01binary/elysium-max-exoskeleton/instructions/images/chest/chest-electronics.png

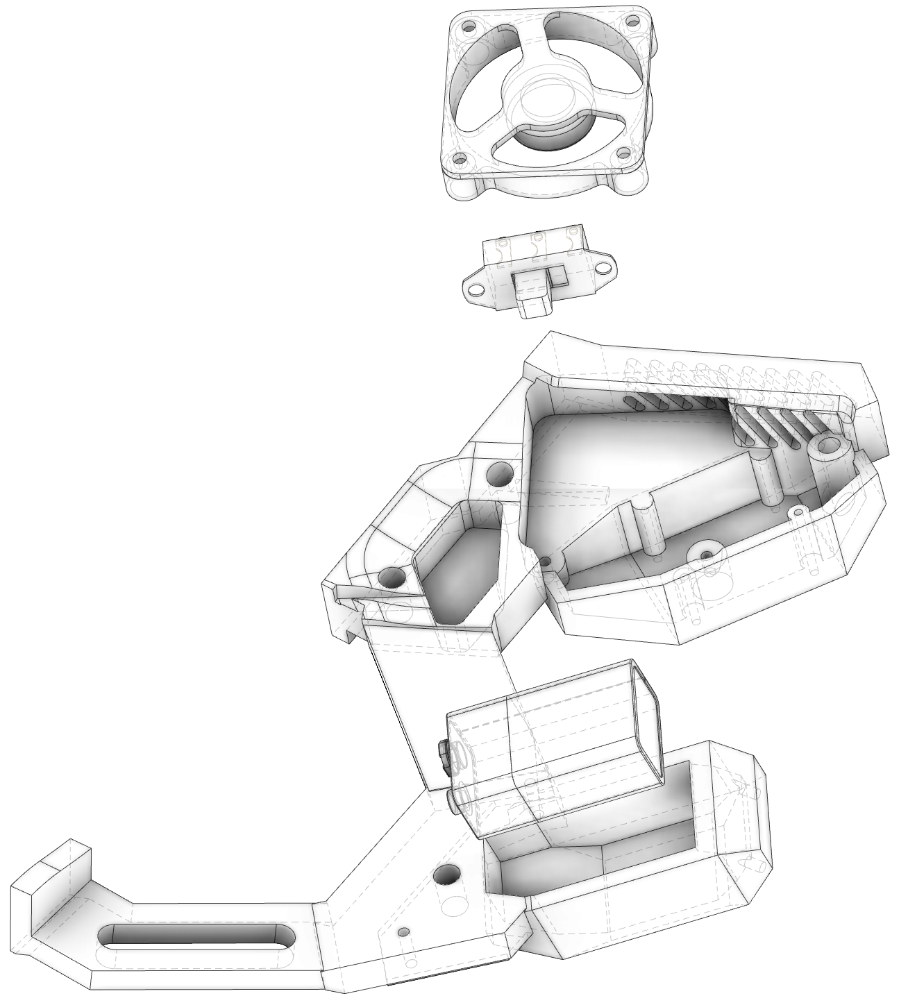
instructions/images/chest/chest-electronics.png
