01binary/elysium-max-exoskeleton/references/6mm-bolts.jpg

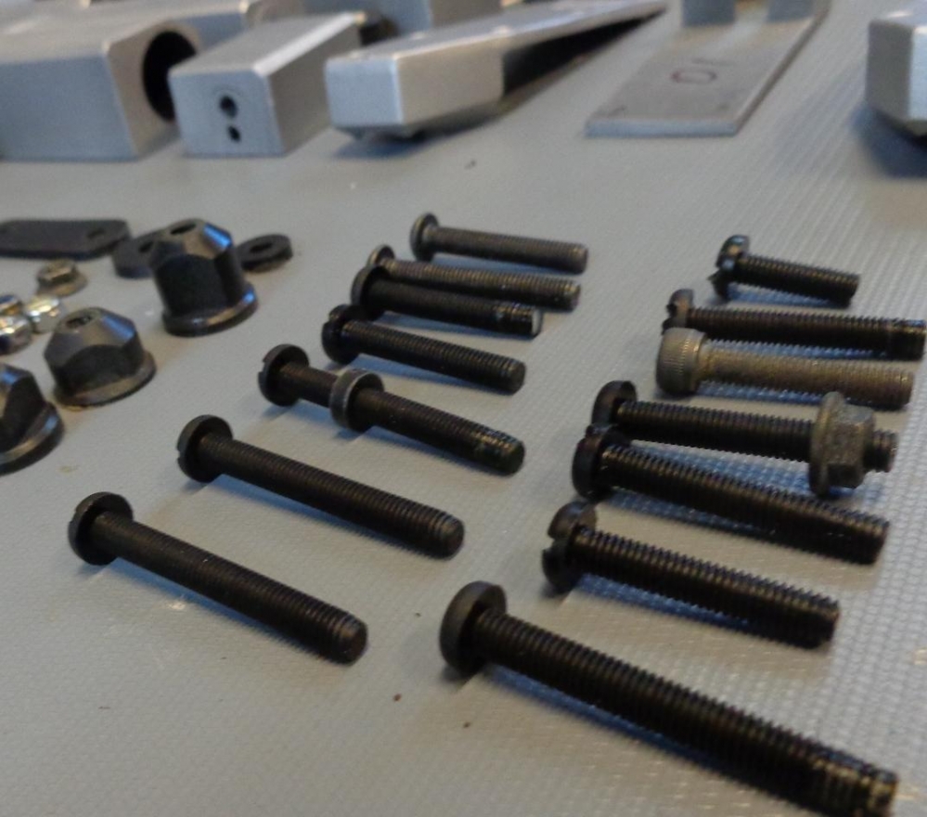
references/6mm-bolts.jpg
