01binary/elysium-max-exoskeleton/references/11591d1393811206-hulc-suit-worn-max-maxmannequin.jpg

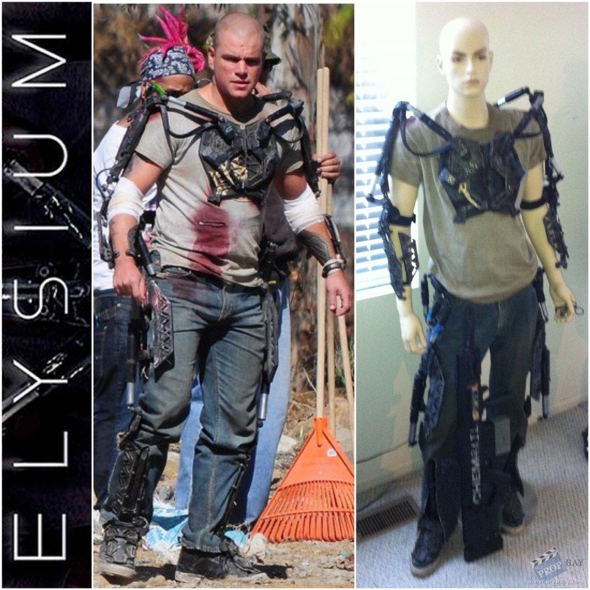
references/11591d1393811206-hulc-suit-worn-max-maxmannequin.jpg
