01binary/elysium-max-exoskeleton/references/11595d1393811206-hulc-suit-worn-max-wetaworkshopelysiumwork111.jpg

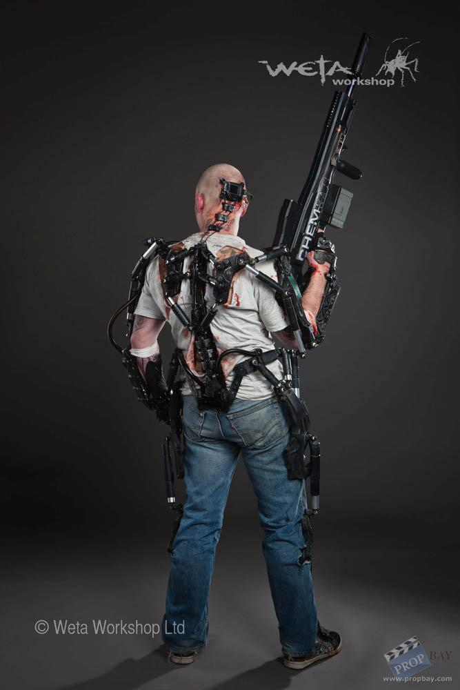
references/11595d1393811206-hulc-suit-worn-max-wetaworkshopelysiumwork111.jpg
