01binary/elysium-max-exoskeleton/references/15305_7.jpg

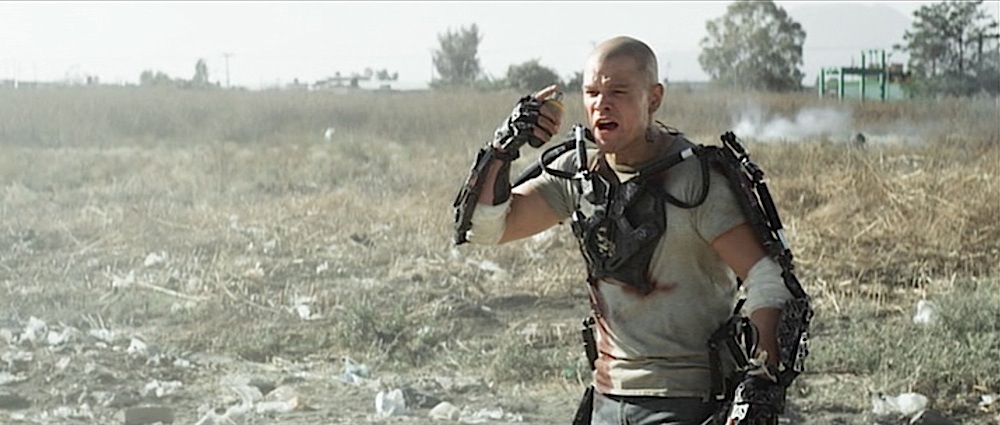
references/15305_7.jpg
