01binary/elysium-max-exoskeleton/references/15305_8.jpg

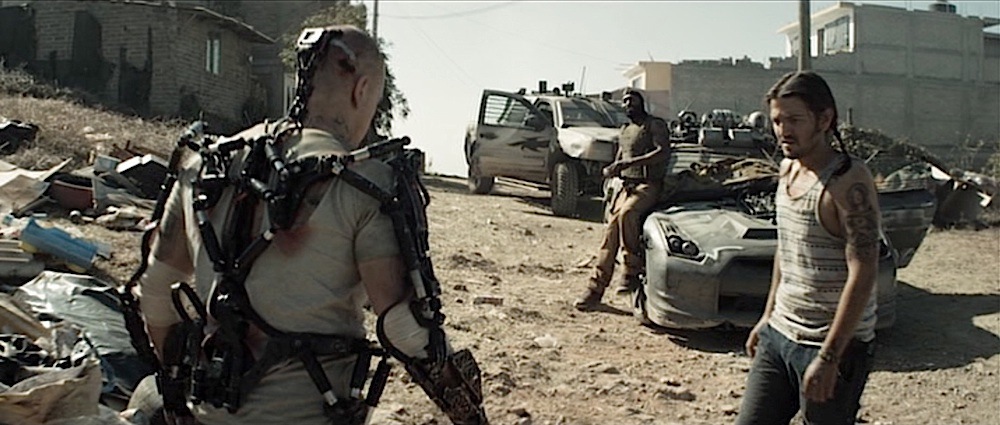
references/15305_8.jpg
