01binary/elysium-max-exoskeleton/references/15305_12.jpg

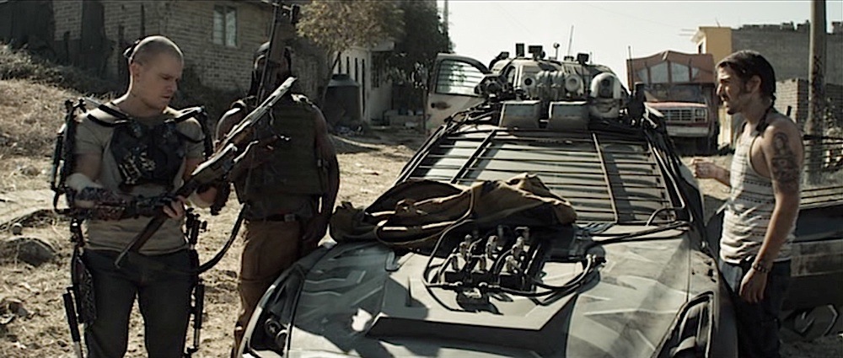
references/15305_12.jpg
