01binary/elysium-max-exoskeleton/references/15445_1.jpg

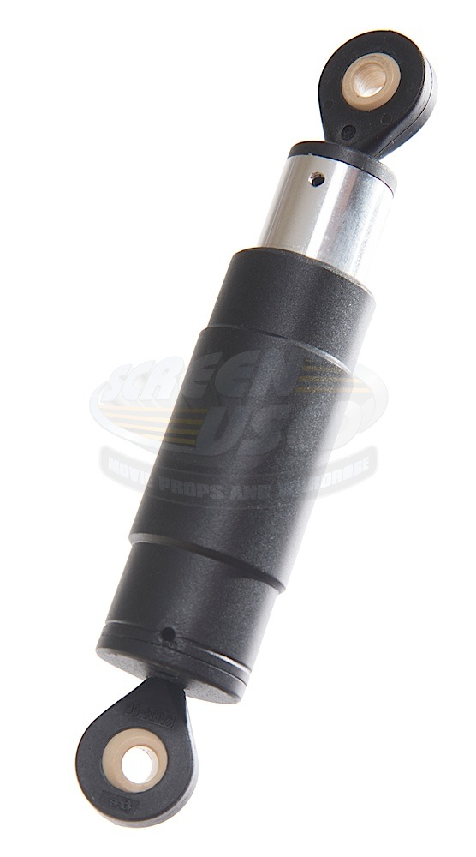
references/15445_1.jpg
