01binary/elysium-max-exoskeleton/references/15445_2.jpg

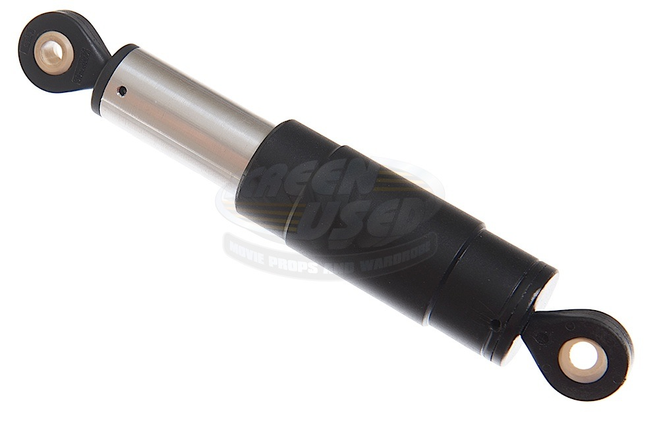
references/15445_2.jpg
