01binary/elysium-max-exoskeleton/references/28012.jpg

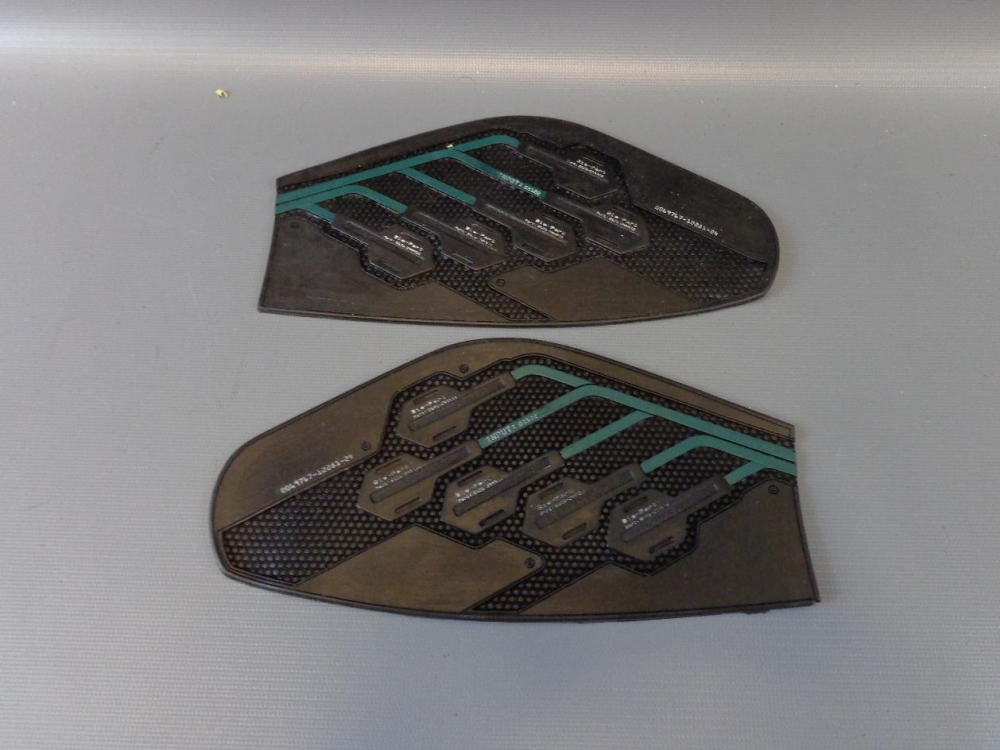
references/28012.jpg
