01binary/elysium-max-exoskeleton/references/197699.jpg

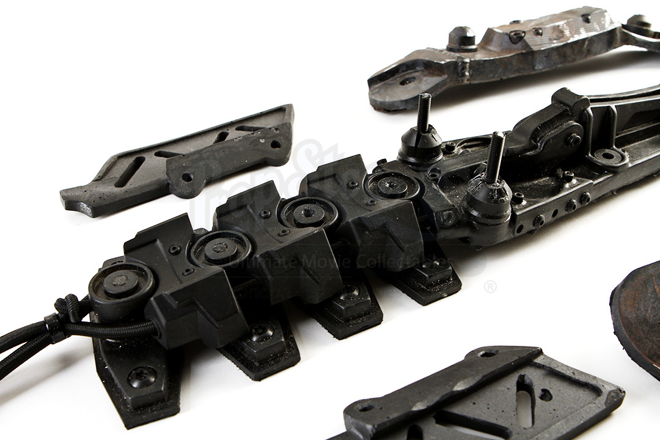
references/197699.jpg
