01binary/elysium-max-exoskeleton/references/197700.jpg

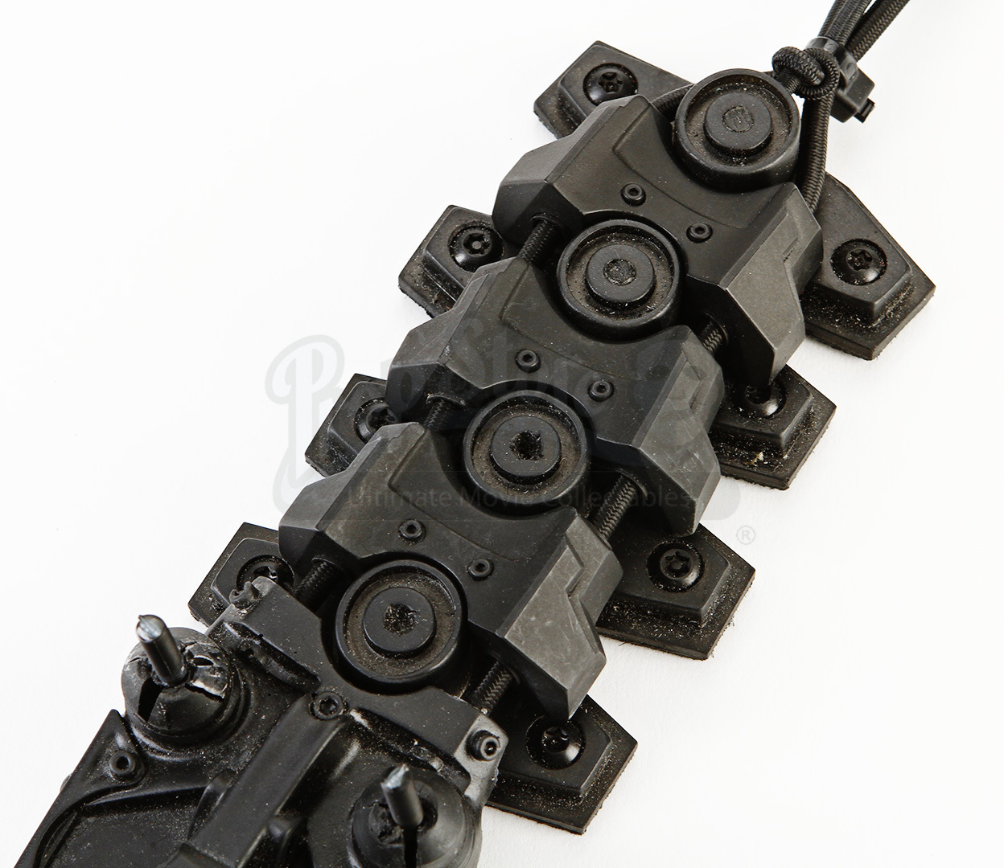
references/197700.jpg
