01binary/elysium-max-exoskeleton/references/197705.jpg

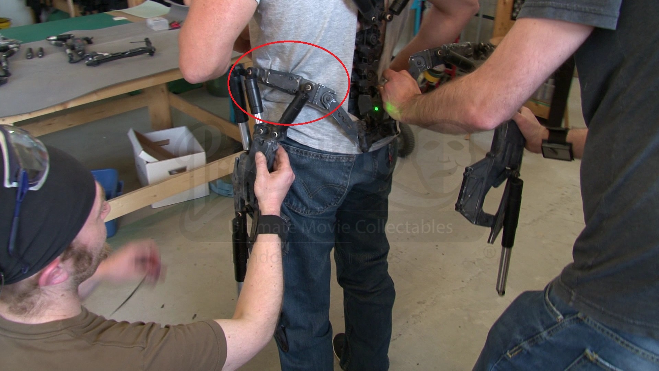
references/197705.jpg
