01binary/elysium-max-exoskeleton/references/198704.jpg

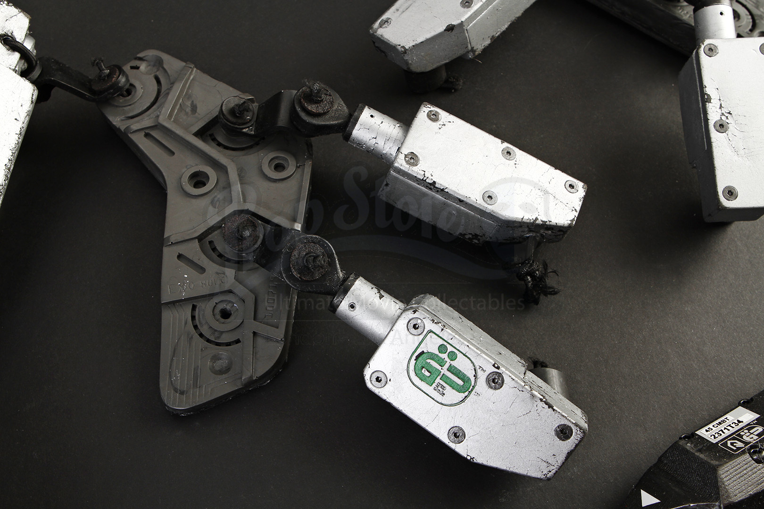
references/198704.jpg
