01binary/elysium-max-exoskeleton/references/198857.jpg

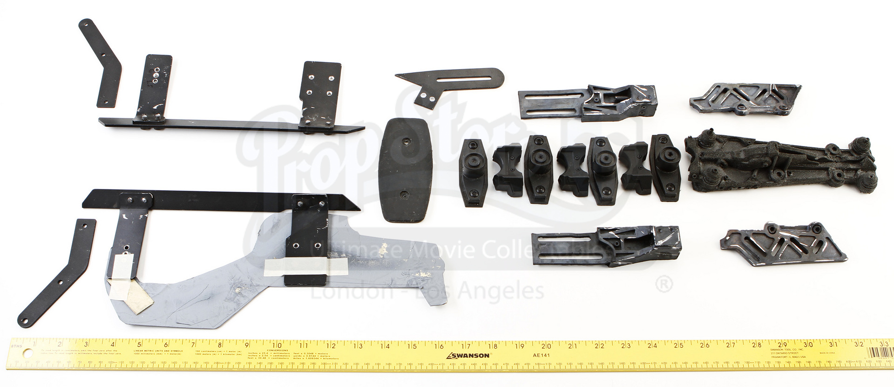
references/198857.jpg
