01binary/elysium-max-exoskeleton/references/213902.jpg

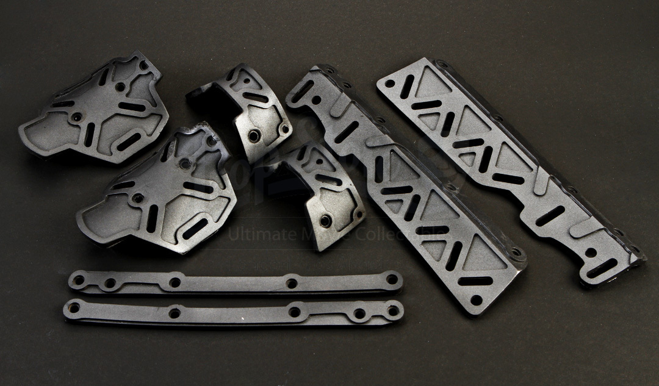
references/213902.jpg
