01binary/elysium-max-exoskeleton/references/213905.jpg

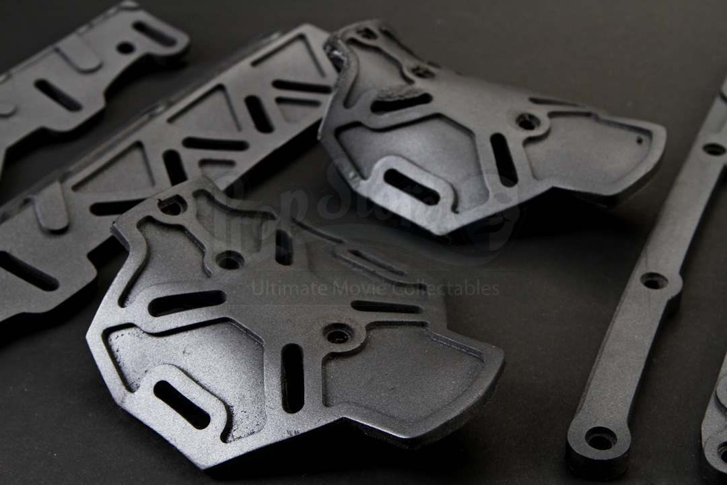
references/213905.jpg
