01binary/elysium-max-exoskeleton/references/574495_199496503551043_1846107824_n.jpg

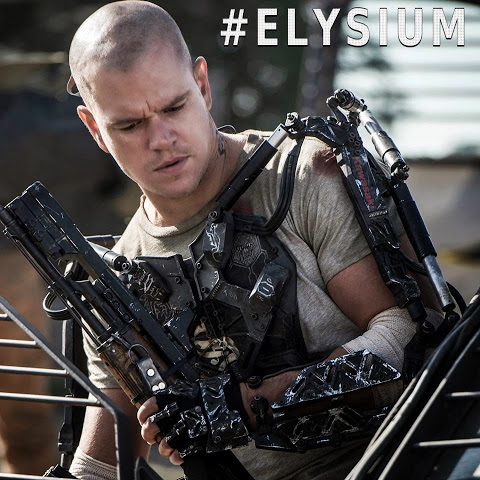
references/574495_199496503551043_1846107824_n.jpg
