01binary/elysium-max-exoskeleton/references/5401417-Elysium-Exoskeleton-Video.jpg

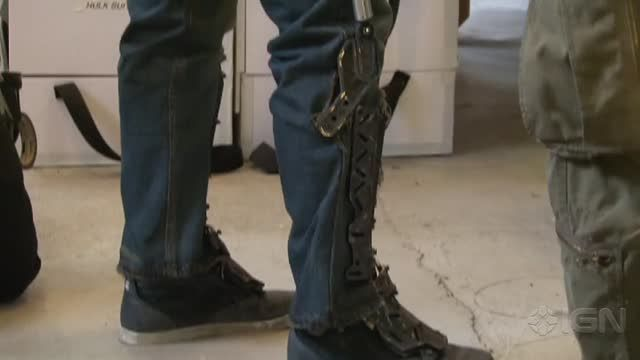
references/5401417-Elysium-Exoskeleton-Video.jpg
