01binary/elysium-max-exoskeleton/references/06674515.jpg

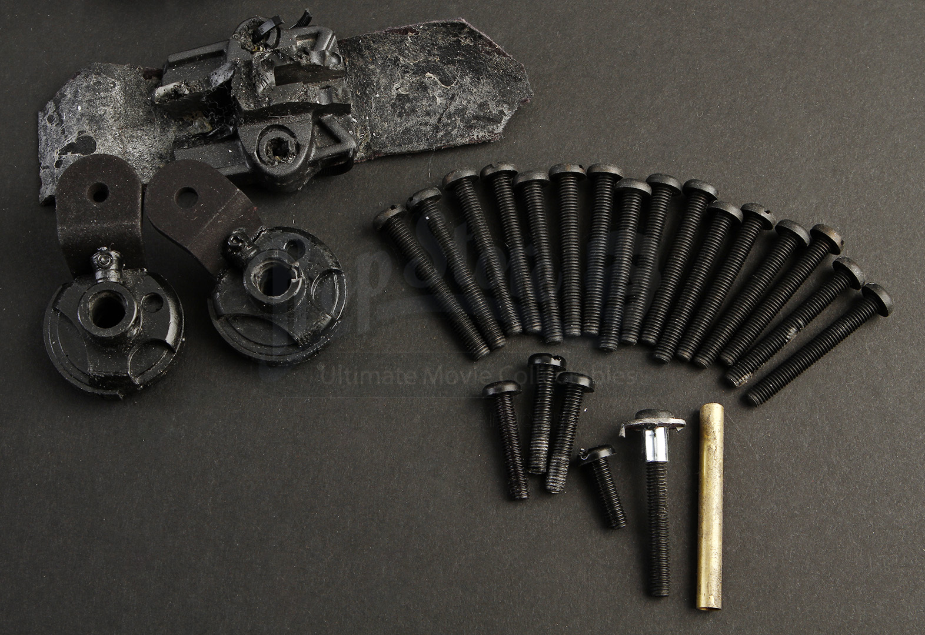
references/06674515.jpg
