01binary/elysium-max-exoskeleton/references/7878678.jpg

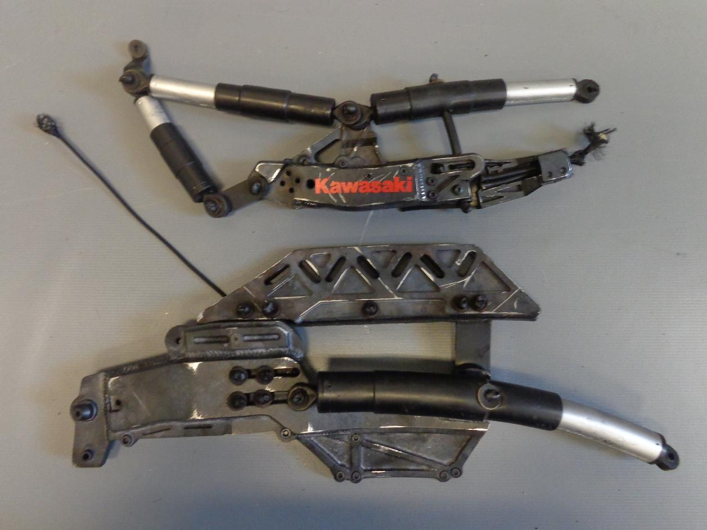
references/7878678.jpg
