01binary/elysium-max-exoskeleton/references/10857353_10152587256252303_362344312174633431_o.jpg

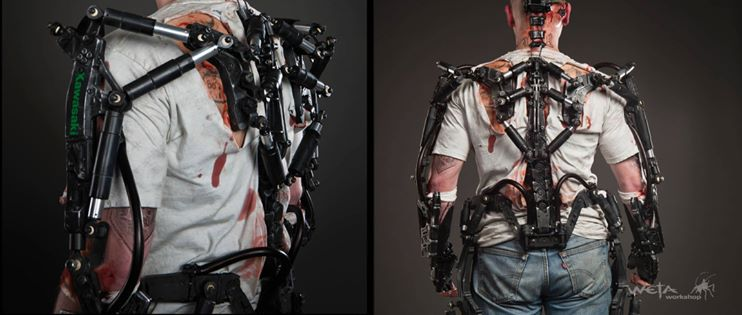
references/10857353_10152587256252303_362344312174633431_o.jpg
