01binary/elysium-max-exoskeleton/references/14776765.jpg

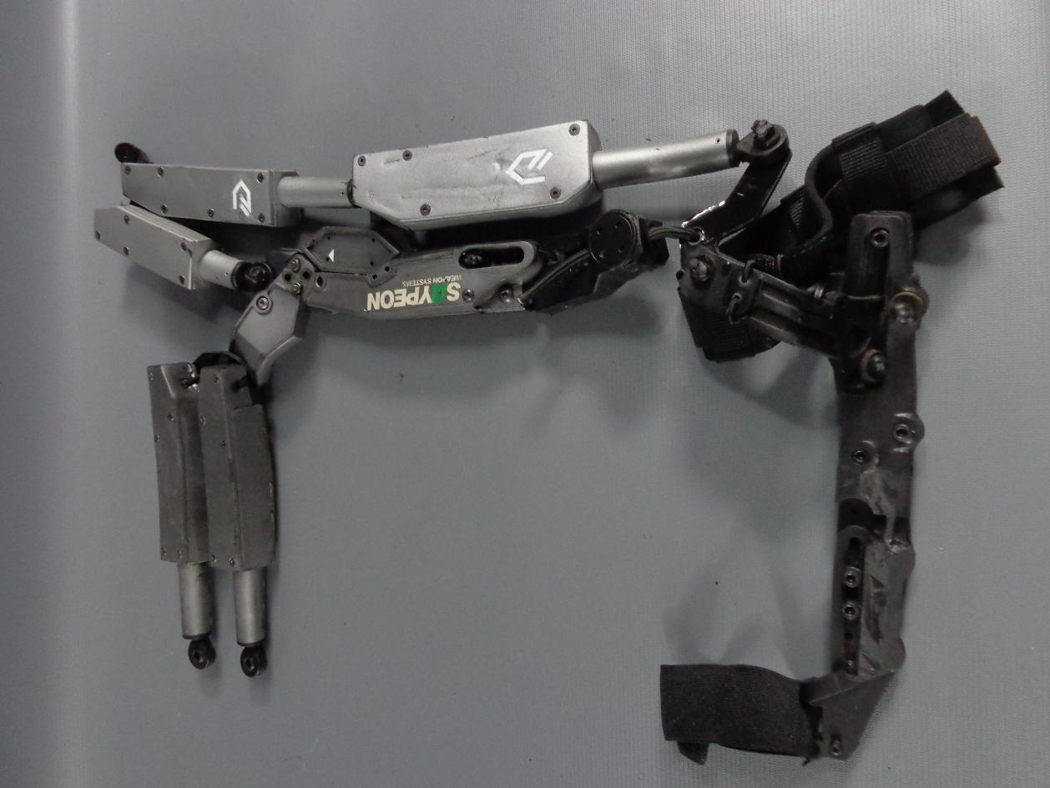
references/14776765.jpg
