01binary/elysium-max-exoskeleton/references/14776832.jpg

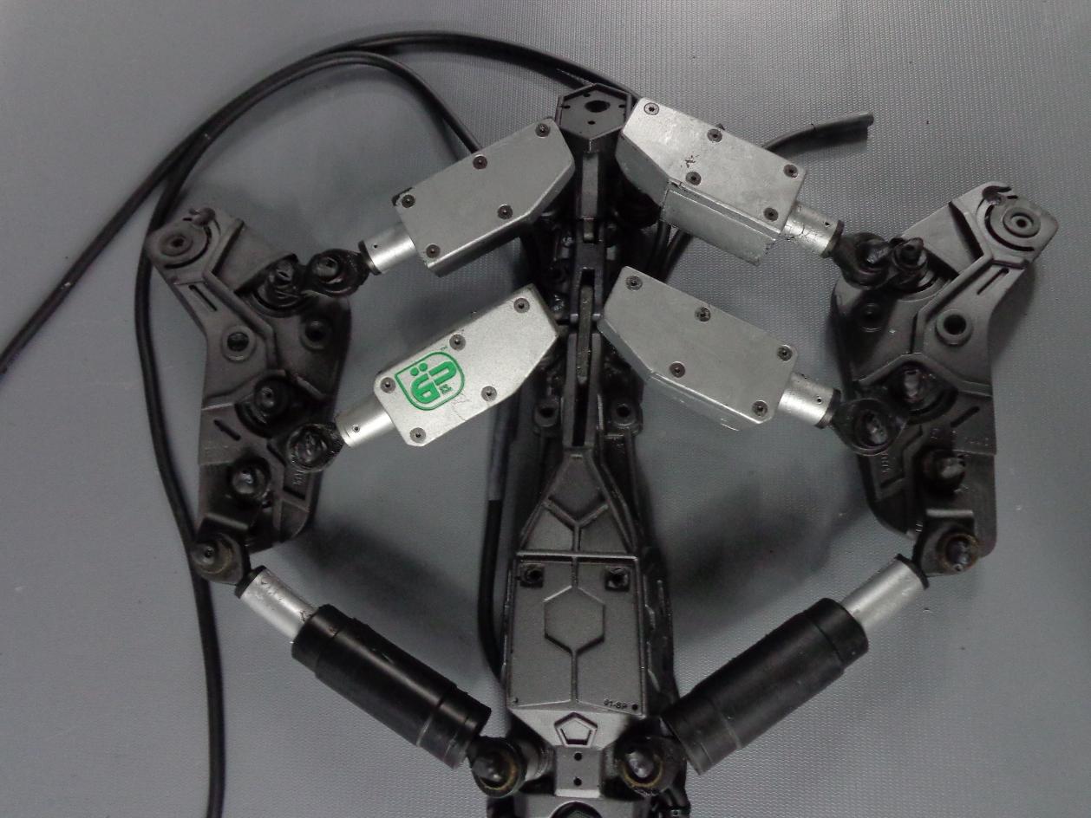
references/14776832.jpg
