01binary/elysium-max-exoskeleton/references/14795775.jpg

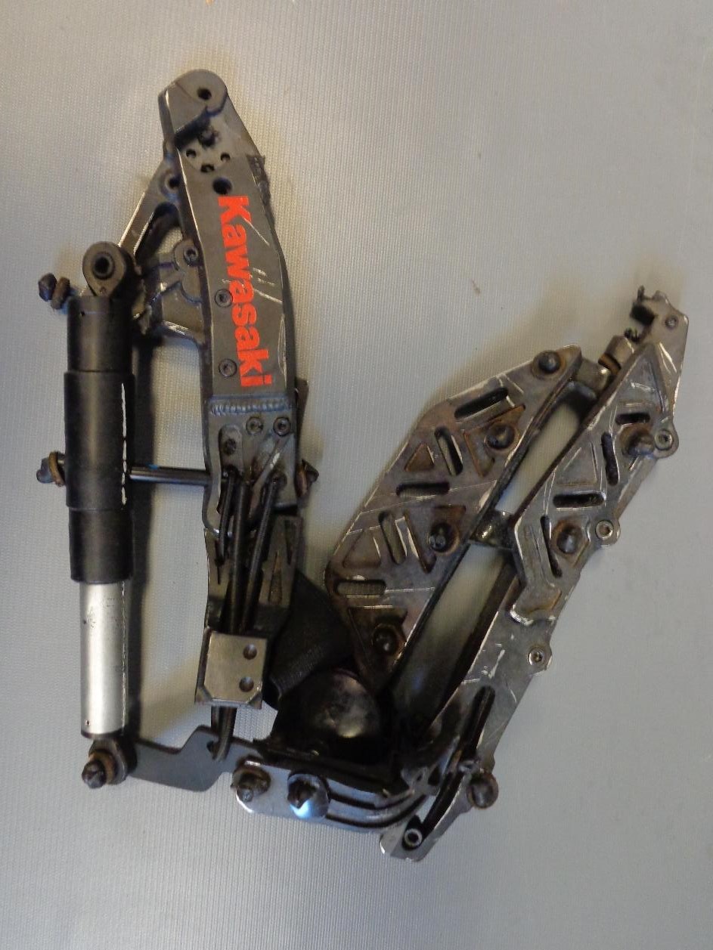
references/14795775.jpg
