01binary/elysium-max-exoskeleton/references/14795777.jpg

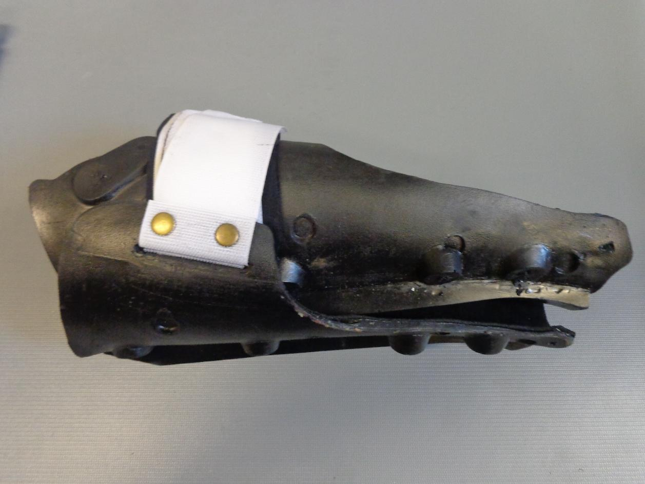
references/14795777.jpg
