01binary/elysium-max-exoskeleton/references/14795779.jpg

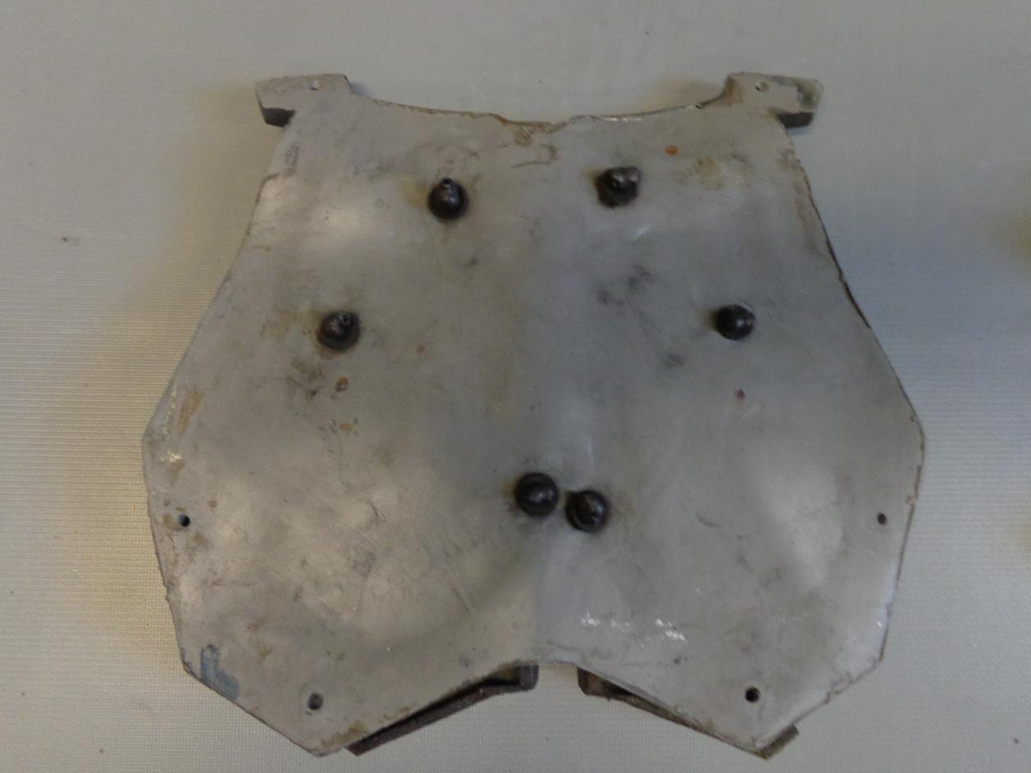
references/14795779.jpg
