01binary/elysium-max-exoskeleton/references/14795780.jpg

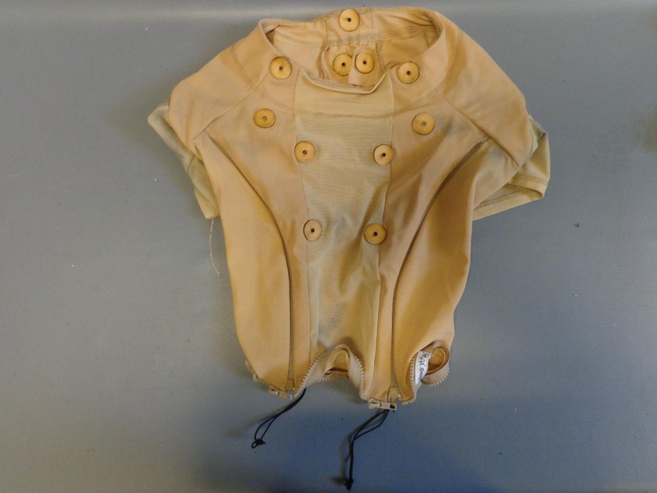
references/14795780.jpg
