01binary/elysium-max-exoskeleton/references/14795787.jpg

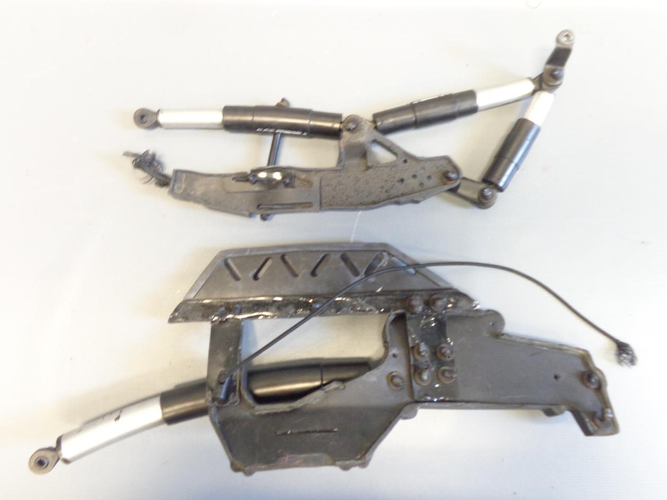
references/14795787.jpg
