01binary/elysium-max-exoskeleton/references/14795788.jpg

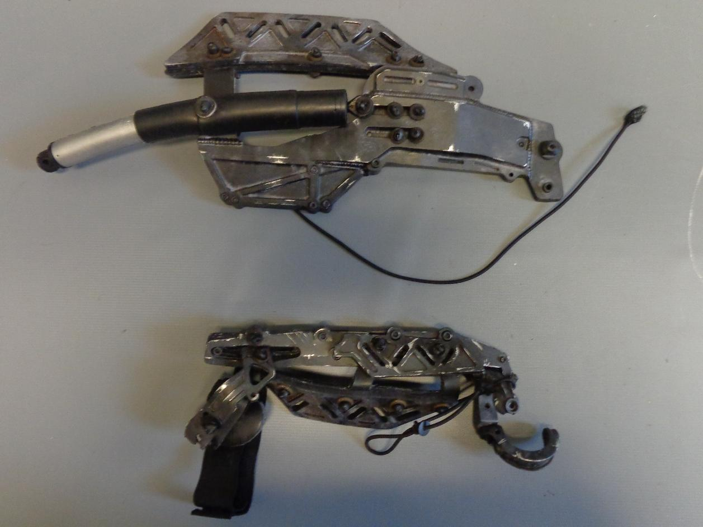
references/14795788.jpg
