01binary/elysium-max-exoskeleton/references/14795789.jpg

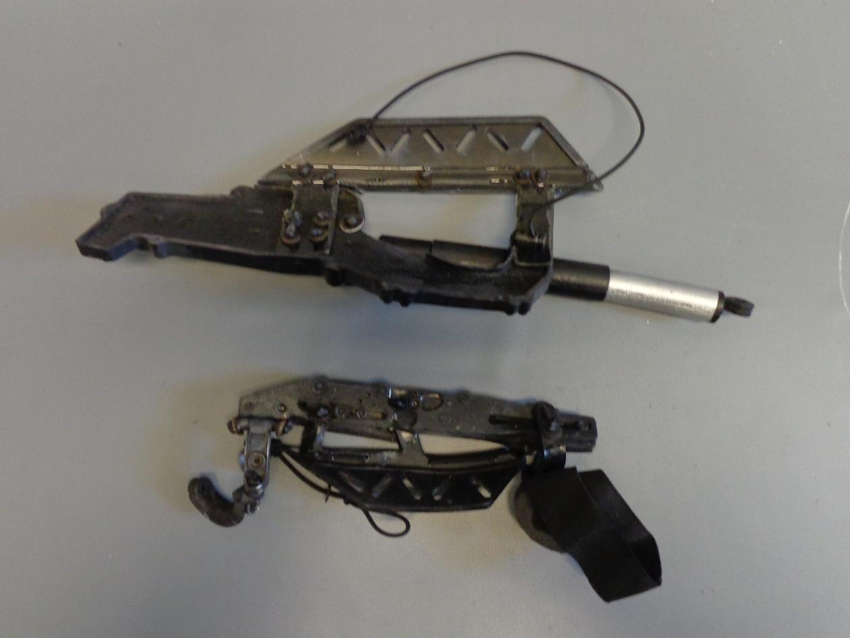
references/14795789.jpg
