01binary/elysium-max-exoskeleton/references/14852573.jpg

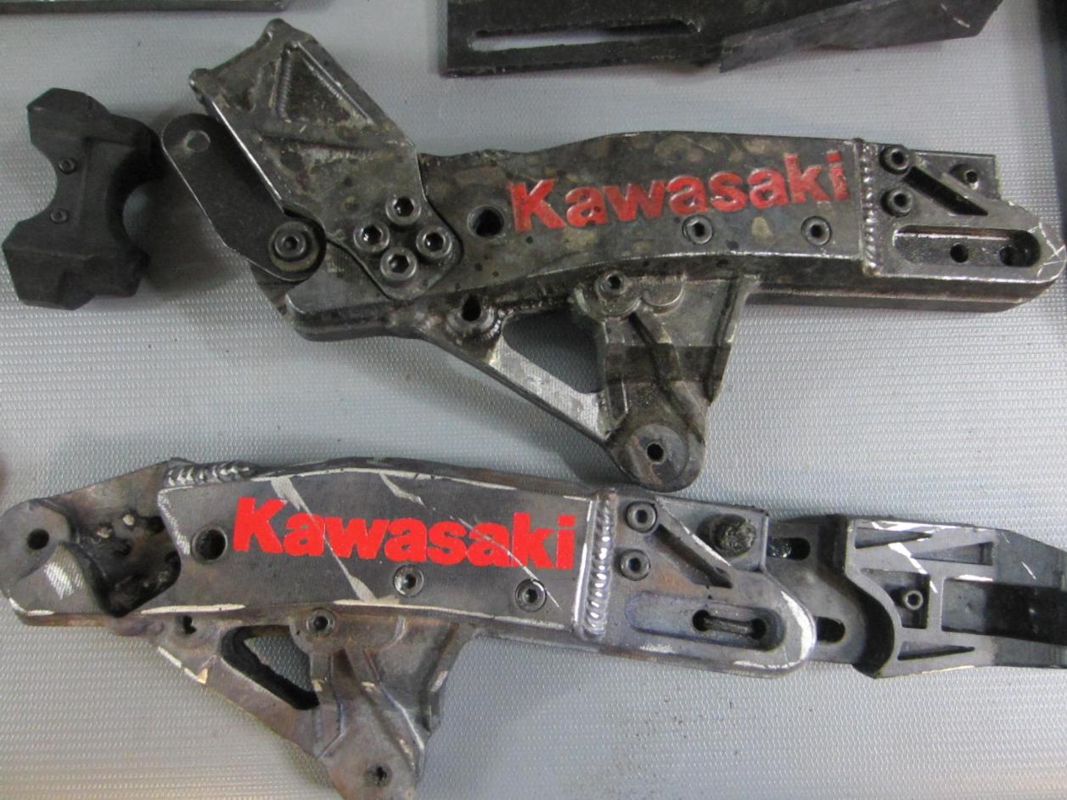
references/14852573.jpg
