01binary/elysium-max-exoskeleton/references/14852575.jpg

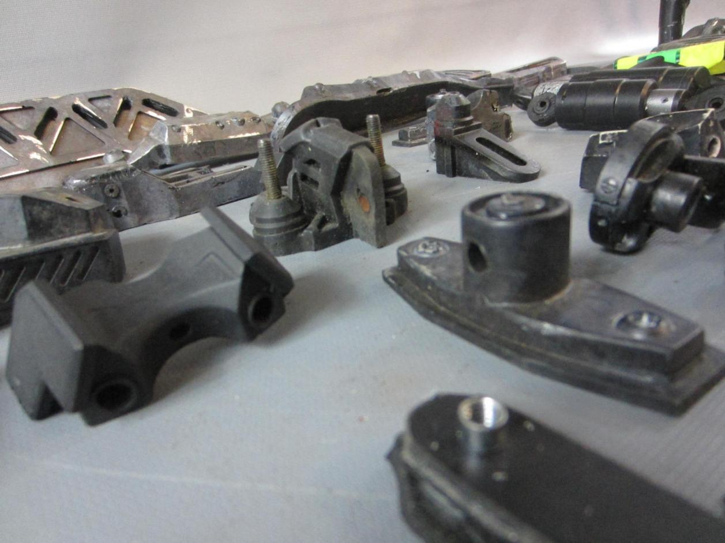
references/14852575.jpg
