01binary/elysium-max-exoskeleton/references/aliensarchive.png

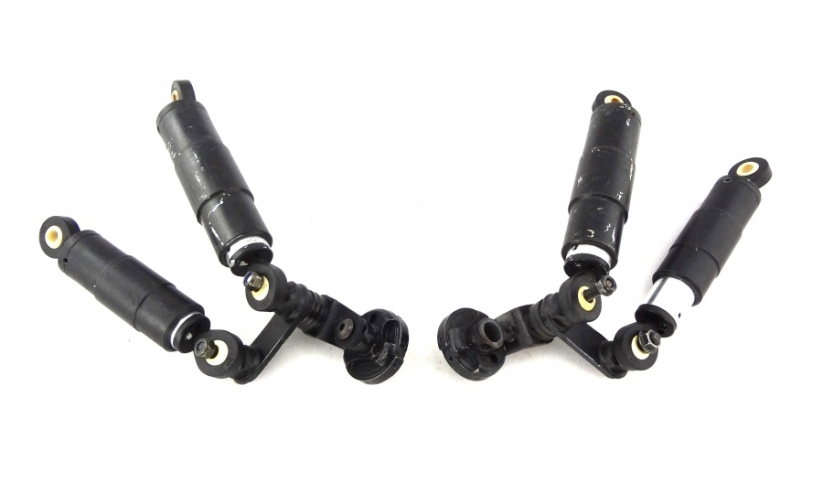
references/aliensarchive.png
