01binary/elysium-max-exoskeleton/references/another-pelvis.jpg

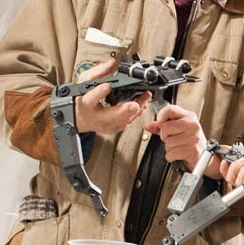
references/another-pelvis.jpg
