01binary/elysium-max-exoskeleton/references/arm left.bmp

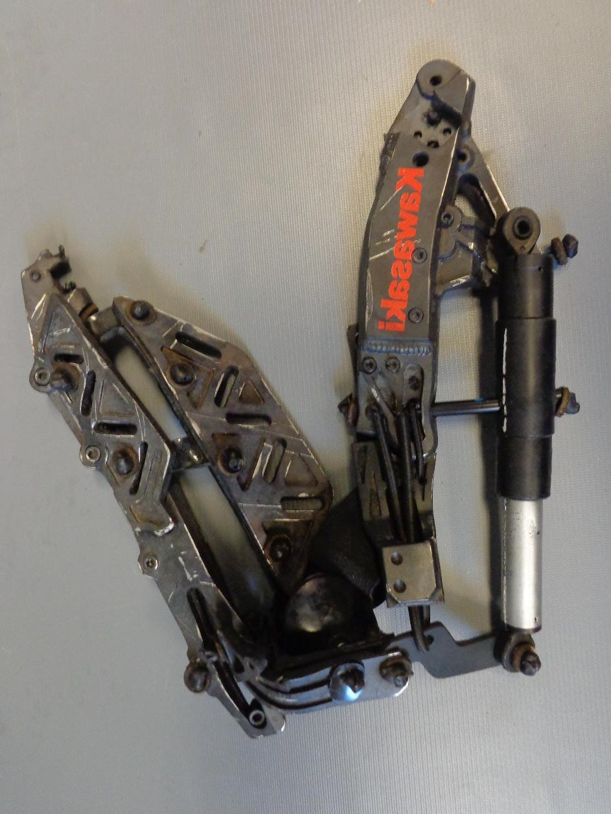
references/arm left.bmp
