01binary/elysium-max-exoskeleton/references/Chest/chest mount 2.jpg

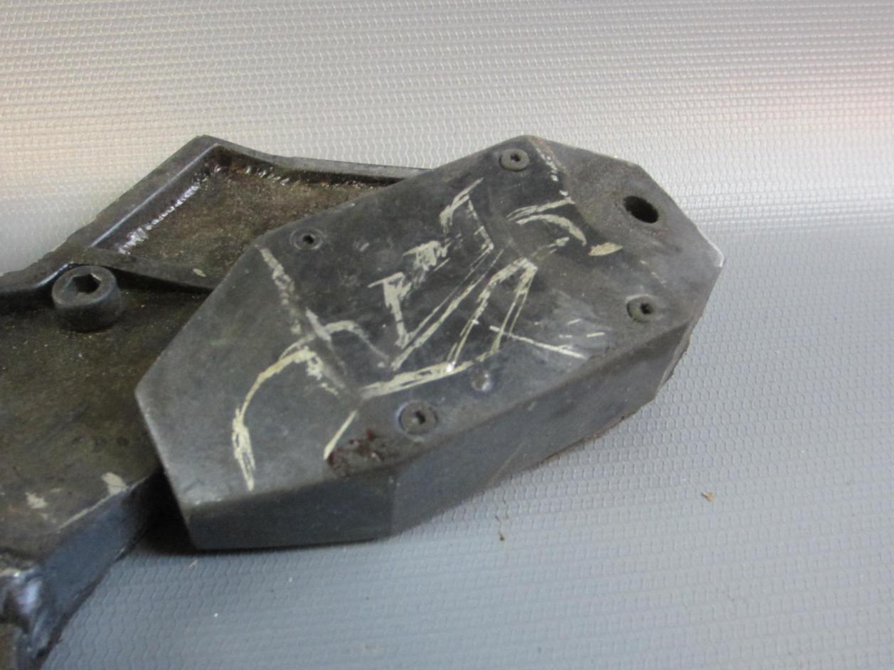
references/chest mount 2.jpg
