01binary/elysium-max-exoskeleton/references/Chest/chest-top.png

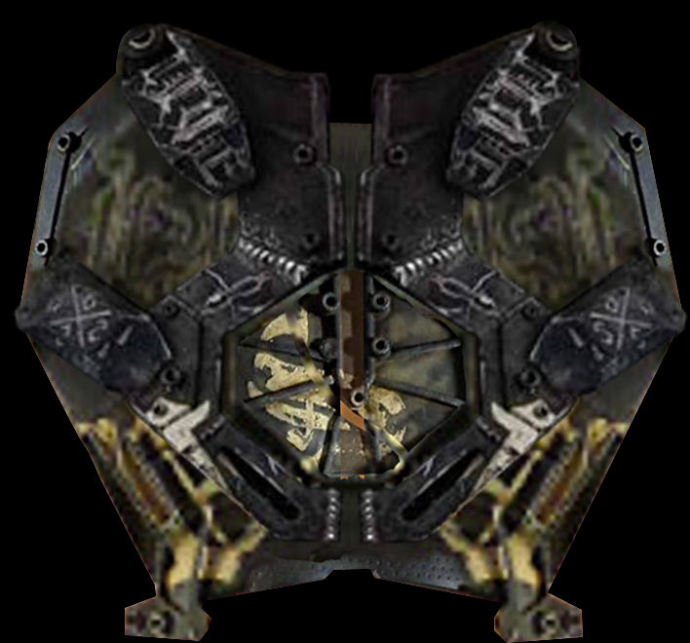
references/Chest/chest-top.png
