01binary/elysium-max-exoskeleton/references/Chest/movie12.jpg

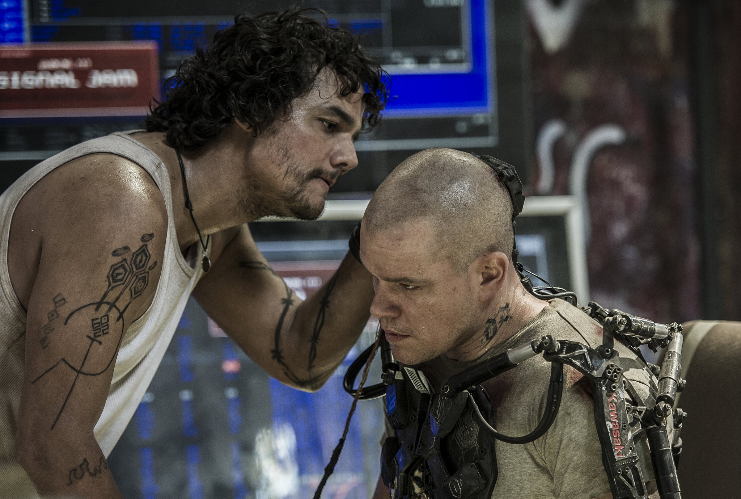
references/Chest/movie12.jpg
