01binary/elysium-max-exoskeleton/references/Chest/production05.jpg

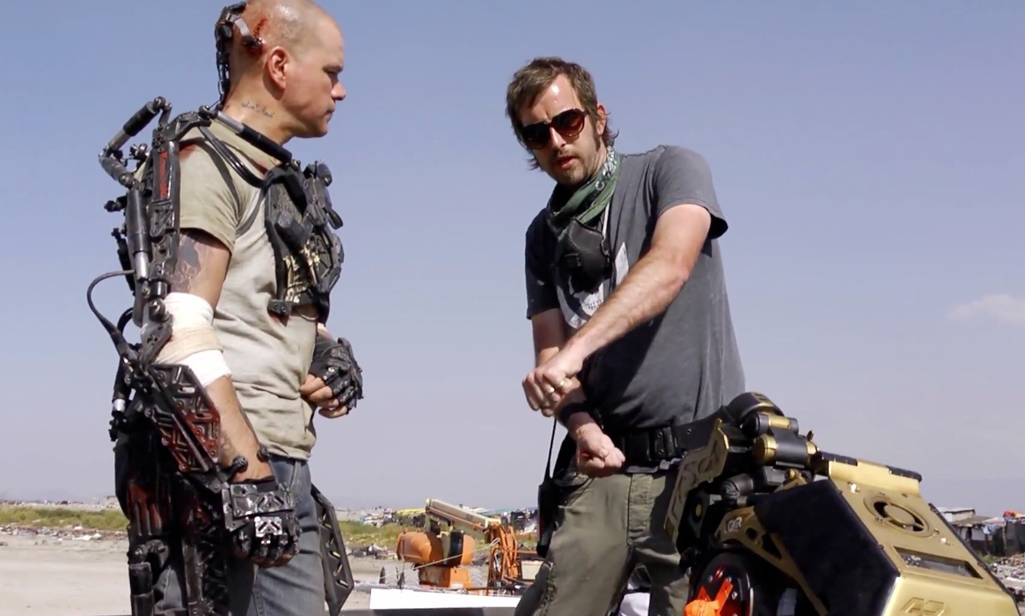
references/Chest/production05.jpg
