01binary/elysium-max-exoskeleton/references/chestak.png

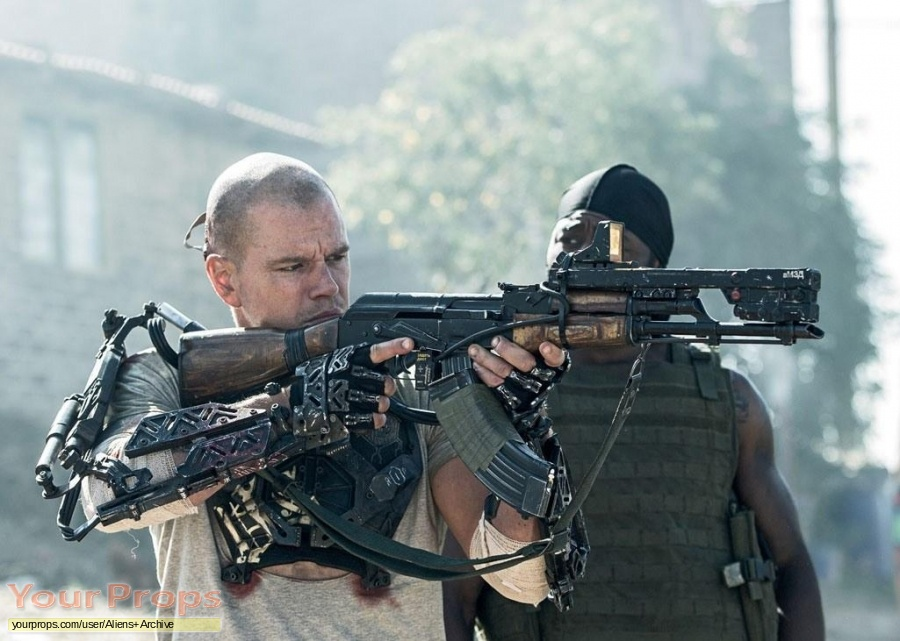
references/chestak.png
