01binary/elysium-max-exoskeleton/references/corners.png

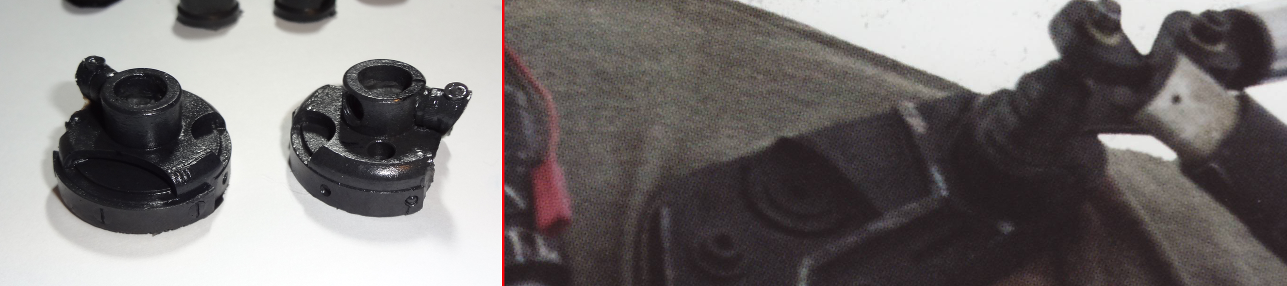
references/corners.png
