01binary/elysium-max-exoskeleton/references/elysium048-upperarmconn.jpg

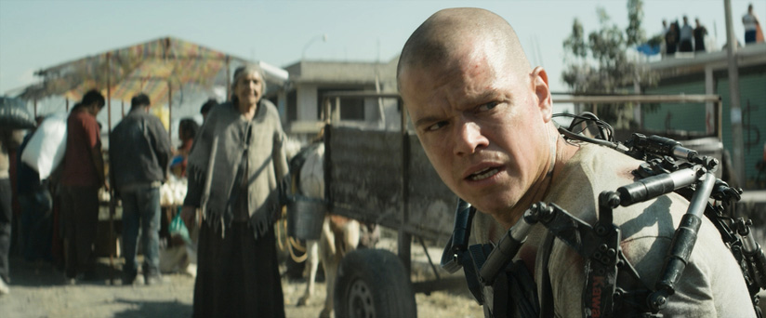
references/elysium048-upperarmconn.jpg
