01binary/elysium-max-exoskeleton/references/elysium065.jpg

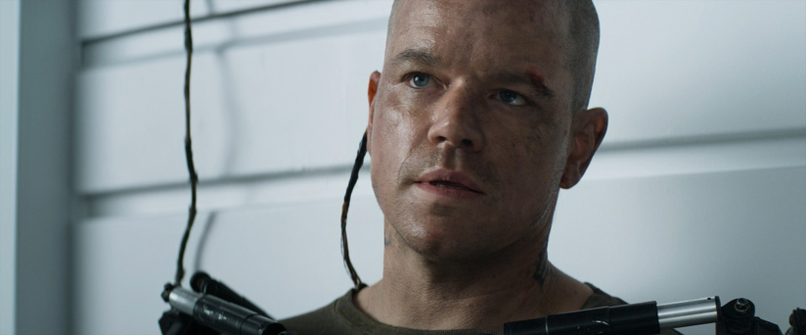
references/elysium065.jpg
