01binary/elysium-max-exoskeleton/references/ELYSIUM-graphic-design2.jpg

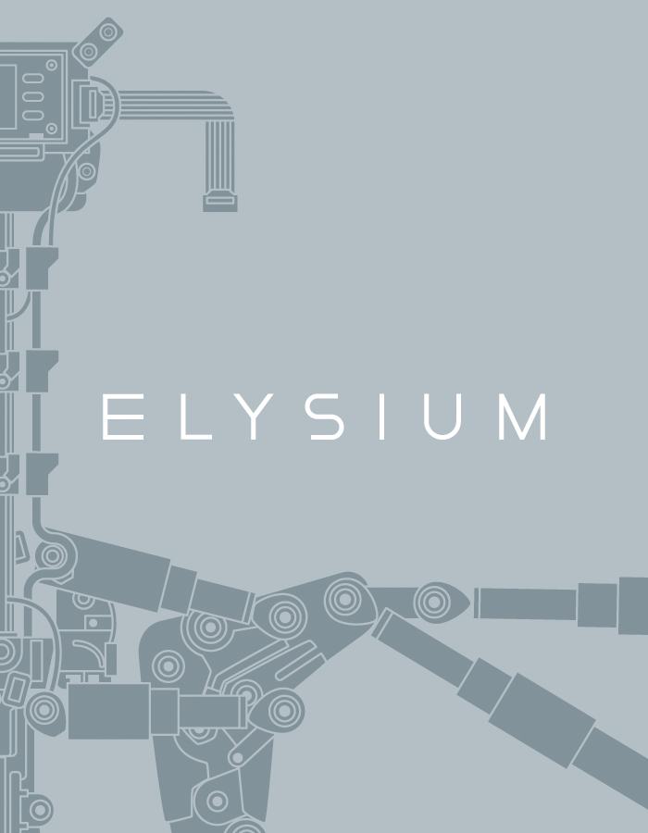
references/ELYSIUM-graphic-design2.jpg
