01binary/elysium-max-exoskeleton/references/elysium-matt-damon-elektro-suit.jpg

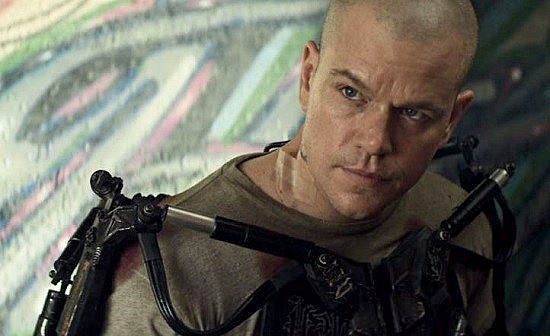
references/elysium-matt-damon-elektro-suit.jpg
