01binary/elysium-max-exoskeleton/references/elysium-sword-strike.jpg

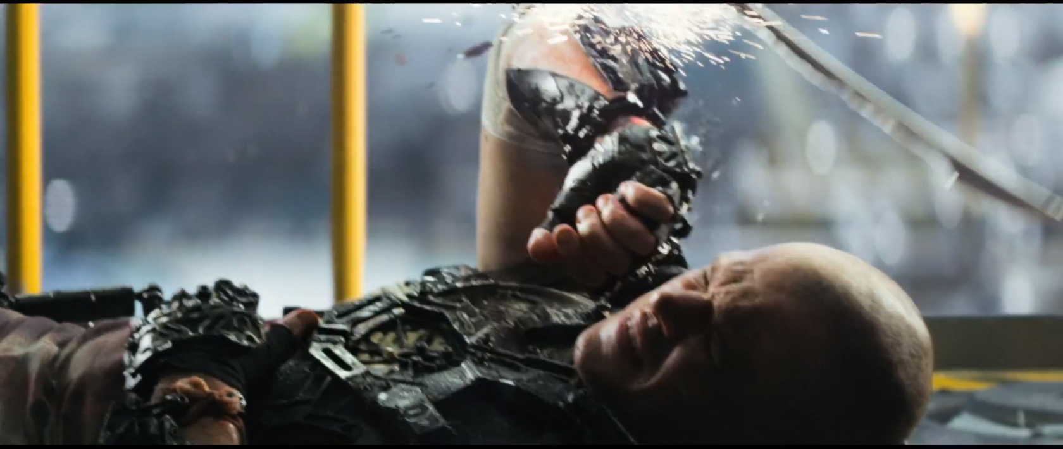
references/elysium-sword-strike.jpg
