01binary/elysium-max-exoskeleton/references/Elysium_BTS_comp_01.jpg

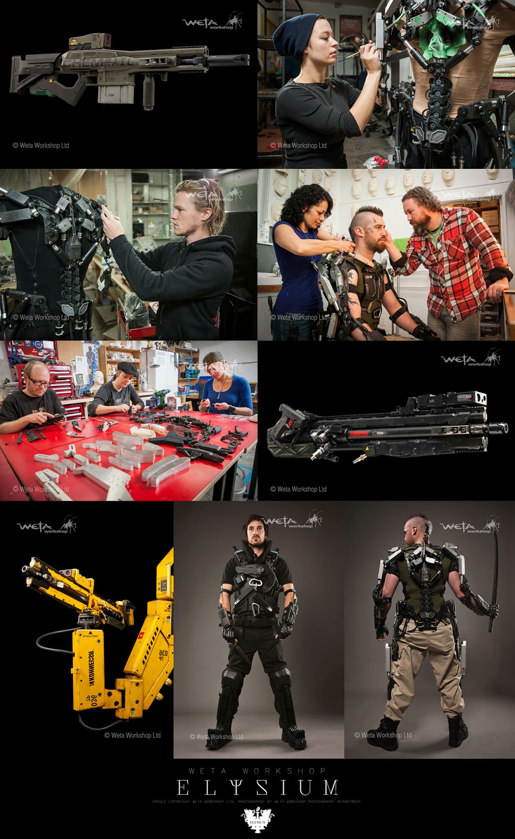
references/Elysium_BTS_comp_01.jpg
