01binary/elysium-max-exoskeleton/references/front.jpg

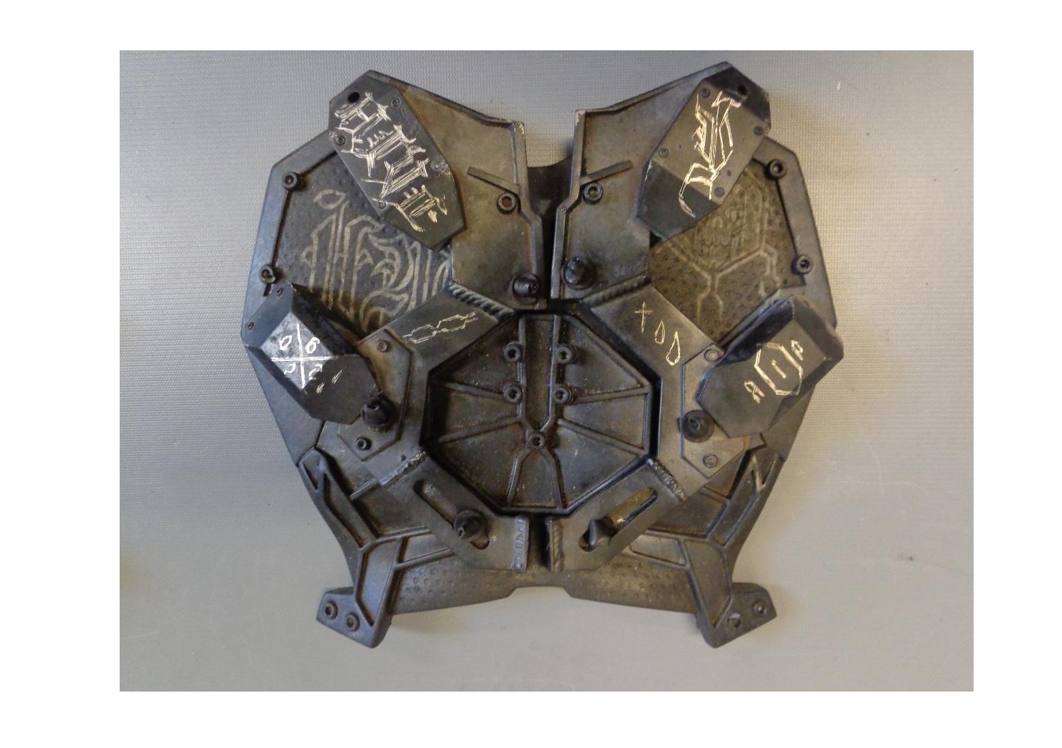
references/front.jpg
