01binary/elysium-max-exoskeleton/references/hand-palm-and-forearm.jpg

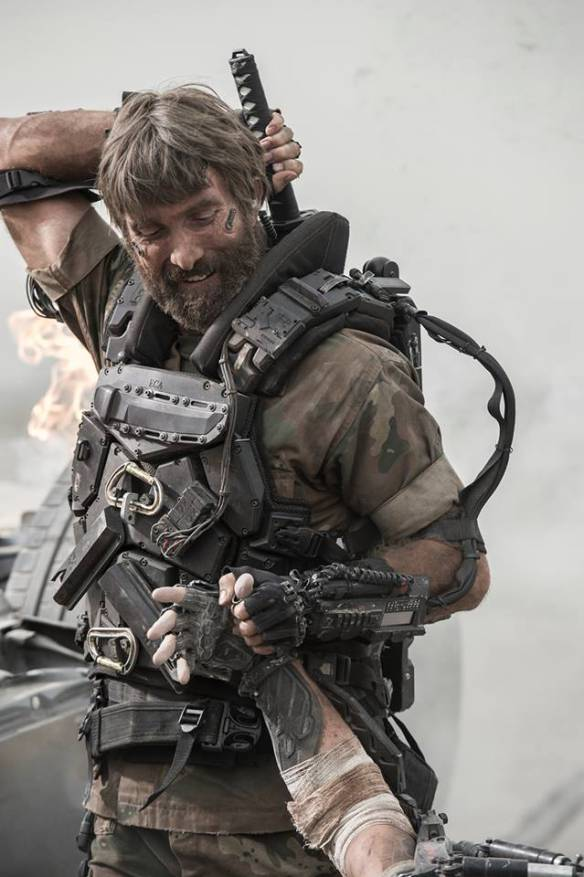
references/hand-palm-and-forearm.jpg
