01binary/elysium-max-exoskeleton/references/handref-unwrapped.JPG

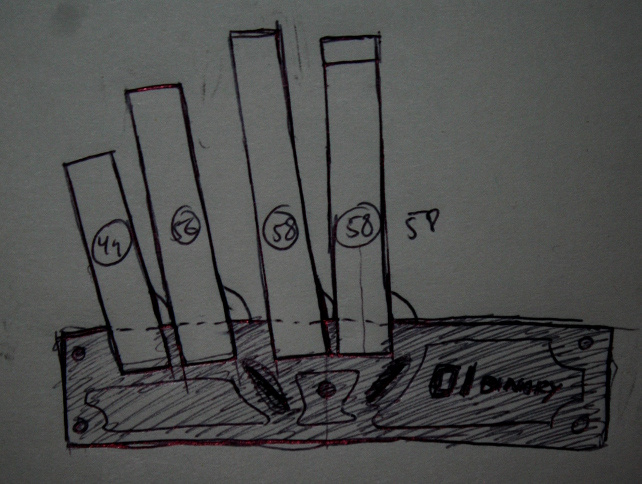
references/handref-unwrapped.JPG
