01binary/elysium-max-exoskeleton/references/hawk-hands.png

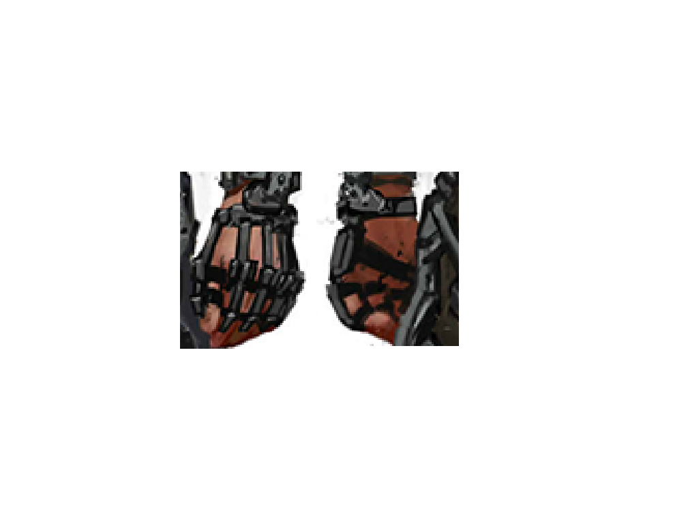
references/hawk-hands.png
