01binary/elysium-max-exoskeleton/references/head-plate.bmp

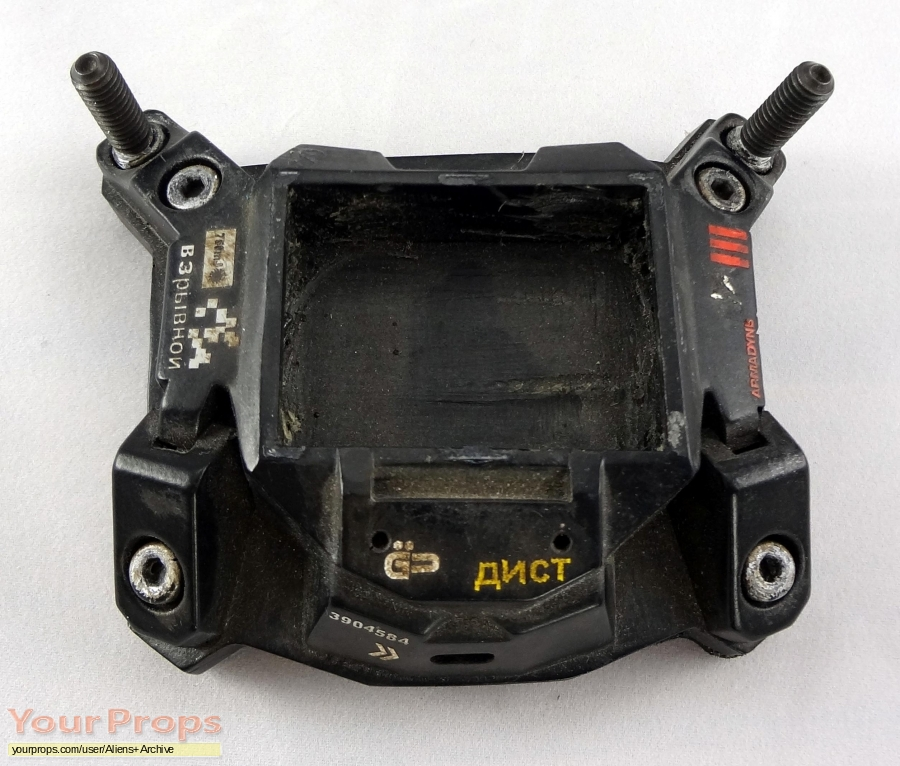
references/head-plate.bmp
