01binary/elysium-max-exoskeleton/references/karm sheet.png

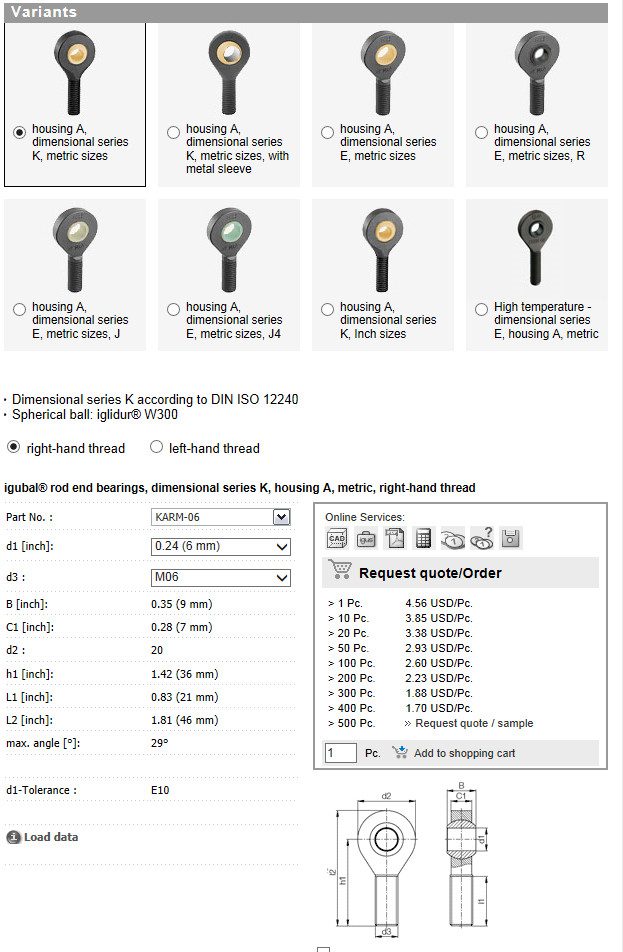
references/karm sheet.png
