01binary/elysium-max-exoskeleton/references/karm.png

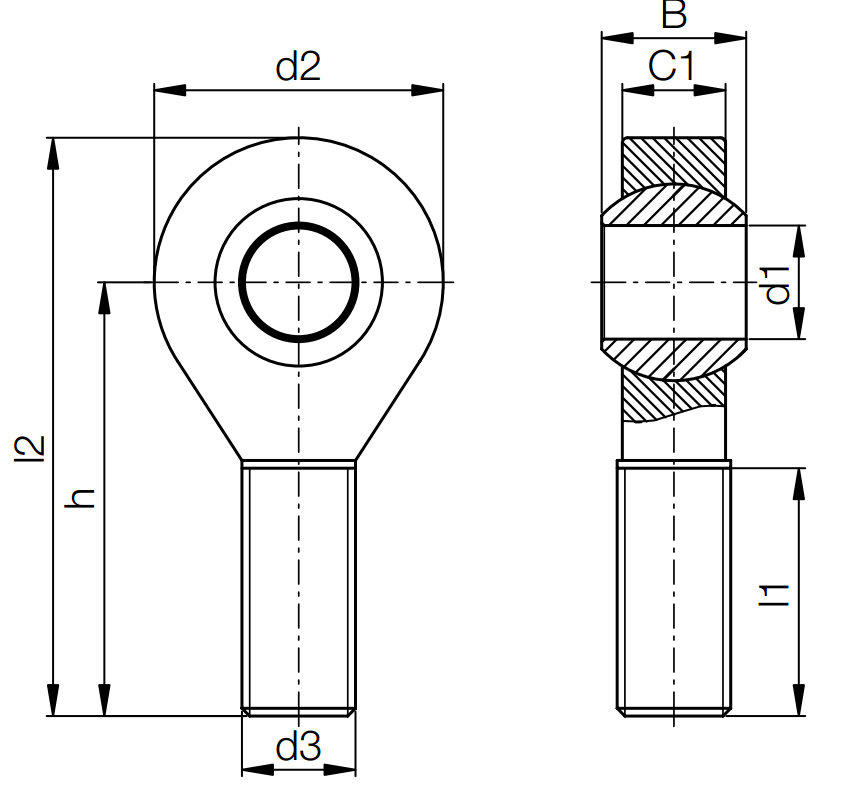
references/karm.png
