01binary/elysium-max-exoskeleton/references/kruger-pistons.jpg

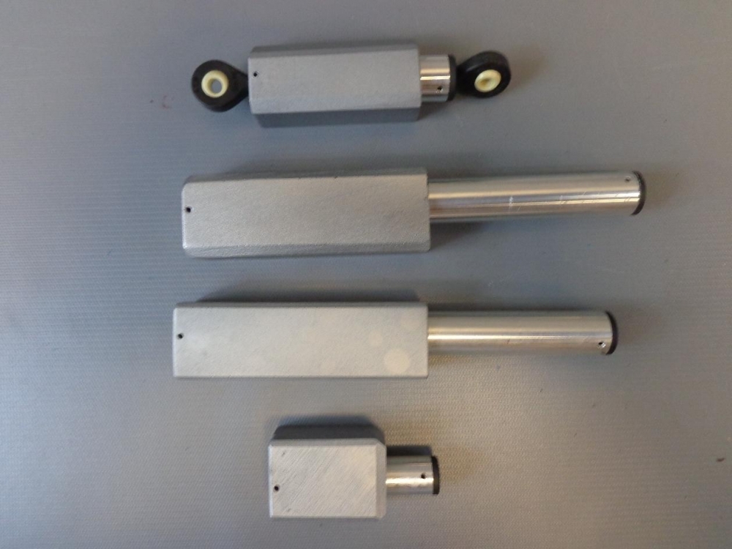
references/kruger-pistons.jpg
