01binary/elysium-max-exoskeleton/references/lf.jpg

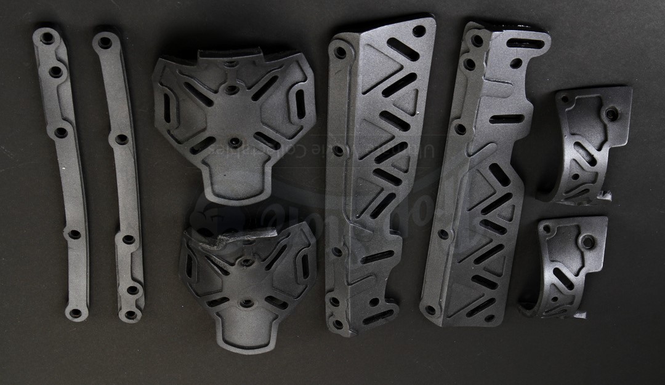
references/lf.jpg
