01binary/elysium-max-exoskeleton/references/Chest/Matt-Damon-in-Exo-Suit.jpg

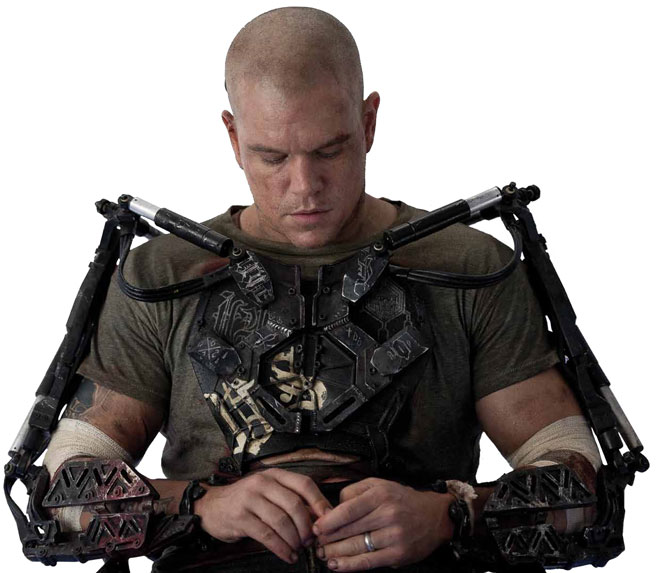
references/Matt-Damon-in-Exo-Suit.jpg
