01binary/elysium-max-exoskeleton/references/Chest/model01.jpg

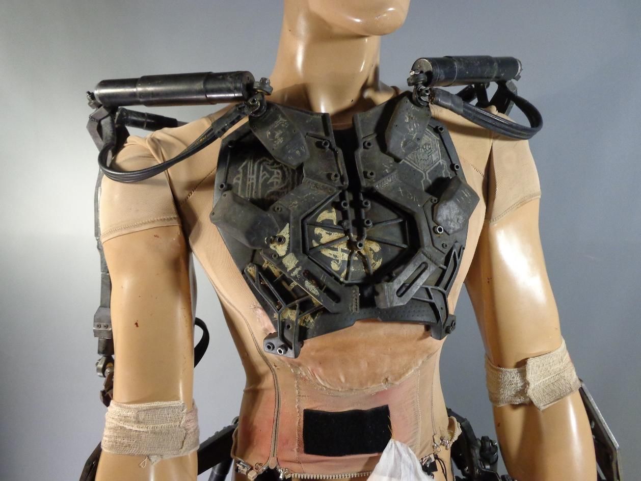
references/model01.jpg
