01binary/elysium-max-exoskeleton/references/model02.jpg

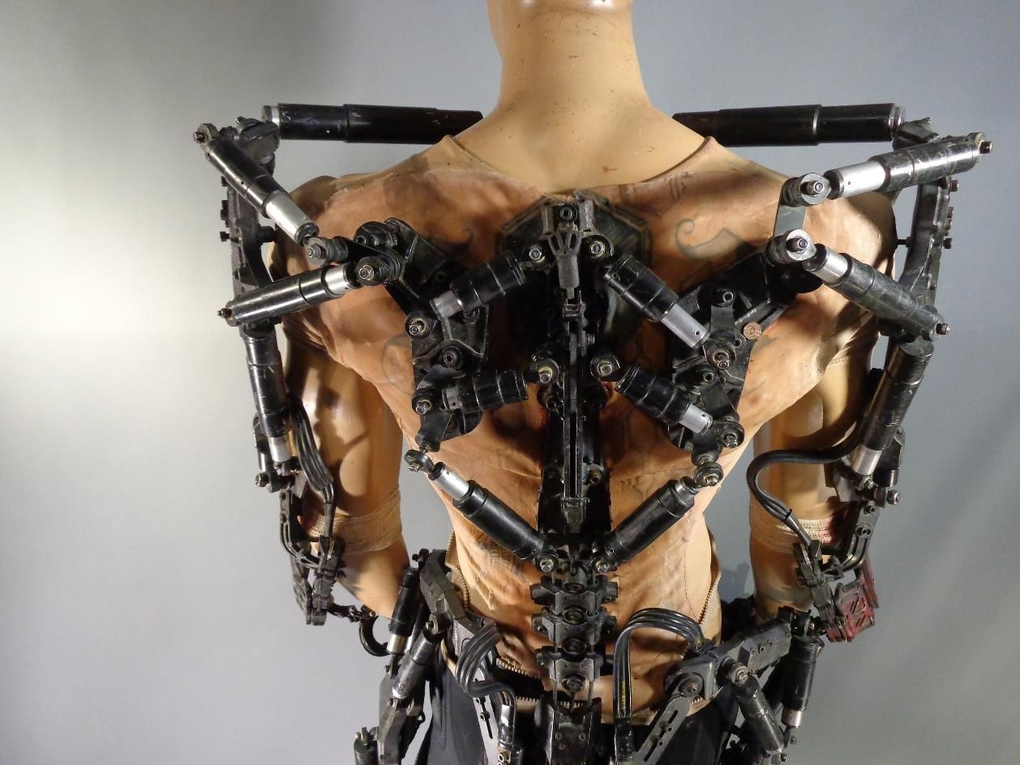
references/model02.jpg
