01binary/elysium-max-exoskeleton/references/model05.JPG

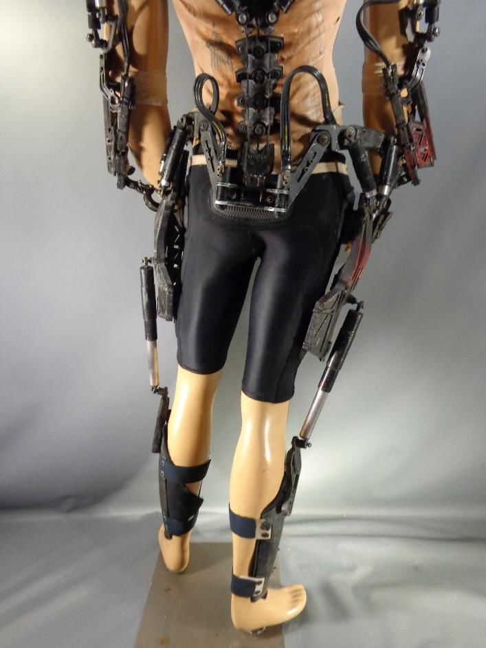
references/model05.JPG
