01binary/elysium-max-exoskeleton/references/model07.jpg

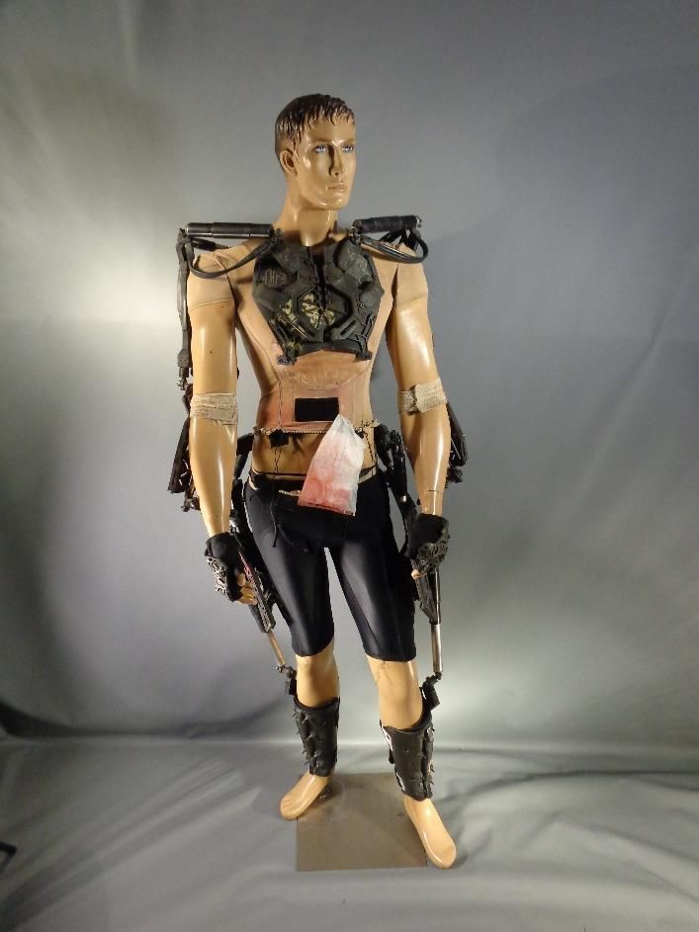
references/model07.jpg
