01binary/elysium-max-exoskeleton/references/model09.jpg

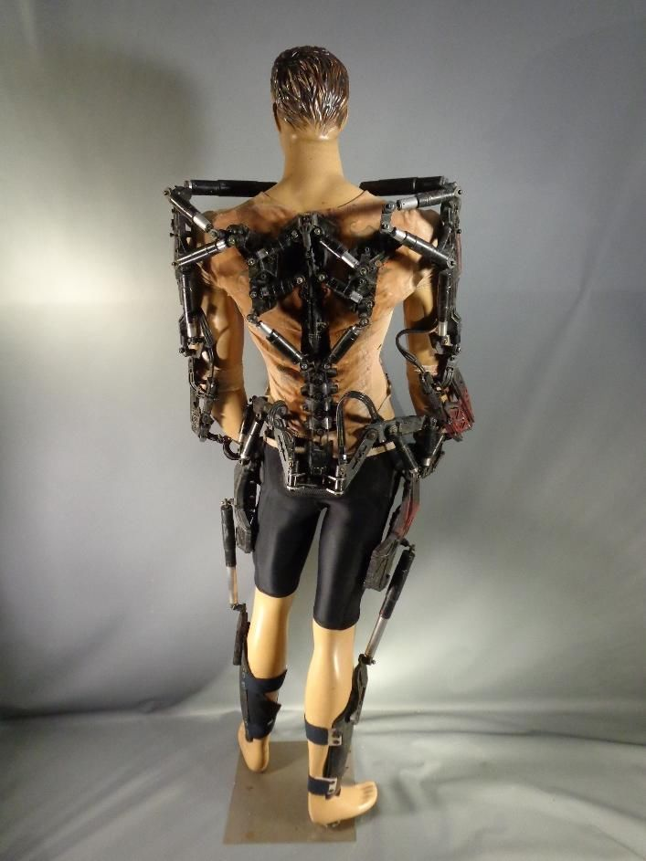
references/model09.jpg
