01binary/elysium-max-exoskeleton/references/model052.jpg

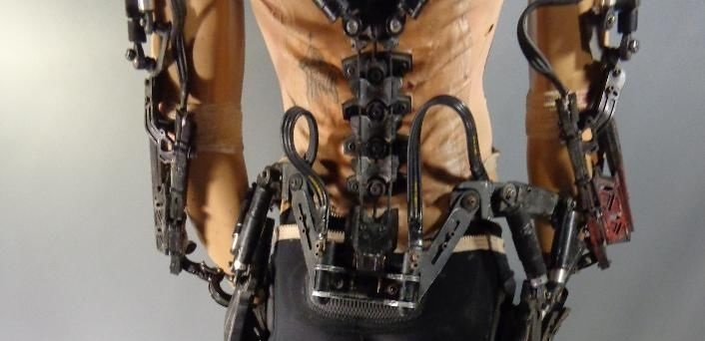
references/model052.jpg
