01binary/elysium-max-exoskeleton/references/movie03.jpg

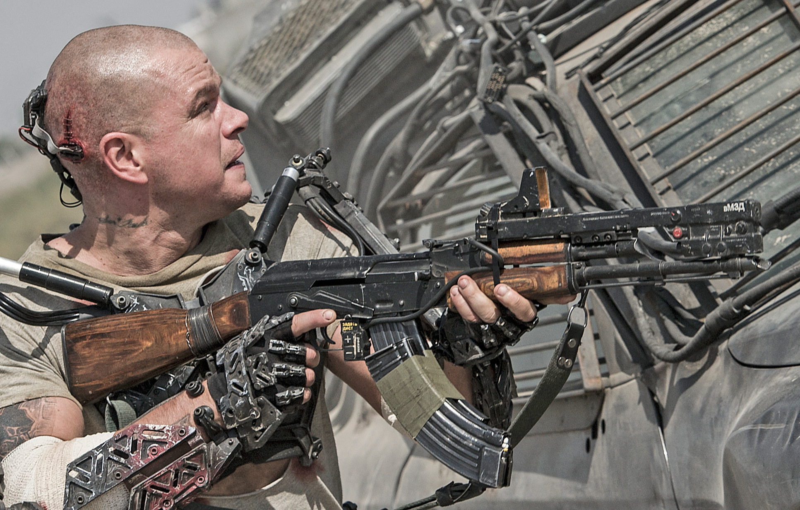
references/movie03.jpg
