01binary/elysium-max-exoskeleton/references/movie04.jpg

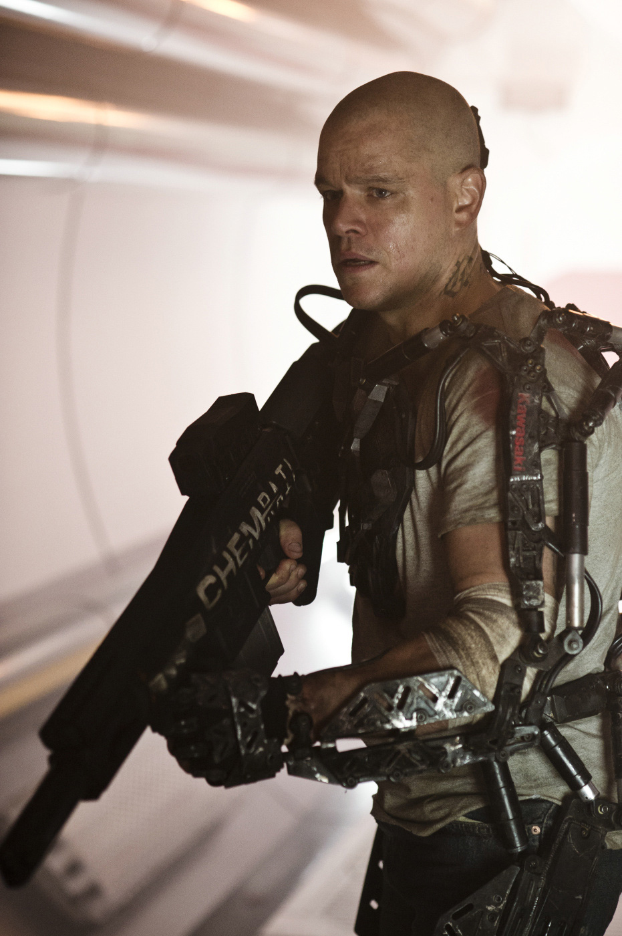
references/movie04.jpg
