01binary/elysium-max-exoskeleton/references/movie05.jpg

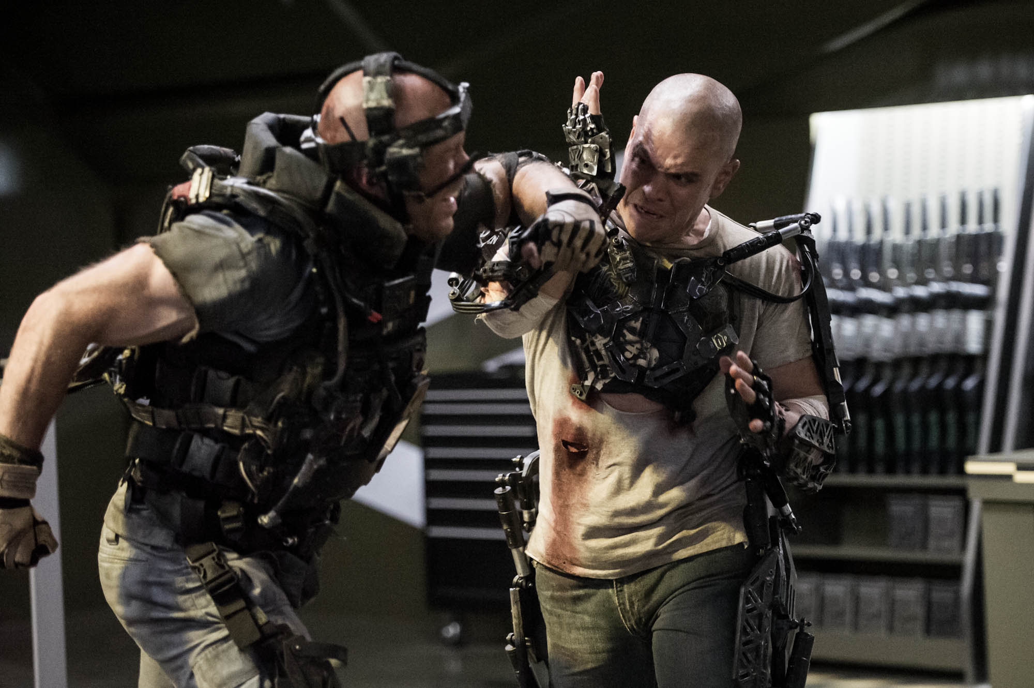
references/movie05.jpg
