01binary/elysium-max-exoskeleton/references/movie06.jpg

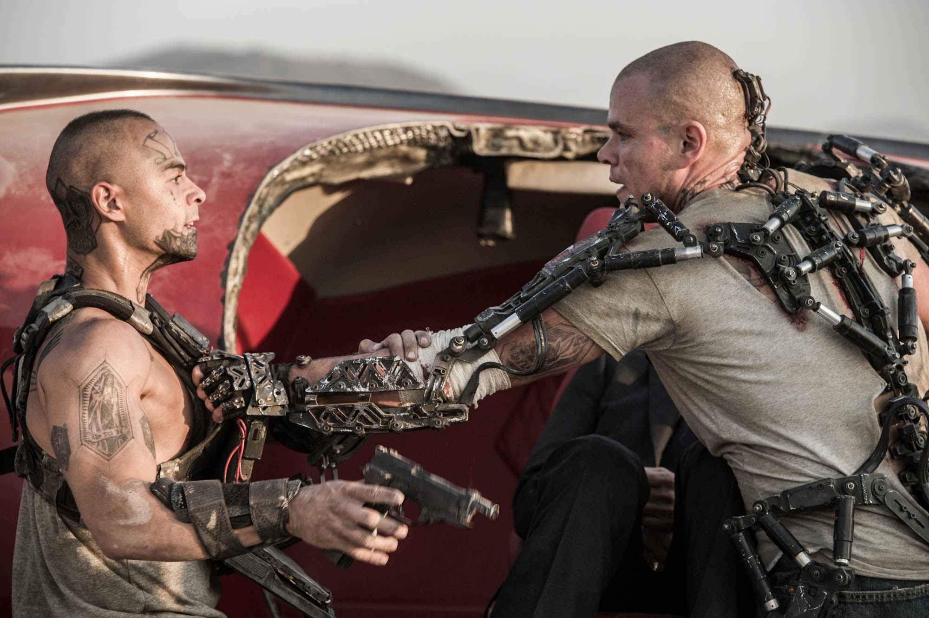
references/movie06.jpg
