01binary/elysium-max-exoskeleton/references/movie07.jpg

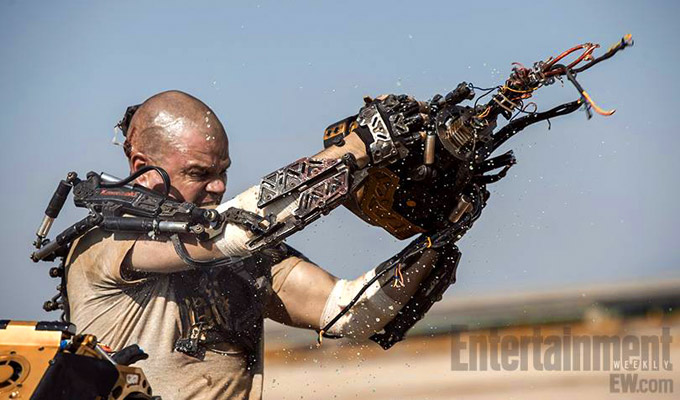
references/movie07.jpg
