01binary/elysium-max-exoskeleton/references/movie08.jpg

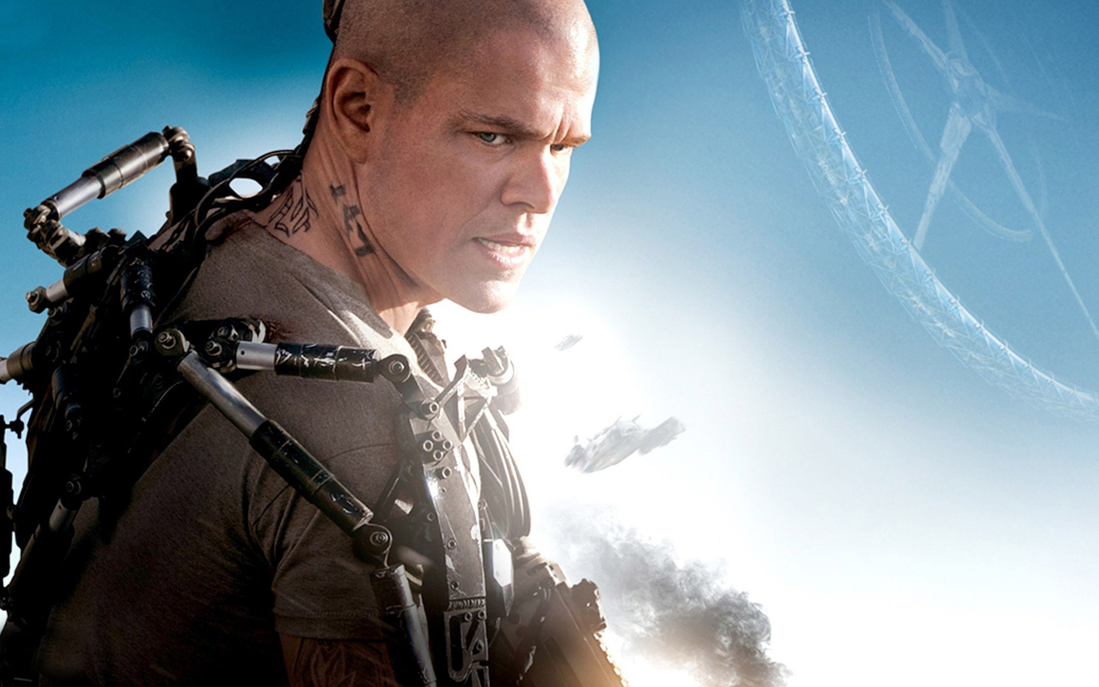
references/movie08.jpg
