01binary/elysium-max-exoskeleton/references/movie11.jpg

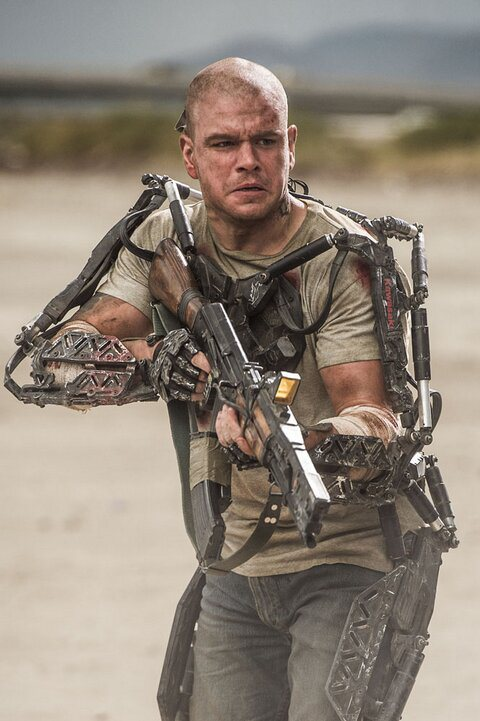
references/movie11.jpg
