01binary/elysium-max-exoskeleton/references/palm-scheme-ref.jpg

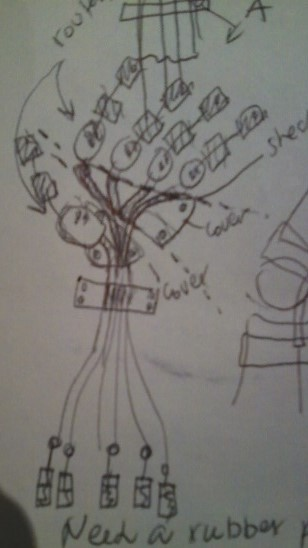
references/palm-scheme-ref.jpg
