01binary/elysium-max-exoskeleton/references/pants.bmp

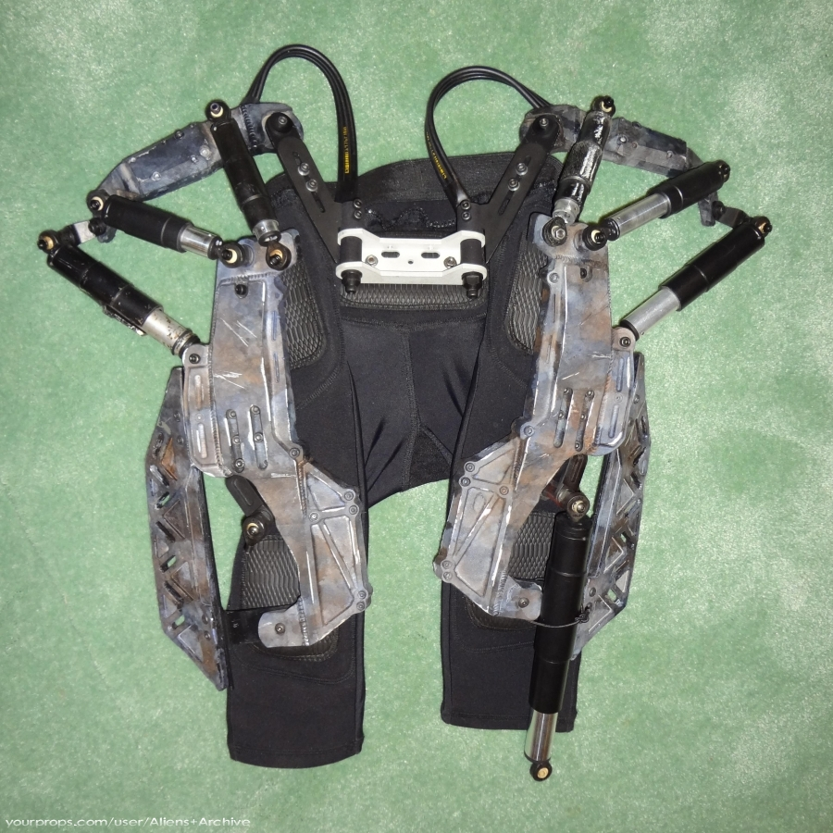
references/pants.bmp
