01binary/elysium-max-exoskeleton/references/piston-swivels-partnumber.jpg

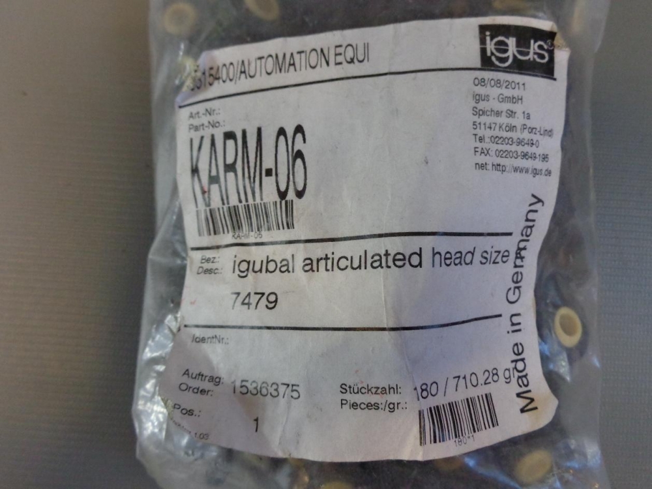
references/piston-swivels-partnumber.jpg
