01binary/elysium-max-exoskeleton/references/pistone-pipes.jpg

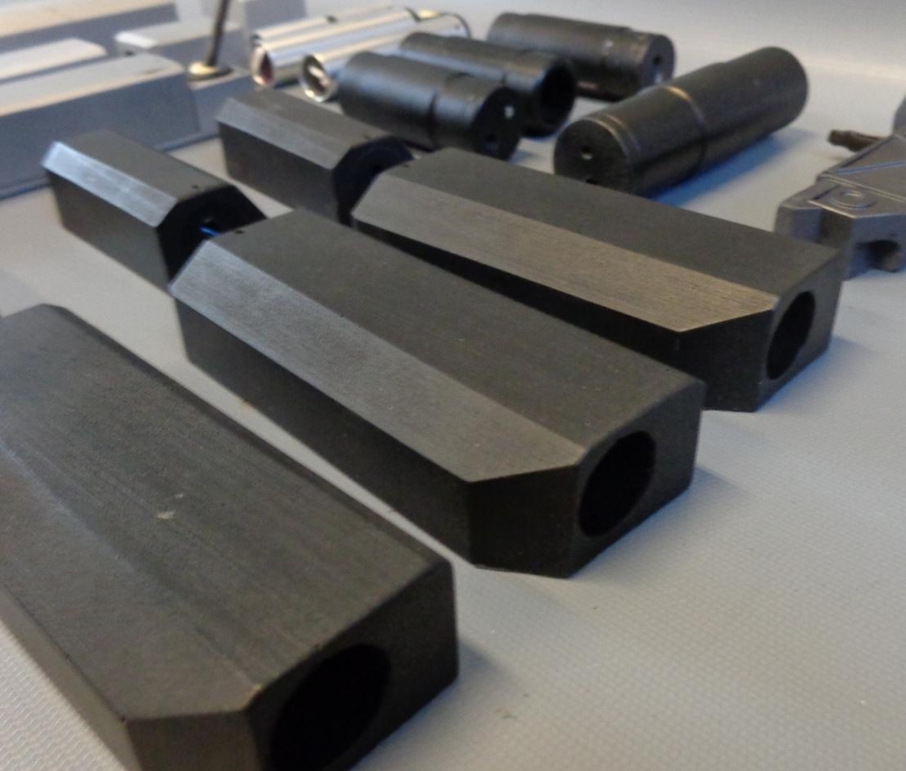
references/pistone-pipes.jpg
