01binary/elysium-max-exoskeleton/references/pistons.jpg

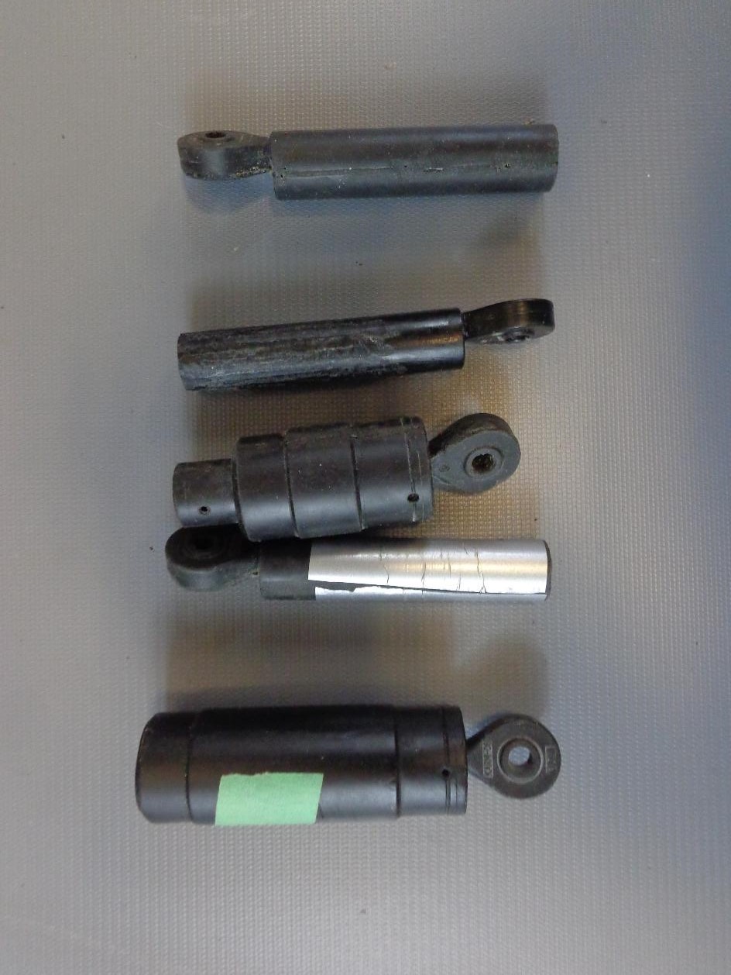
references/pistons.jpg
