01binary/elysium-max-exoskeleton/references/plate-connector-1.JPG

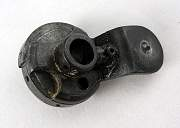
references/plate-connector-1.JPG
