01binary/elysium-max-exoskeleton/references/production01.png

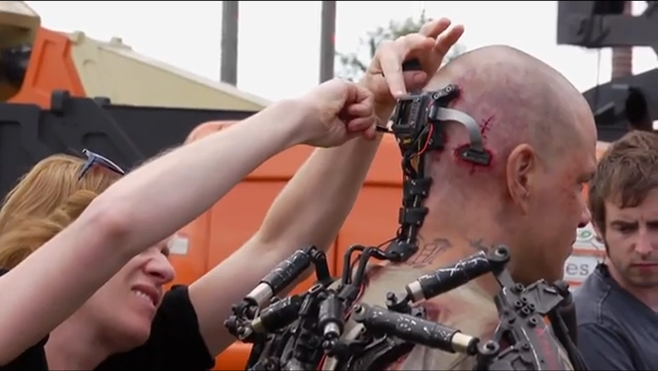
references/production01.png
