01binary/elysium-max-exoskeleton/references/production02.png

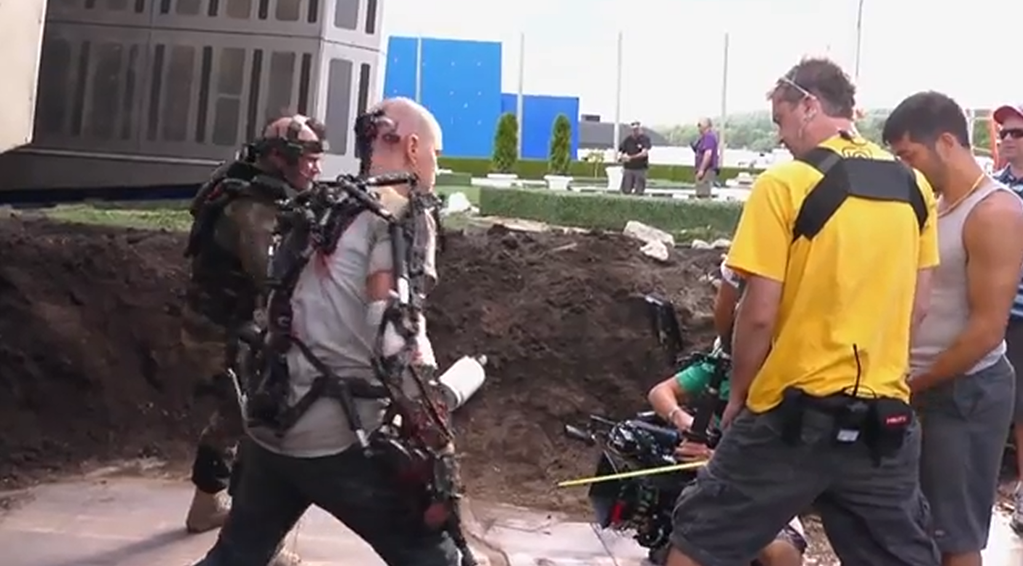
references/production02.png
