01binary/elysium-max-exoskeleton/references/production03.jpg

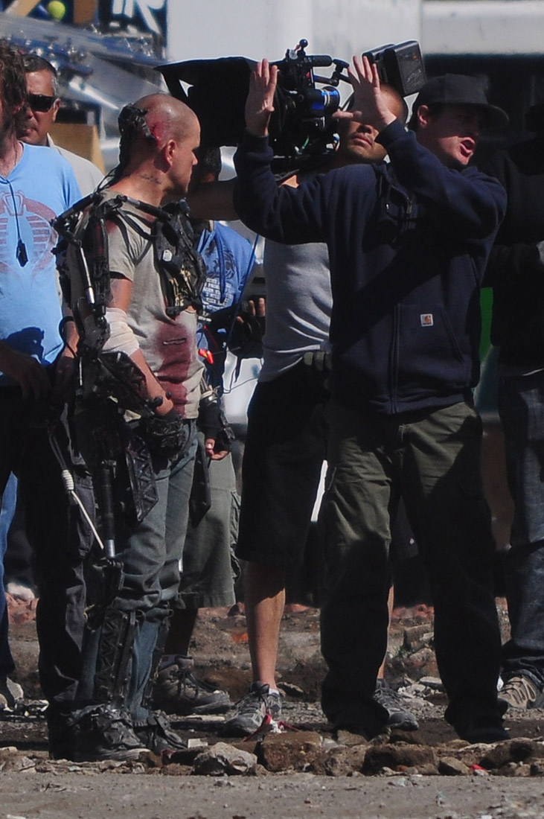
references/production03.jpg
