01binary/elysium-max-exoskeleton/references/refmodel02.jpg

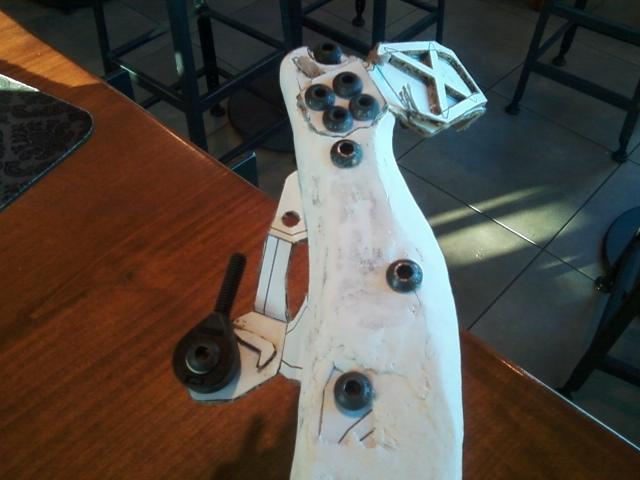
references/refmodel02.jpg
