01binary/elysium-max-exoskeleton/references/refmodel03.jpg

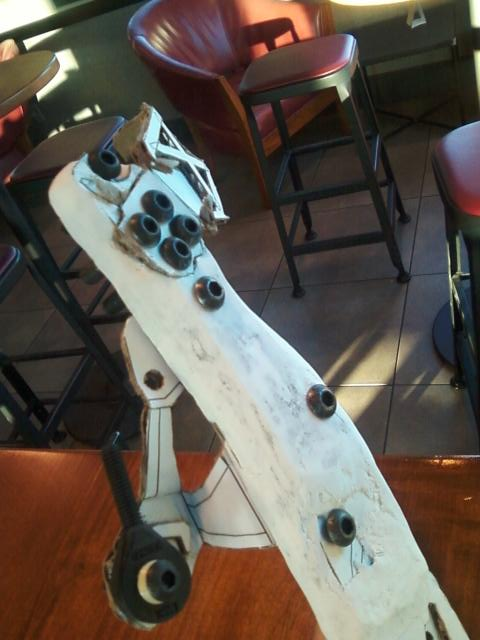
references/refmodel03.jpg
