01binary/elysium-max-exoskeleton/references/screencap02.jpg

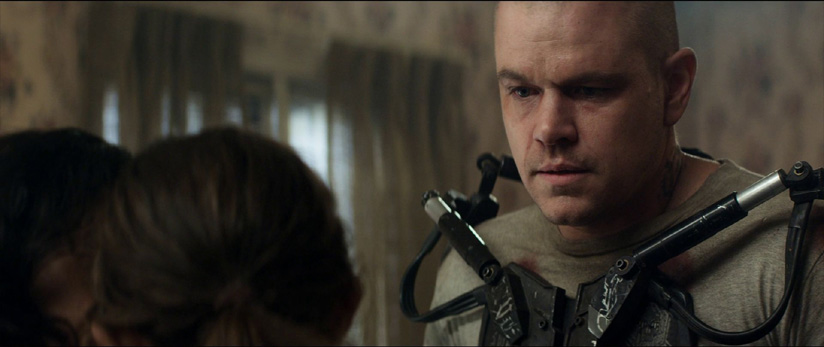
references/screencap02.jpg
