01binary/elysium-max-exoskeleton/references/screencap04.jpg

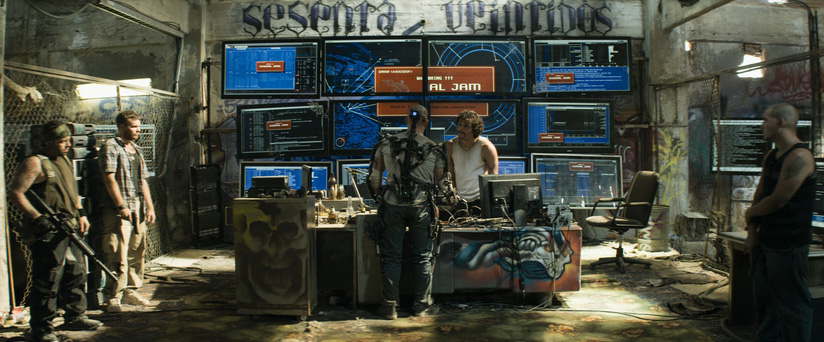
references/screencap04.jpg
