01binary/elysium-max-exoskeleton/references/screencap05.jpg

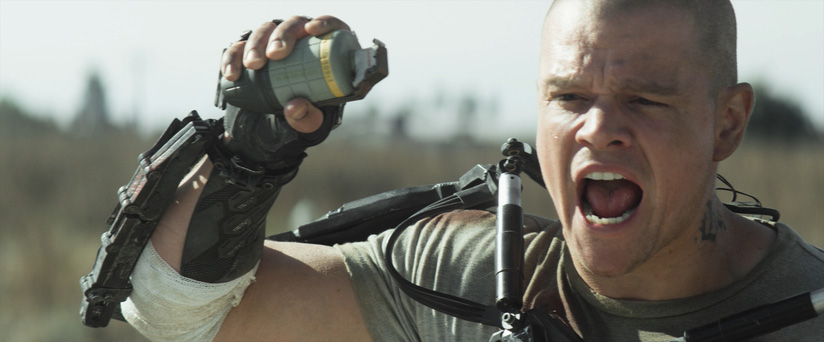
references/screencap05.jpg
