01binary/elysium-max-exoskeleton/references/screencap07.jpg

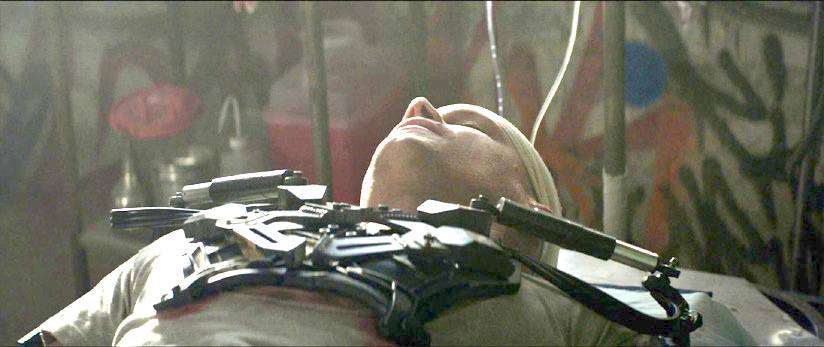
references/screencap07.jpg
