01binary/elysium-max-exoskeleton/references/screencap09.jpg

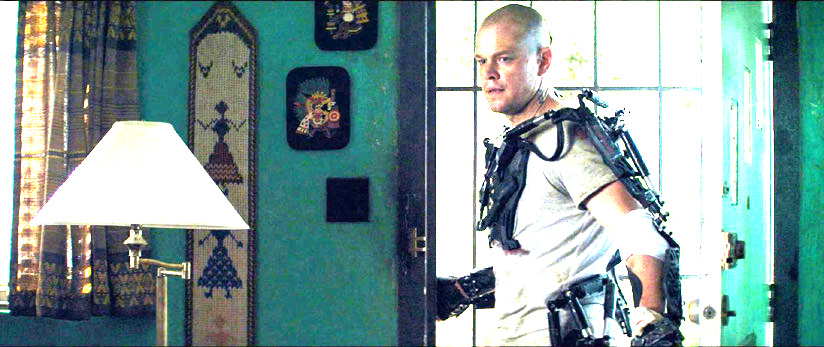
references/screencap09.jpg
