01binary/elysium-max-exoskeleton/references/screencap10.jpg

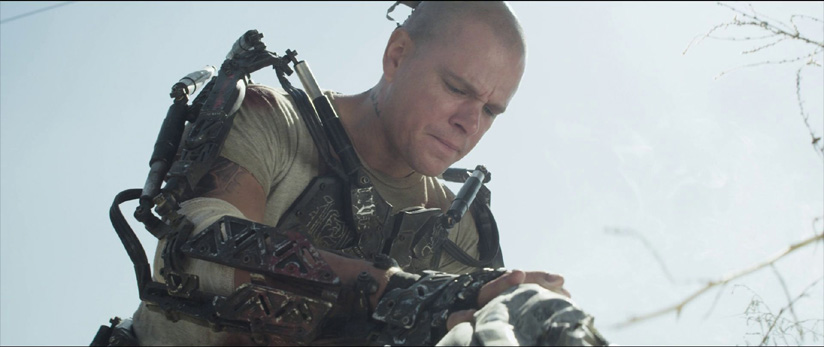
references/screencap10.jpg
