01binary/elysium-max-exoskeleton/references/screencap14.jpg

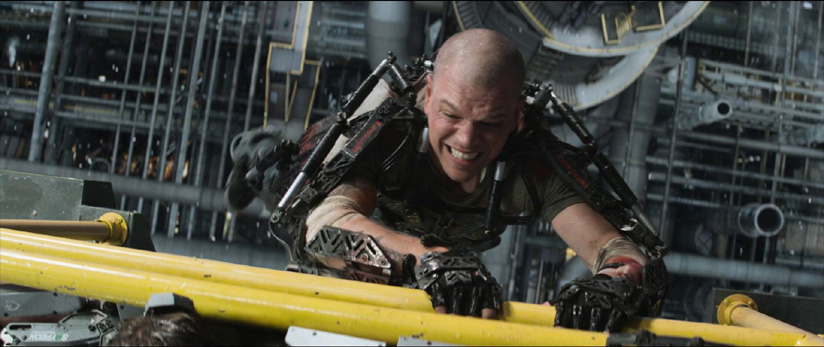
references/screencap14.jpg
