01binary/elysium-max-exoskeleton/references/screencap16.jpg

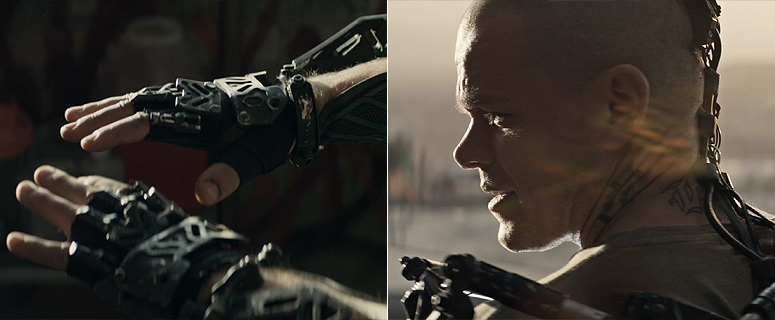
references/screencap16.jpg
