01binary/elysium-max-exoskeleton/references/screencap-spine.jpg

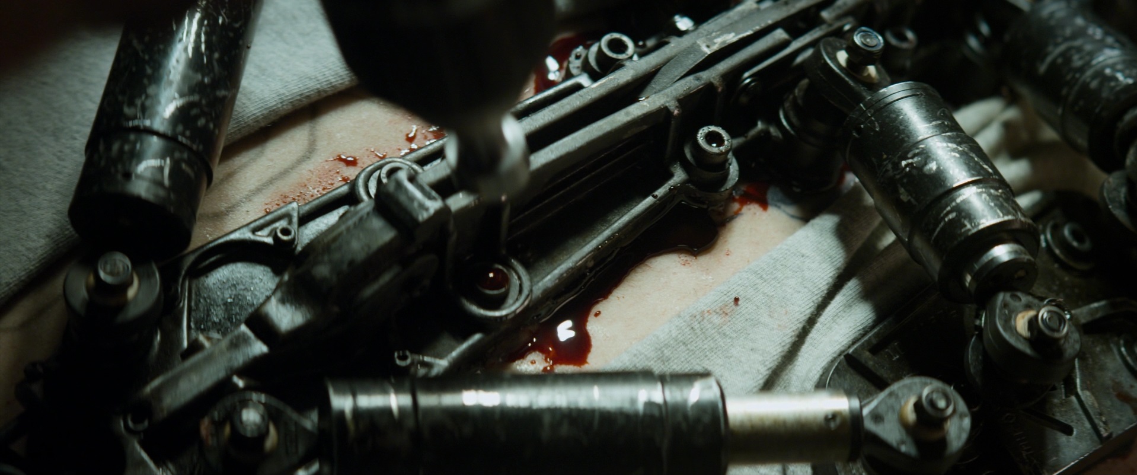
references/screencap-spine.jpg
