01binary/elysium-max-exoskeleton/references/shoeplates.jpg

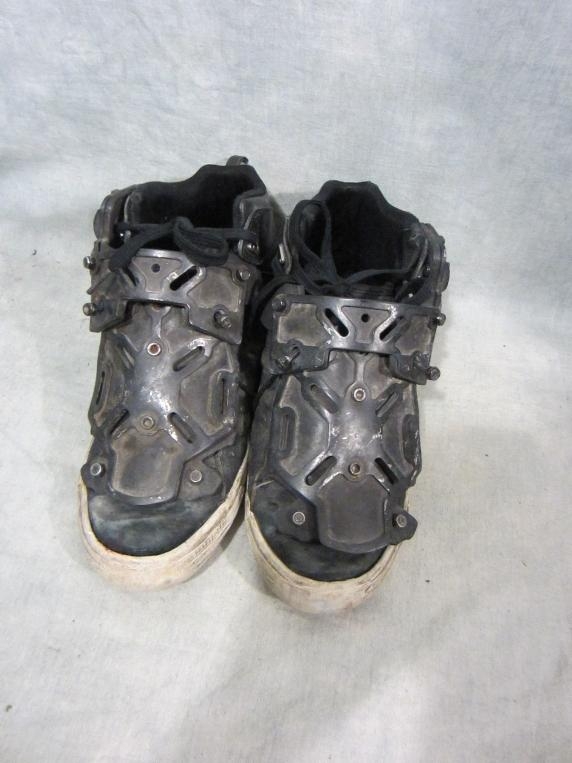
references/shoeplates.jpg
