01binary/elysium-max-exoskeleton/references/shoulder spine plates.jpg

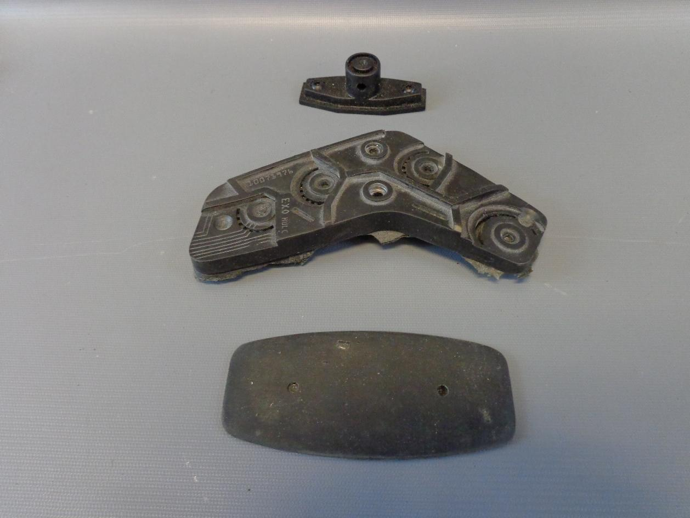
references/shoulder spine plates.jpg
