01binary/elysium-max-exoskeleton/references/slinkref.jpg

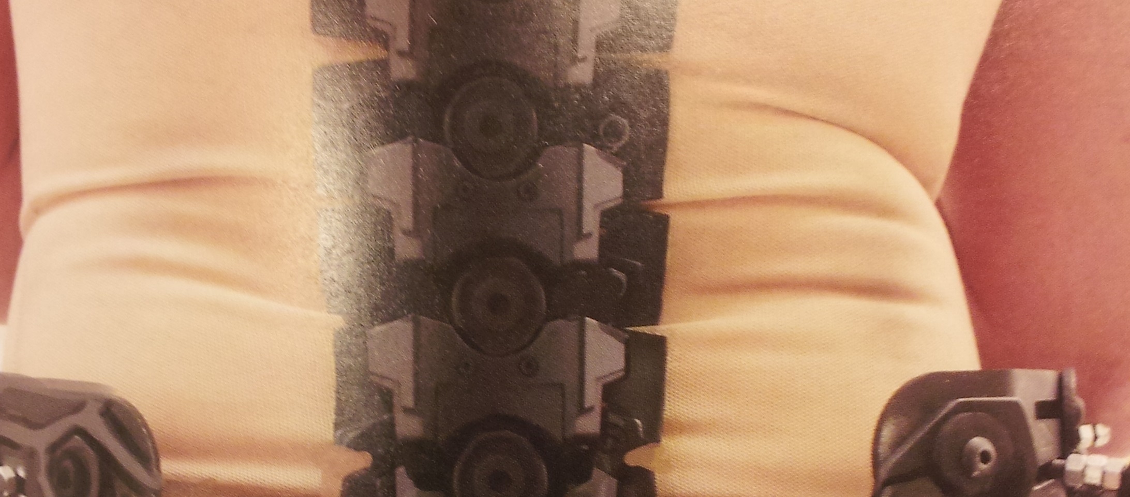
references/slinkref.jpg
