01binary/elysium-max-exoskeleton/references/spine detail top2.png

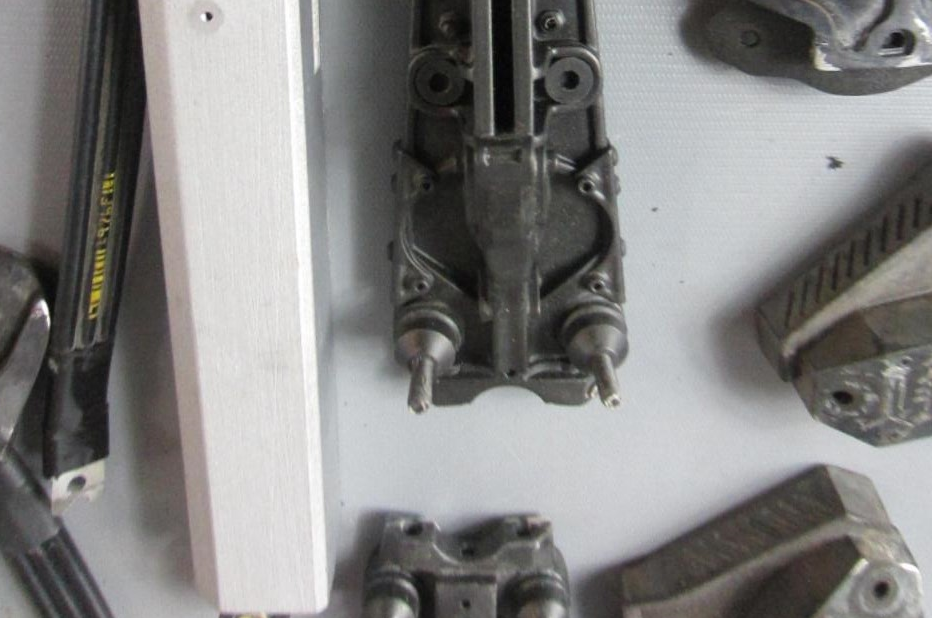
references/spine detail top2.png
