01binary/elysium-max-exoskeleton/references/spine-all.png

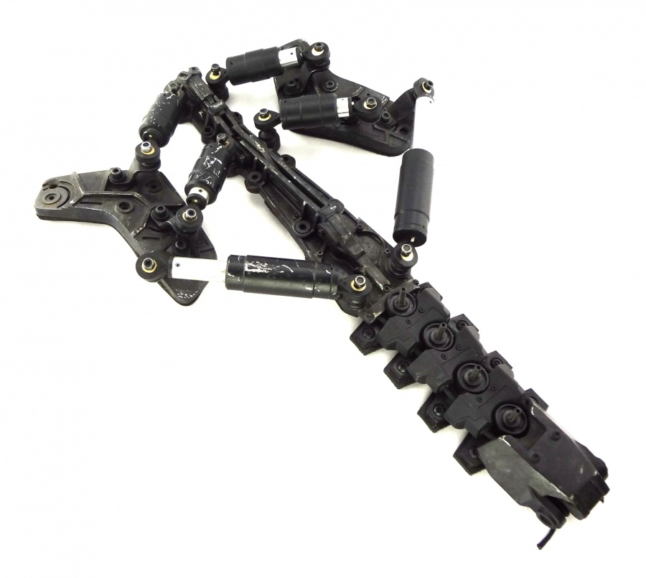
references/spine-all.png
