01binary/elysium-max-exoskeleton/references/spine-and-shoulder-blades.jpg

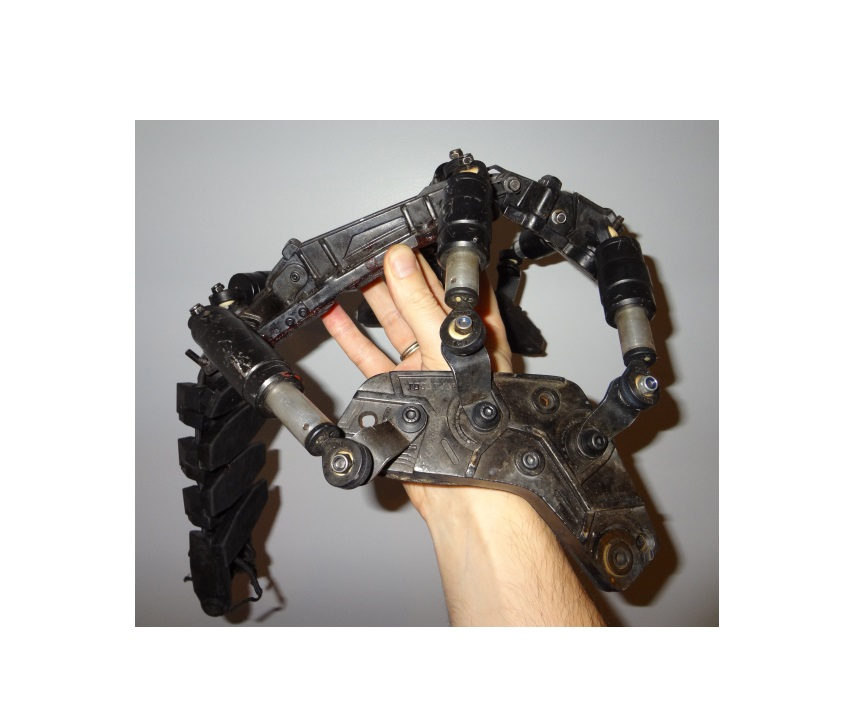
references/spine-and-shoulder-blades.jpg
