01binary/elysium-max-exoskeleton/references/spine-detail.png

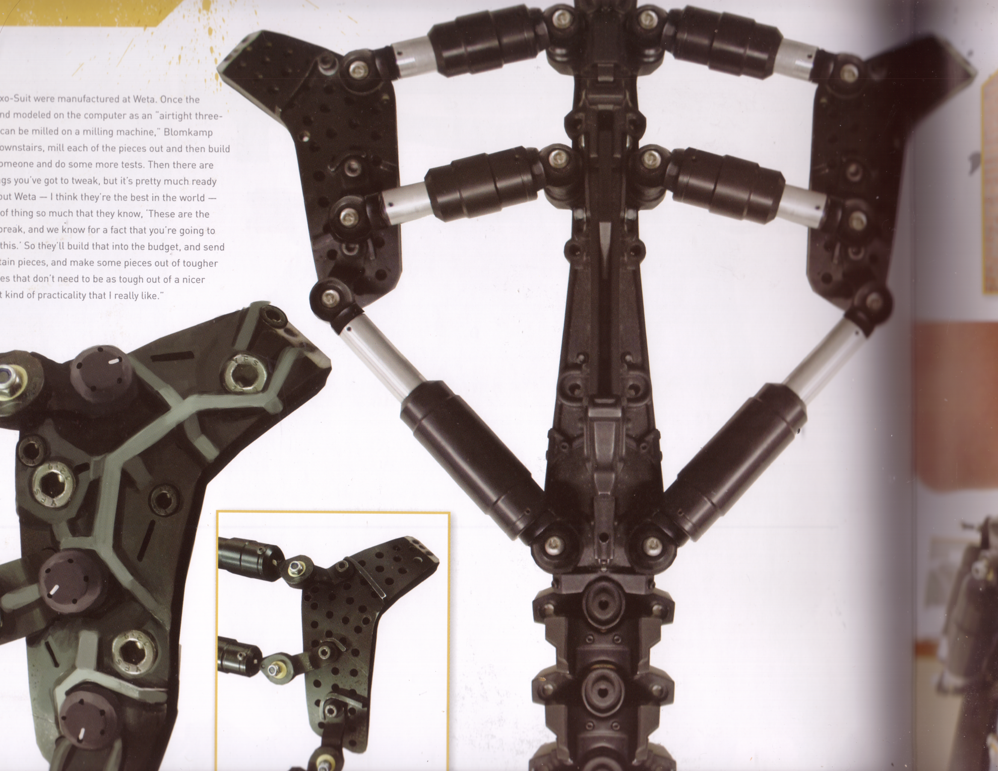
references/spine-detail.png
