01binary/elysium-max-exoskeleton/references/sprint-detail-top2.jpg

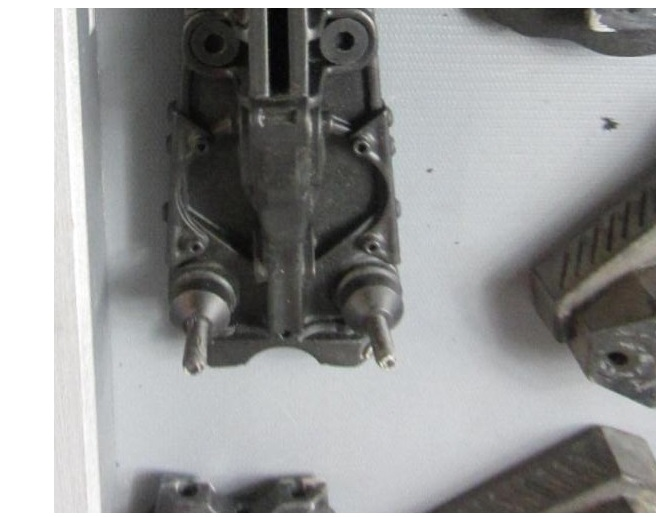
references/sprint-detail-top2.jpg
