01binary/elysium-max-exoskeleton/references/the-magic-behind-matt-damons-suit-in-elysium-preview.jpg

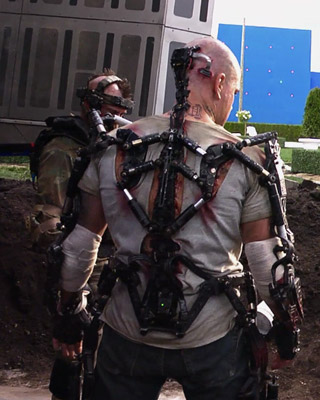
references/the-magic-behind-matt-damons-suit-in-elysium-preview.jpg
