01binary/elysium-max-exoskeleton/references/upperarmconnector.jpg

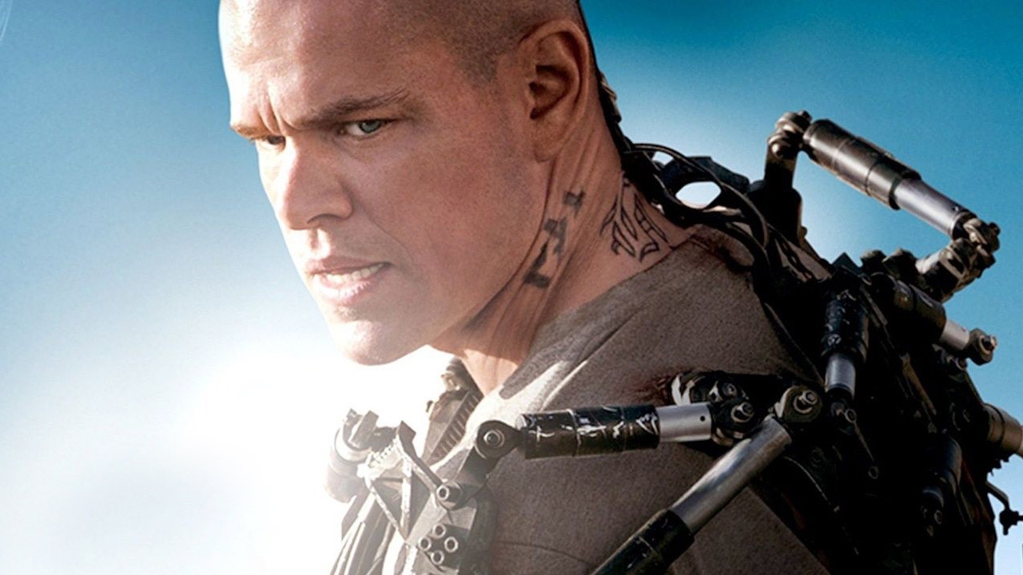
references/upperarmconnector.jpg
