01binary/elysium-max-exoskeleton/references/WetaProps9.jpg

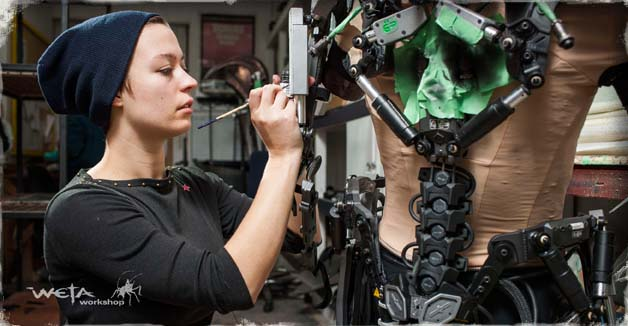
references/WetaProps9.jpg
