01binary/elysium-max-exoskeleton/references/WetaProps13.jpg

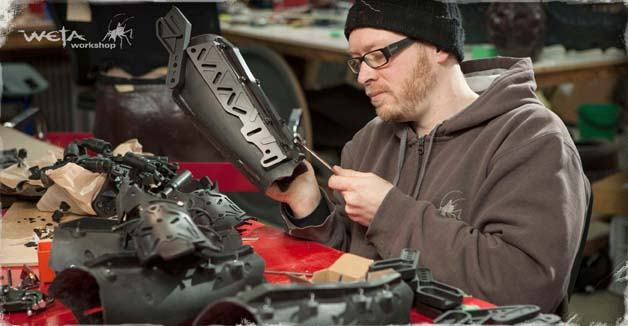
references/WetaProps13.jpg
