01binary/elysium-max-exoskeleton/references/WetaSpecialityCostume4.jpg

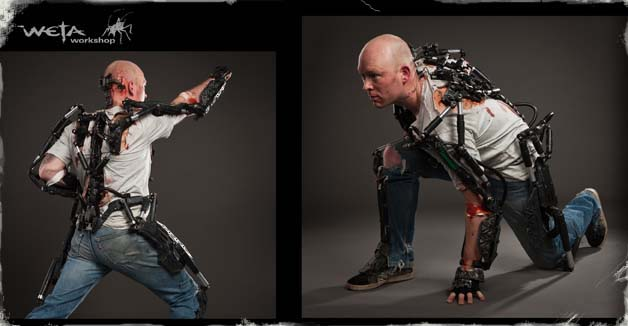
references/WetaSpecialityCostume4.jpg
