01binary/elysium-max-exoskeleton/references/WetaWorkshopElysiumWork043b.jpg

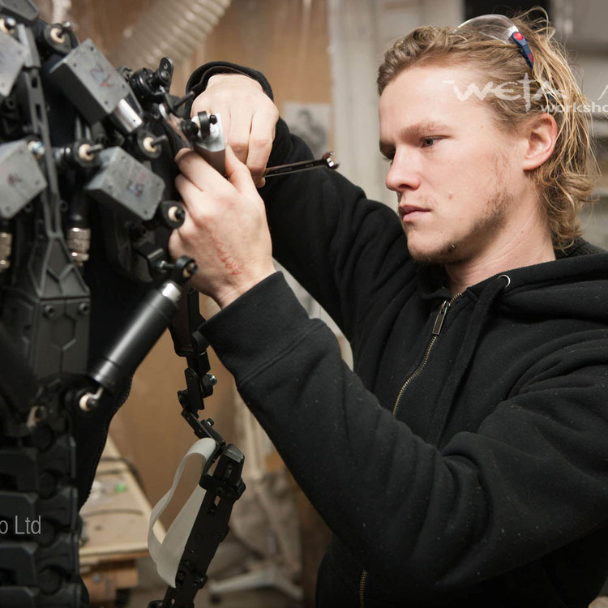
references/WetaWorkshopElysiumWork043b.jpg
