01binary/elysium-max-exoskeleton/references/WetaWorkshopElysiumWork089.jpg

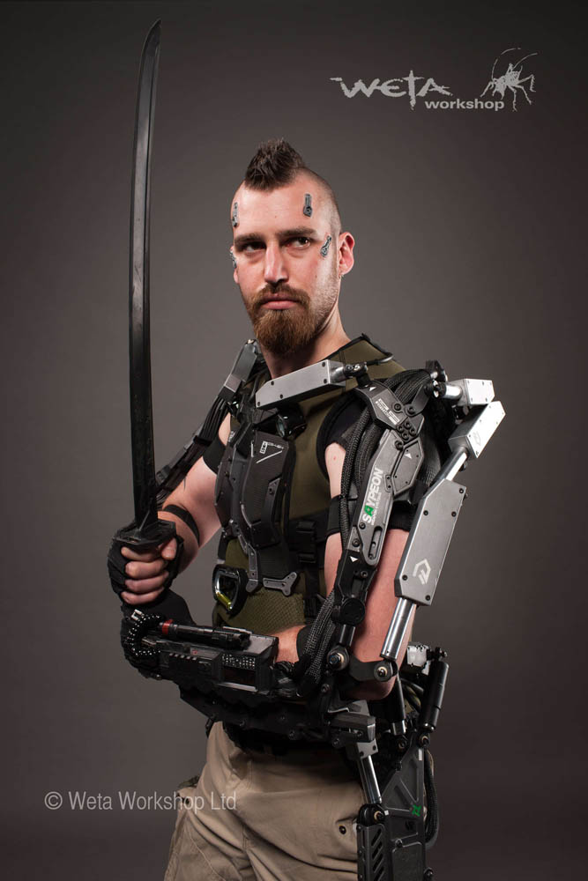
references/WetaWorkshopElysiumWork089.jpg
