01binary/elysium-max-exoskeleton/references/WetaWorkshopElysiumWork090.jpg

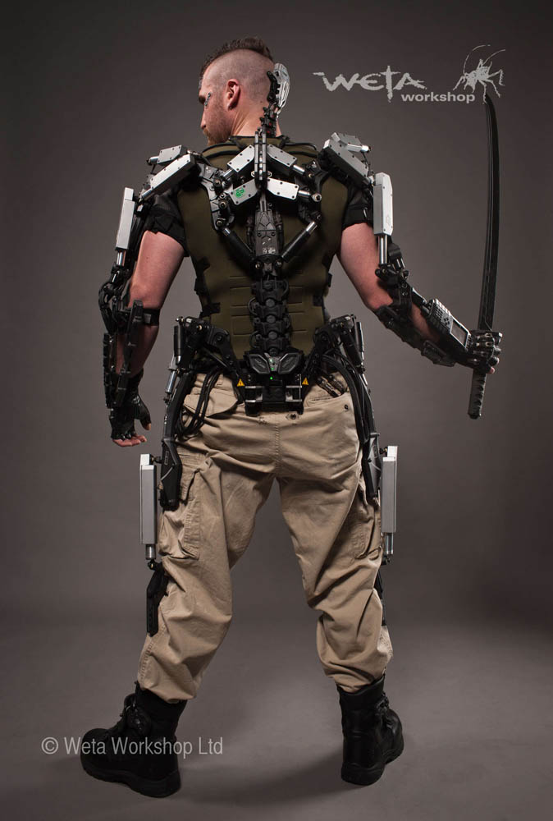
references/WetaWorkshopElysiumWork090.jpg
