01binary/elysium-max-exoskeleton/render/iso.png

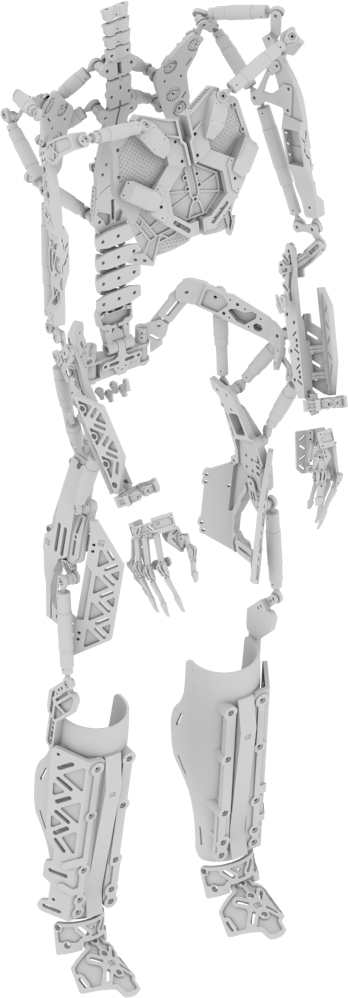
render/iso.png
