01binary/elysium-max-exoskeleton/render/top.png

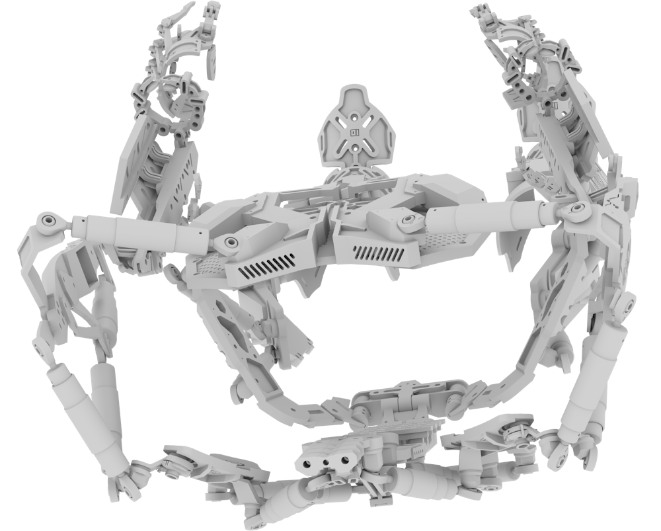
render/top.png
