01binary/elysium-max-exoskeleton/view/Exoskeleton.png

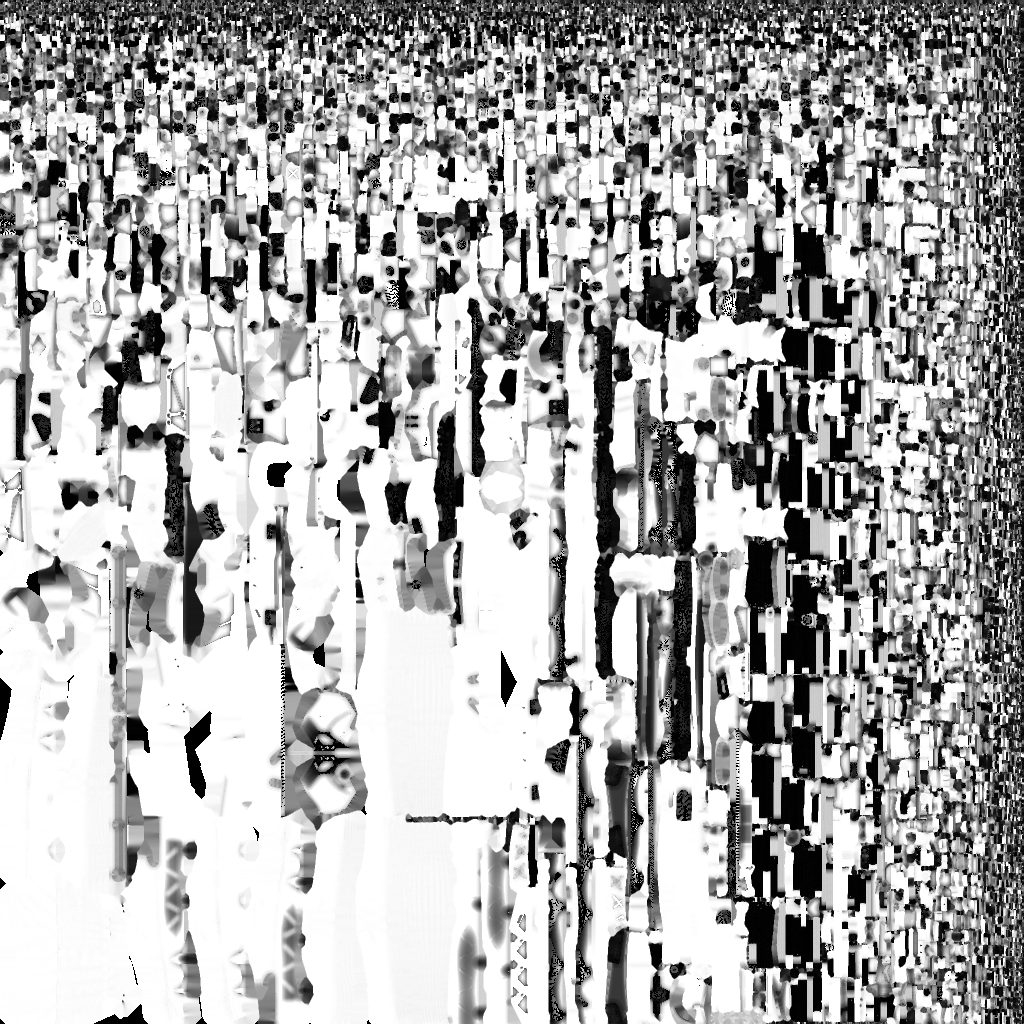
view/Exoskeleton.png
