01binary/elysium-max-exoskeleton/build/arm-parts.JPG

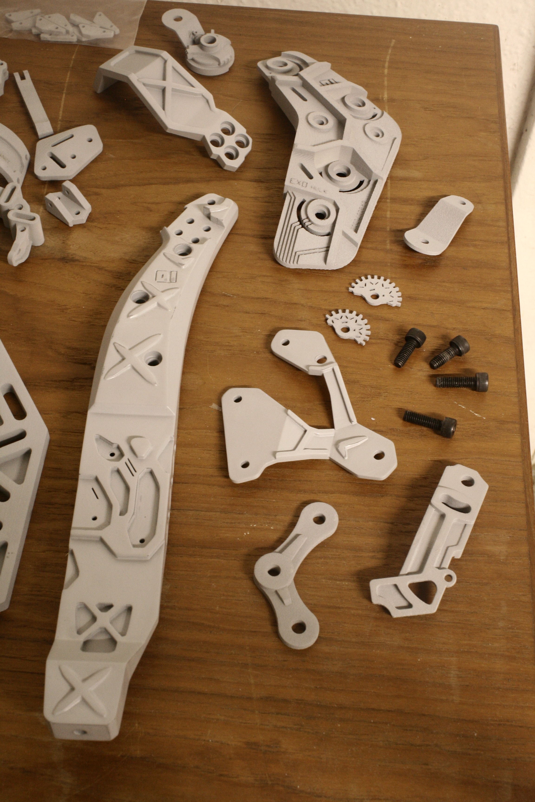
build/arm-parts.JPG
