01binary/elysium-max-exoskeleton/build/inventor-hand-parts01.png

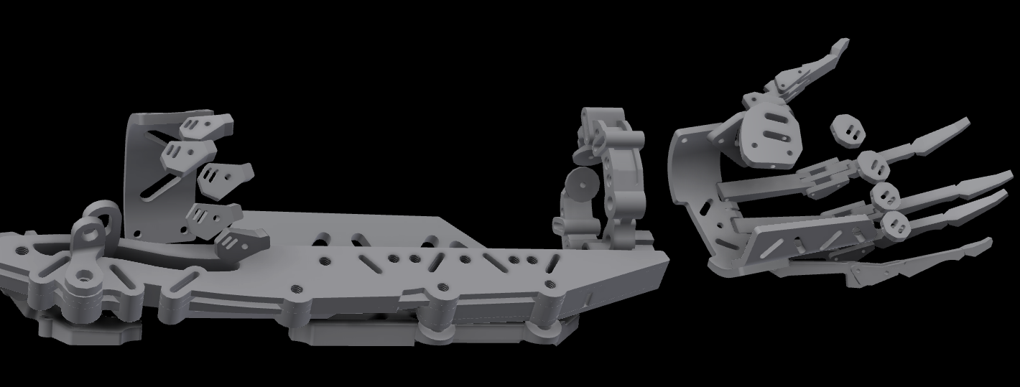
build/inventor-hand-parts01.png
