01binary/elysium-max-exoskeleton/build/inventor-hand-parts02.png

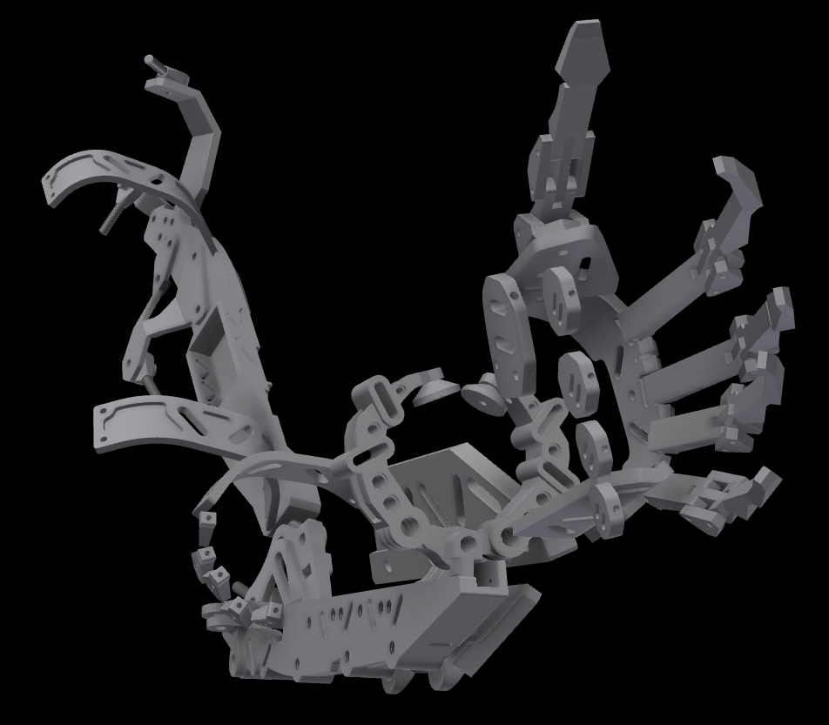
build/inventor-hand-parts02.png
