01binary/elysium-max-exoskeleton/build/inventor-spine-parts.png

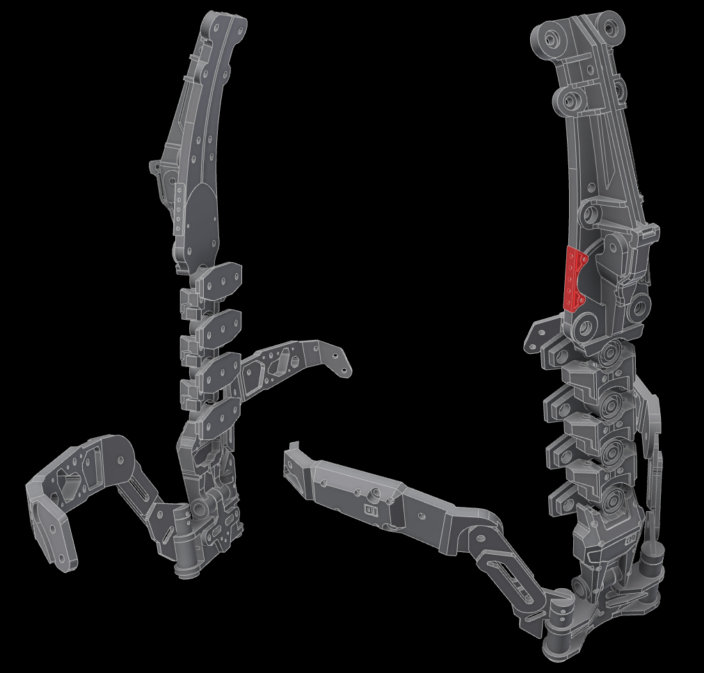
build/inventor-spine-parts.png
