01binary/elysium-max-exoskeleton/build/parts-polished01.JPG

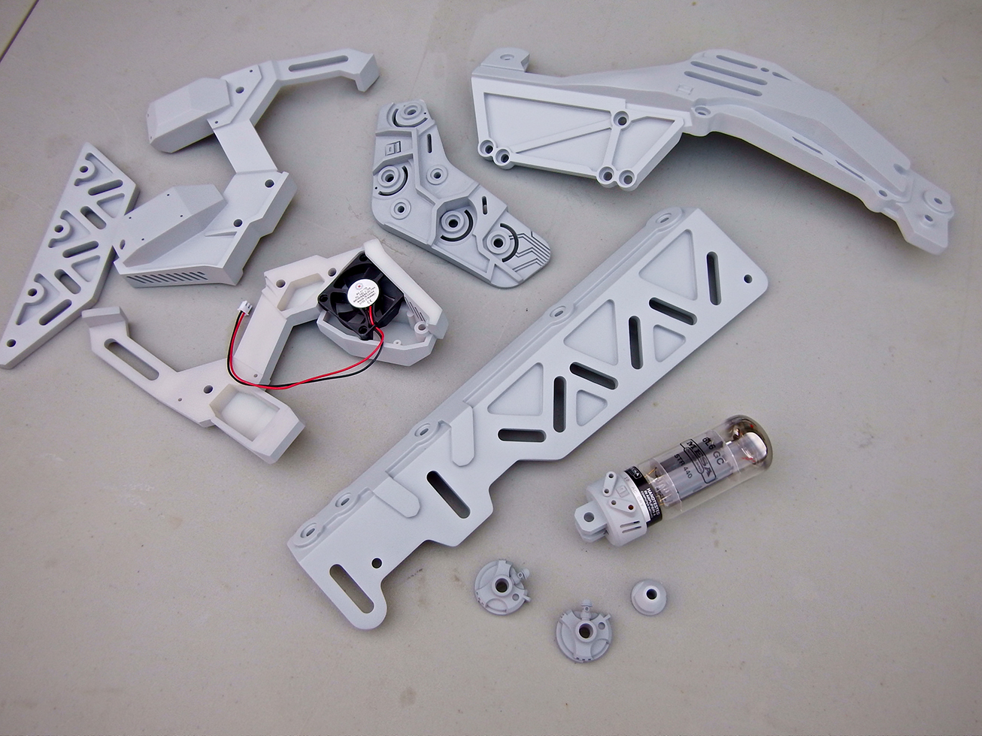
build/parts-polished01.JPG
