01binary/elysium-max-exoskeleton/build/parts-polished02.JPG

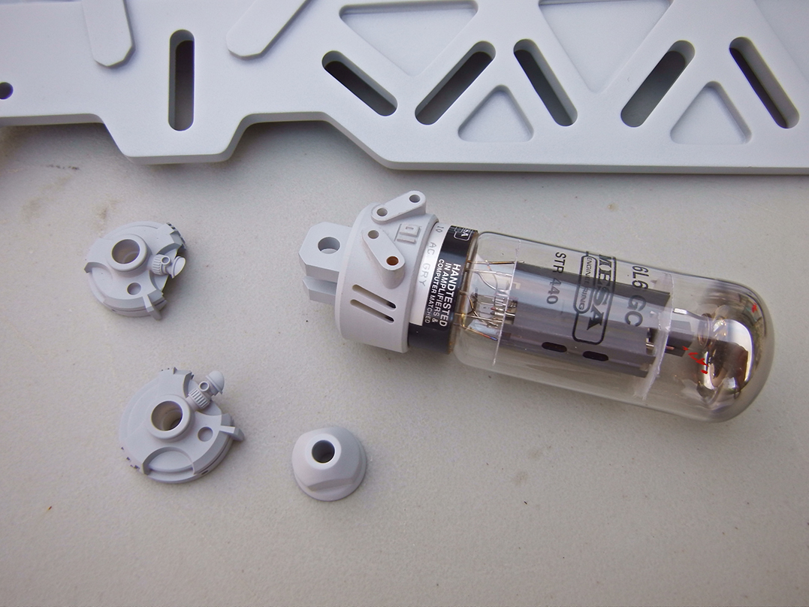
build/parts-polished02.JPG
