01binary/elysium-max-exoskeleton/build/parts-polished03.JPG

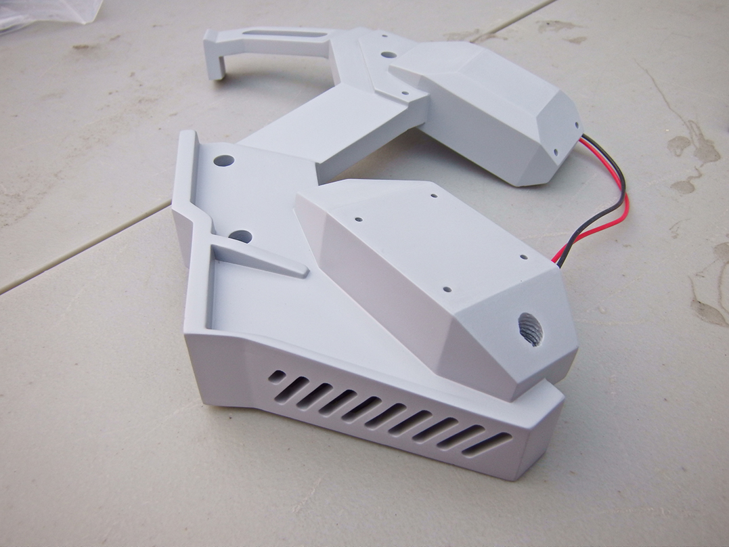
build/parts-polished03.JPG
