01binary/elysium-max-exoskeleton/build/piston-inventor-parts.png

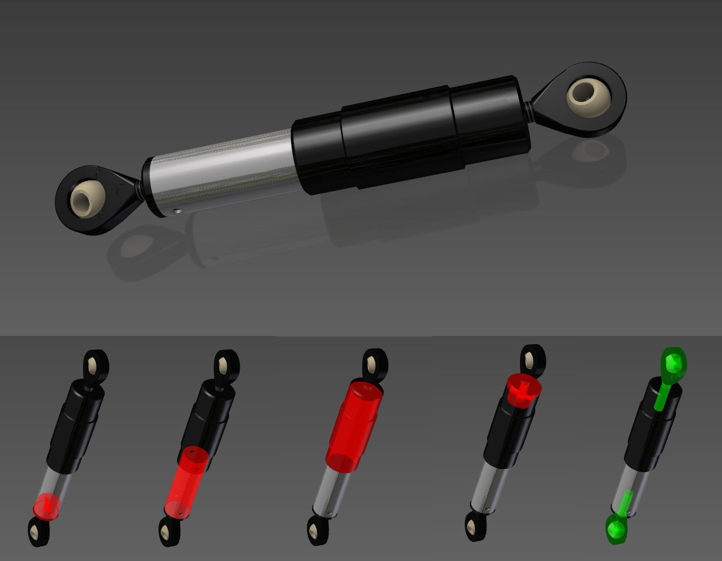
build/piston-inventor-parts.png
