01binary/elysium-max-exoskeleton/build/spine-inventor-parts.png

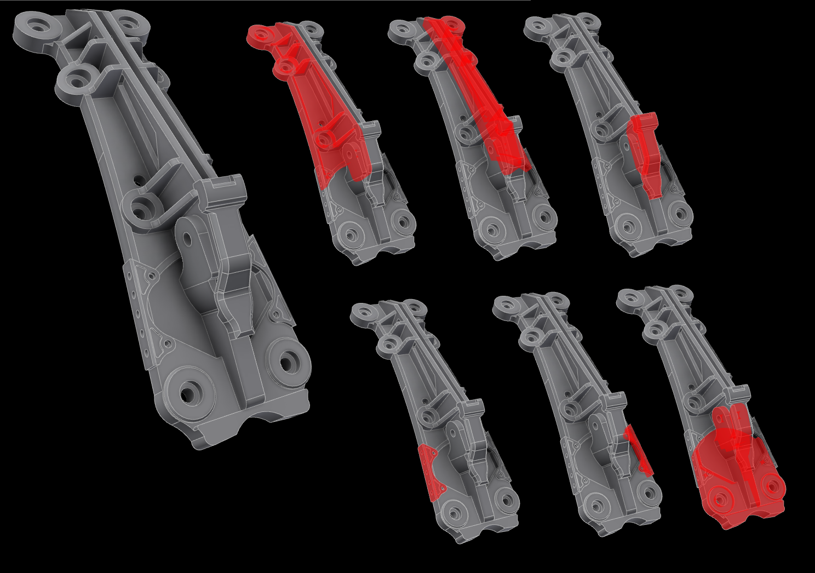
build/spine-inventor-parts.png
