01binary/elysium-max-exoskeleton/references/chest parts.jpg

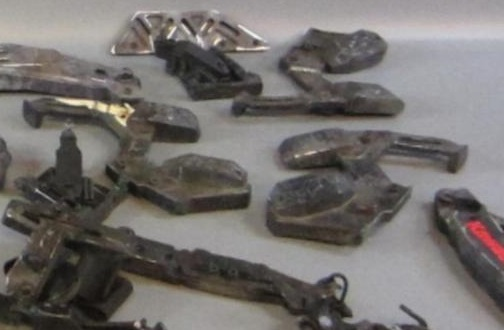
references/chest parts.jpg
