01binary/elysium-max-exoskeleton/references/Chest/more parts.jpg

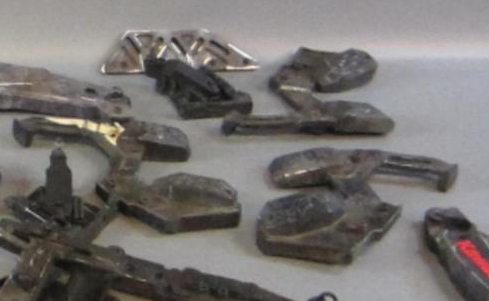
references/Chest/more parts.jpg
