01binary/elysium-max-exoskeleton/references/Chest/parts03.jpg

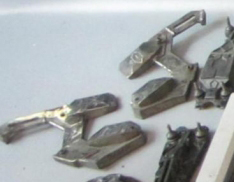
references/Chest/parts03.jpg
