01binary/elysium-max-exoskeleton/references/Chest/parts04.png

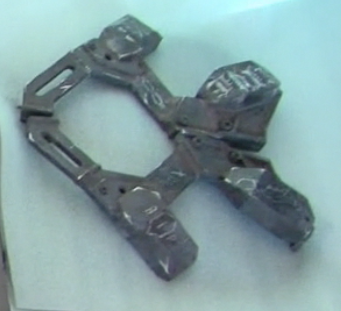
references/Chest/parts04.png
