01binary/elysium-max-exoskeleton/references/hulc-parts.jpg

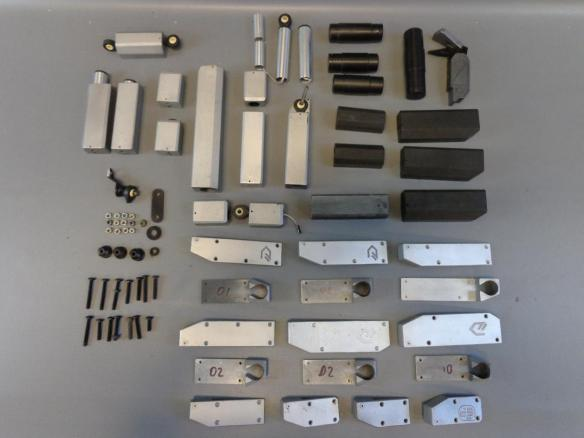
references/hulc-parts.jpg
