01binary/elysium-max-exoskeleton/references/more parts.jpg

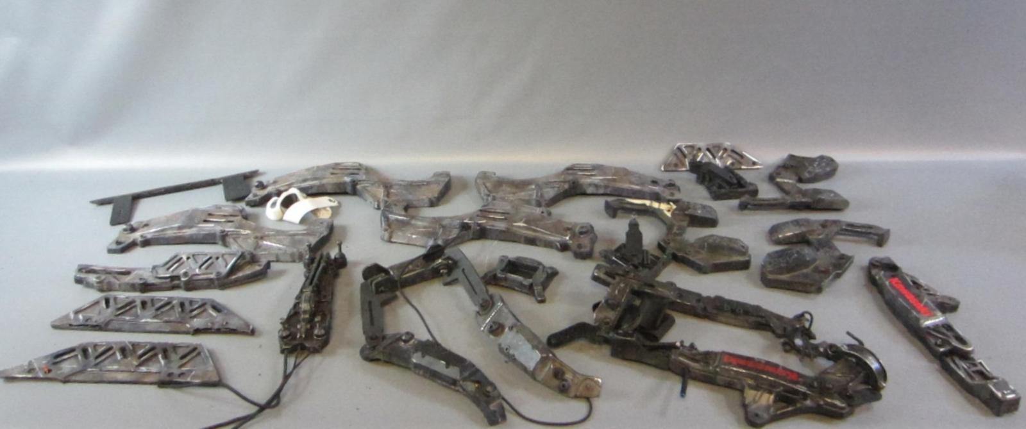
references/more parts.jpg
