01binary/elysium-max-exoskeleton/references/parts01.png

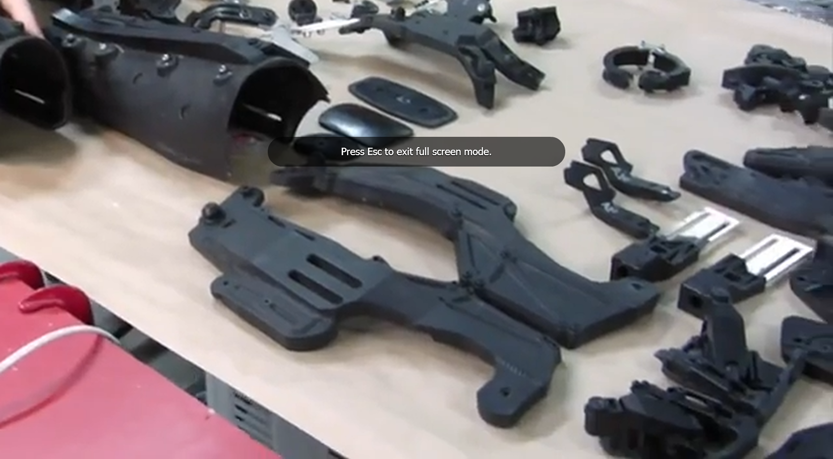
references/parts01.png
