01binary/elysium-max-exoskeleton/references/parts02.png

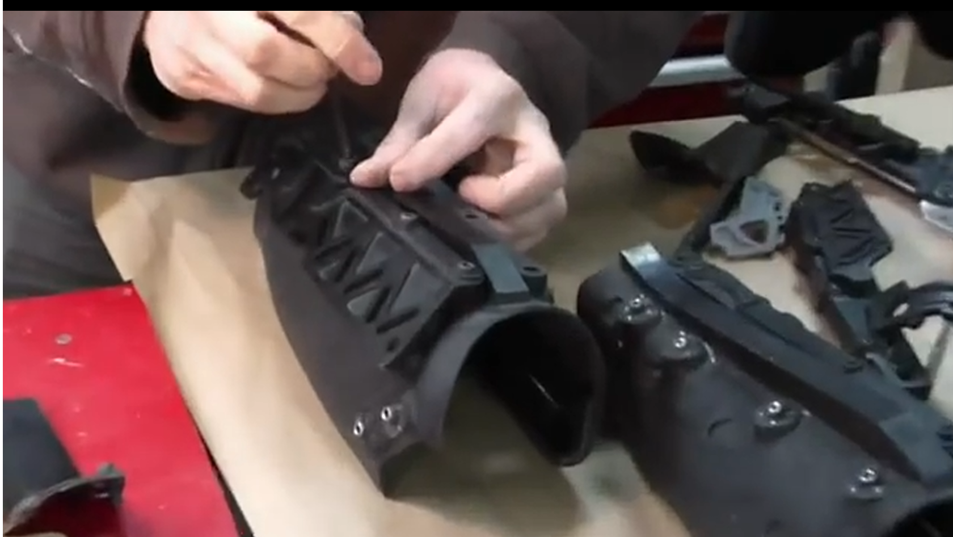
references/parts02.png
