01binary/elysium-max-exoskeleton/references/parts03 chest.jpg

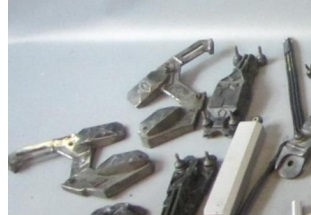
references/parts03 chest.jpg
