01binary/elysium-max-exoskeleton/references/parts03.jpg

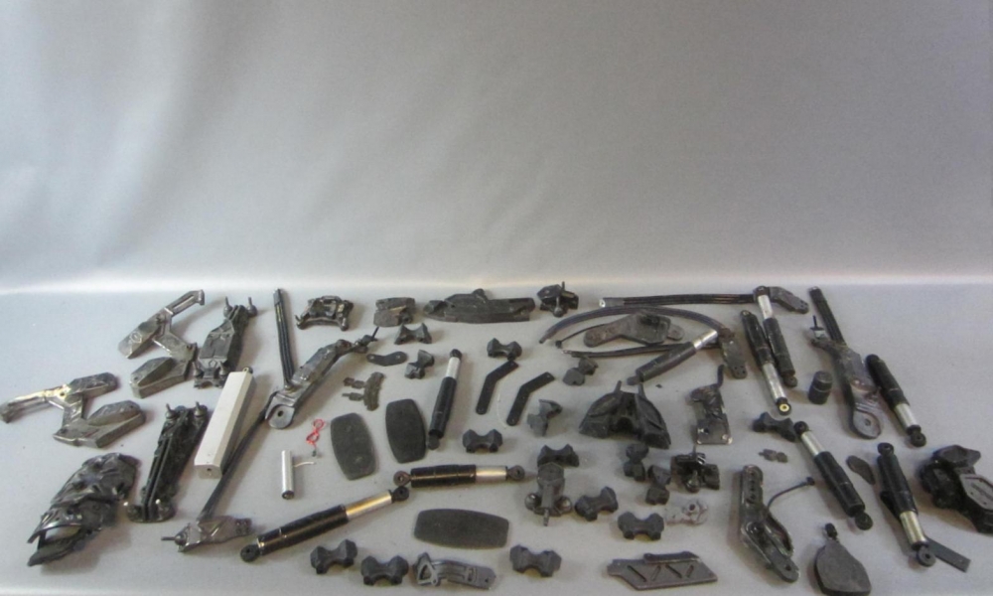
references/parts03.jpg
