01binary/elysium-max-exoskeleton/references/parts04.png

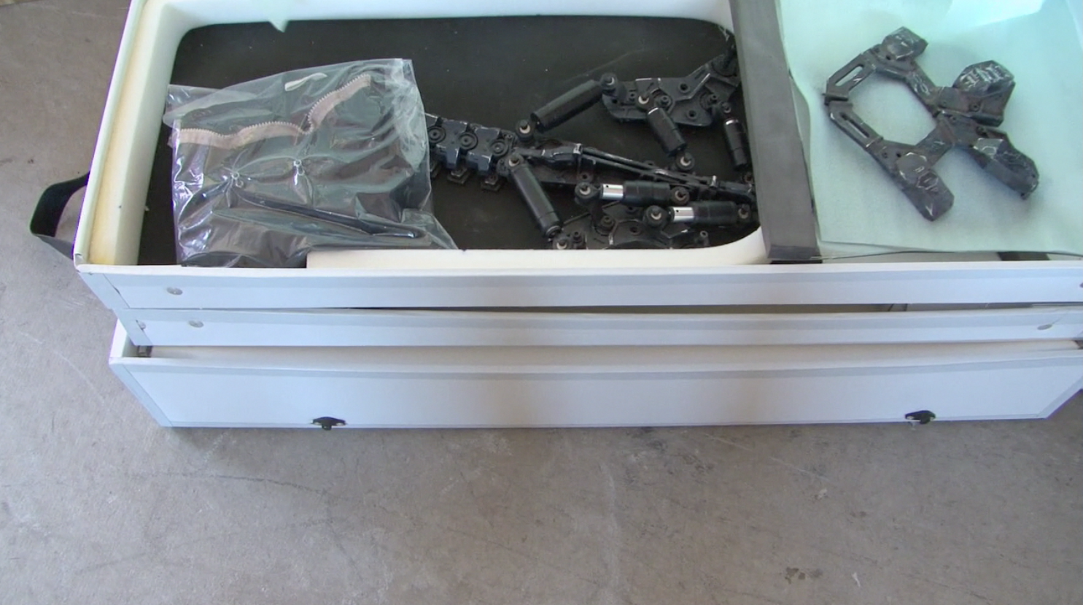
references/parts04.png
