01binary/elysium-max-exoskeleton/references/parts-1.png

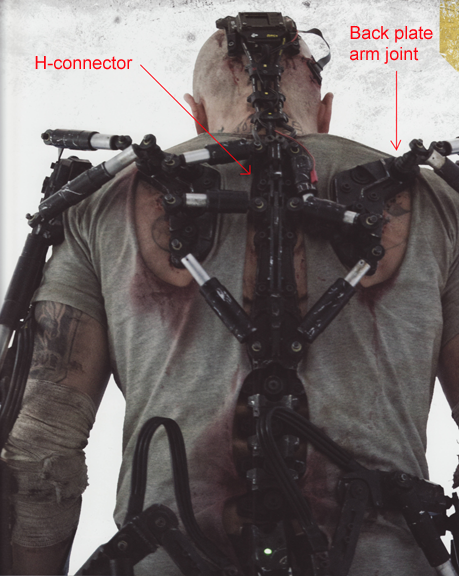
references/parts-1.png
