01binary/elysium-max-exoskeleton/references/piston-parts01.jpg

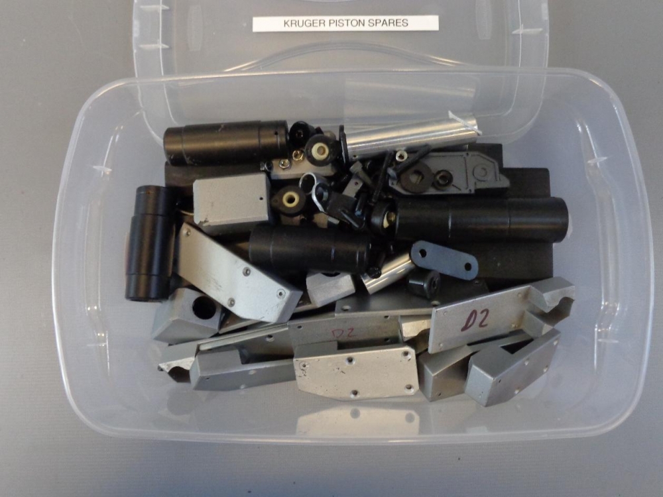
references/piston-parts01.jpg
