01binary/elysium-max-exoskeleton/references/piston-parts02.jpg

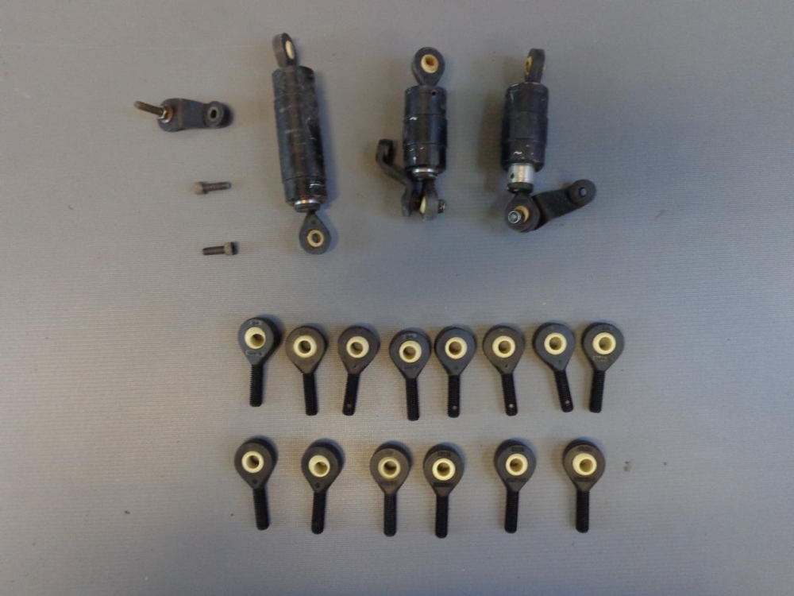
references/piston-parts02.jpg
