01binary/elysium-max-exoskeleton/references/piston-parts03.jpg

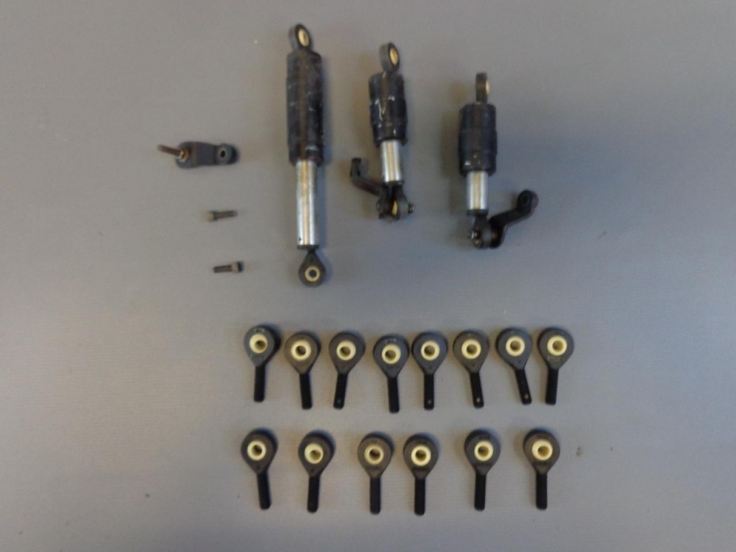
references/piston-parts03.jpg
