01binary/elysium-max-exoskeleton/references/piston-parts04.jpg

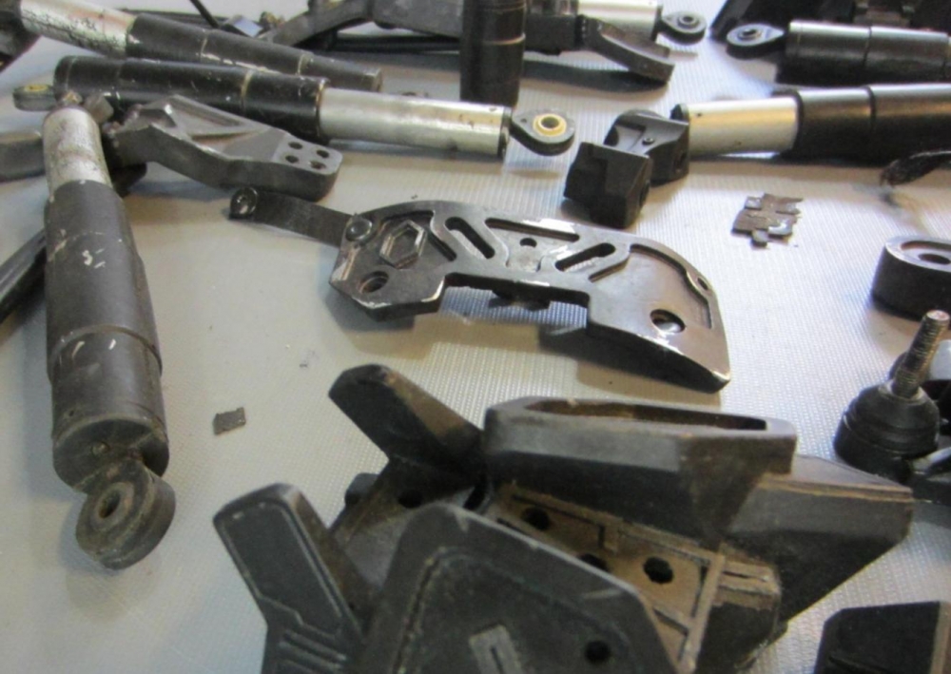
references/piston-parts04.jpg
