01binary/elysium-max-exoskeleton/print/ShinConnectorLeft.stl

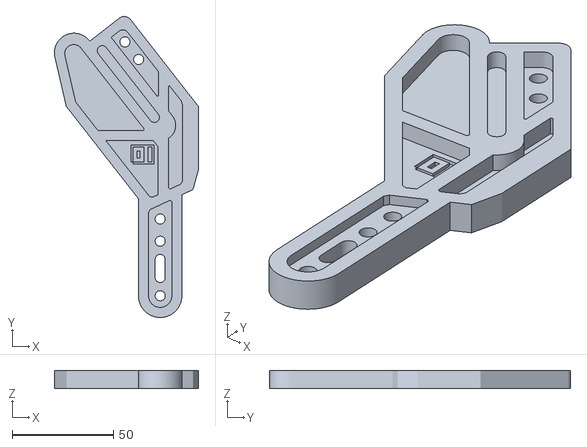
[picture p154: CAD file, 2016-10-02]
print/ShinConnectorLeft.stl
71.3 x 148.9 x 9.00
