01binary/elysium-max-exoskeleton/print/Pistons/PistonHipMiddleBody.stl

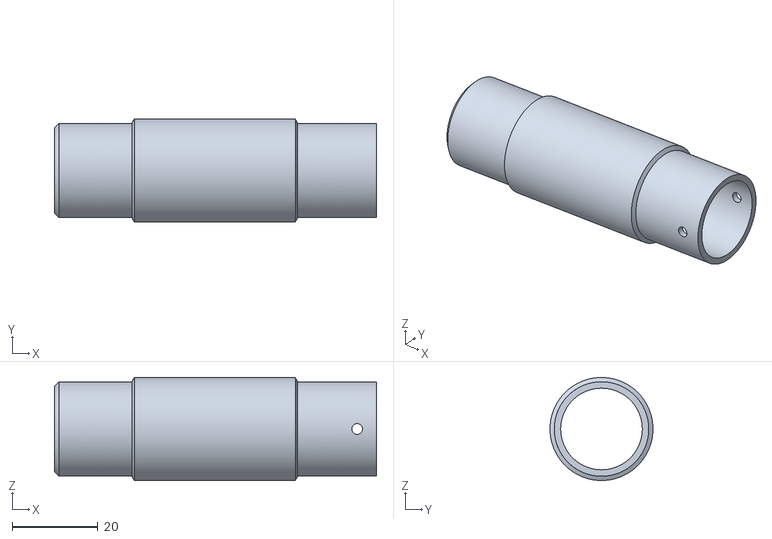
[picture p155: CAD file, 2016-10-01]
print/Pistons/PistonHipMiddleBody.stl
75.0 x 24.0 x 24.0
