01binary/elysium-max-exoskeleton/print/ShinLockLeft.stl

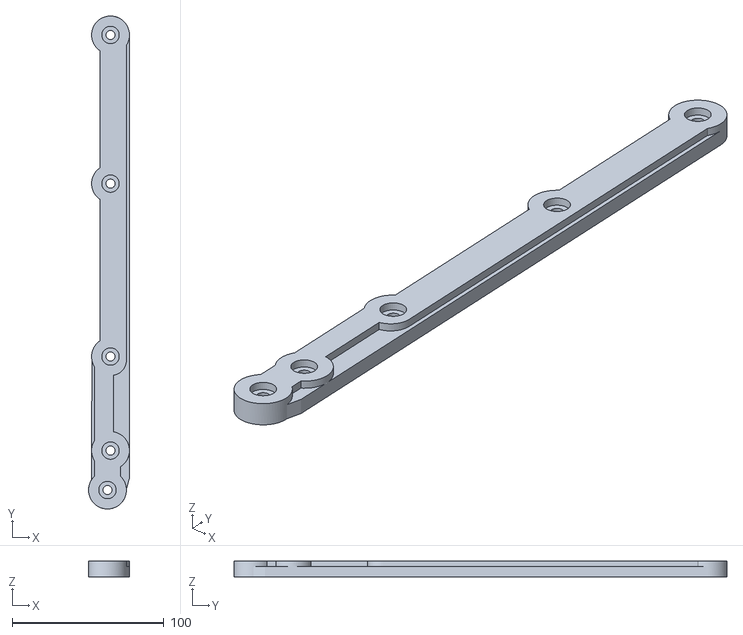
[picture p156: CAD file, 2016-10-02]
print/ShinLockLeft.stl
27.0 x 325.0 x 10.5
