01binary/elysium-max-exoskeleton/print/Pistons/PistonHipBackBody.stl

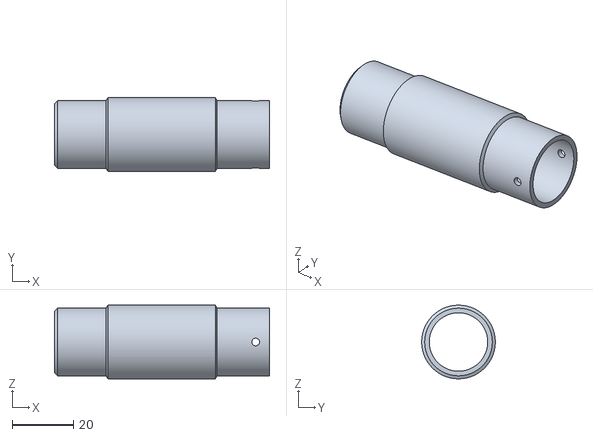
[picture p157: CAD file, 2016-10-01]
print/Pistons/PistonHipBackBody.stl
70.0 x 24.0 x 24.0
