01binary/elysium-max-exoskeleton/print/Pistons/PistonHipFrontBody.stl

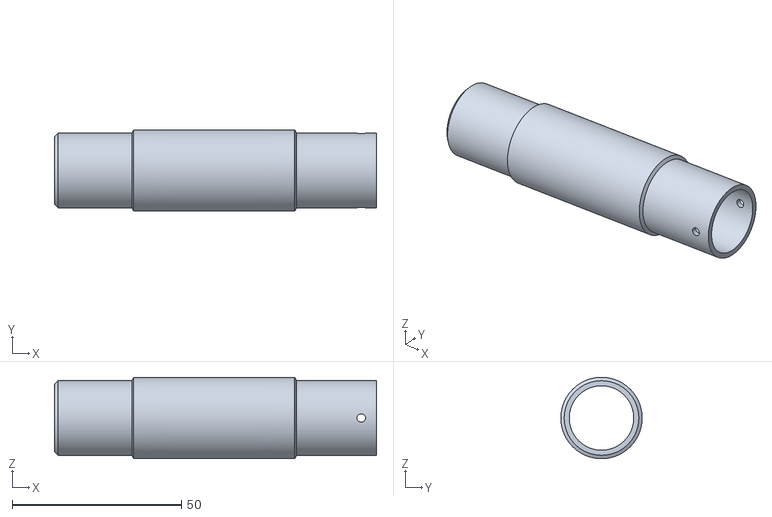
[picture p158: CAD file, 2016-10-01]
print/Pistons/PistonHipFrontBody.stl
95.0 x 24.0 x 24.0
