01binary/elysium-max-exoskeleton/print/Pistons/PistonBackMiddleBody.stl

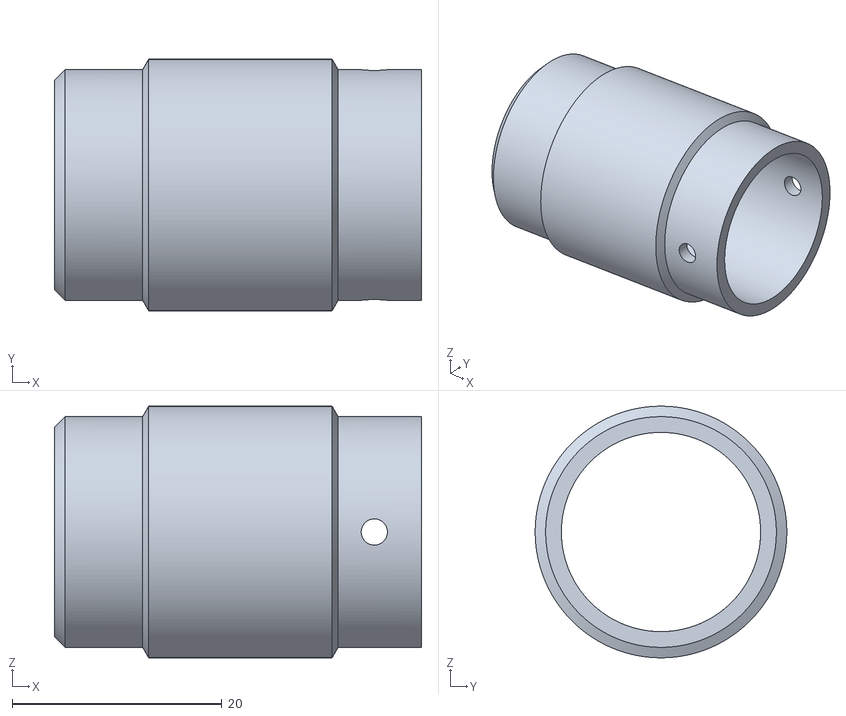
[picture p159: CAD file, 2016-10-01]
print/Pistons/PistonBackMiddleBody.stl
35.0 x 24.0 x 24.0
