01binary/elysium-max-exoskeleton/print/ShinRight.stl

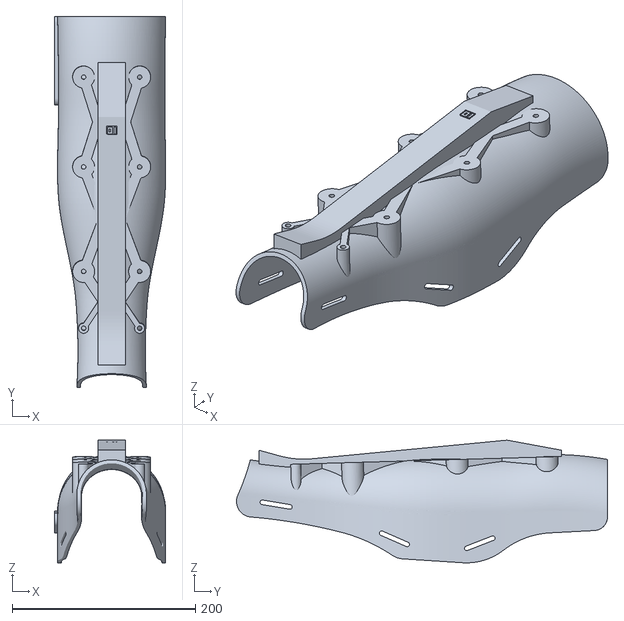
[picture p160: CAD file, 2016-10-02]
print/ShinRight.stl
121.5 x 404.5 x 133.8
