01binary/elysium-max-exoskeleton/print/Pistons/PistonClavicleBody.stl

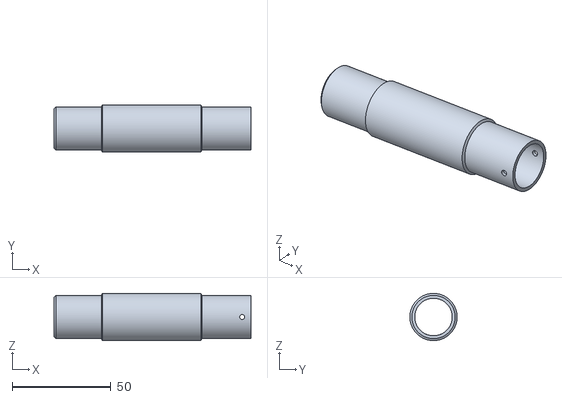
[picture p161: CAD file, 2016-10-01]
print/Pistons/PistonClavicleBody.stl
100.0 x 24.0 x 24.0
