01binary/elysium-max-exoskeleton/print/ShinShockPlateLeft.stl

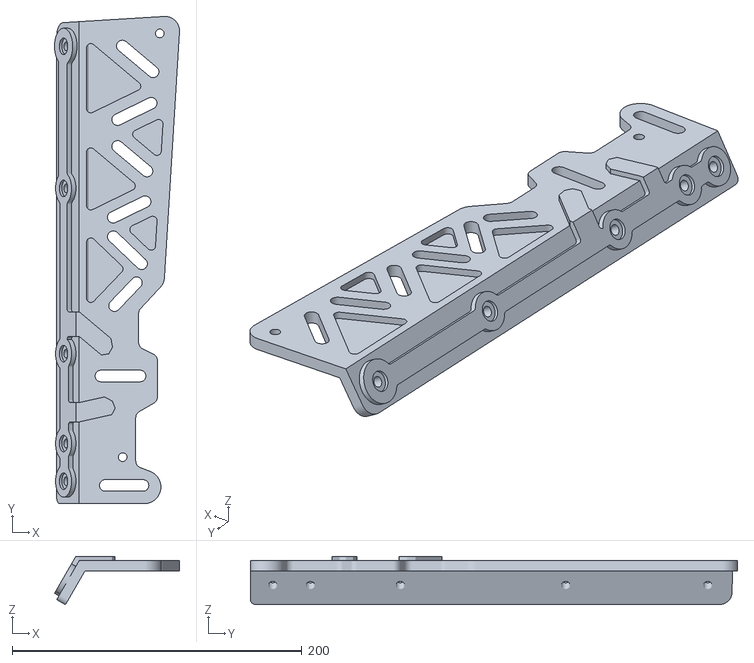
[picture p162: CAD file, 2016-10-02]
print/ShinShockPlateLeft.stl
86.2 x 336.0 x 33.4
