01binary/elysium-max-exoskeleton/print/Pistons/PistonHipFrontShaft.stl

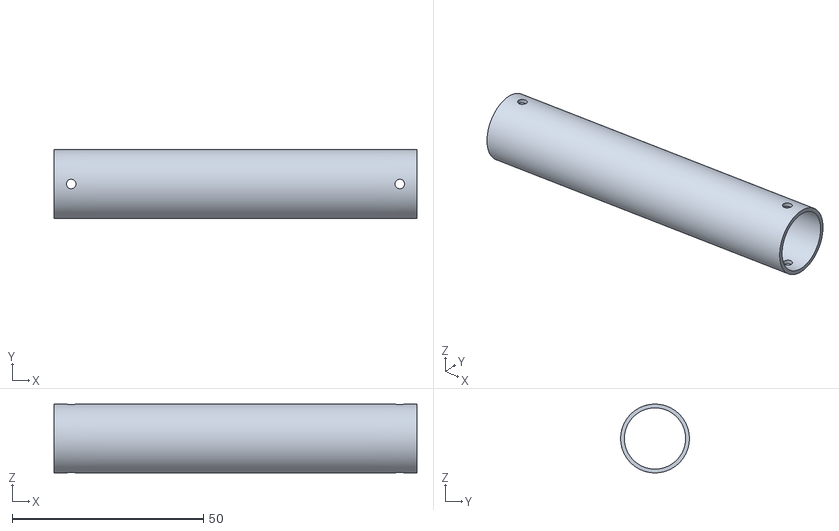
[picture p163: CAD file, 2016-10-01]
print/Pistons/PistonHipFrontShaft.stl
95.0 x 18.0 x 18.0
