01binary/elysium-max-exoskeleton/print/FootUpperShockPlate.stl

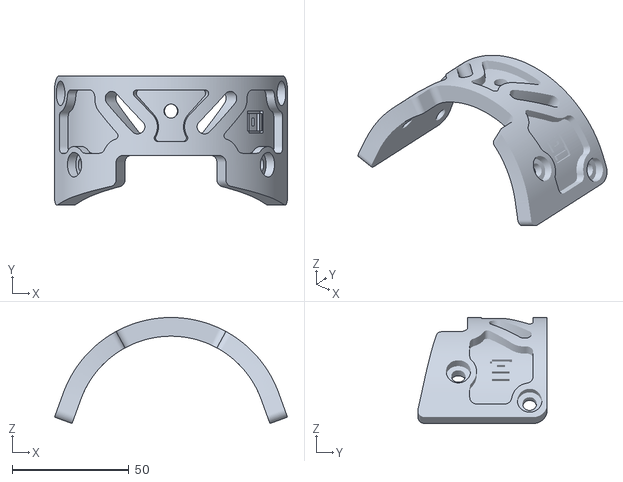
[picture p164: CAD file, 2016-10-02]
print/FootUpperShockPlate.stl
99.6 x 55.3 x 45.3
