01binary/elysium-max-exoskeleton/print/Pistons/PistonClavicleShaft.stl

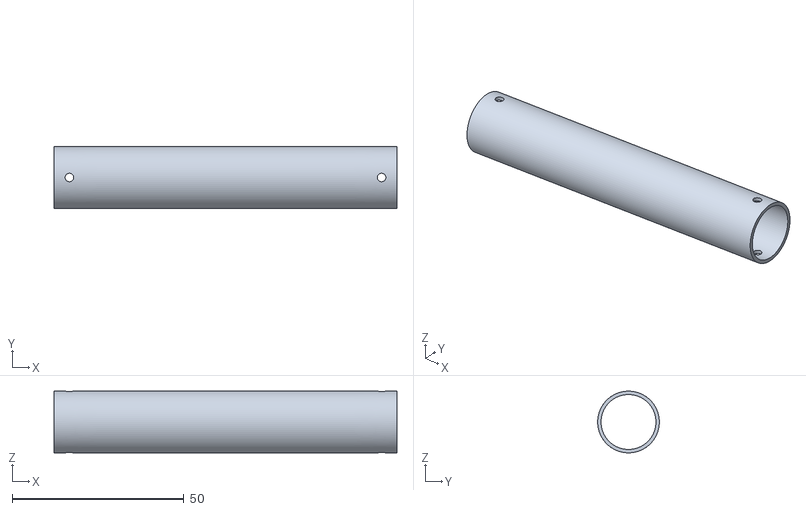
[picture p165: CAD file, 2016-10-01]
print/Pistons/PistonClavicleShaft.stl
100.0 x 18.0 x 18.0
