01binary/elysium-max-exoskeleton/print/FootShockPlate.stl

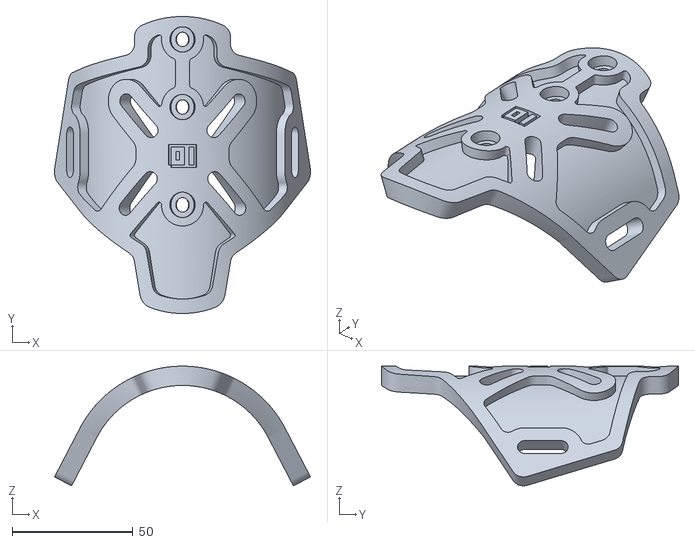
[picture p166: CAD file, 2016-10-02]
print/FootShockPlate.stl
106.0 x 123.0 x 49.6
