01binary/elysium-max-exoskeleton/print/Pistons/PistonShoulderFrontBody.stl

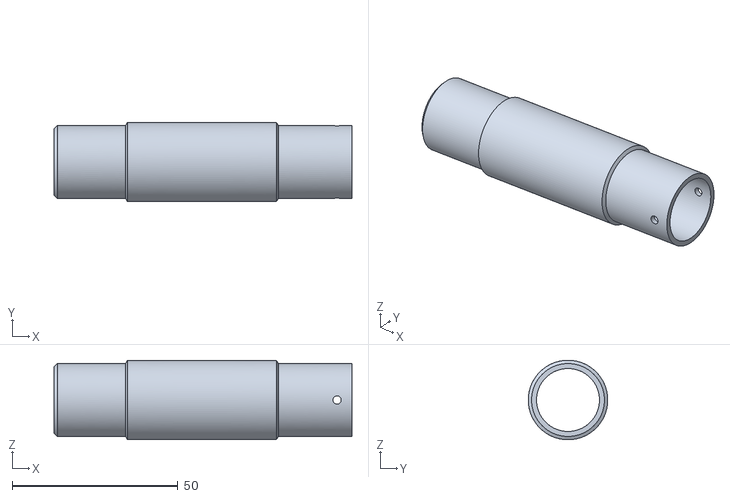
[picture p167: CAD file, 2016-10-01]
print/Pistons/PistonShoulderFrontBody.stl
90.0 x 24.0 x 24.0
