01binary/elysium-max-exoskeleton/print/Pistons/PistonShoulderFrontShaft.stl

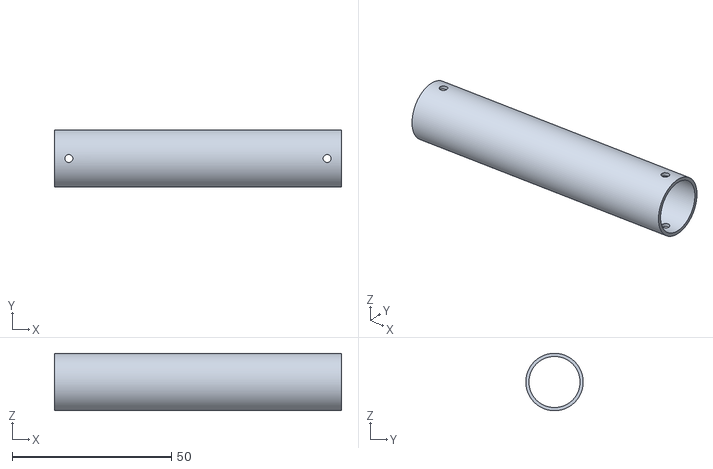
[picture p168: CAD file, 2016-10-01]
print/Pistons/PistonShoulderFrontShaft.stl
90.0 x 18.0 x 18.0
