01binary/elysium-max-exoskeleton/print/ShinExtender.stl

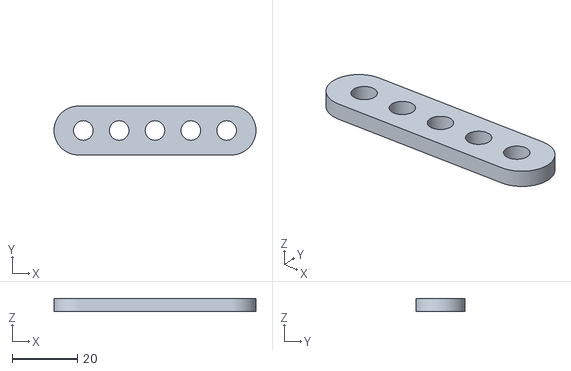
[picture p169: CAD file, 2016-10-01]
print/ShinExtender.stl
62.0 x 15.0 x 4.00
