01binary/elysium-max-exoskeleton/print/ForearmUpperShockPlateLeft.stl

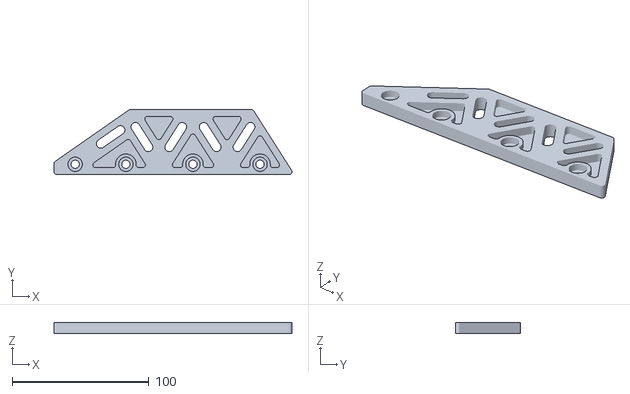
[picture p170: CAD file, 2016-10-01]
print/ForearmUpperShockPlateLeft.stl
173.9 x 47.5 x 8.00
