01binary/elysium-max-exoskeleton/print/Pistons/PistonBackTopBody.stl

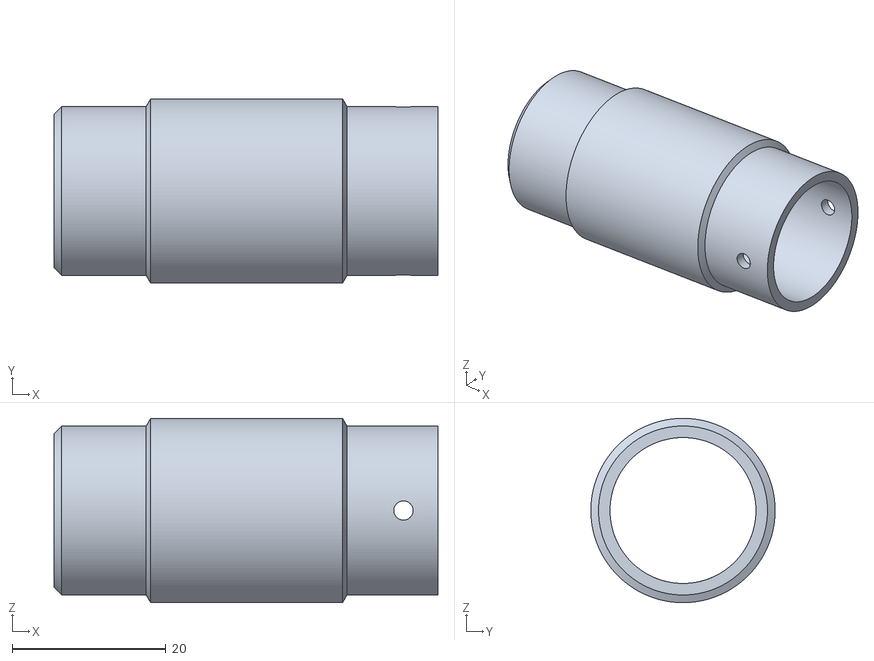
[picture p171: CAD file, 2016-10-01]
print/Pistons/PistonBackTopBody.stl
50.0 x 24.0 x 24.0
