01binary/elysium-max-exoskeleton/print/UpperArmTricepRight.stl

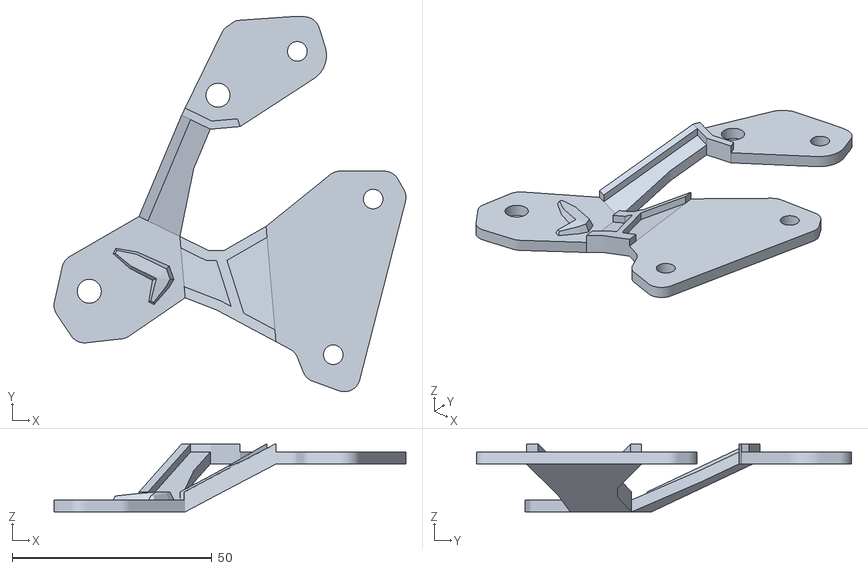
[picture p172: CAD file, 2016-10-01]
print/UpperArmTricepRight.stl
88.2 x 94.1 x 17.0
