01binary/elysium-max-exoskeleton/print/Pistons/PistonBackTopShaft.stl

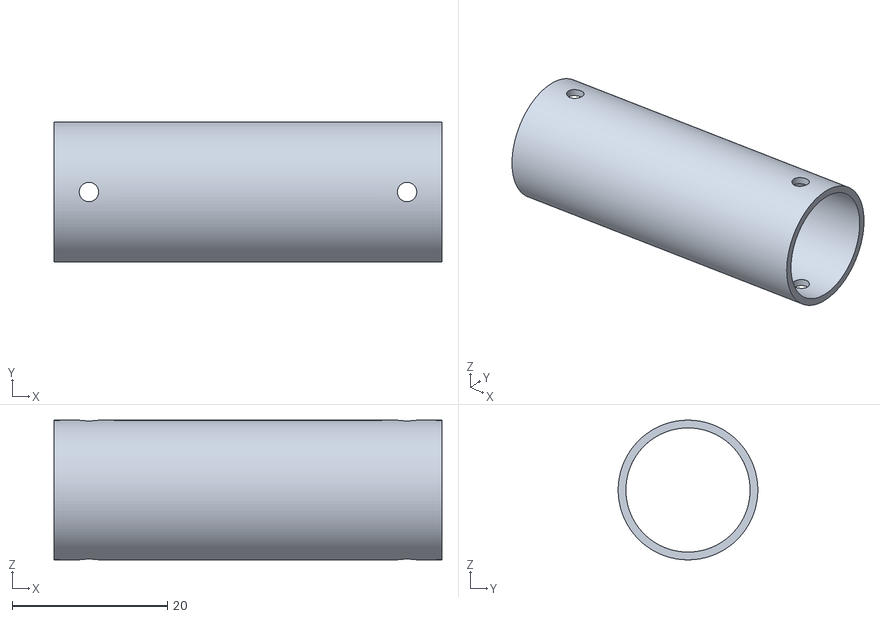
[picture p173: CAD file, 2016-10-01]
print/Pistons/PistonBackTopShaft.stl
50.0 x 18.0 x 18.0
