01binary/elysium-max-exoskeleton/print/ProxPhalangeMiddle.stl

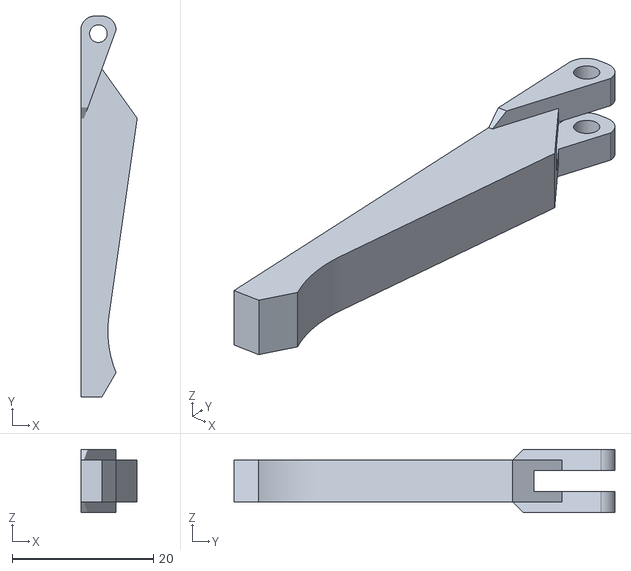
[picture p174: CAD file, 2016-10-01]
print/ProxPhalangeMiddle.stl
8.00 x 54.0 x 9.00
