01binary/elysium-max-exoskeleton/print/Pistons/PistonLegBody.stl

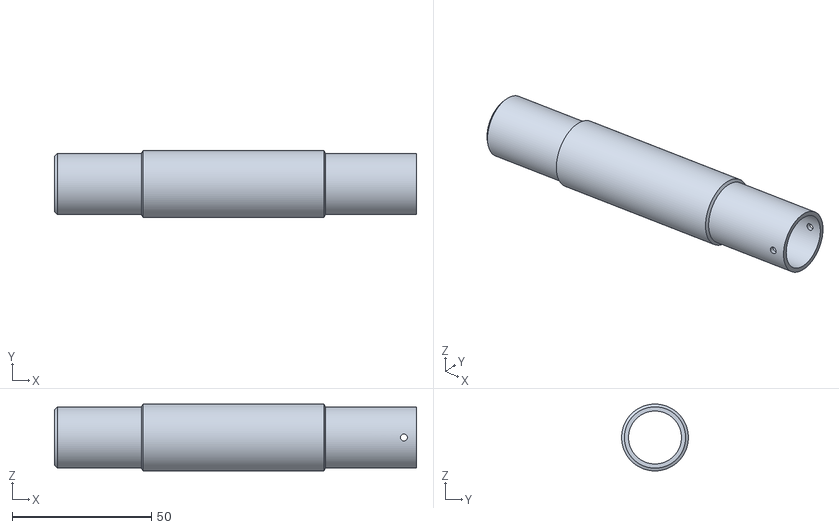
[picture p175: CAD file, 2016-10-01]
print/Pistons/PistonLegBody.stl
130.0 x 24.0 x 24.0
