01binary/elysium-max-exoskeleton/print/ShoulderLeft.stl

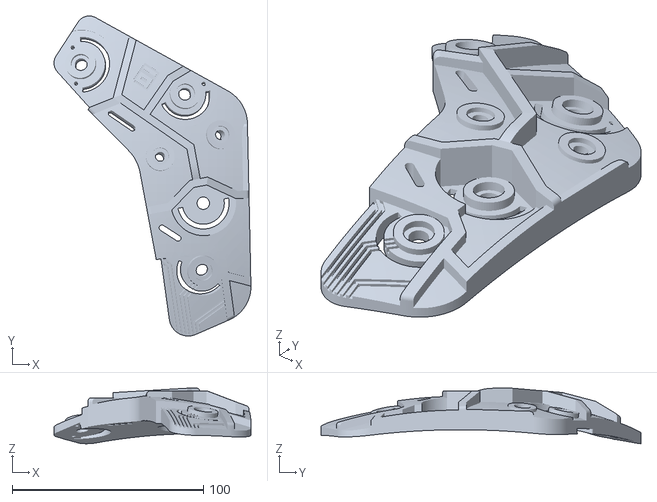
[picture p176: CAD file, 2016-10-01]
print/ShoulderLeft.stl
103.0 x 167.5 x 29.1
