01binary/elysium-max-exoskeleton/print/ElbowSubConnectorRight.stl

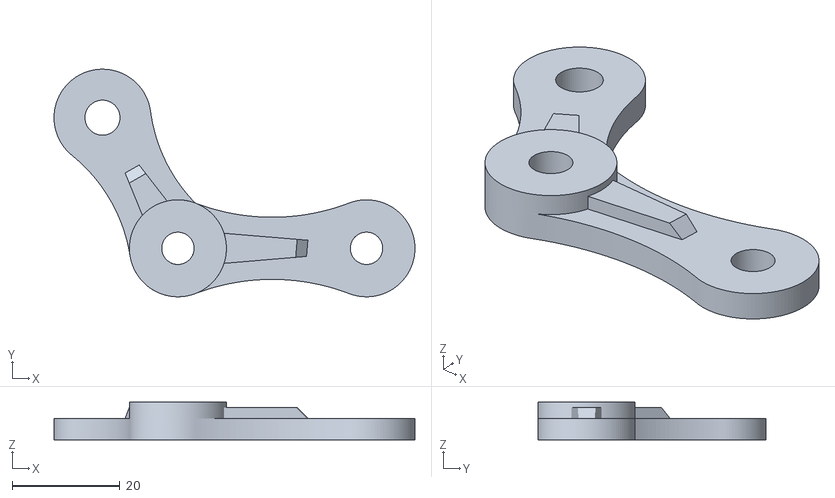
[picture p177: CAD file, 2016-10-01]
print/ElbowSubConnectorRight.stl
67.0 x 42.2 x 7.00
