01binary/elysium-max-exoskeleton/print/Pistons/PistonBodyCap.stl

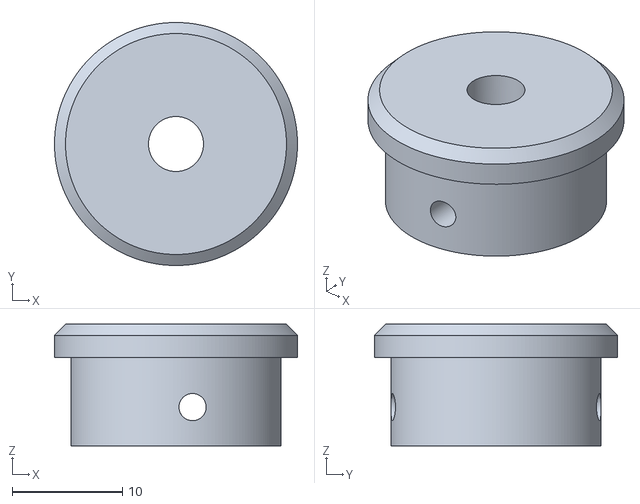
[picture p178: CAD file, 2016-10-01]
print/Pistons/PistonBodyCap.stl
22.0 x 22.0 x 11.0
