01binary/elysium-max-exoskeleton/print/SpineBottom.stl

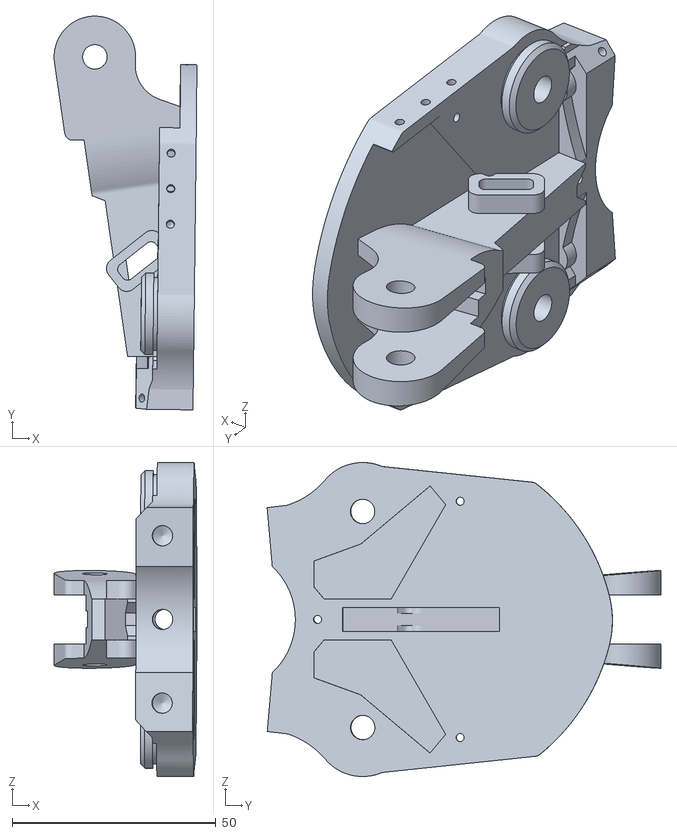
[picture p179: CAD file, 2016-10-01]
print/SpineBottom.stl
35.0 x 96.6 x 77.0
