01binary/elysium-max-exoskeleton/print/MetacarpusThumb.stl

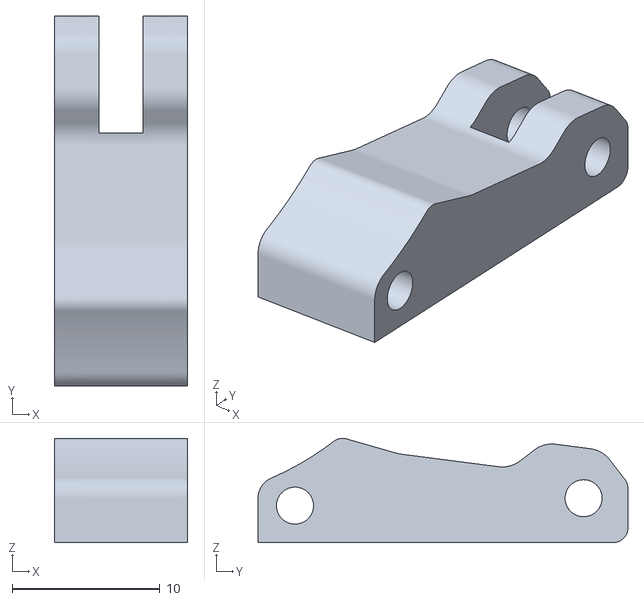
[picture p180: CAD file, 2016-10-01]
print/MetacarpusThumb.stl
9.00 x 25.0 x 7.04
