01binary/elysium-max-exoskeleton/print/Pistons/PistonHipBackShaft.stl

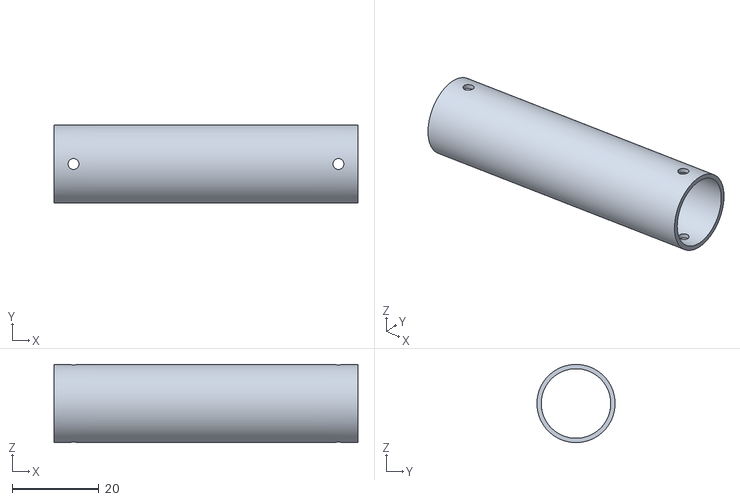
[picture p181: CAD file, 2016-10-01]
print/Pistons/PistonHipBackShaft.stl
70.0 x 18.0 x 18.0
