01binary/elysium-max-exoskeleton/print/ThumbMount.stl

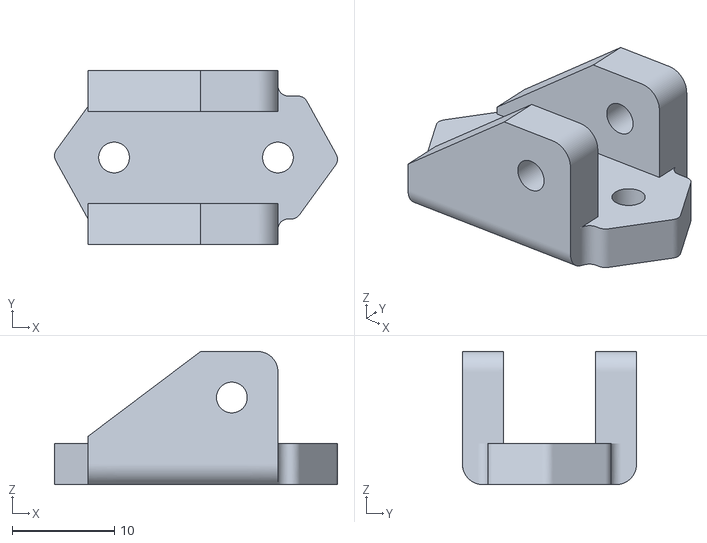
[picture p182: CAD file, 2016-10-01]
print/ThumbMount.stl
27.6 x 17.0 x 13.0
