01binary/elysium-max-exoskeleton/print/NeckLink.stl

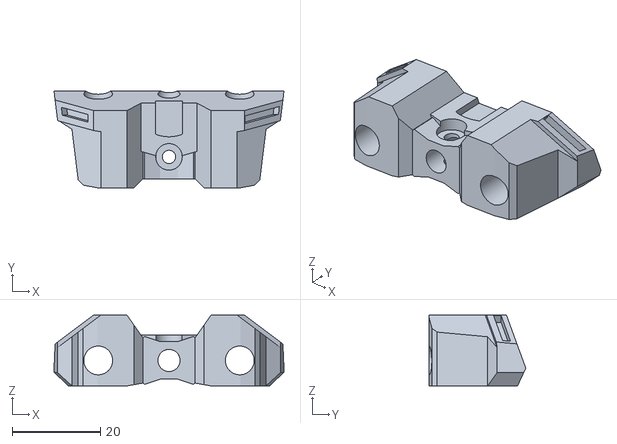
[picture p183: CAD file, 2016-10-01]
print/NeckLink.stl
52.0 x 21.9 x 16.0
