01binary/elysium-max-exoskeleton/print/ForearmClampHead.stl

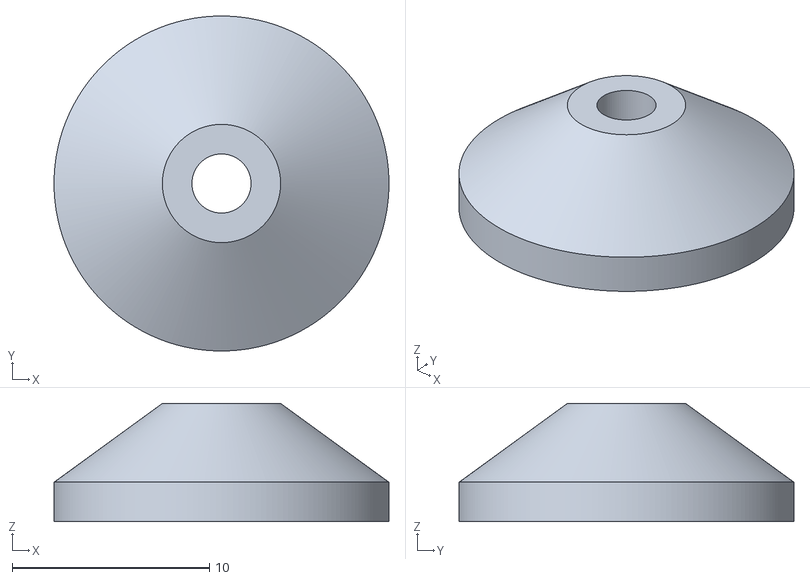
[picture p184: CAD file, 2016-10-01]
print/ForearmClampHead.stl
17.0 x 17.0 x 6.00
