01binary/elysium-max-exoskeleton/print/UpperArmConnectorLeft.stl

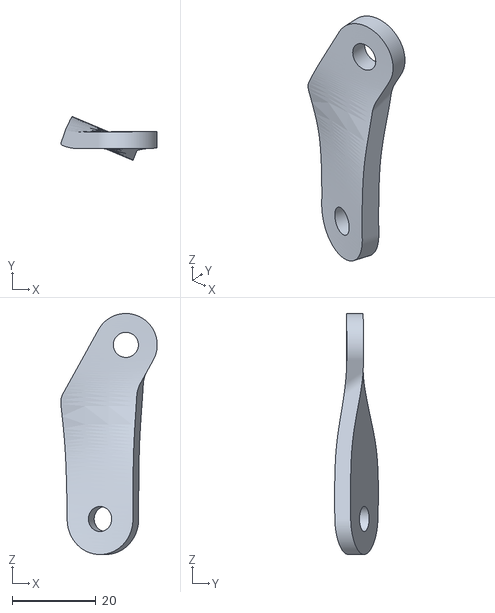
[picture p185: CAD file, 2016-10-01]
print/UpperArmConnectorLeft.stl
23.1 x 10.5 x 57.6
