01binary/elysium-max-exoskeleton/print/SpineTop.stl

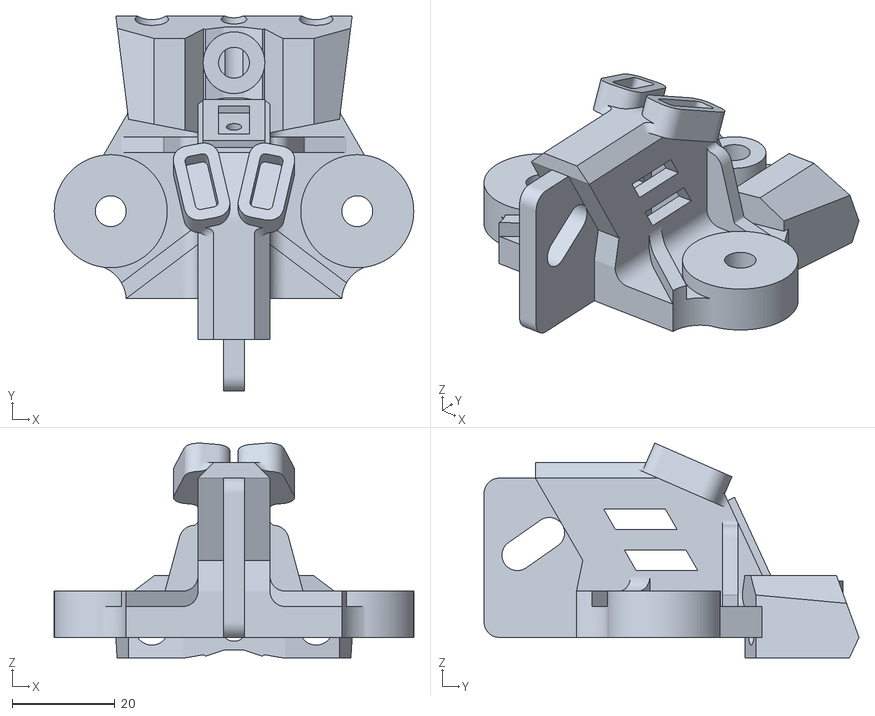
[picture p186: CAD file, 2016-10-01]
print/SpineTop.stl
70.0 x 73.0 x 41.8
