01binary/elysium-max-exoskeleton/print/UpperArmLeft.stl

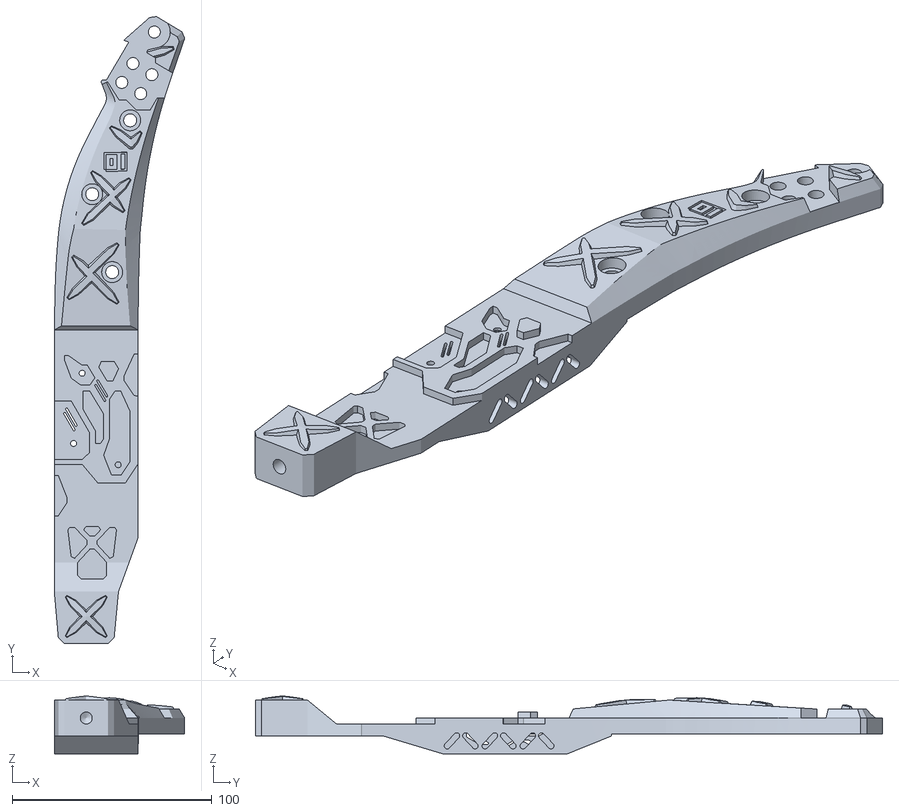
[picture p187: CAD file, 2016-10-01]
print/UpperArmLeft.stl
65.3 x 314.0 x 29.0
