01binary/elysium-max-exoskeleton/print/ProxPhalangeIndex.stl

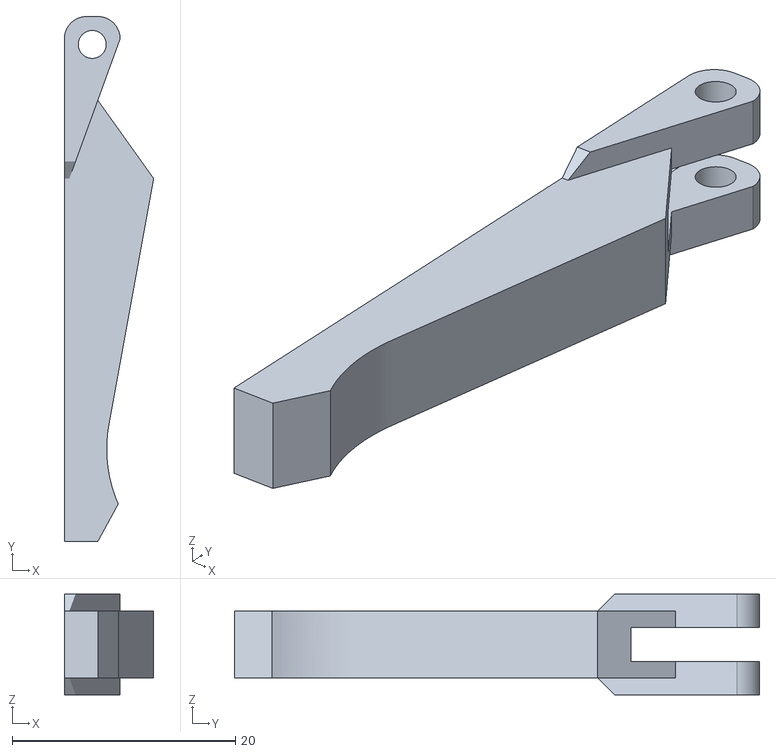
[picture p188: CAD file, 2016-10-01]
print/ProxPhalangeIndex.stl
8.00 x 47.0 x 9.00
