01binary/elysium-max-exoskeleton/print/PelvisBaseMount.stl

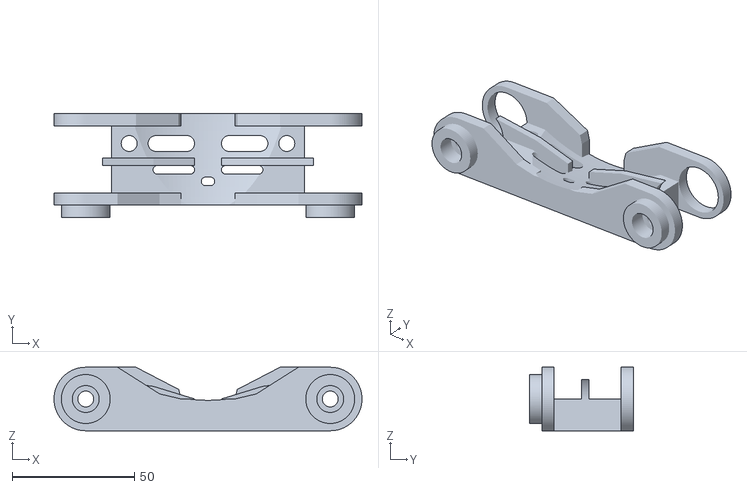
[picture p189: CAD file, 2016-10-01]
print/PelvisBaseMount.stl
126.0 x 42.5 x 26.0
