01binary/elysium-max-exoskeleton/print/UpperForearmShockPlateConnectorLeft.stl

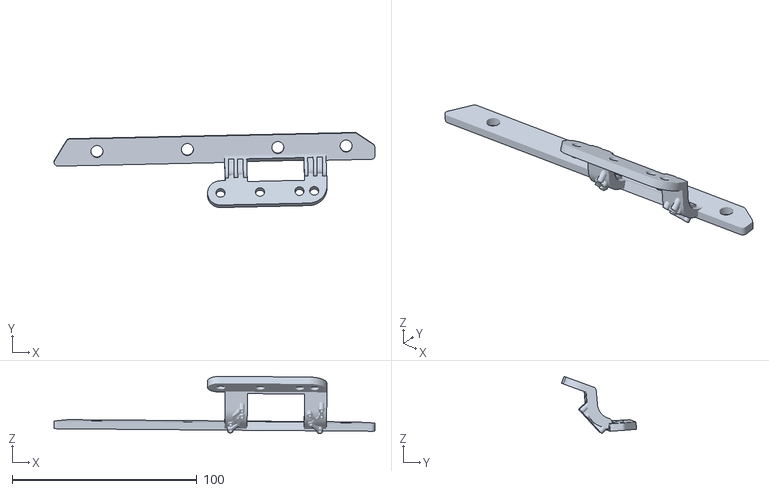
[picture p190: CAD file, 2016-10-01]
print/UpperForearmShockPlateConnectorLeft.stl
173.8 x 40.7 x 31.0
