01binary/elysium-max-exoskeleton/print/ForearmClamp.stl

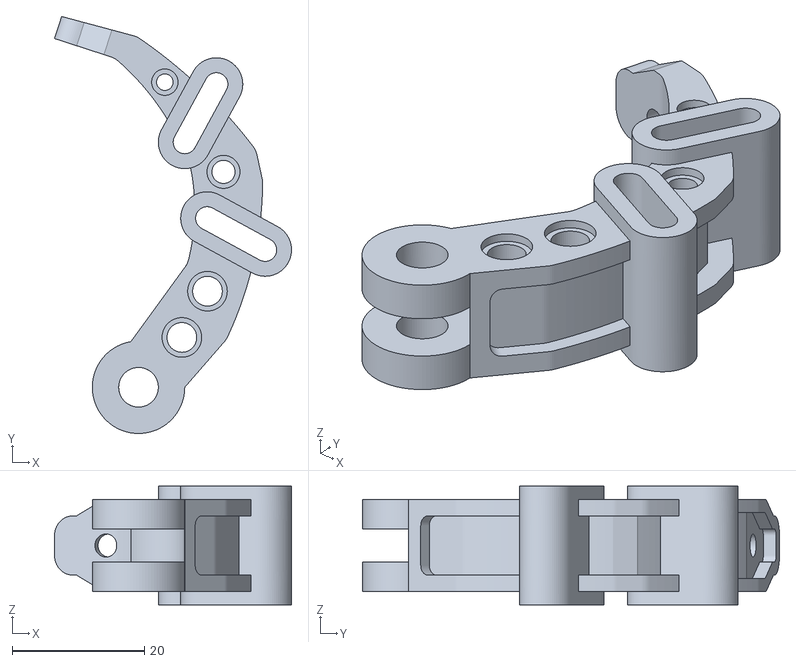
[picture p191: CAD file, 2016-10-01]
print/ForearmClamp.stl
35.9 x 63.1 x 18.0
