01binary/elysium-max-exoskeleton/print/HipTopConnectorLeft.stl

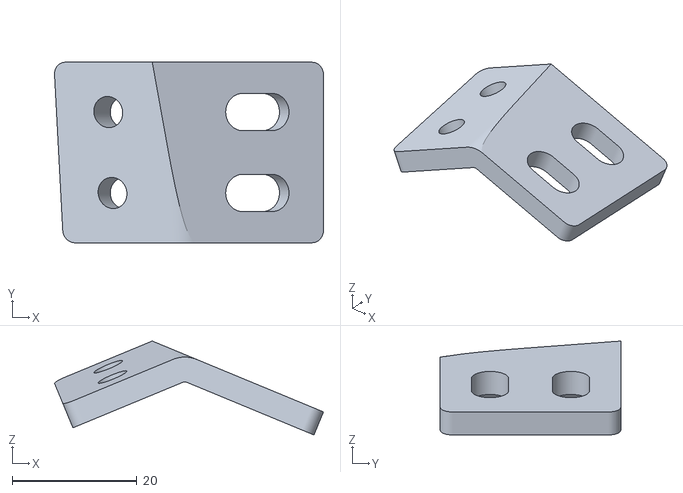
[picture p192: CAD file, 2016-10-01]
print/HipTopConnectorLeft.stl
43.2 x 29.0 x 15.1
