01binary/elysium-max-exoskeleton/print/DistPhalangeMiddle.stl

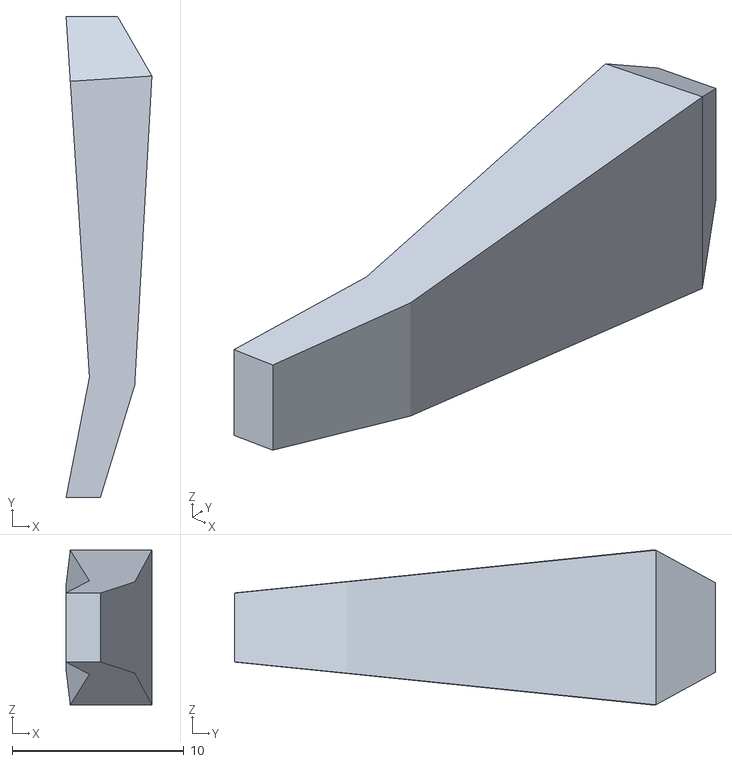
[picture p193: CAD file, 2016-10-01]
print/DistPhalangeMiddle.stl
5.00 x 28.0 x 9.00
