01binary/elysium-max-exoskeleton/print/MetacarpusMiddle.stl

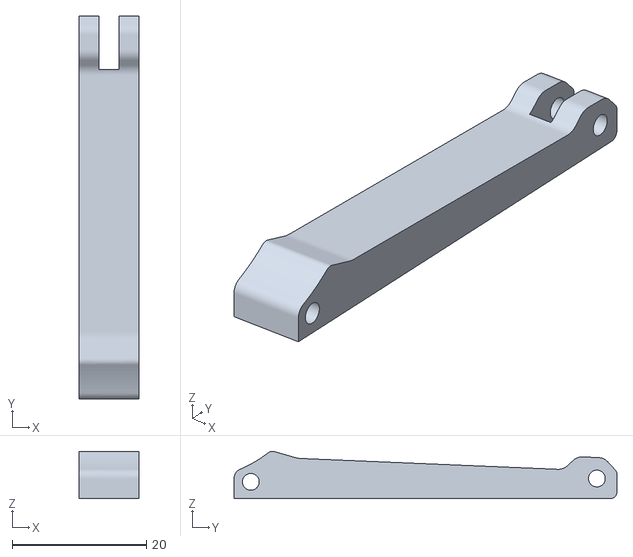
[picture p194: CAD file, 2016-10-01]
print/MetacarpusMiddle.stl
9.00 x 57.0 x 7.04
