01binary/elysium-max-exoskeleton/print/UpperArmShoulderRight.stl

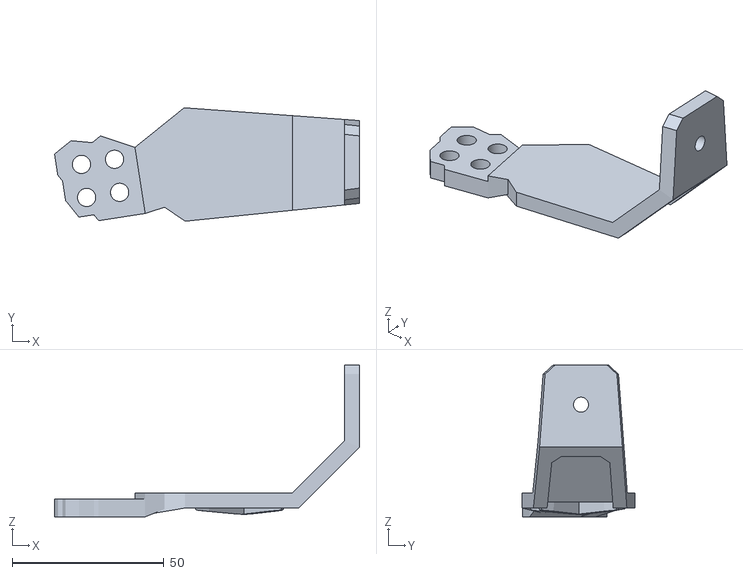
[picture p195: CAD file, 2016-10-01]
print/UpperArmShoulderRight.stl
100.4 x 37.3 x 49.9
