01binary/elysium-max-exoskeleton/print/ElbowConnectorLeft.stl

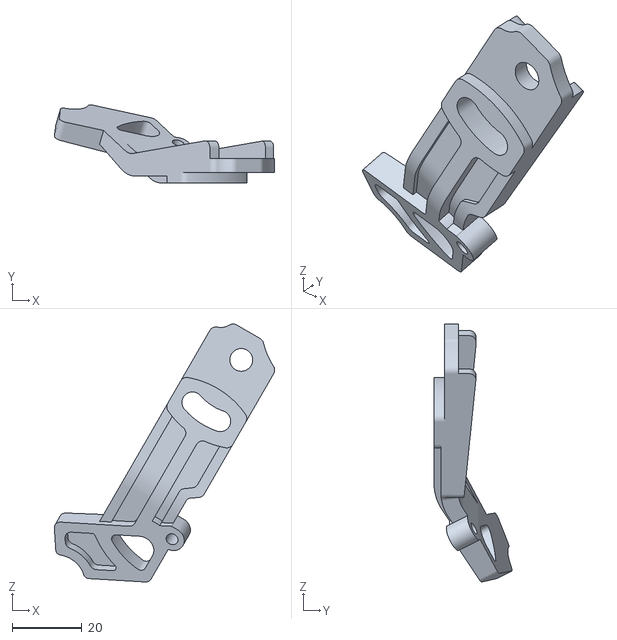
[picture p196: CAD file, 2016-10-01]
print/ElbowConnectorLeft.stl
63.0 x 22.3 x 73.8
