01binary/elysium-max-exoskeleton/print/ShoulderCogLarge.stl

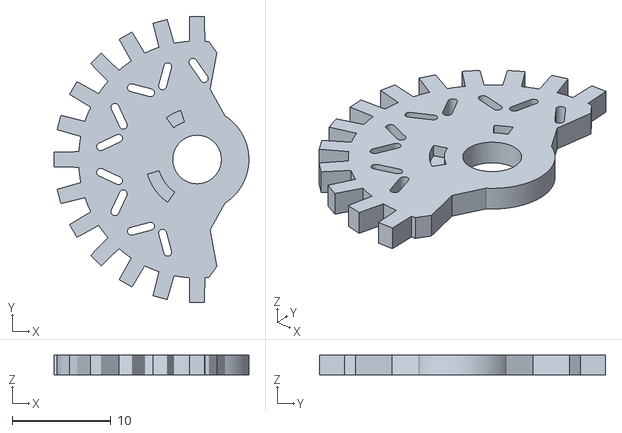
[picture p197: CAD file, 2016-10-01]
print/ShoulderCogLarge.stl
19.7 x 29.0 x 2.00
