01binary/elysium-max-exoskeleton/print/MetacarpusRing.stl

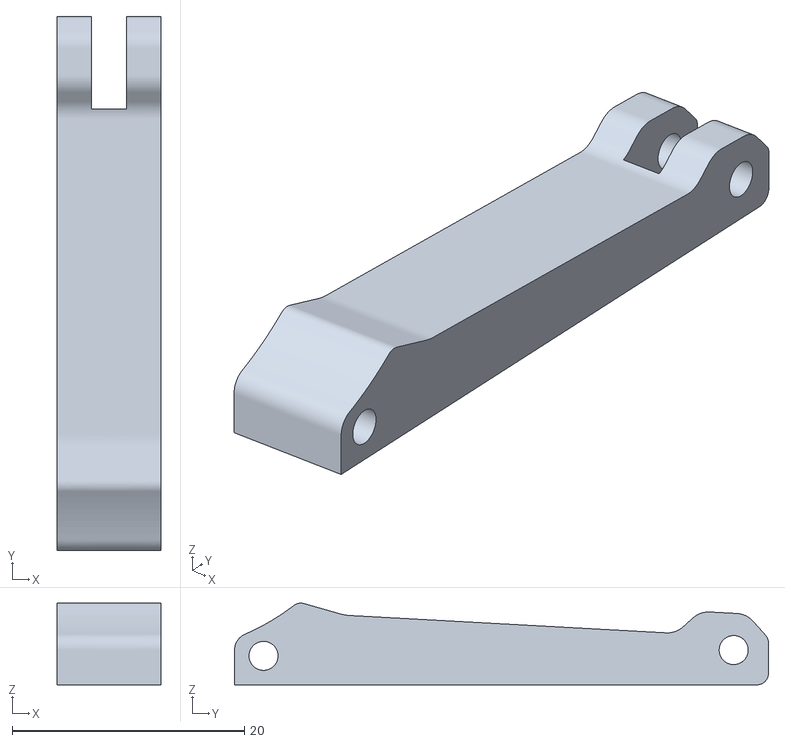
[picture p198: CAD file, 2016-10-01]
print/MetacarpusRing.stl
9.00 x 46.0 x 7.04
