01binary/elysium-max-exoskeleton/print/RingRouter.stl

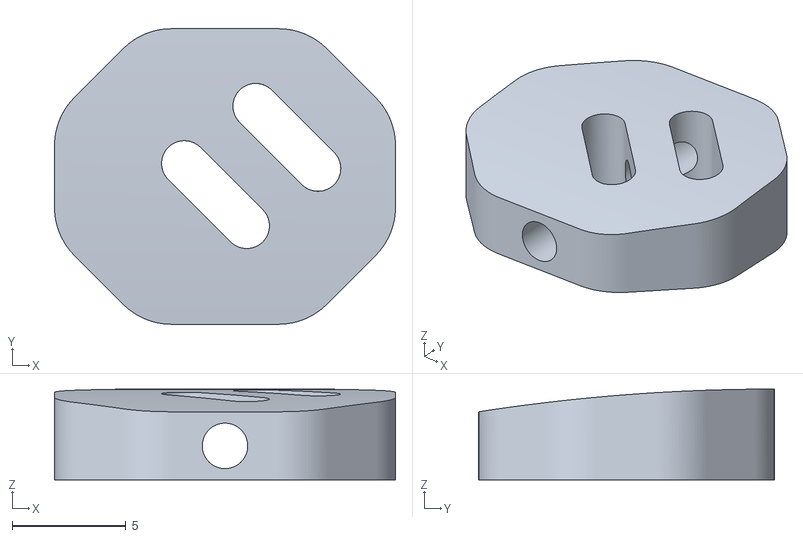
[picture p199: CAD file, 2016-10-01]
print/RingRouter.stl
15.0 x 13.0 x 4.00
