01binary/elysium-max-exoskeleton/print/SpineMiddleTop.stl

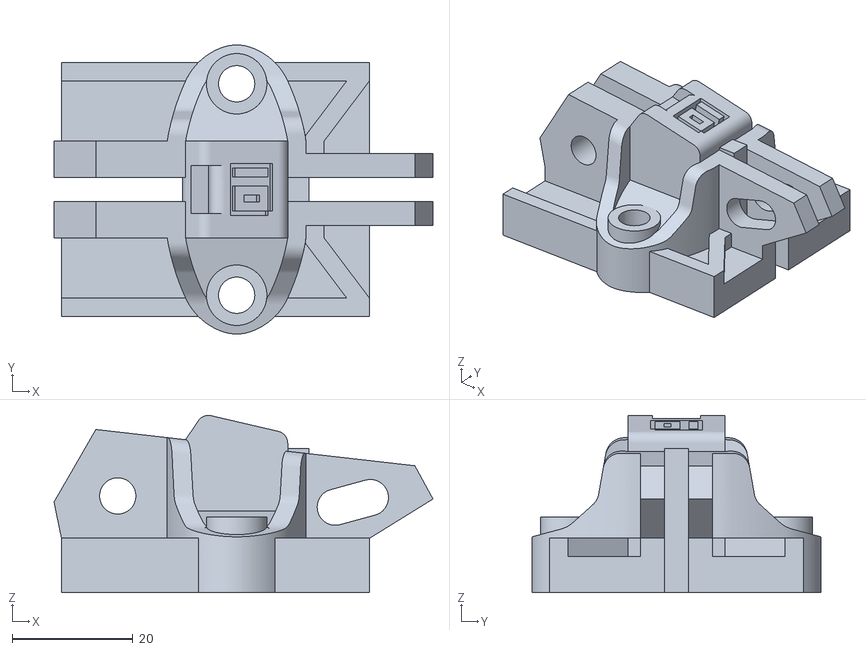
[picture p200: CAD file, 2016-10-01]
print/SpineMiddleTop.stl
62.7 x 47.9 x 29.3
