01binary/elysium-max-exoskeleton/print/DistPhalangeRing.stl

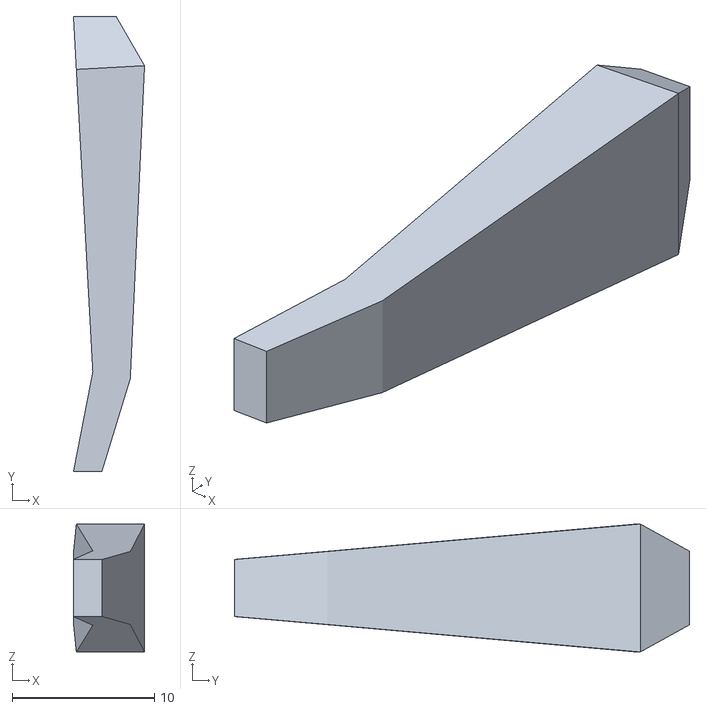
[picture p201: CAD file, 2016-10-01]
print/DistPhalangeRing.stl
5.00 x 32.0 x 9.00
