01binary/elysium-max-exoskeleton/print/ElbowConnectorUnderlinkLeft.stl

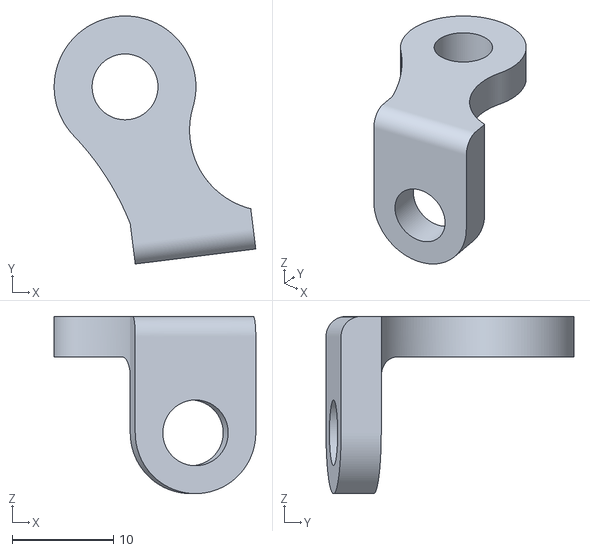
[picture p202: CAD file, 2016-10-01]
print/ElbowConnectorUnderlinkLeft.stl
19.9 x 24.5 x 17.5
