01binary/elysium-max-exoskeleton/print/ForearmCuffConnector.stl

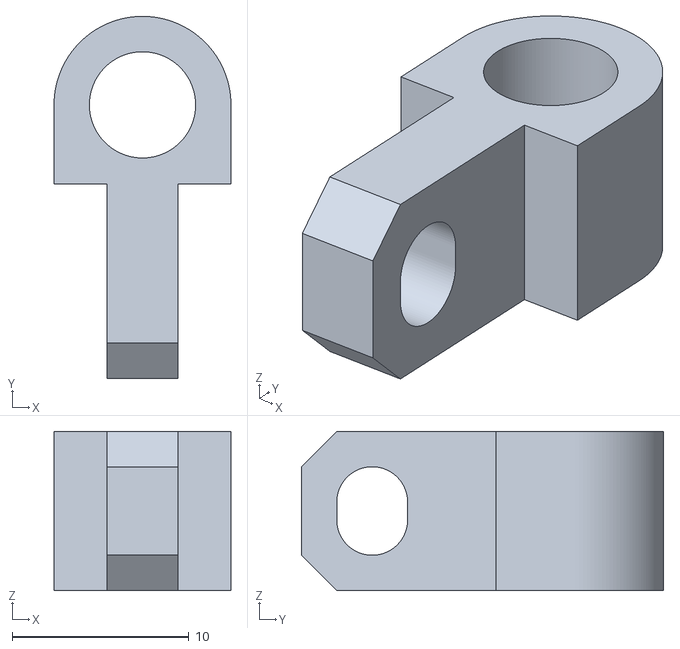
[picture p203: CAD file, 2016-10-01]
print/ForearmCuffConnector.stl
10.0 x 20.5 x 9.00
