01binary/elysium-max-exoskeleton/print/ForearmLowerShockPlateRight.stl

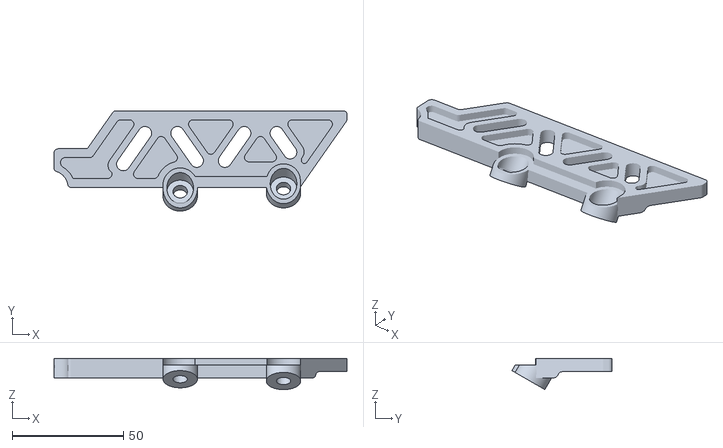
[picture p204: CAD file, 2016-10-01]
print/ForearmLowerShockPlateRight.stl
131.9 x 45.1 x 14.1
