01binary/elysium-max-exoskeleton/print/UpperForearmShockPlateConnectorRight.stl

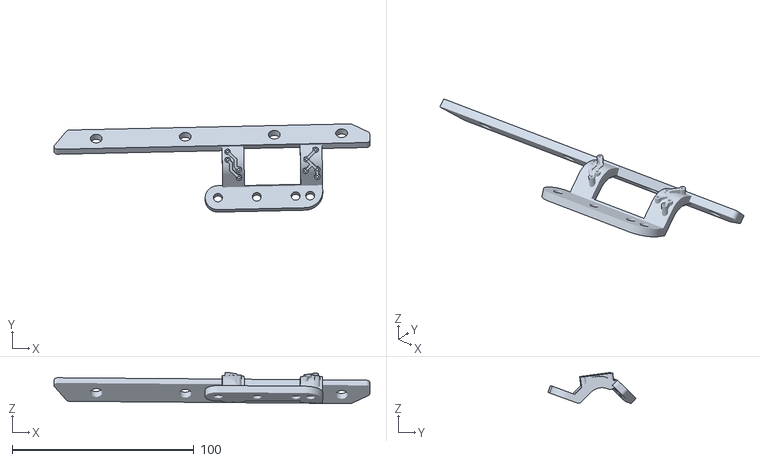
[picture p205: CAD file, 2016-10-01]
print/UpperForearmShockPlateConnectorRight.stl
173.8 x 48.5 x 17.1
