01binary/elysium-max-exoskeleton/print/IndexRouter.stl

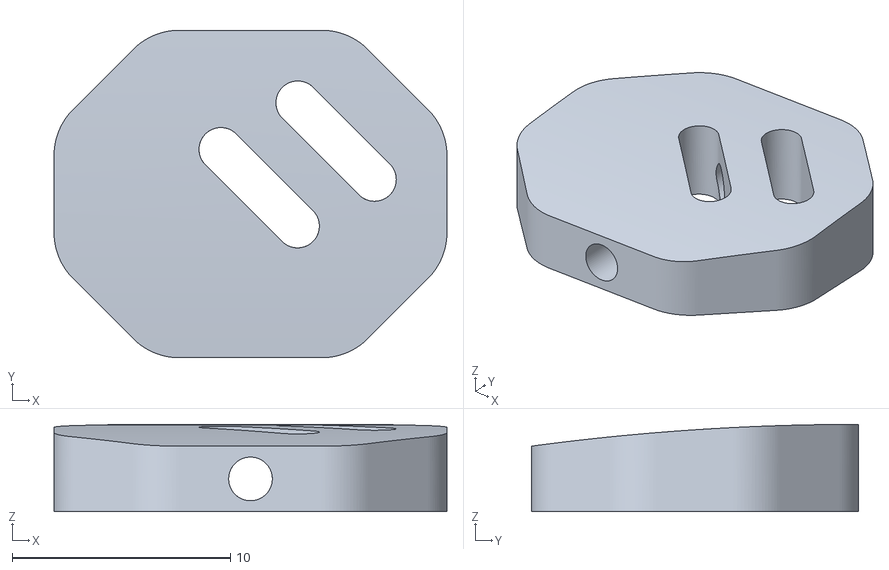
[picture p206: CAD file, 2016-10-01]
print/IndexRouter.stl
18.0 x 15.0 x 4.00
