01binary/elysium-max-exoskeleton/print/ForearmLowerShockplateLeft.stl

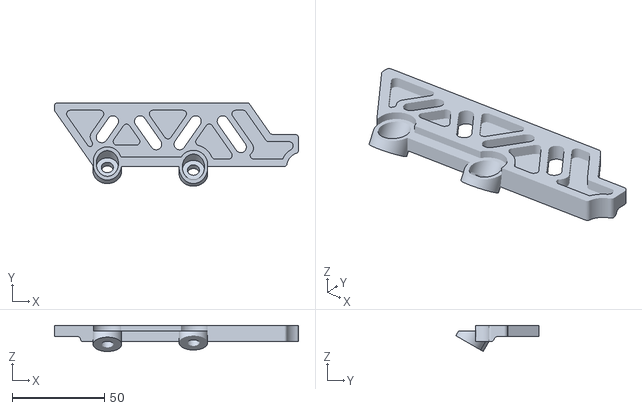
[picture p207: CAD file, 2016-10-01]
print/ForearmLowerShockplateLeft.stl
131.9 x 45.1 x 14.1
