01binary/elysium-max-exoskeleton/print/SpineNeckLinkConnector.stl

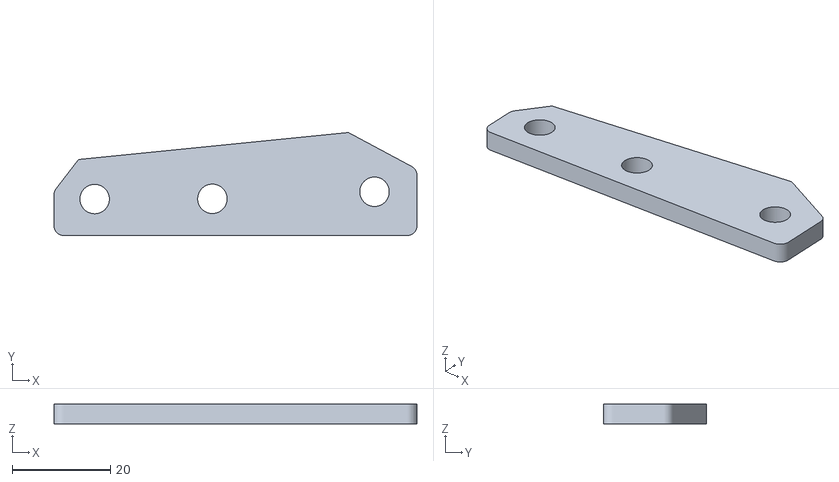
[picture p208: CAD file, 2016-10-01]
print/SpineNeckLinkConnector.stl
74.0 x 21.0 x 4.00
