01binary/elysium-max-exoskeleton/print/SpineLink.stl

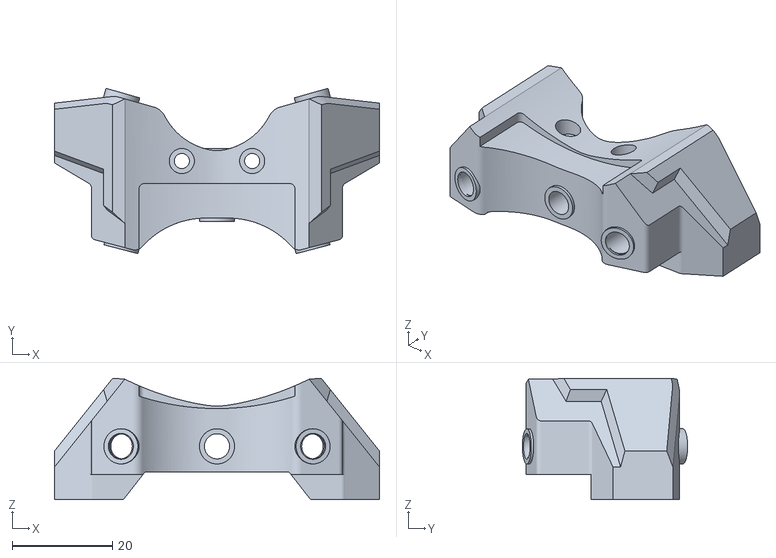
[picture p209: CAD file, 2016-10-01]
print/SpineLink.stl
64.7 x 32.9 x 24.2
