01binary/elysium-max-exoskeleton/print/SpacerLong.stl

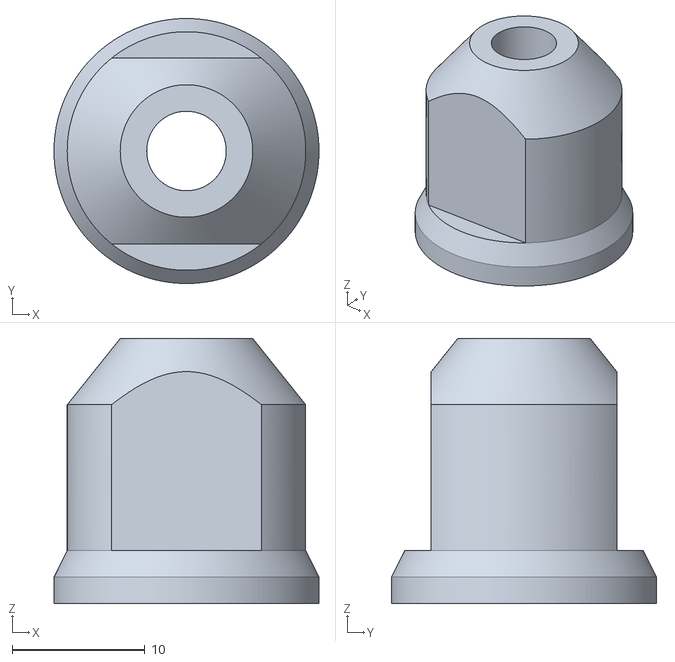
[picture p210: CAD file, 2016-10-01]
print/SpacerLong.stl
20.0 x 20.0 x 20.0
