01binary/elysium-max-exoskeleton/print/ThumbShockPlateLeft.stl

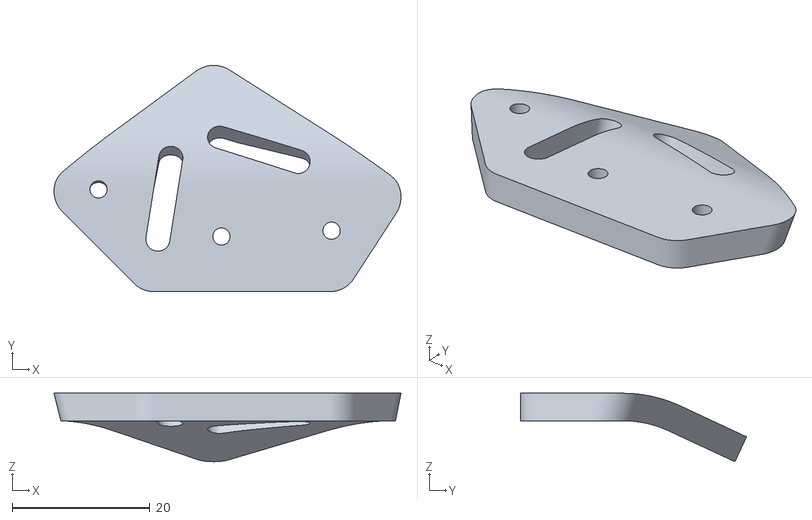
[picture p211: CAD file, 2016-10-01]
print/ThumbShockPlateLeft.stl
50.4 x 32.9 x 9.96
