01binary/elysium-max-exoskeleton/print/ForearmClampLink.stl

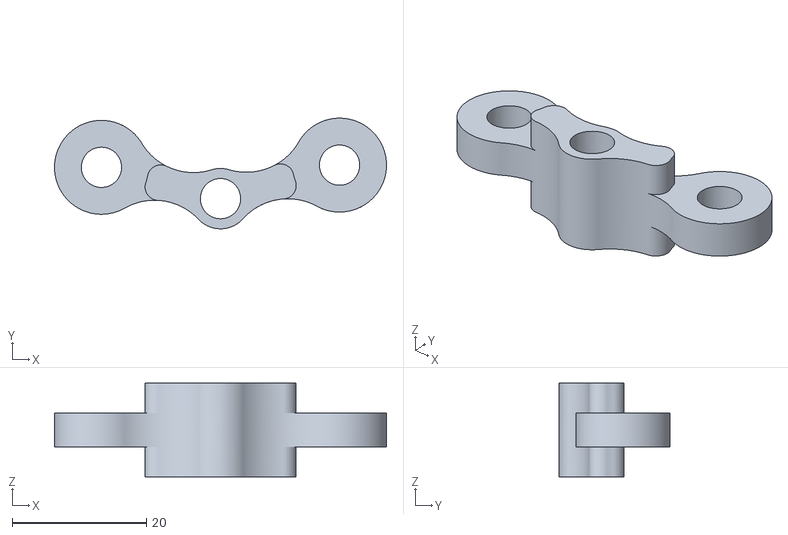
[picture p212: CAD file, 2016-10-01]
print/ForearmClampLink.stl
49.5 x 16.5 x 14.0
