01binary/elysium-max-exoskeleton/print/PelvisWingLeft.stl

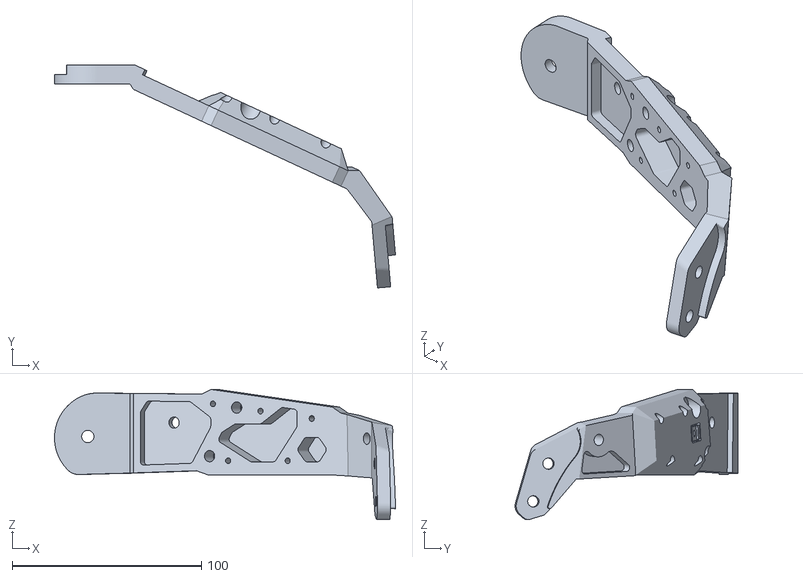
[picture p213: CAD file, 2016-10-01]
print/PelvisWingLeft.stl
180.1 x 117.7 x 68.7
