01binary/elysium-max-exoskeleton/print/ElbowConnectorLinkLeft.stl

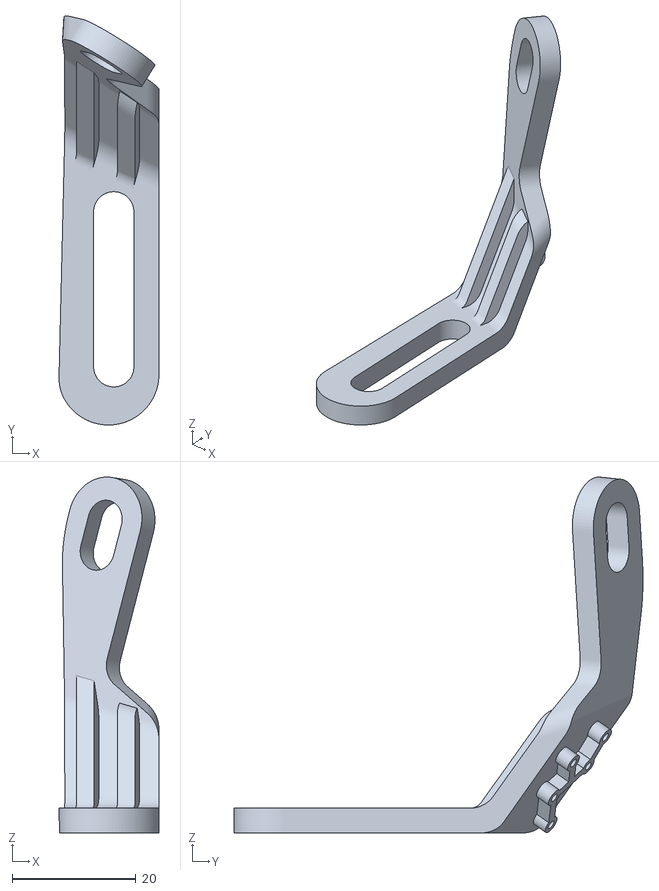
[picture p214: CAD file, 2016-10-01]
print/ElbowConnectorLinkLeft.stl
16.1 x 66.0 x 57.4
