01binary/elysium-max-exoskeleton/print/HipBottomConnectorLeft.stl

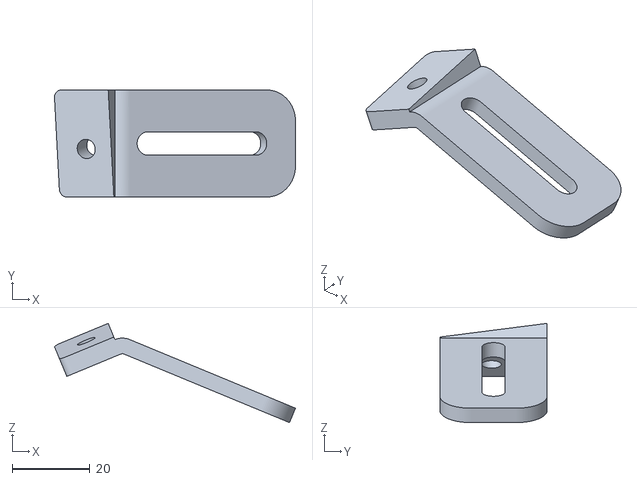
[picture p215: CAD file, 2016-10-01]
print/HipBottomConnectorLeft.stl
61.9 x 27.5 x 25.5
