01binary/elysium-max-exoskeleton/print/SpineBase.stl

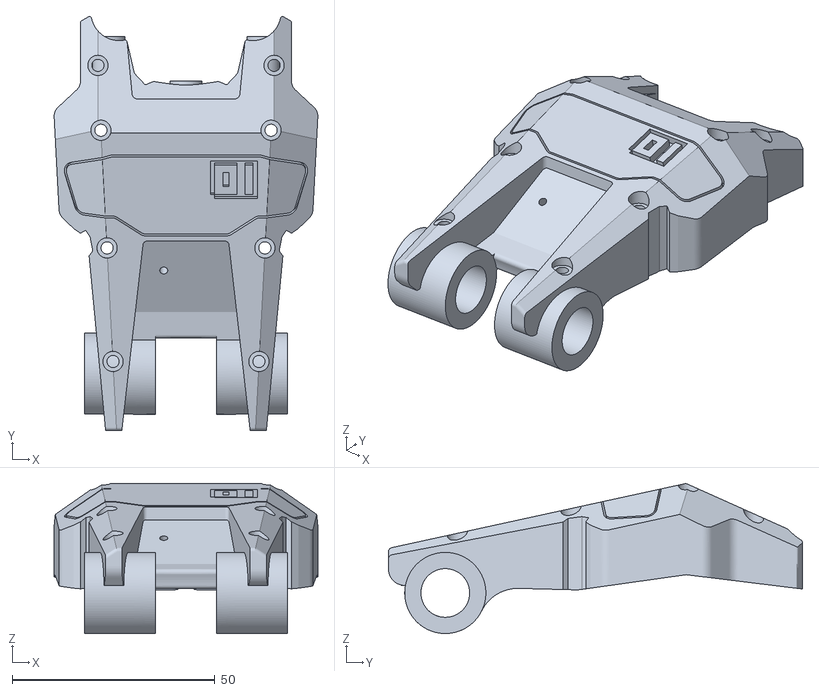
[picture p216: CAD file, 2016-10-01]
print/SpineBase.stl
65.0 x 102.1 x 37.0
