01binary/elysium-max-exoskeleton/print/DistPhalangeThumb.stl

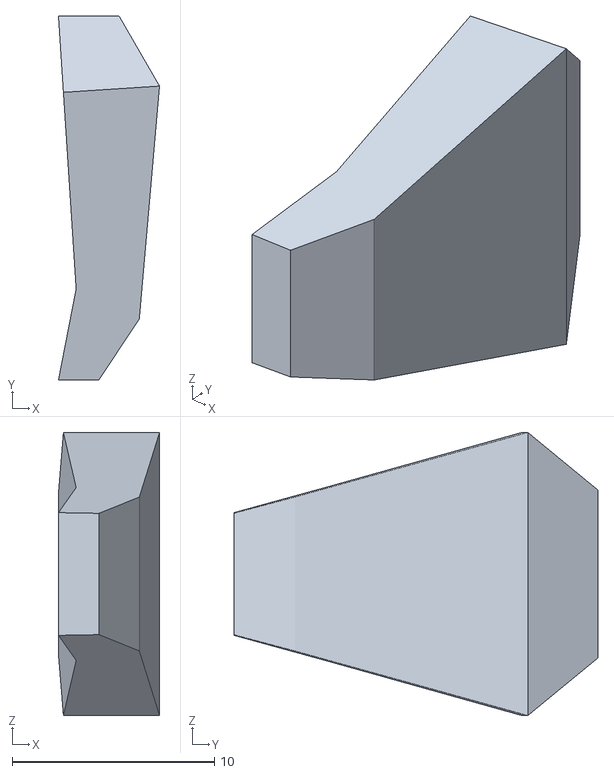
[picture p217: CAD file, 2016-10-01]
print/DistPhalangeThumb.stl
5.00 x 18.0 x 14.0
