01binary/elysium-max-exoskeleton/print/HipTopConnectorRight.stl

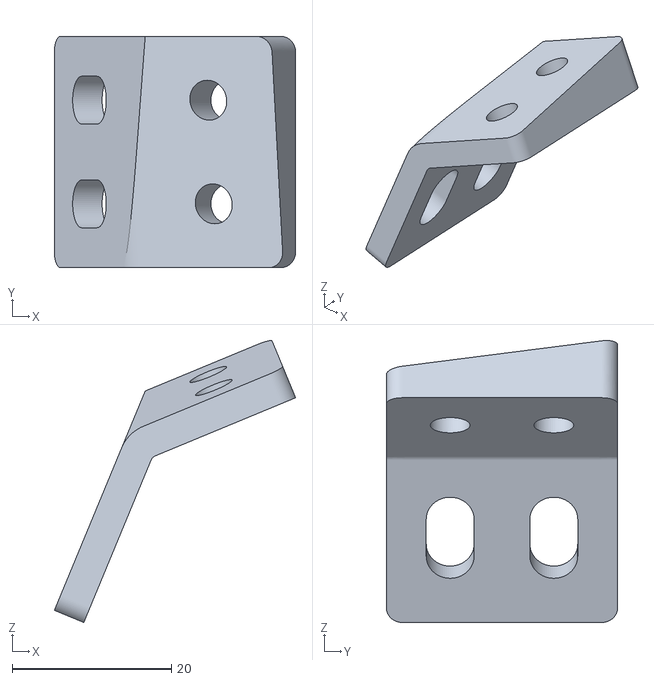
[picture p218: CAD file, 2016-10-01]
print/HipTopConnectorRight.stl
30.3 x 29.0 x 35.4
