01binary/elysium-max-exoskeleton/print/SpineMiddleLeft.stl

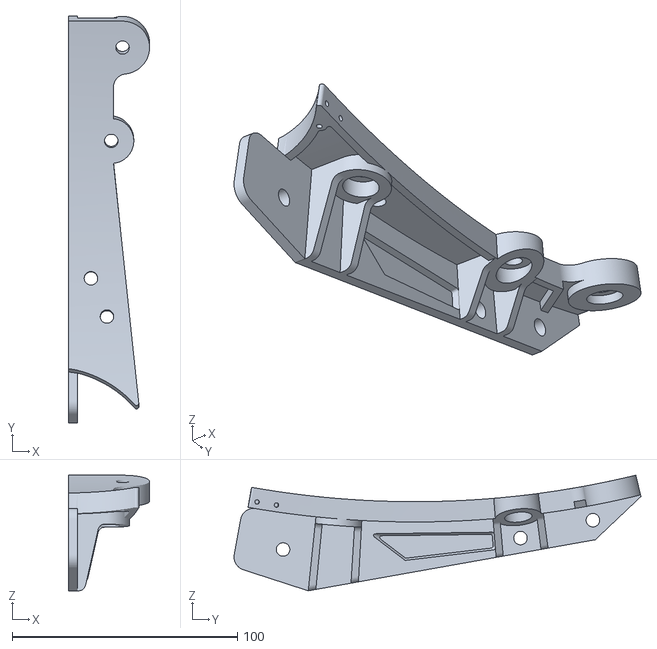
[picture p219: CAD file, 2016-10-01]
print/SpineMiddleLeft.stl
36.0 x 180.6 x 51.3
