01binary/elysium-max-exoskeleton/print/ChestPlateLeft.stl

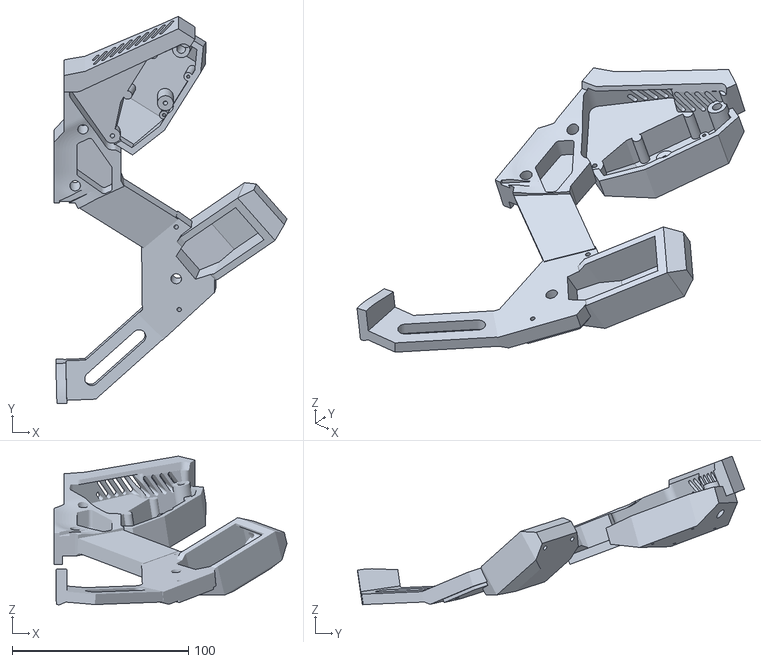
[picture p220: CAD file, 2016-10-01]
print/ChestPlateLeft.stl
132.1 x 219.6 x 84.4
