01binary/elysium-max-exoskeleton/print/ForearmBase.stl

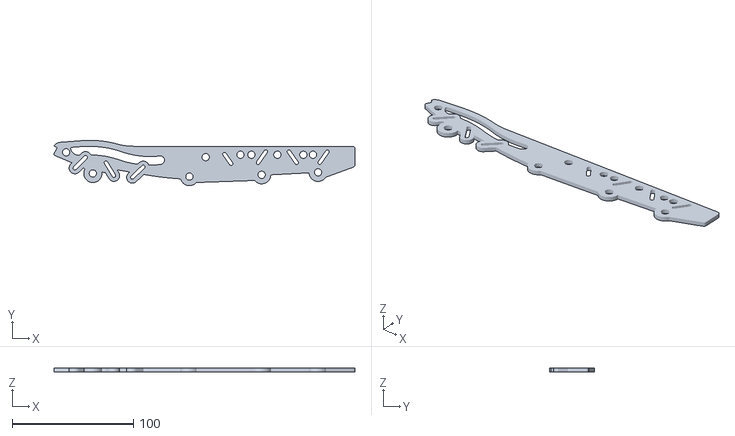
[picture p221: CAD file, 2016-10-01]
print/ForearmBase.stl
247.9 x 37.3 x 3.00
