01binary/elysium-max-exoskeleton/print/MiddleRouter.stl

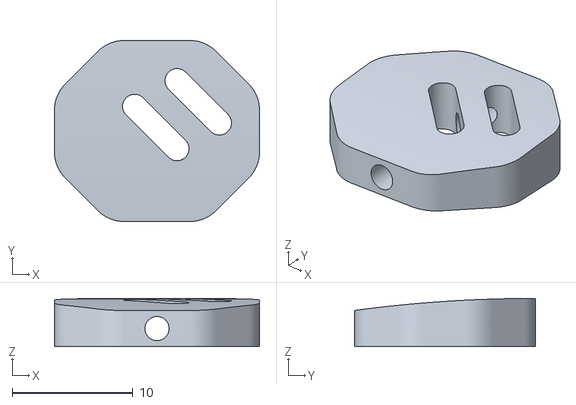
[picture p222: CAD file, 2016-10-01]
print/MiddleRouter.stl
17.0 x 15.0 x 4.00
