01binary/elysium-max-exoskeleton/print/DistPhalangeIndex.stl

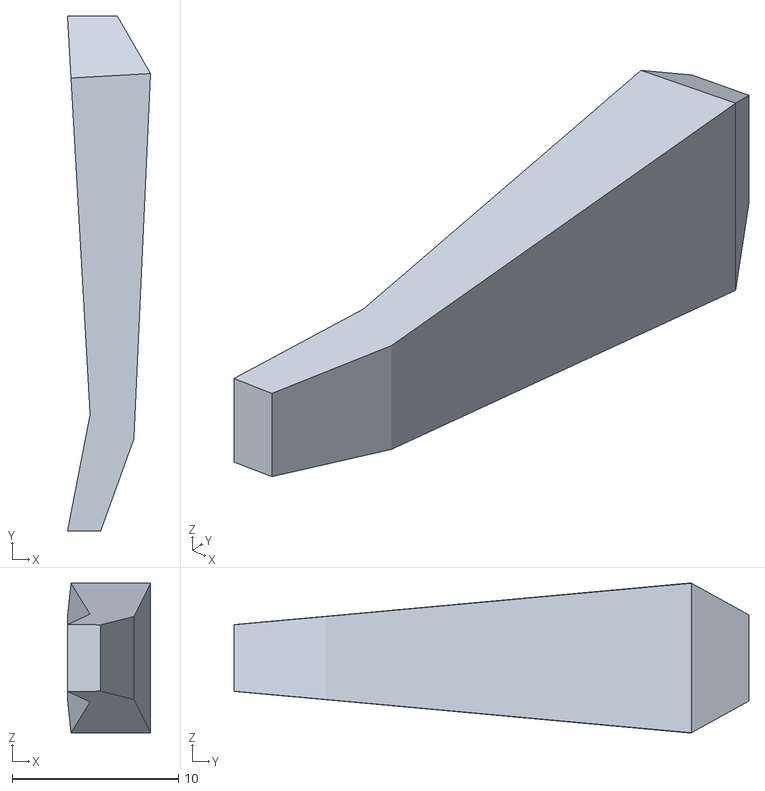
[picture p223: CAD file, 2016-10-01]
print/DistPhalangeIndex.stl
5.00 x 31.0 x 9.00
