01binary/elysium-max-exoskeleton/print/PelvisLink.stl

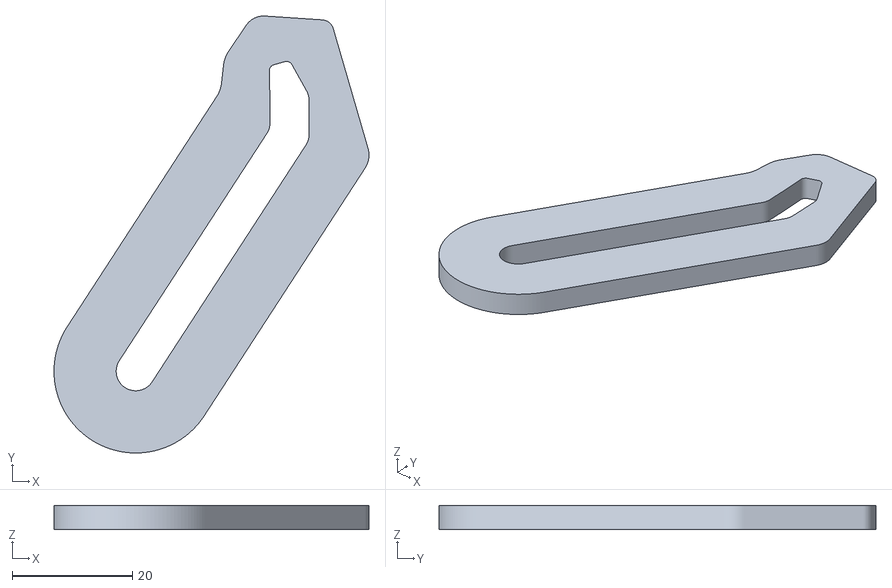
[picture p224: CAD file, 2016-10-01]
print/PelvisLink.stl
52.4 x 72.7 x 4.00
