01binary/elysium-max-exoskeleton/print/MetacarpusIndex.stl

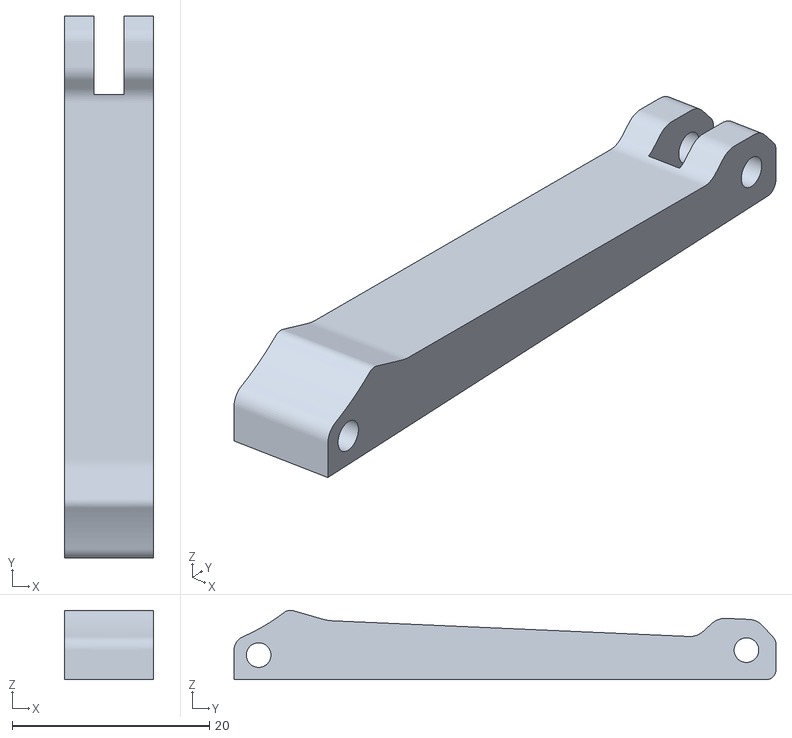
[picture p225: CAD file, 2016-10-01]
print/MetacarpusIndex.stl
9.00 x 55.0 x 7.04
