01binary/elysium-max-exoskeleton/print/PelvisSubLink.stl

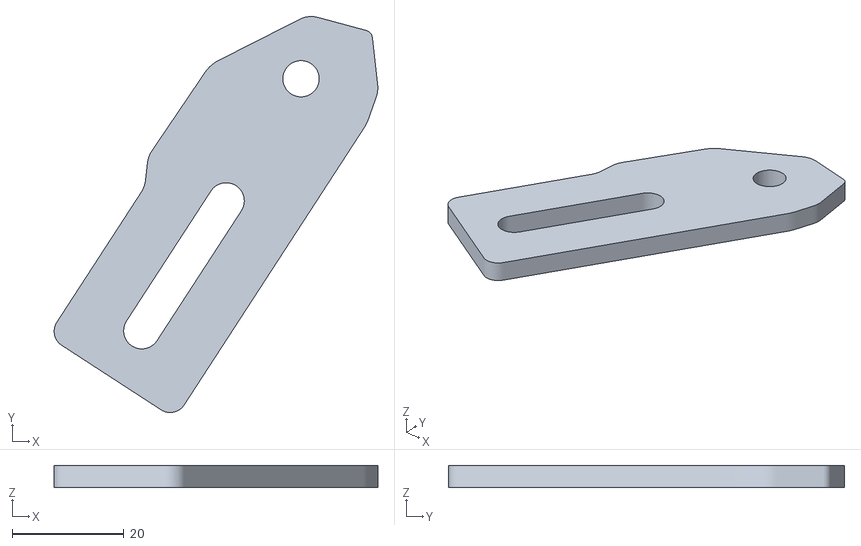
[picture p226: CAD file, 2016-10-01]
print/PelvisSubLink.stl
58.0 x 71.0 x 4.00
