01binary/elysium-max-exoskeleton/print/ForearmInnerBase.stl

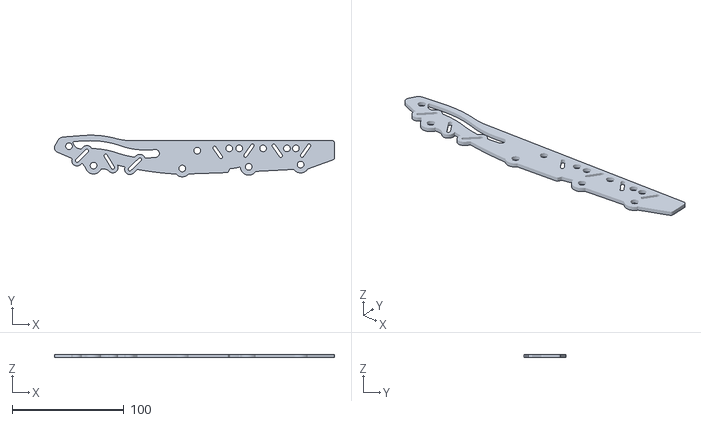
[picture p227: CAD file, 2016-10-01]
print/ForearmInnerBase.stl
250.9 x 37.3 x 3.00
