01binary/elysium-max-exoskeleton/print/PelvisWingRight.stl

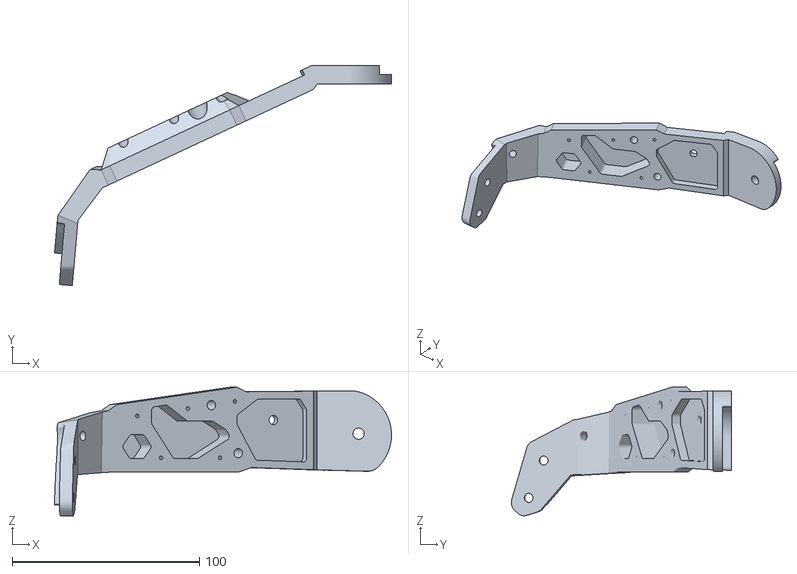
[picture p228: CAD file, 2016-10-01]
print/PelvisWingRight.stl
180.1 x 117.7 x 68.7
