01binary/elysium-max-exoskeleton/print/HipBottomConnectorRight.stl

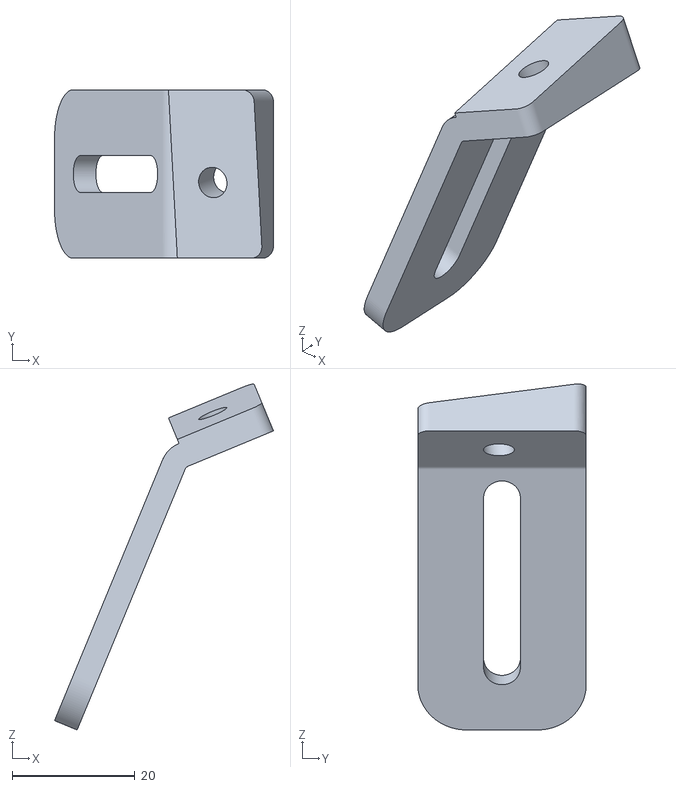
[picture p229: CAD file, 2016-10-01]
print/HipBottomConnectorRight.stl
35.7 x 27.5 x 56.5
