01binary/elysium-max-exoskeleton/print/ShoulderConnectorSplitBody.stl

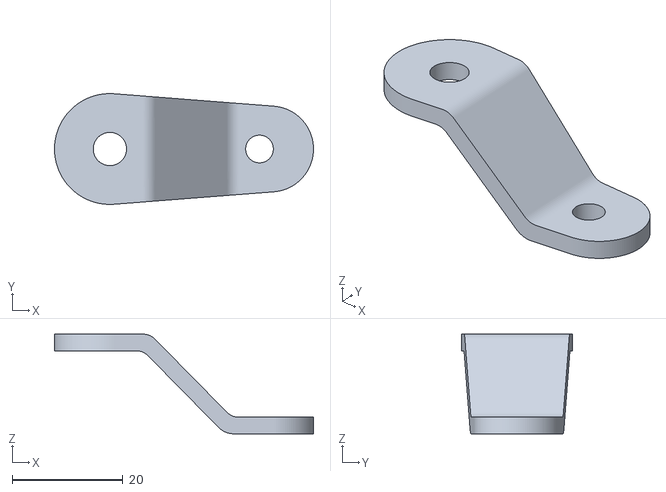
[picture p230: CAD file, 2016-10-01]
print/ShoulderConnectorSplitBody.stl
46.7 x 20.0 x 18.0
