01binary/elysium-max-exoskeleton/print/HandShockPlateLeft.stl

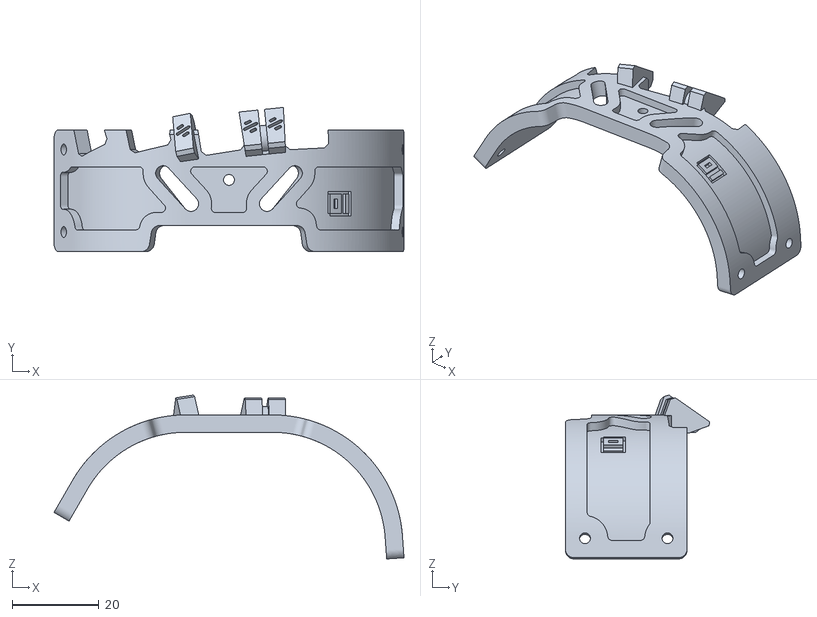
[picture p231: CAD file, 2016-10-01]
print/HandShockPlateLeft.stl
80.5 x 33.2 x 37.7
