01binary/elysium-max-exoskeleton/print/ThumbRouter.stl

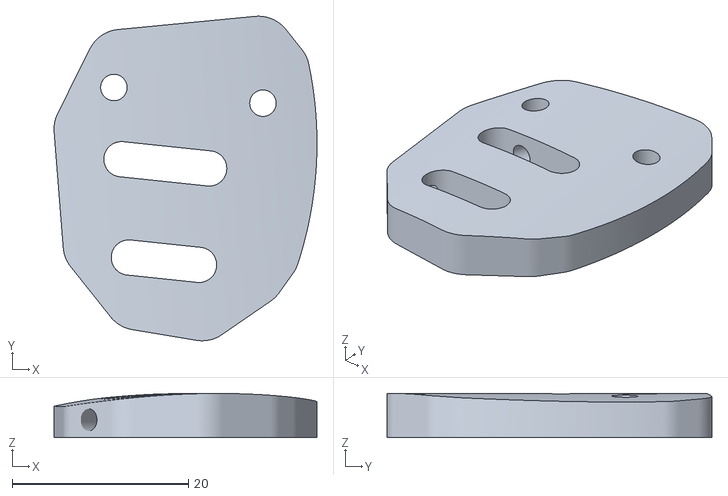
[picture p232: CAD file, 2016-10-01]
print/ThumbRouter.stl
29.8 x 36.8 x 5.00
