01binary/elysium-max-exoskeleton/print/ProxPhalangeThumb.stl

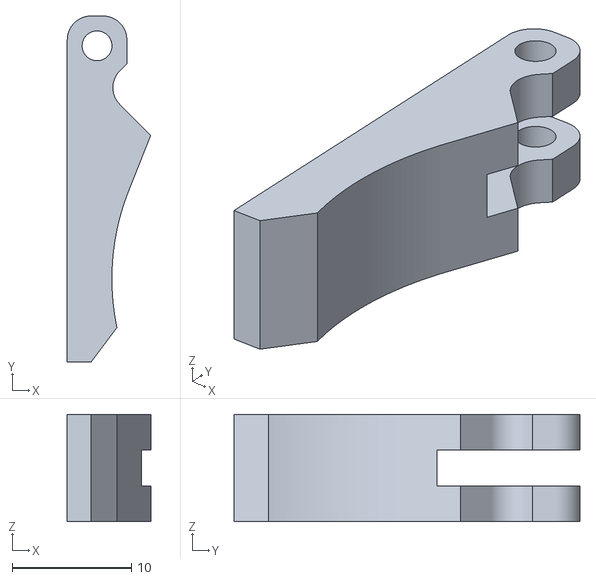
[picture p233: CAD file, 2016-10-01]
print/ProxPhalangeThumb.stl
7.00 x 29.0 x 9.00
