01binary/elysium-max-exoskeleton/print/VacuumTubeHolder.stl

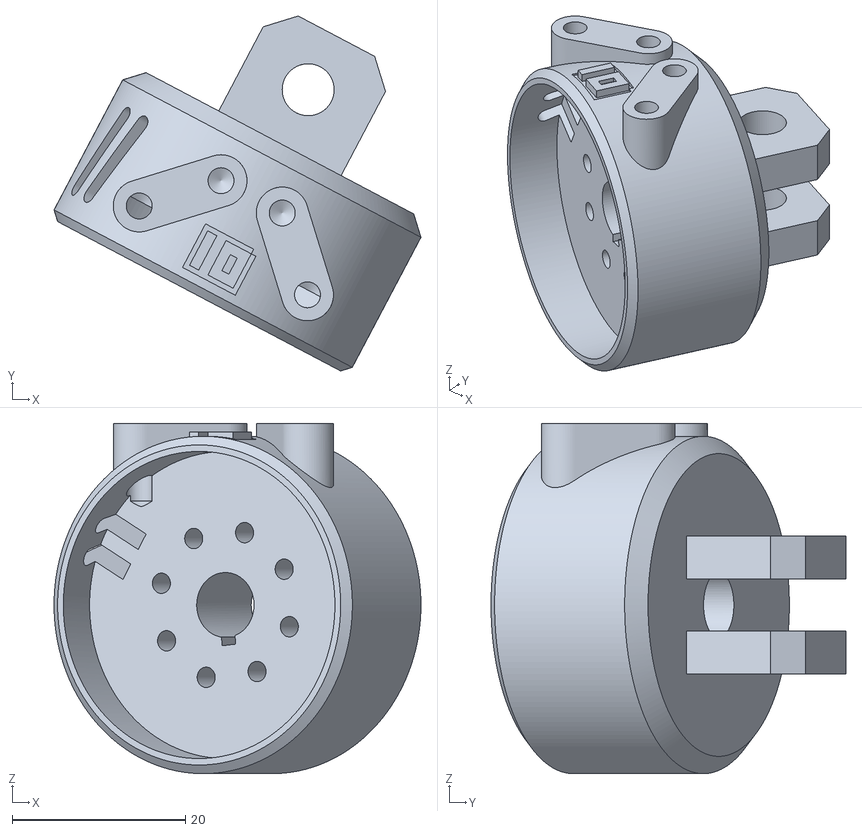
[picture p234: CAD file, 2016-10-01]
print/VacuumTubeHolder.stl
42.4 x 41.0 x 40.5
