01binary/elysium-max-exoskeleton/print/HandRibLeft.stl

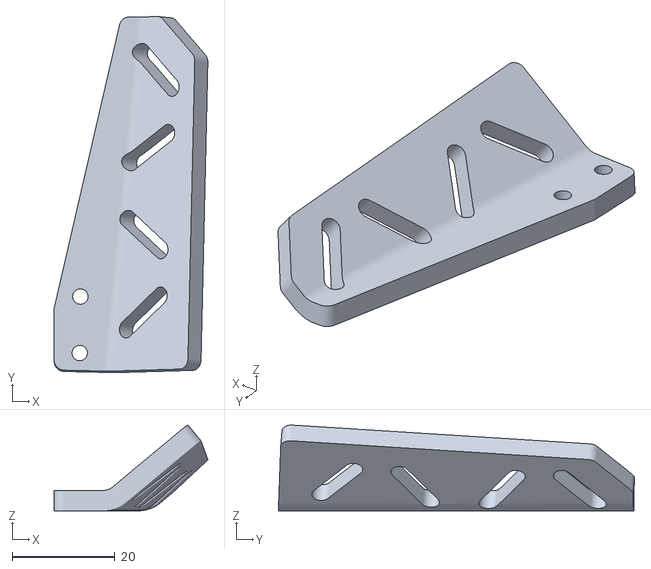
[picture p235: CAD file, 2016-10-01]
print/HandRibLeft.stl
30.0 x 69.4 x 16.7
