01binary/elysium-max-exoskeleton/print/SpineCoverLeft.stl

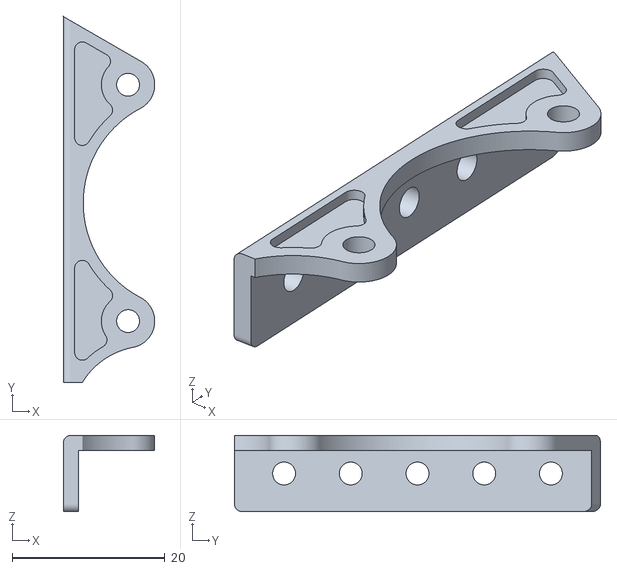
[picture p236: CAD file, 2016-10-01]
print/SpineCoverLeft.stl
12.0 x 48.0 x 10.0
