01binary/elysium-max-exoskeleton/print/UpperForearmLeft.stl

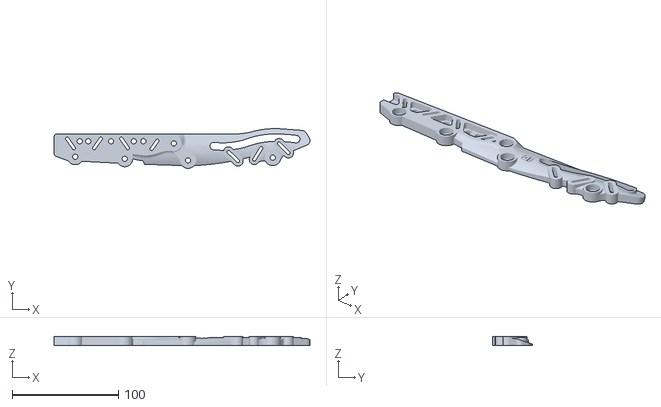
[picture p237: CAD file, 2016-10-01]
print/UpperForearmLeft.stl
240.5 x 37.3 x 8.00
