01binary/elysium-max-exoskeleton/print/SpineCoverMiddle.stl

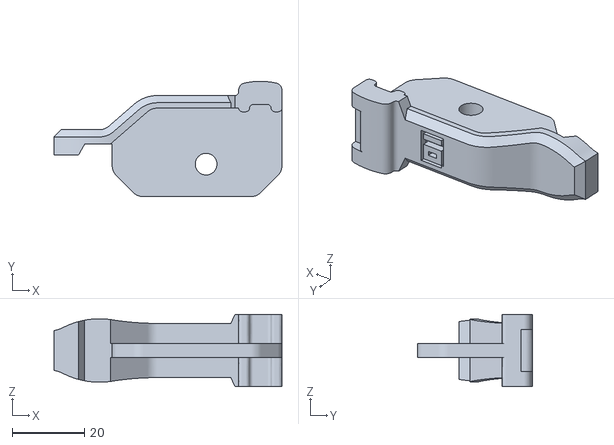
[picture p238: CAD file, 2016-10-01]
print/SpineCoverMiddle.stl
63.1 x 31.9 x 20.0
