01binary/elysium-max-exoskeleton/print/ShoulderConnectorSplitHead.stl

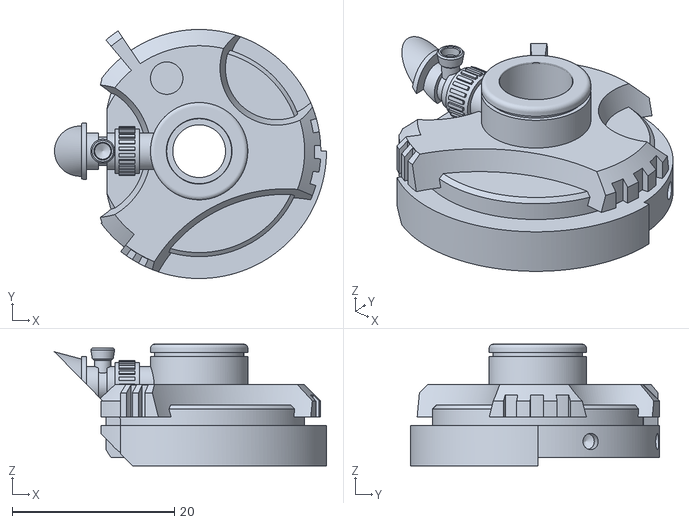
[picture p239: CAD file, 2016-10-01]
print/ShoulderConnectorSplitHead.stl
33.5 x 30.7 x 15.0
