01binary/elysium-max-exoskeleton/print/BackSideConnector.stl

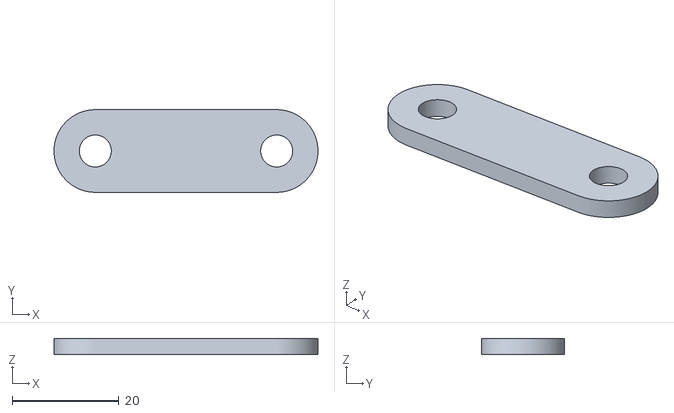
[picture p240: CAD file, 2016-10-01]
print/BackSideConnector.stl
49.5 x 15.5 x 3.00
