01binary/elysium-max-exoskeleton/print/ProxPhalangePinky.stl

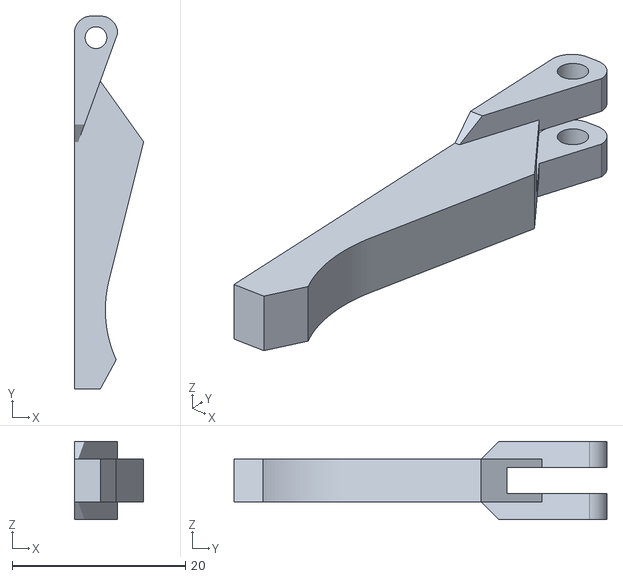
[picture p241: CAD file, 2016-10-01]
print/ProxPhalangePinky.stl
8.00 x 43.0 x 9.00
