01binary/elysium-max-exoskeleton/print/BackConnector.stl

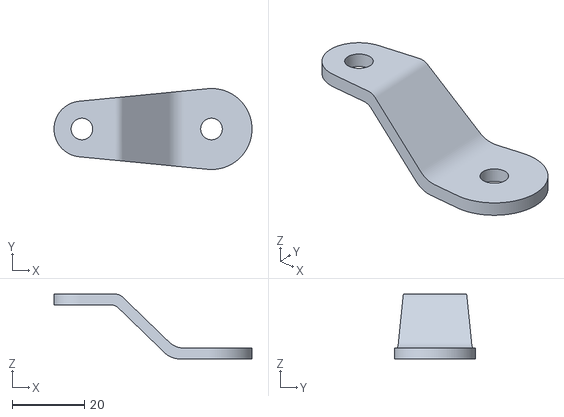
[picture p242: CAD file, 2016-10-01]
print/BackConnector.stl
55.0 x 22.5 x 18.0
