01binary/elysium-max-exoskeleton/print/Knuckle.stl

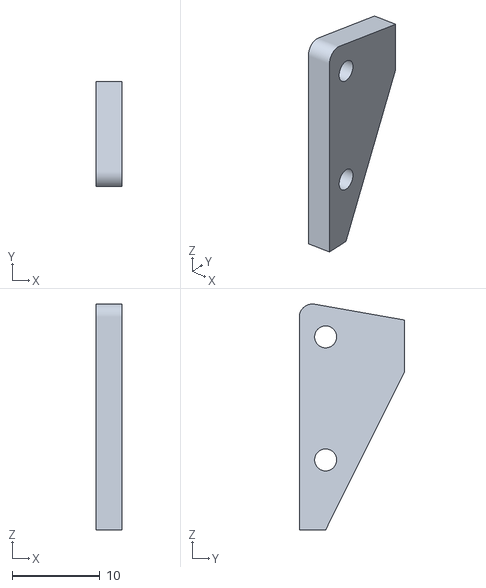
[picture p243: CAD file, 2016-10-01]
print/Knuckle.stl
3.00 x 12.0 x 25.7
