01binary/elysium-max-exoskeleton/print/LowerForearm.stl

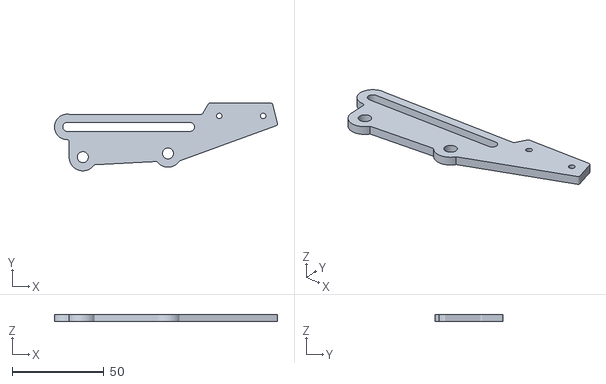
[picture p244: CAD file, 2016-10-01]
print/LowerForearm.stl
121.8 x 37.0 x 4.00
