01binary/elysium-max-exoskeleton/print/KnuckleSide.stl

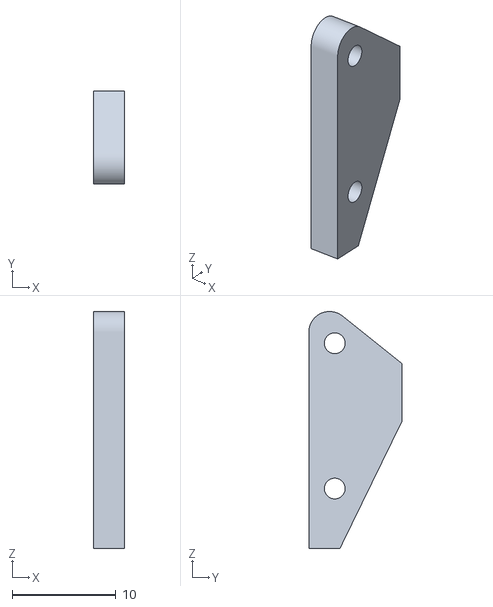
[picture p245: CAD file, 2016-10-01]
print/KnuckleSide.stl
3.00 x 9.00 x 22.8
