01binary/elysium-max-exoskeleton/print/DistPhalangePinky.stl

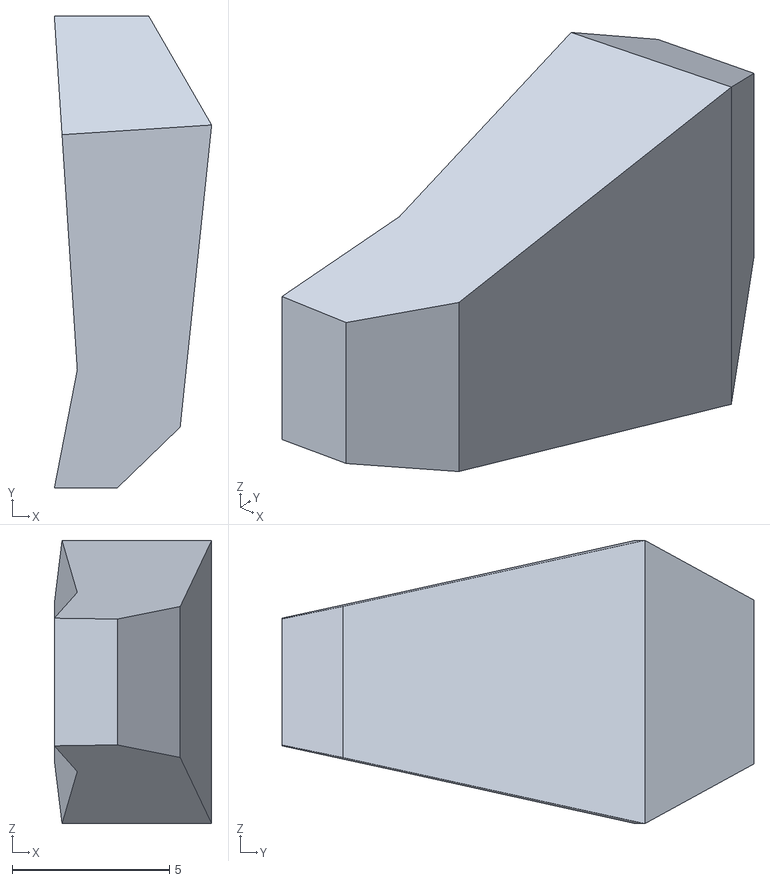
[picture p246: CAD file, 2016-10-01]
print/DistPhalangePinky.stl
5.00 x 15.0 x 9.00
