01binary/elysium-max-exoskeleton/print/MetacarpusPinky.stl

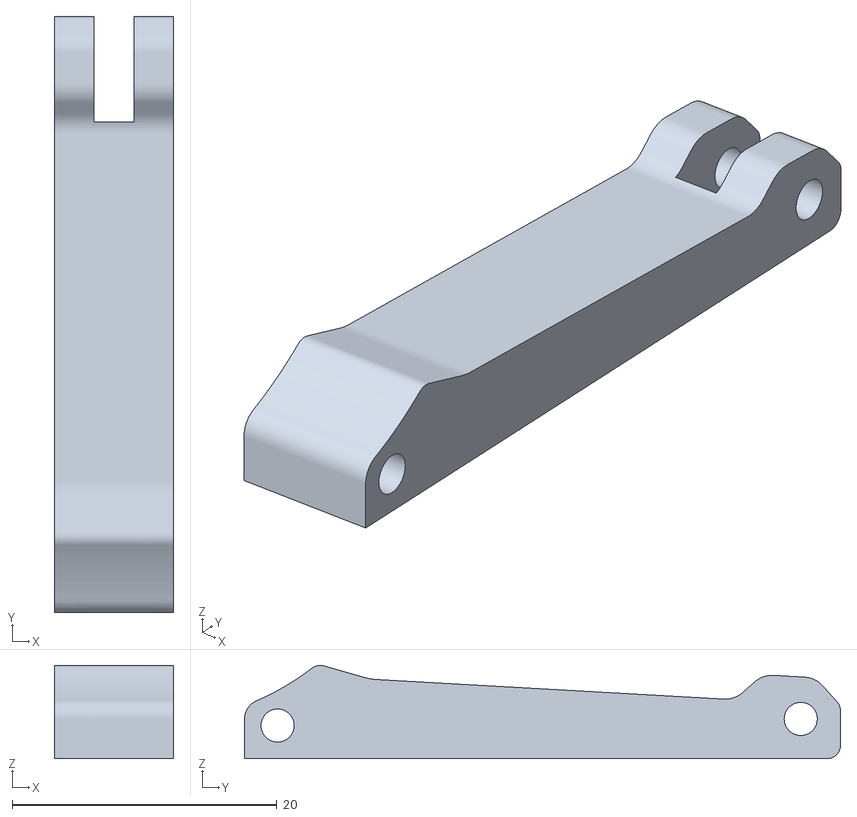
[picture p247: CAD file, 2016-10-01]
print/MetacarpusPinky.stl
9.00 x 45.0 x 7.04
