01binary/elysium-max-exoskeleton/print/PelvisMount.stl

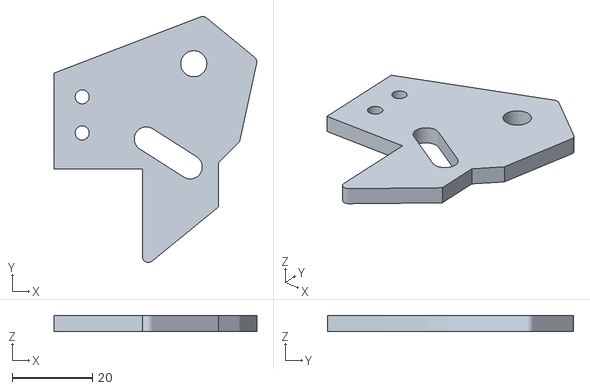
[picture p248: CAD file, 2016-10-01]
print/PelvisMount.stl
50.6 x 61.4 x 4.00
