01binary/elysium-max-exoskeleton/print/SpineTopMiddleConnector.stl

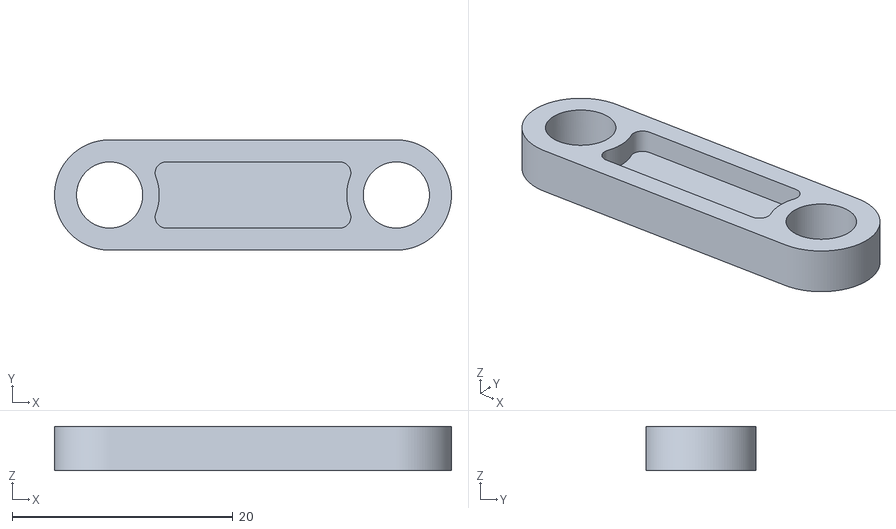
[picture p249: CAD file, 2016-10-01]
print/SpineTopMiddleConnector.stl
36.0 x 10.0 x 4.00
