01binary/elysium-max-exoskeleton/print/PinkyRouter.stl

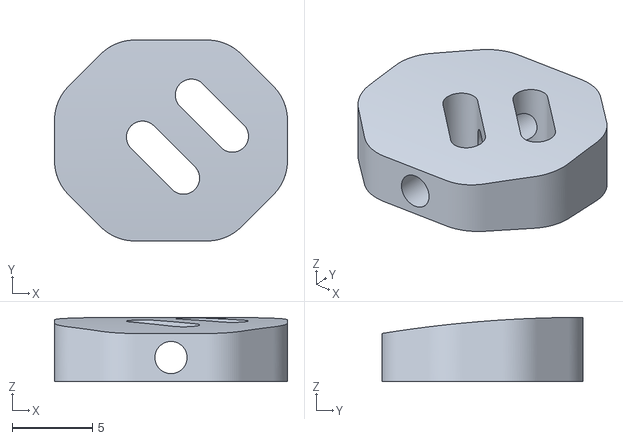
[picture p250: CAD file, 2016-10-01]
print/PinkyRouter.stl
14.5 x 12.5 x 4.00
