01binary/elysium-max-exoskeleton/print/ForearmPistonConnector.stl

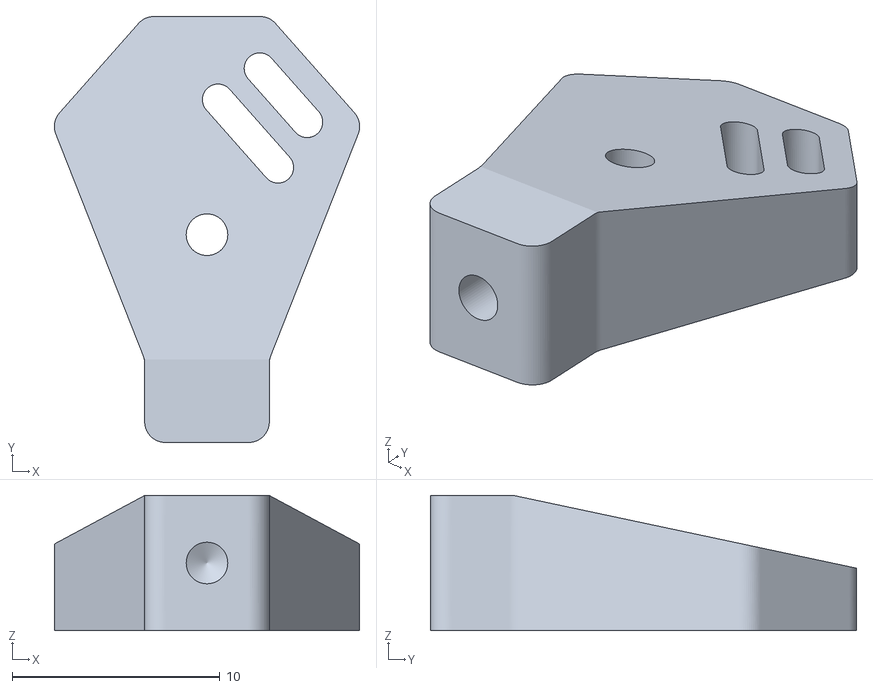
[picture p251: CAD file, 2016-10-01]
print/ForearmPistonConnector.stl
14.7 x 20.5 x 6.50
