01binary/elysium-max-exoskeleton/build/arm-assembled01.JPG

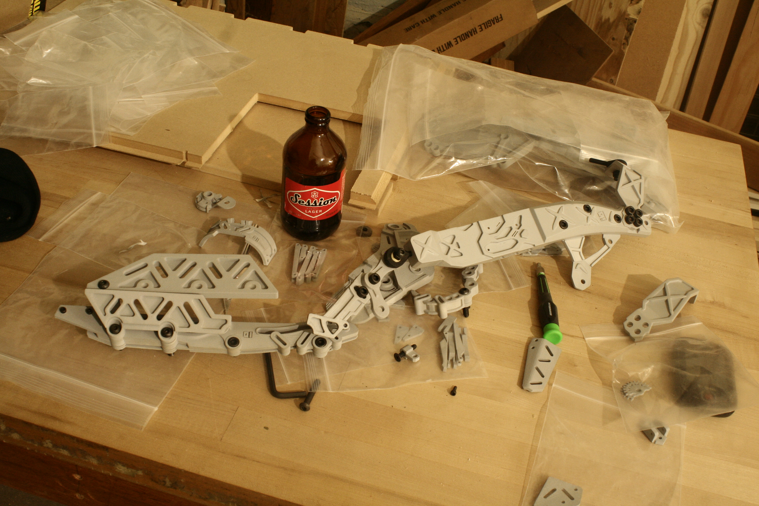
build/arm-assembled01.JPG
