01binary/elysium-max-exoskeleton/build/arm-assembled02.JPG

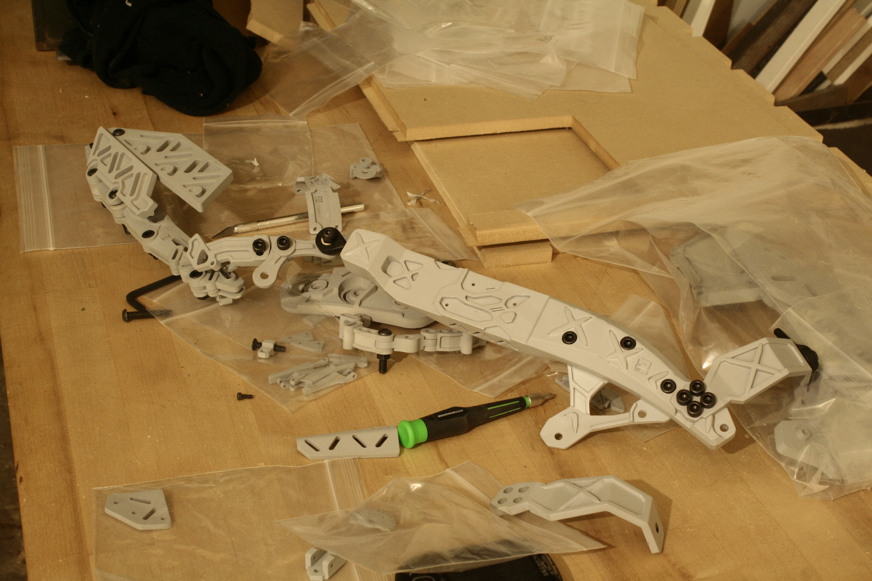
build/arm-assembled02.JPG
