01binary/elysium-max-exoskeleton/build/arm-assembled03.JPG

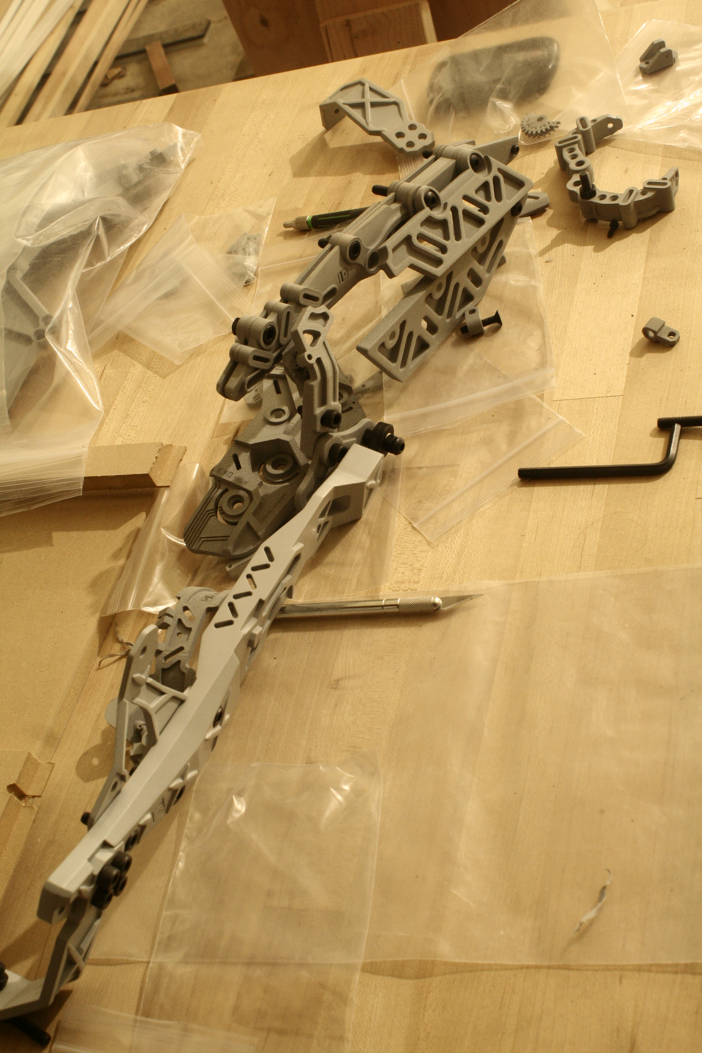
build/arm-assembled03.JPG
