01binary/elysium-max-exoskeleton/build/back01.png

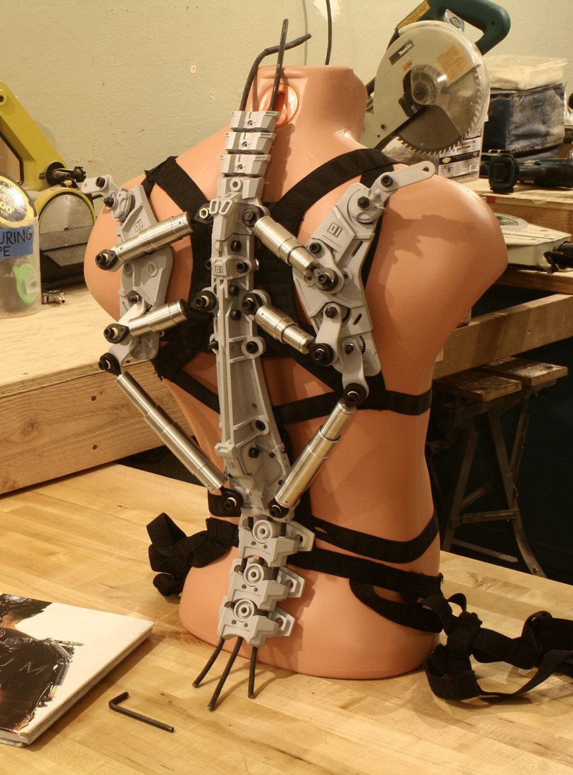
build/back01.png
