01binary/elysium-max-exoskeleton/build/back02.png

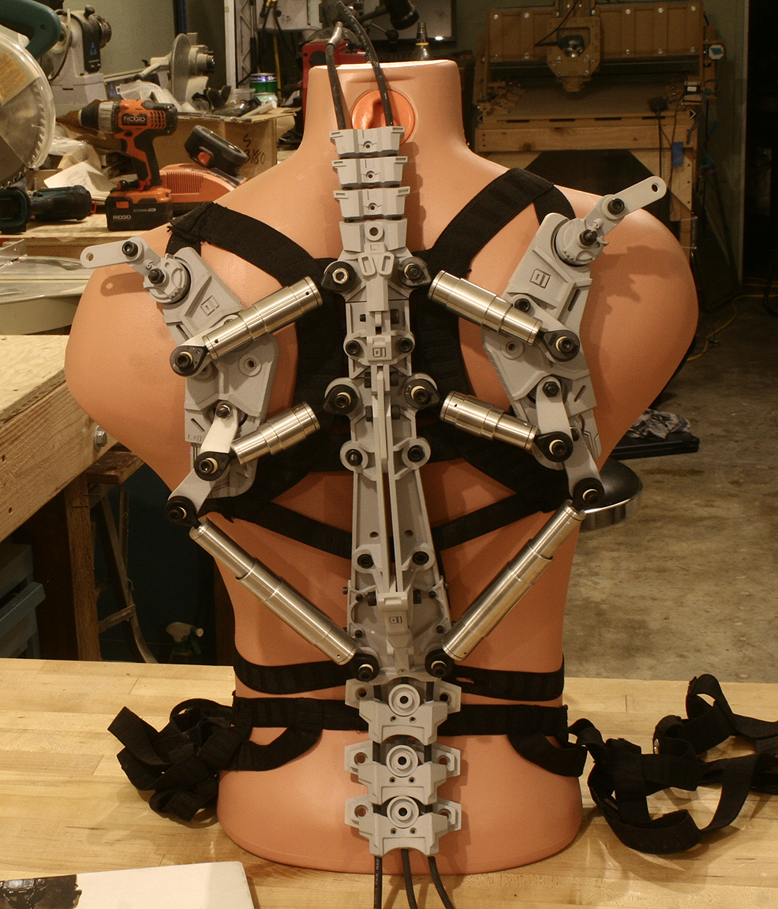
build/back02.png
