01binary/elysium-max-exoskeleton/build/back03.png

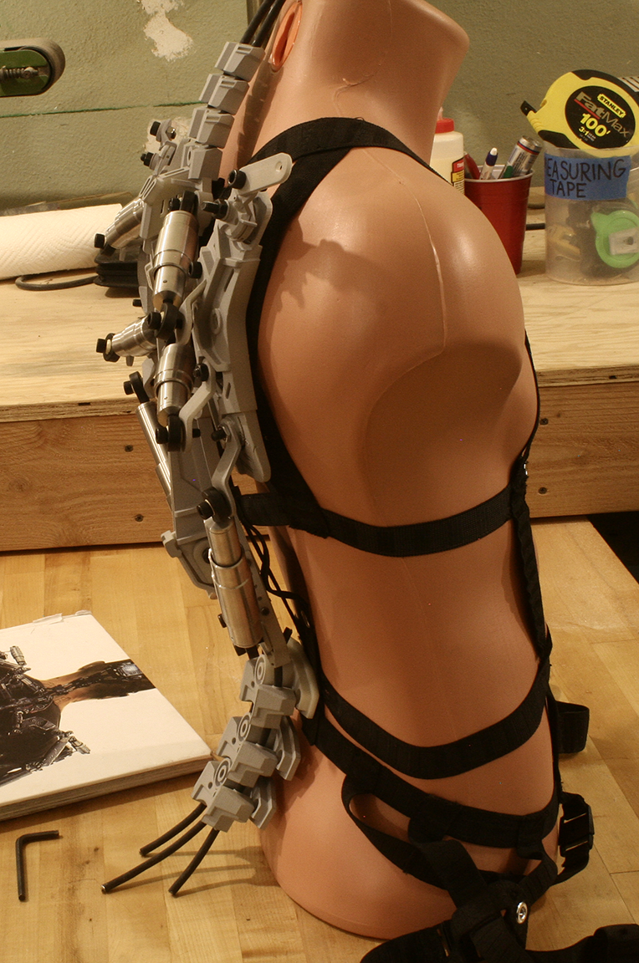
build/back03.png
