01binary/elysium-max-exoskeleton/build/back04.png

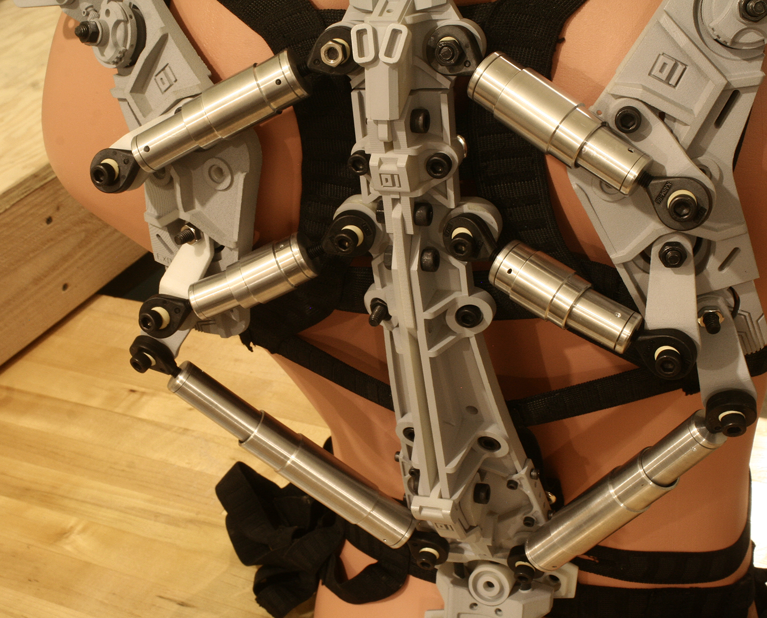
build/back04.png
