01binary/elysium-max-exoskeleton/build/boxed.png

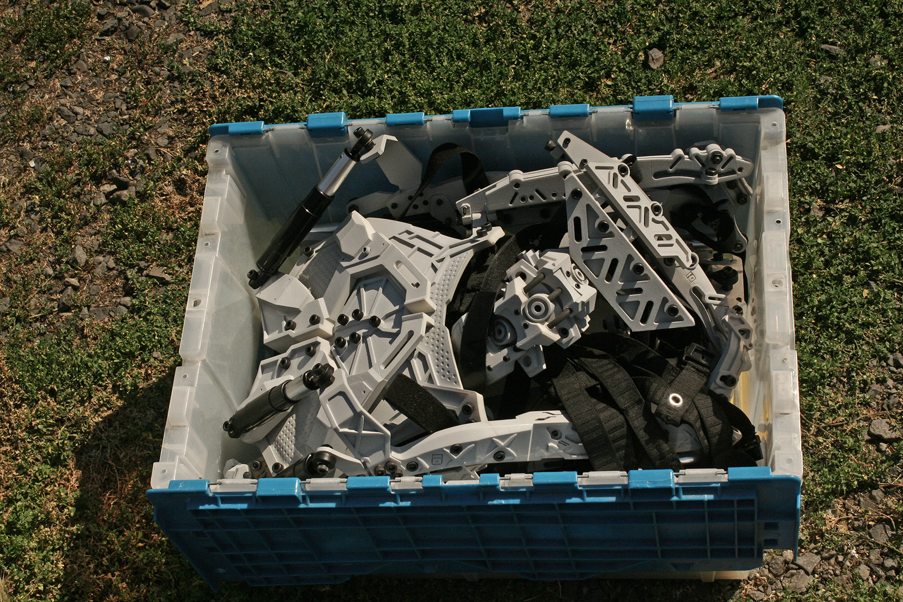
build/boxed.png
