01binary/elysium-max-exoskeleton/build/chestplate01.png

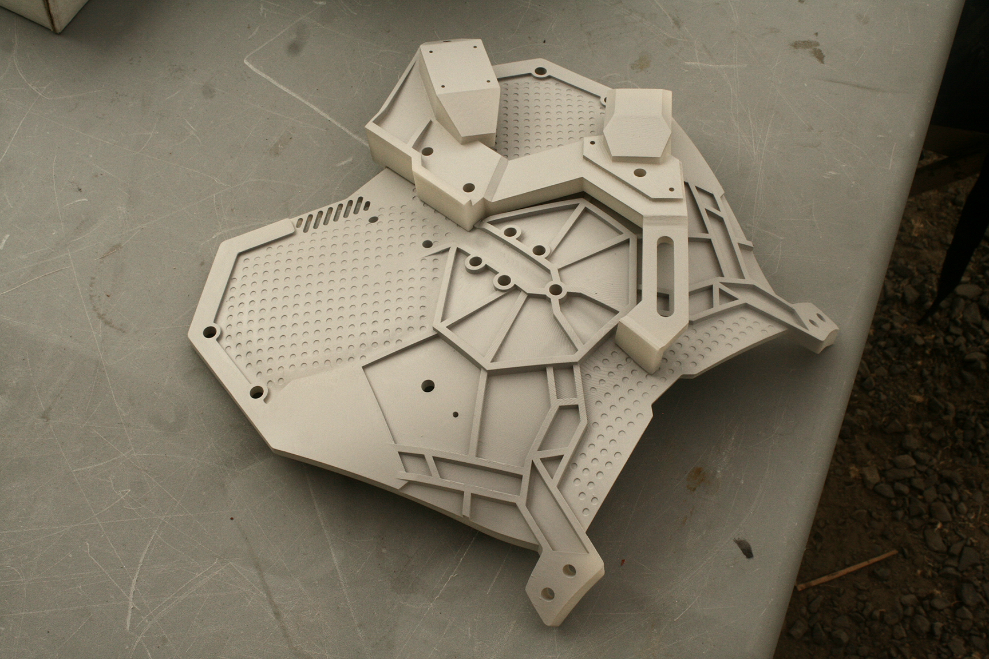
build/chestplate01.png
