01binary/elysium-max-exoskeleton/build/chestplate02.png

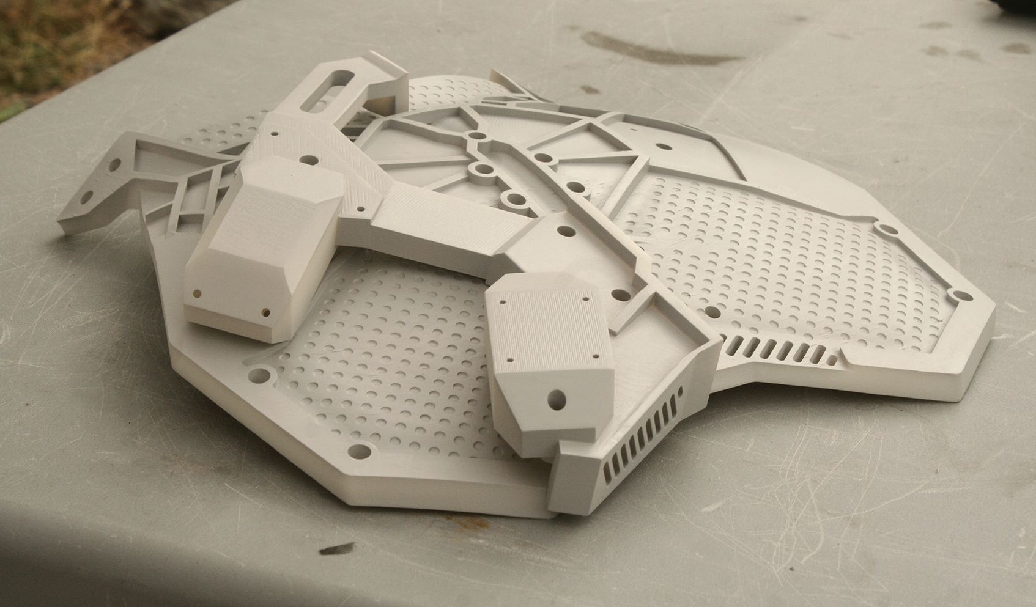
build/chestplate02.png
