01binary/elysium-max-exoskeleton/build/chestplate03.png

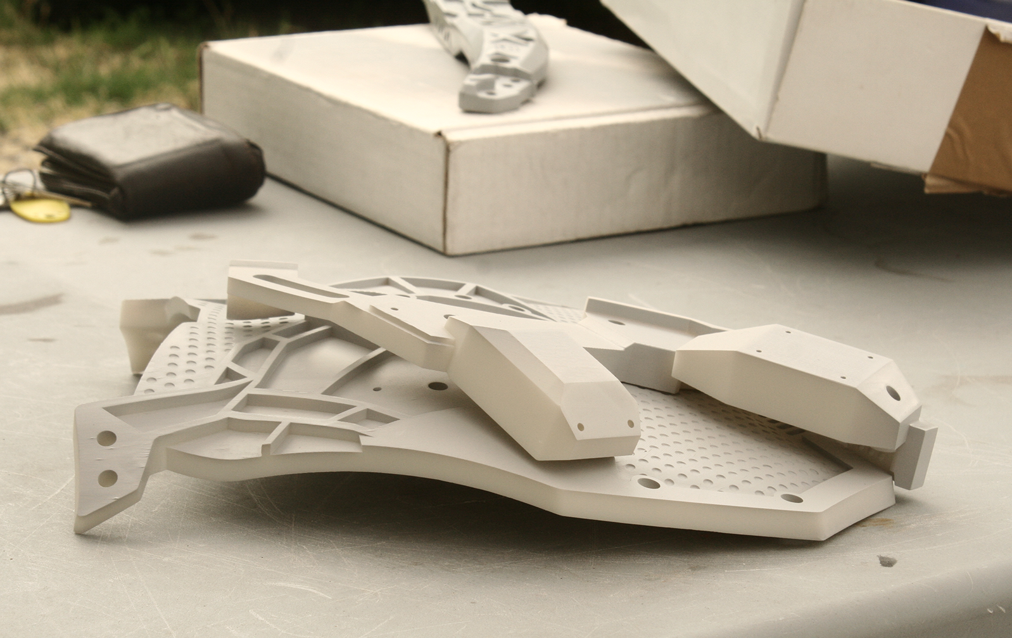
build/chestplate03.png
