01binary/elysium-max-exoskeleton/build/chestplate04.png

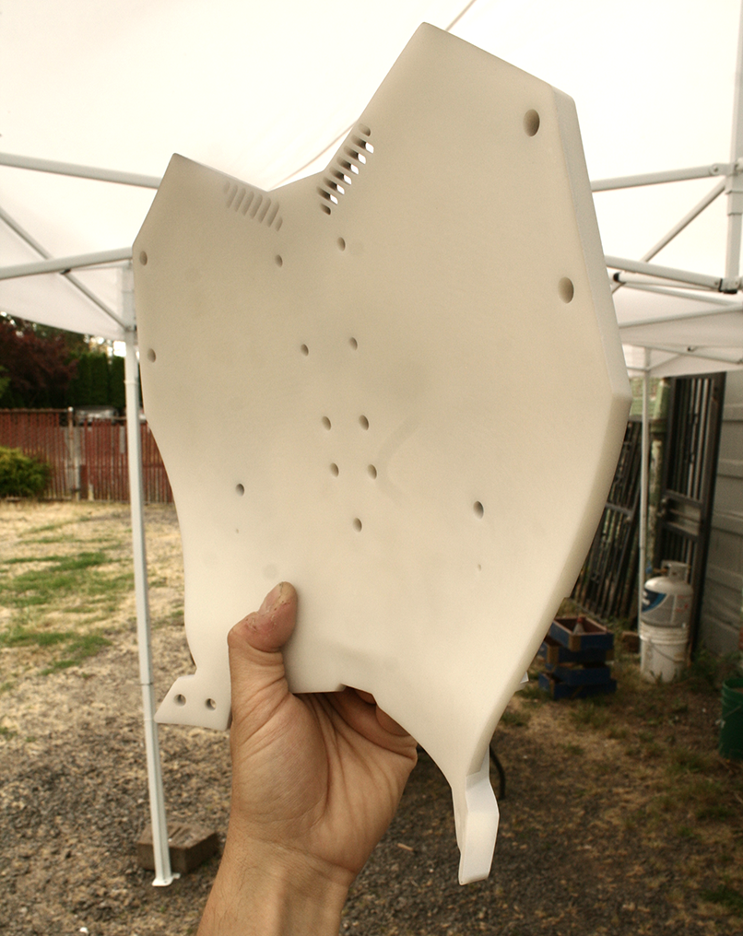
build/chestplate04.png
