01binary/elysium-max-exoskeleton/build/chestplate05.png

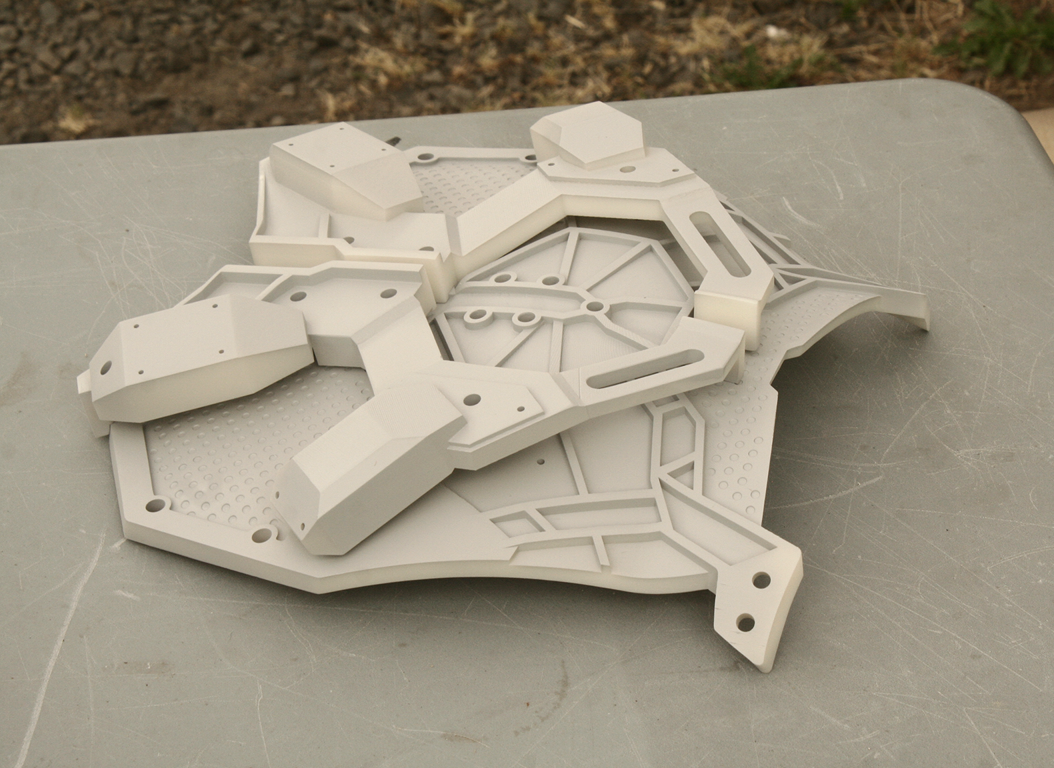
build/chestplate05.png
