01binary/elysium-max-exoskeleton/build/fans01.png

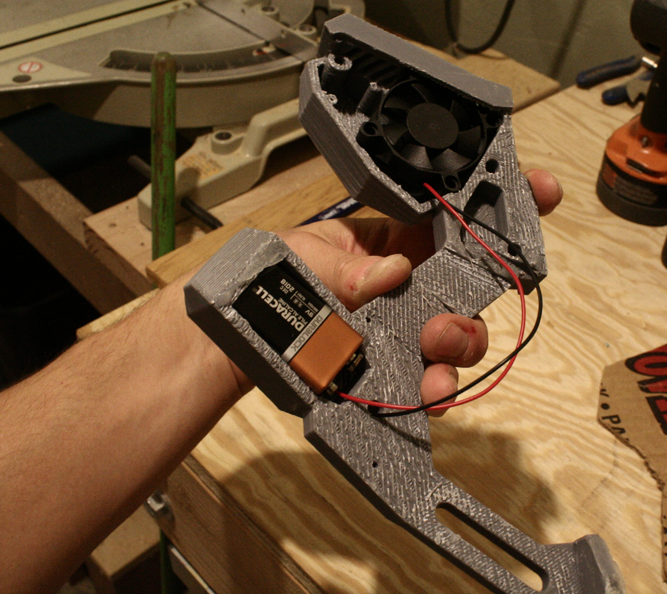
build/fans01.png
