01binary/elysium-max-exoskeleton/build/fans02.png

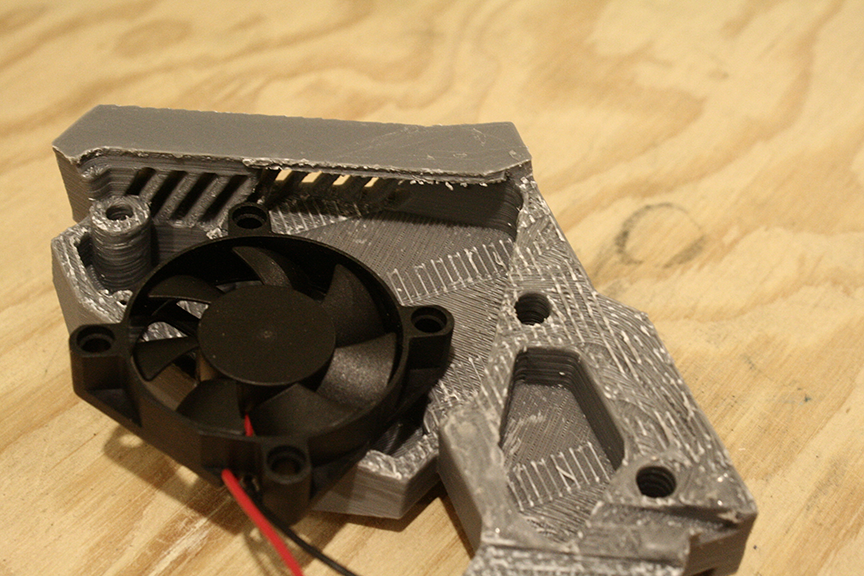
build/fans02.png
