01binary/elysium-max-exoskeleton/build/hand-assembled01.JPG

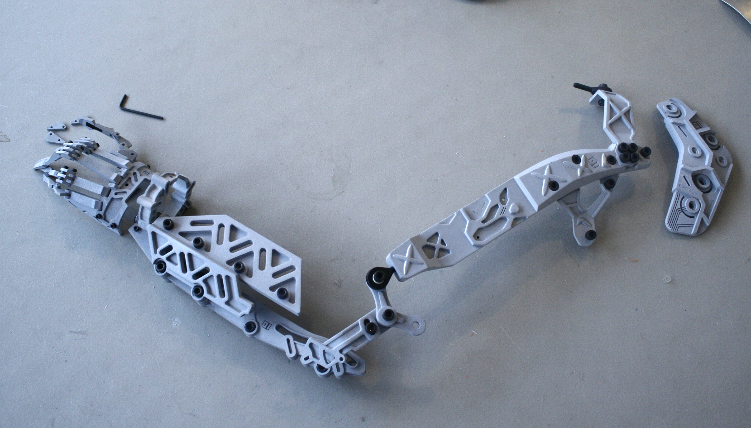
build/hand-assembled01.JPG
