01binary/elysium-max-exoskeleton/build/hand-assembled02.JPG

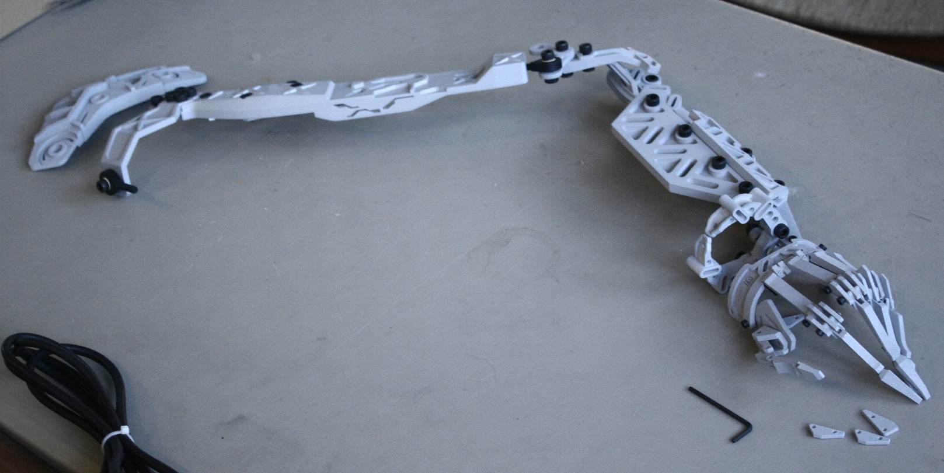
build/hand-assembled02.JPG
