01binary/elysium-max-exoskeleton/build/hand-assembled03.JPG

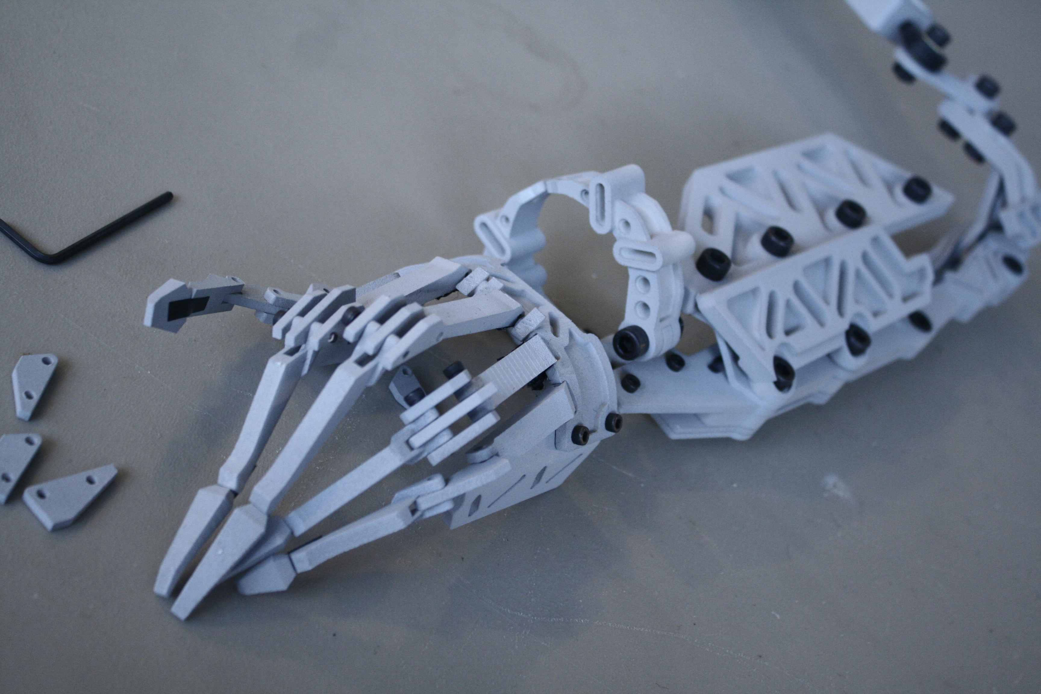
build/hand-assembled03.JPG
