01binary/elysium-max-exoskeleton/build/hand-proto01.JPG

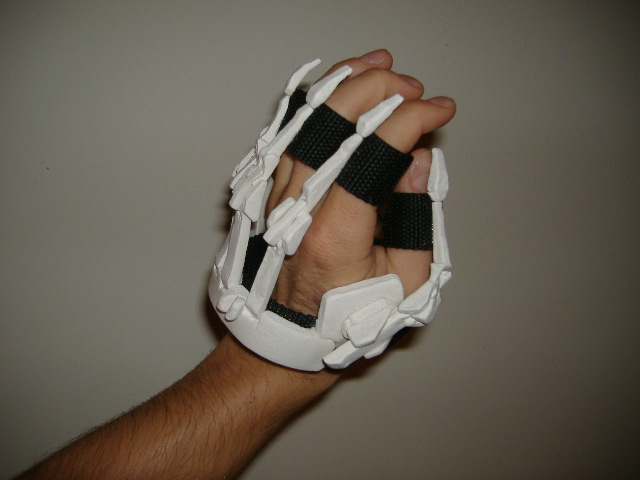
build/hand-proto01.JPG
