01binary/elysium-max-exoskeleton/build/hand-proto02.JPG

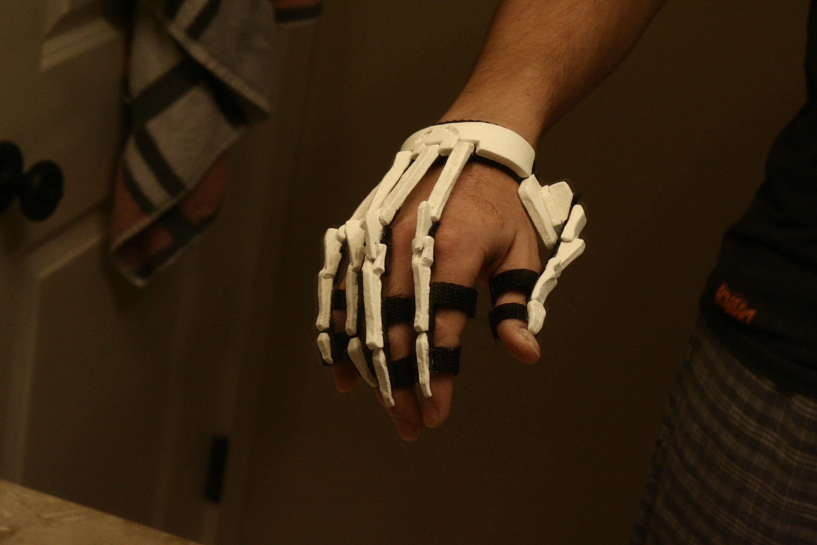
build/hand-proto02.JPG
