01binary/elysium-max-exoskeleton/build/hand-proto03.JPG

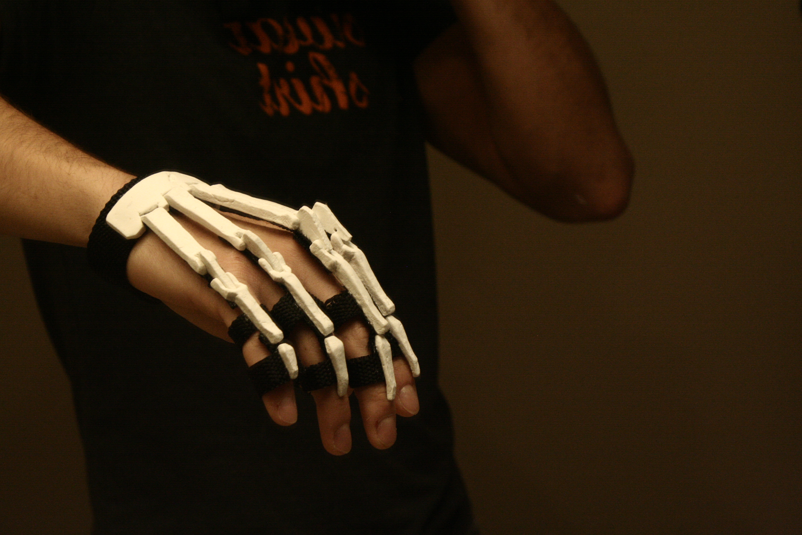
build/hand-proto03.JPG
