01binary/elysium-max-exoskeleton/build/hand-proto04.JPG

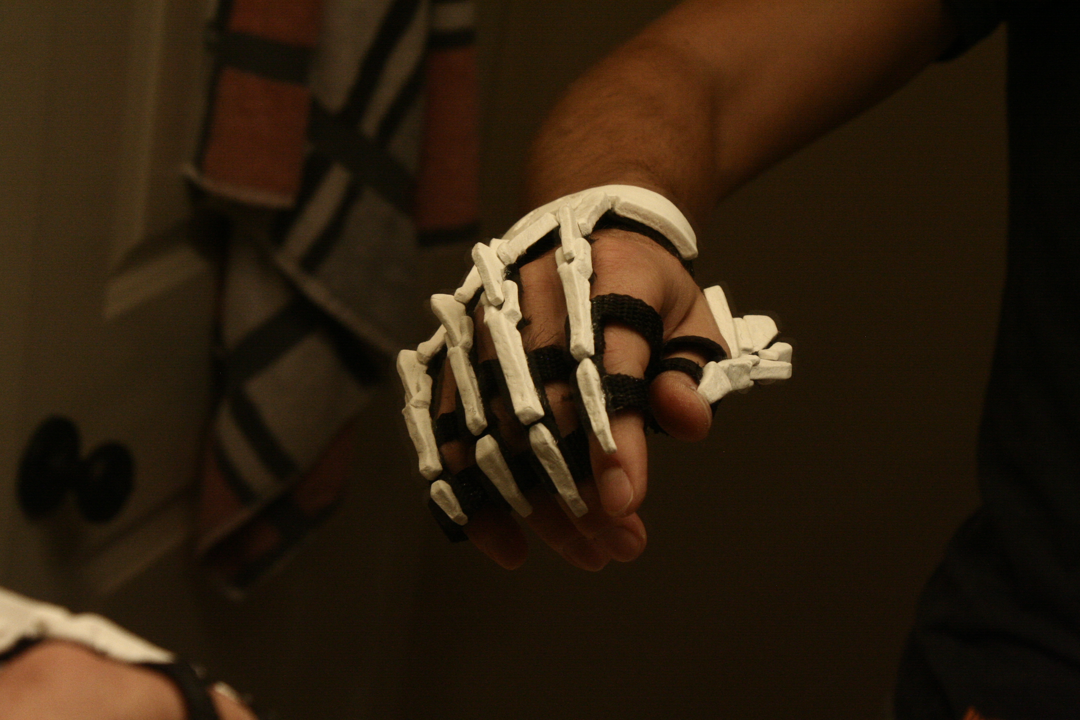
build/hand-proto04.JPG
