01binary/elysium-max-exoskeleton/build/hand-proto05.JPG

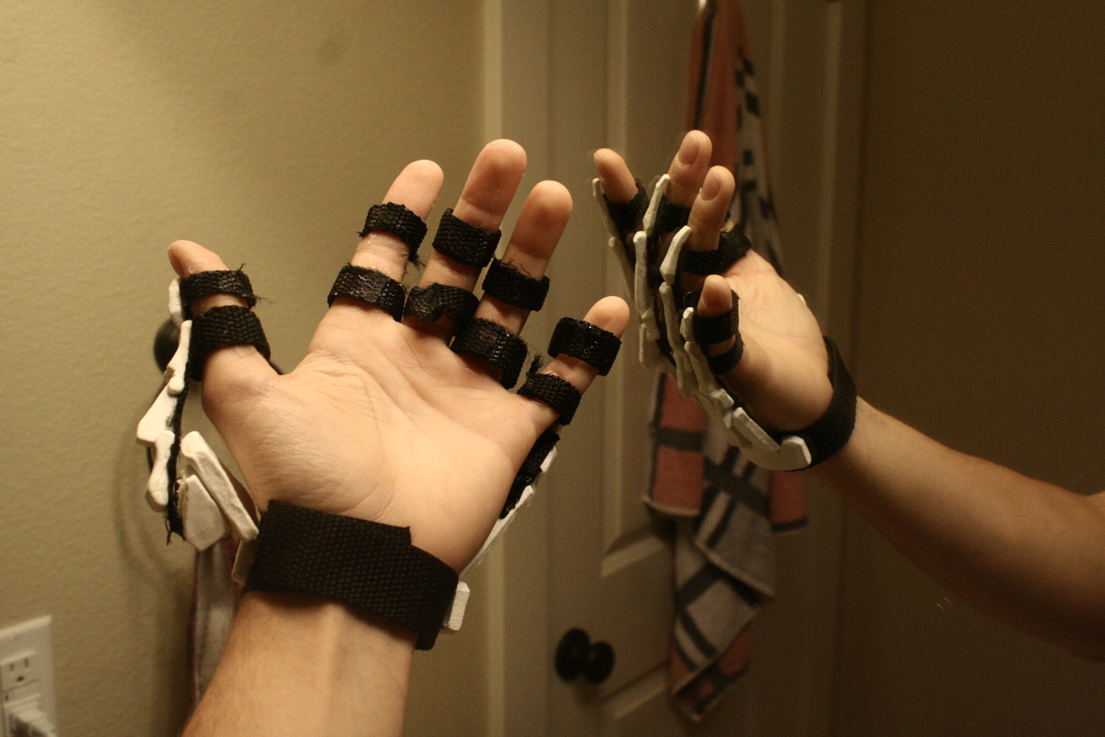
build/hand-proto05.JPG
