01binary/elysium-max-exoskeleton/build/hand-proto06.JPG

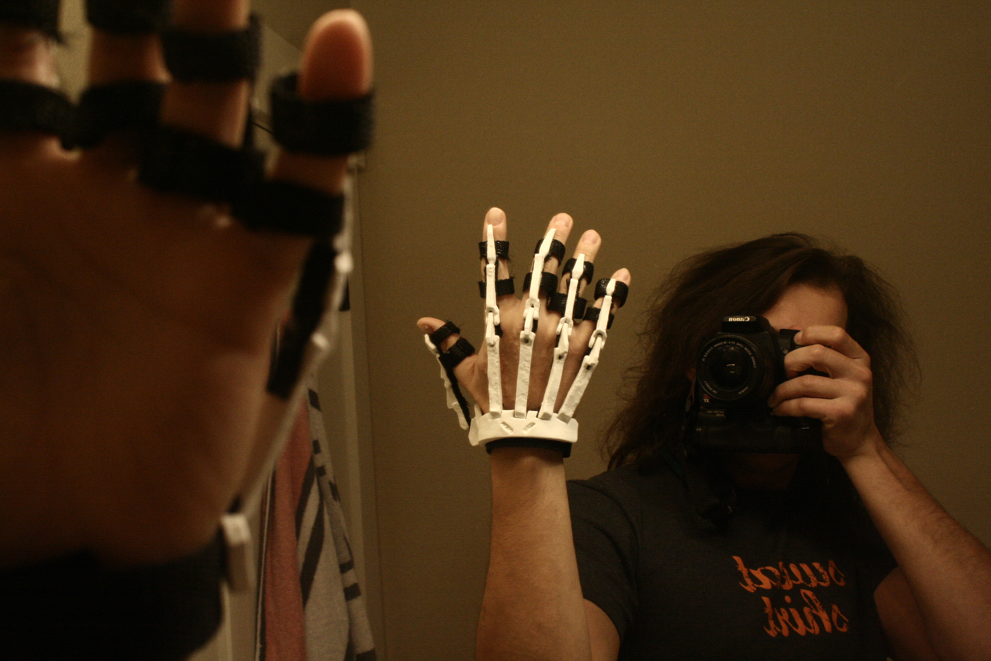
build/hand-proto06.JPG
