01binary/elysium-max-exoskeleton/build/hand-proto07.JPG

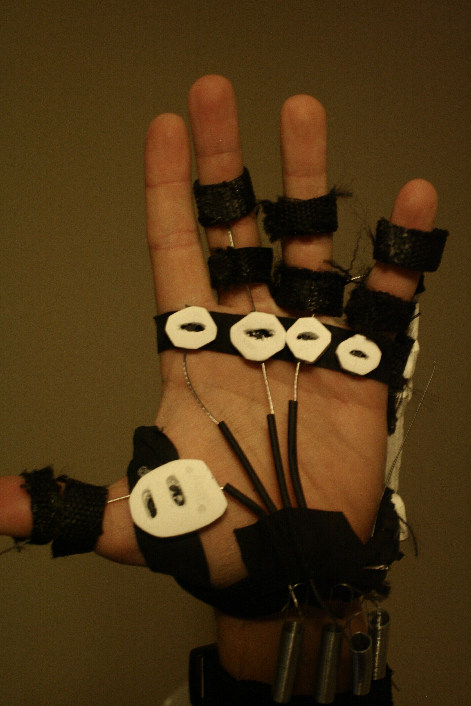
build/hand-proto07.JPG
