01binary/elysium-max-exoskeleton/build/hand-proto08.JPG

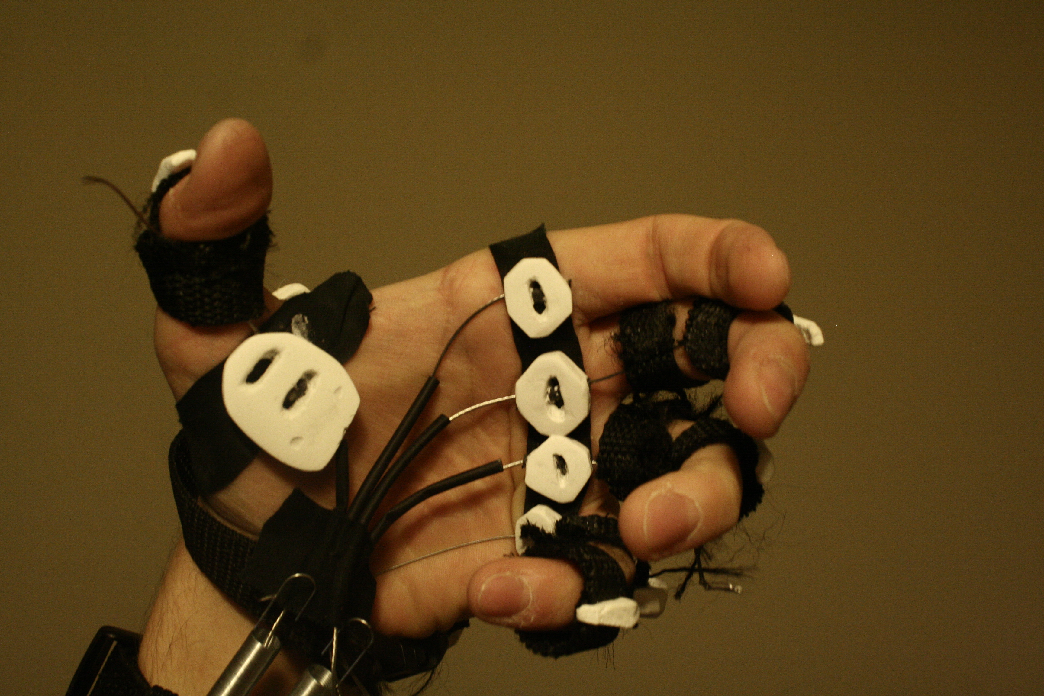
build/hand-proto08.JPG
