01binary/elysium-max-exoskeleton/build/hand-proto09.JPG

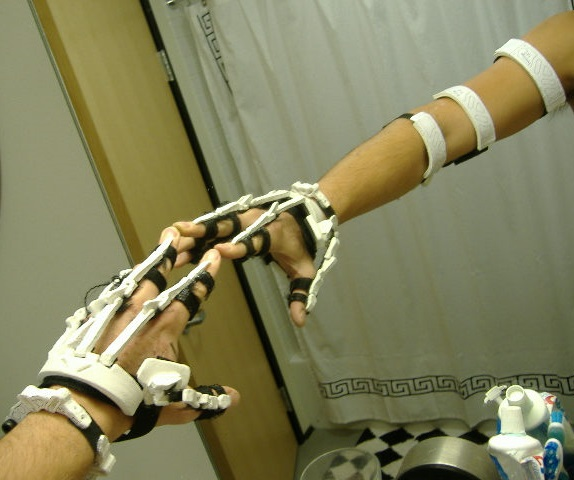
build/hand-proto09.JPG
