01binary/elysium-max-exoskeleton/build/hang01.png

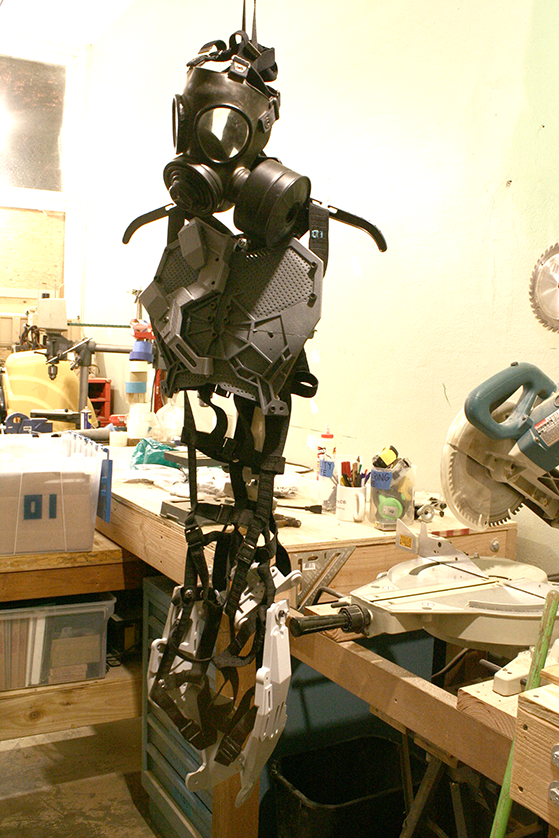
build/hang01.png
