01binary/elysium-max-exoskeleton/build/hang02.png

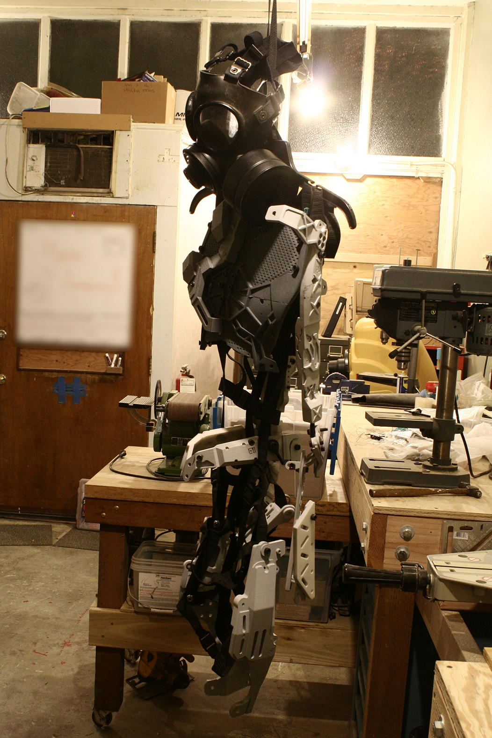
build/hang02.png
