01binary/elysium-max-exoskeleton/build/hang03.png

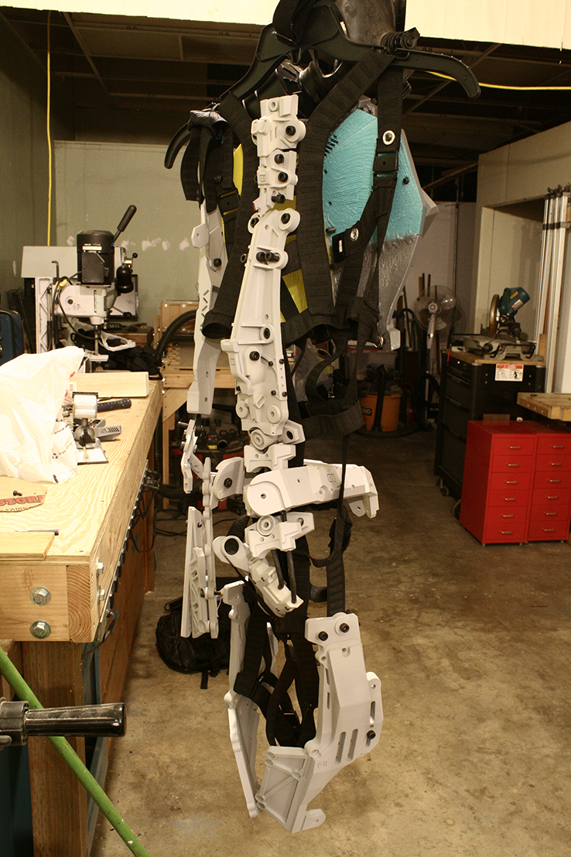
build/hang03.png
