01binary/elysium-max-exoskeleton/build/hang04.png

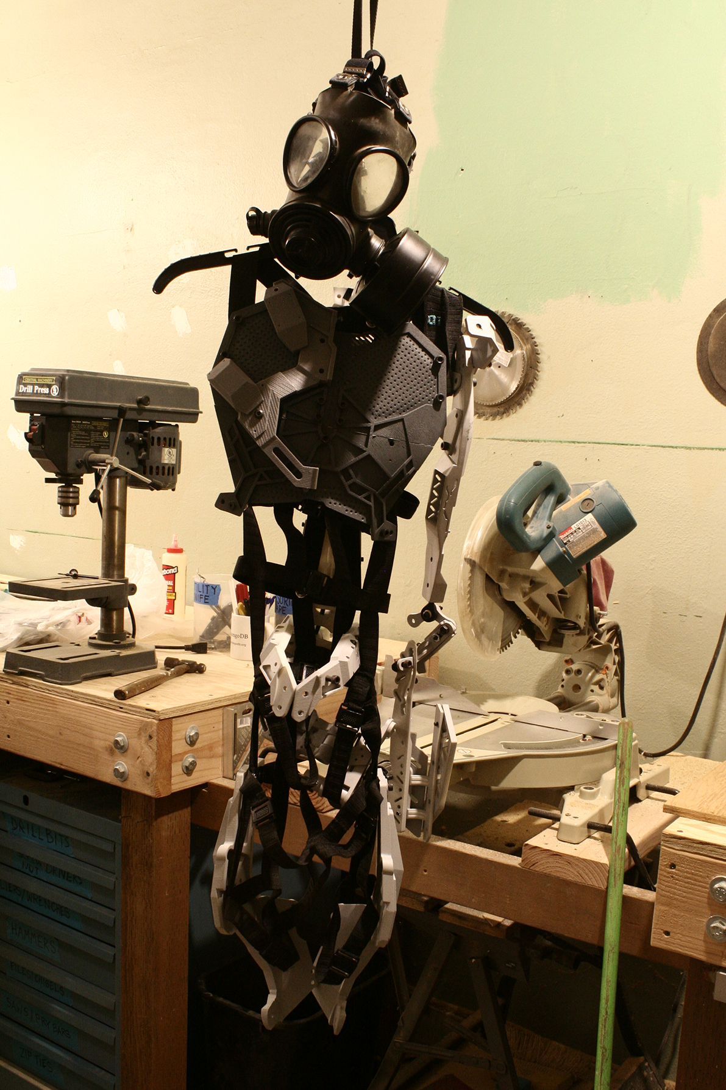
build/hang04.png
