01binary/elysium-max-exoskeleton/build/hang05.png

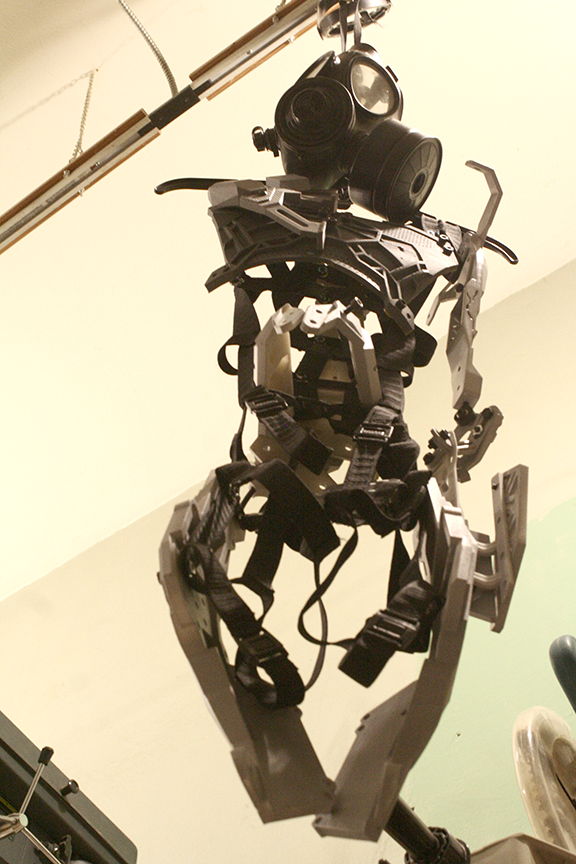
build/hang05.png
