01binary/elysium-max-exoskeleton/build/hang06.png

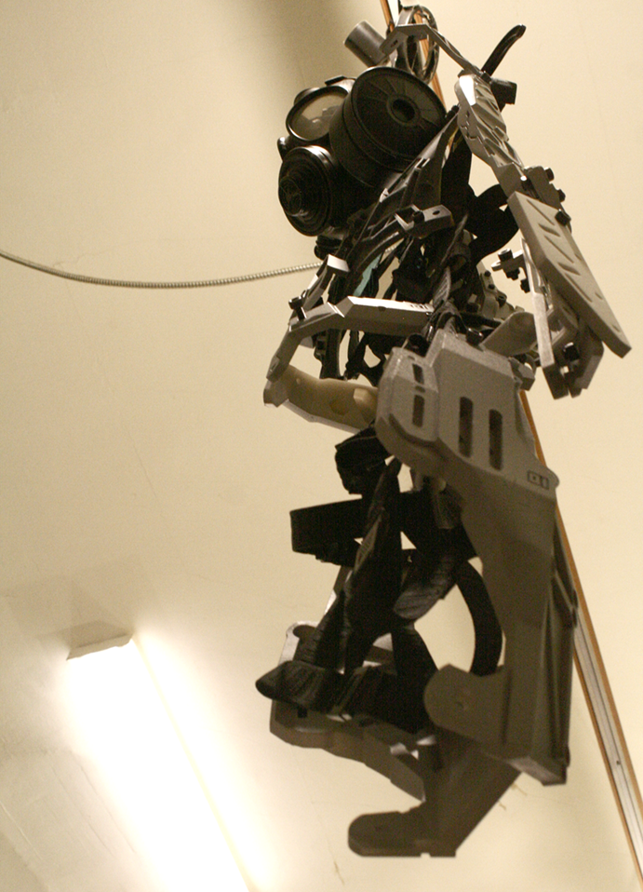
build/hang06.png
