01binary/elysium-max-exoskeleton/build/harness01.png

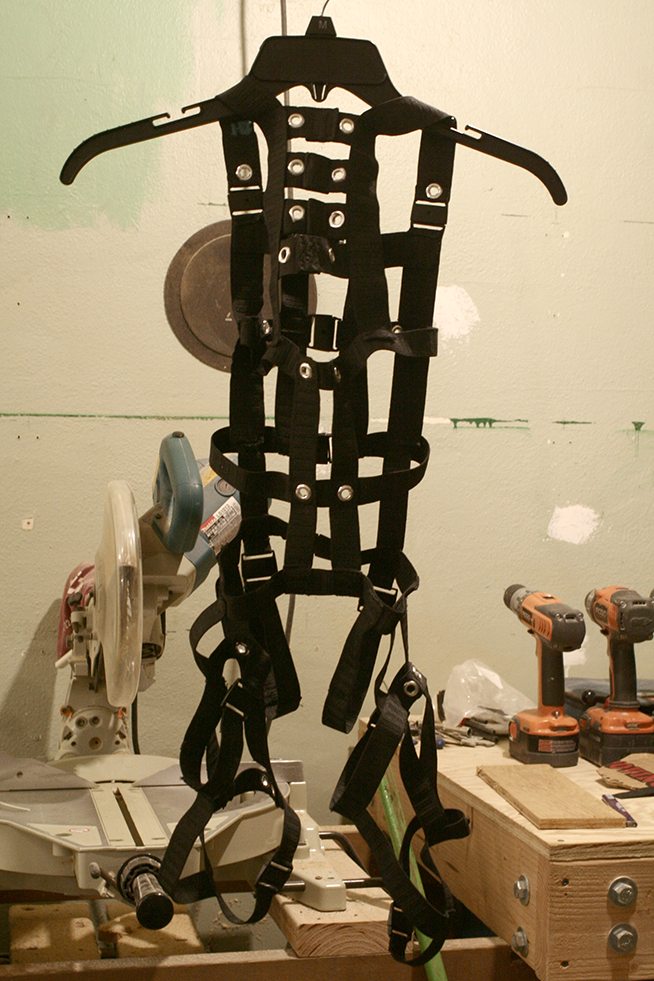
build/harness01.png
