01binary/elysium-max-exoskeleton/build/harness02.png

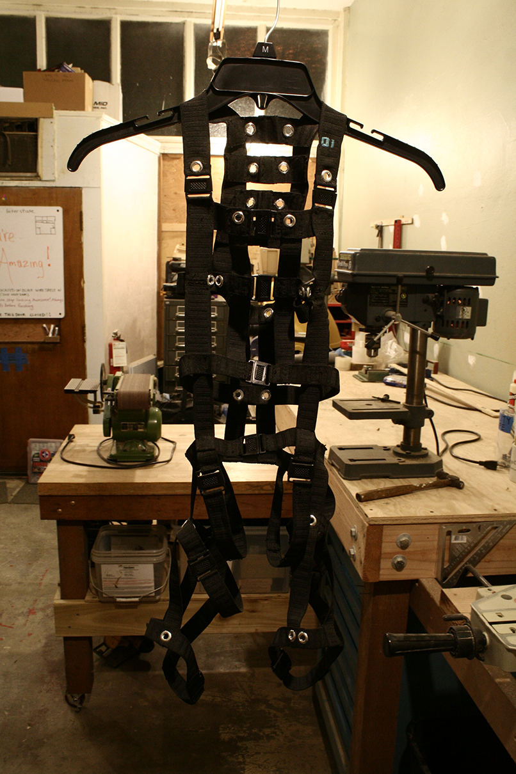
build/harness02.png
