01binary/elysium-max-exoskeleton/build/hip assembly-inventor.png

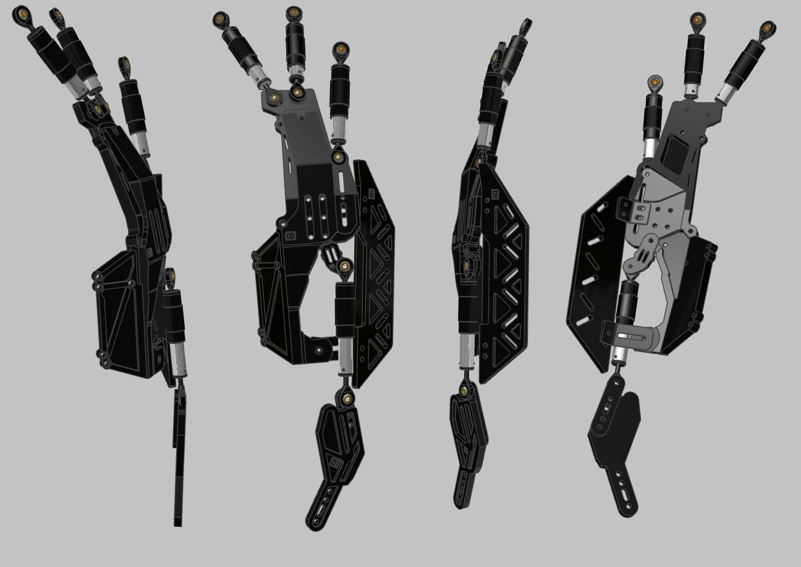
build/hip assembly-inventor.png
