01binary/elysium-max-exoskeleton/build/inventornew01.PNG

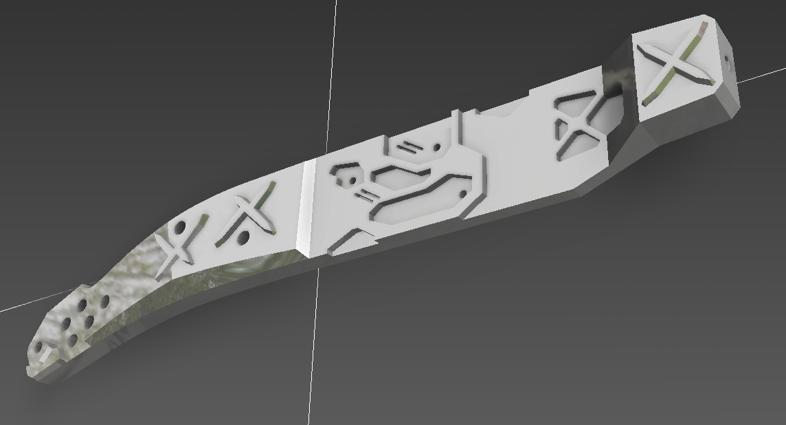
build/inventornew01.PNG
