01binary/elysium-max-exoskeleton/build/inventornew02.PNG

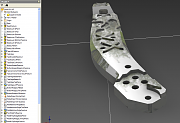
build/inventornew02.PNG
