01binary/elysium-max-exoskeleton/build/karm06.png

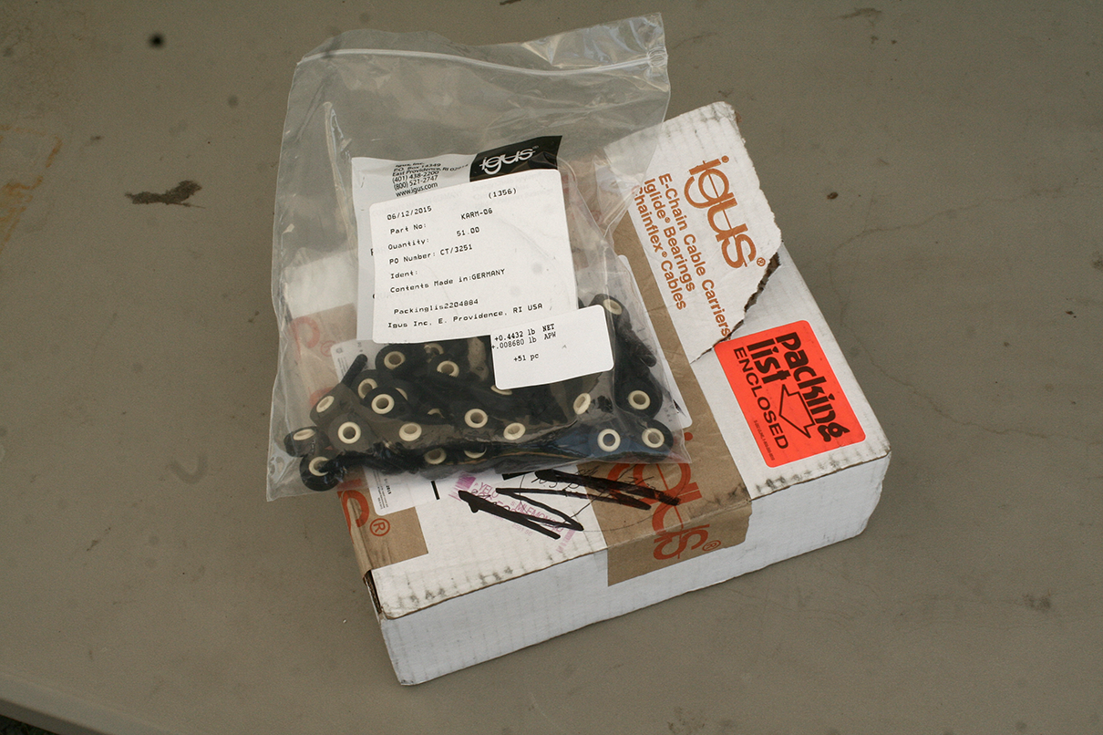
build/karm06.png
