01binary/elysium-max-exoskeleton/build/layout00.jpg

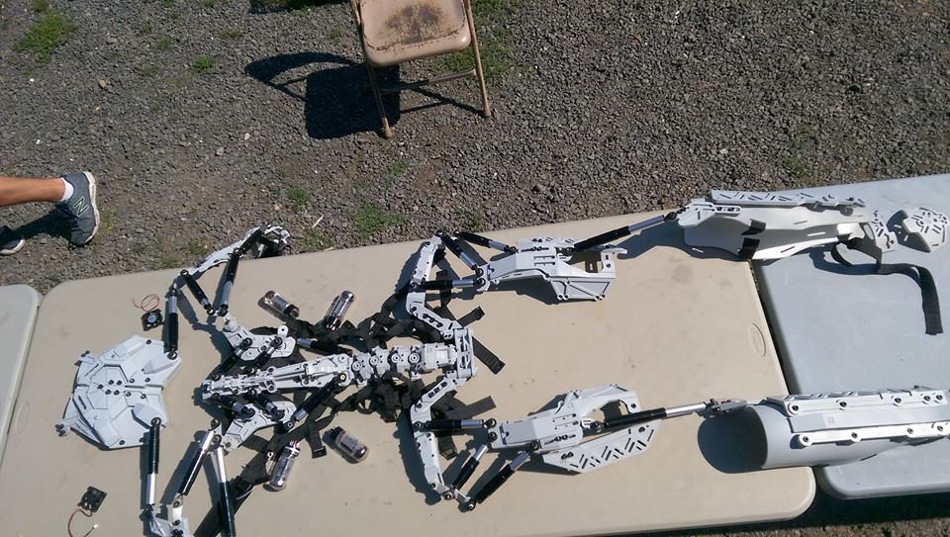
build/layout00.jpg
