01binary/elysium-max-exoskeleton/build/layout02.jpg

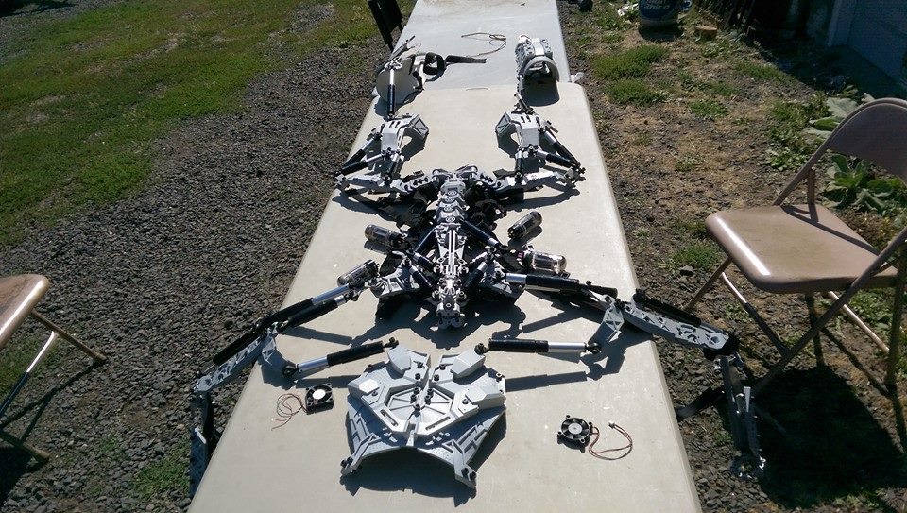
build/layout02.jpg
