01binary/elysium-max-exoskeleton/build/layout03.jpg

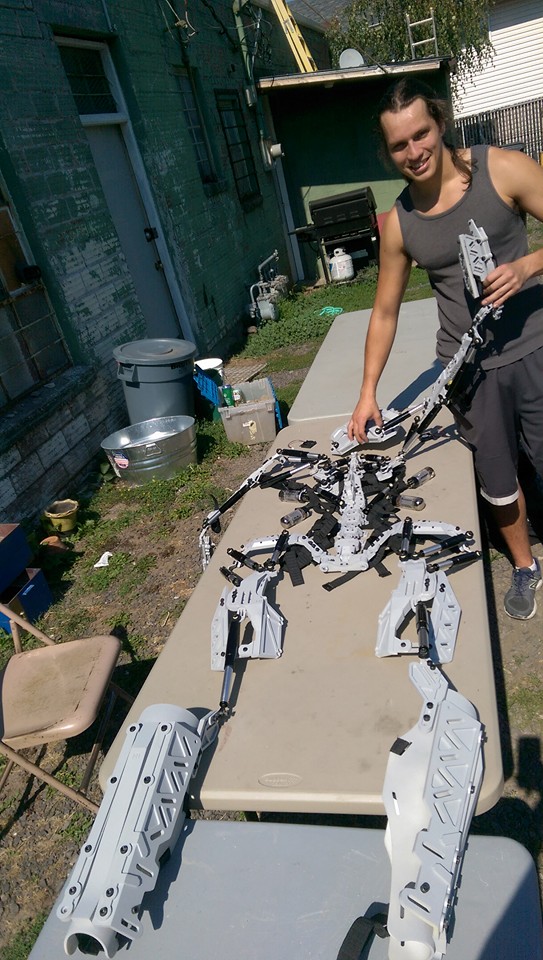
build/layout03.jpg
