01binary/elysium-max-exoskeleton/build/layout04.jpg

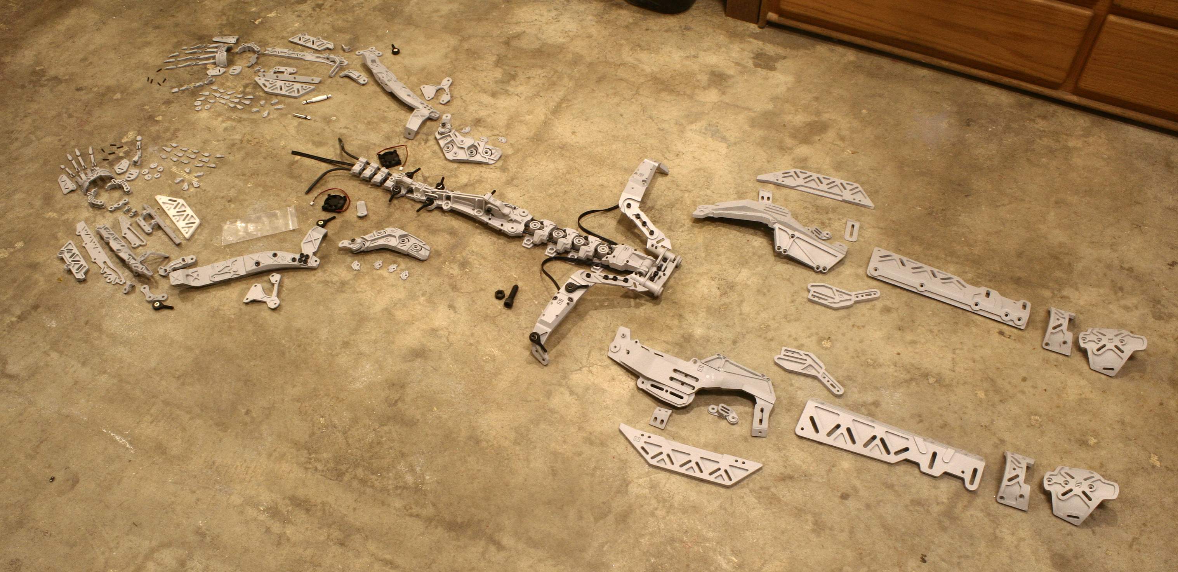
build/layout04.jpg
