01binary/elysium-max-exoskeleton/build/layout05.jpg

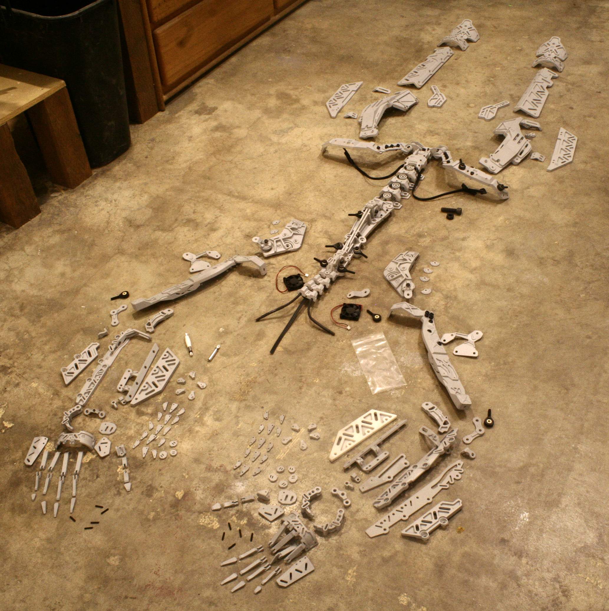
build/layout05.jpg
