01binary/elysium-max-exoskeleton/build/mounted01.JPG

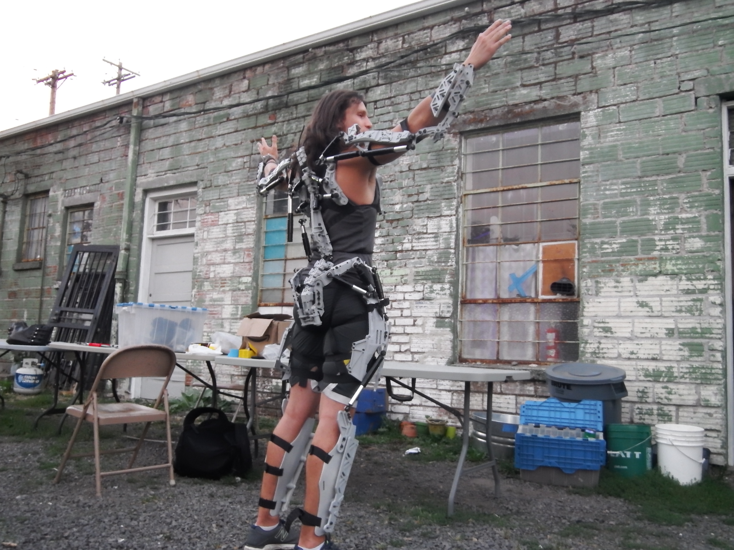
build/mounted01.JPG
