01binary/elysium-max-exoskeleton/build/mounted02.JPG

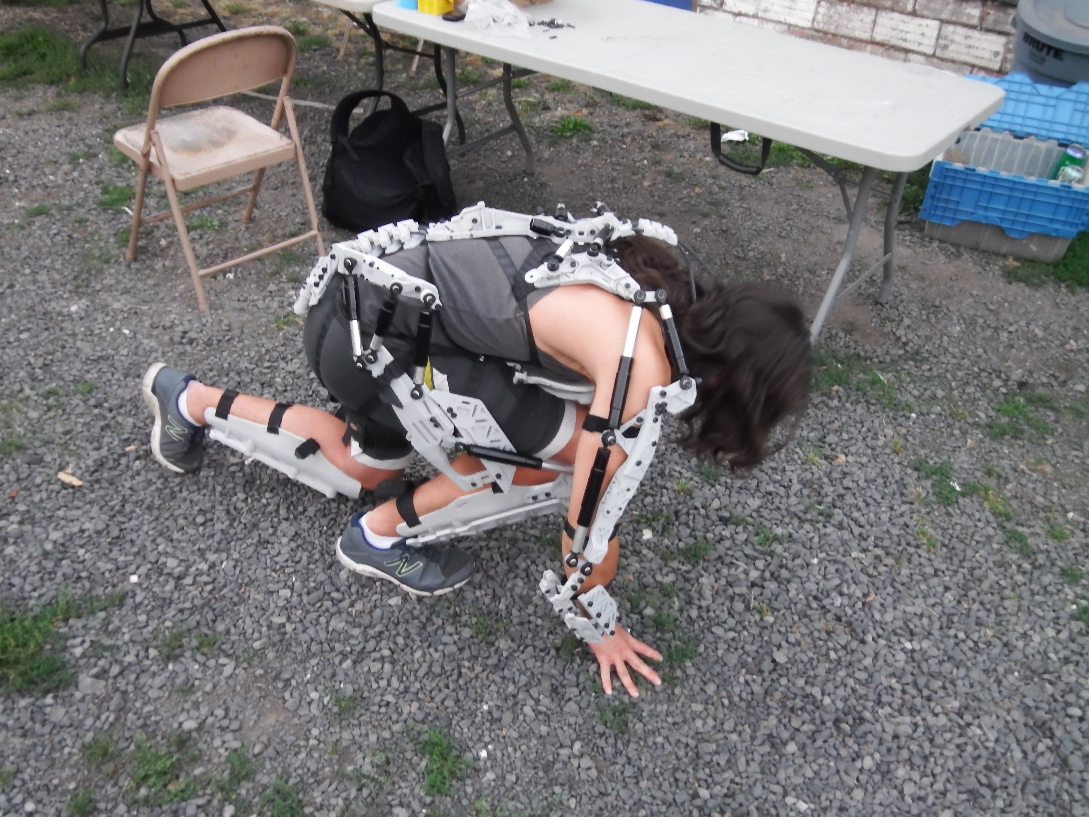
build/mounted02.JPG
