01binary/elysium-max-exoskeleton/build/piston-making01.png

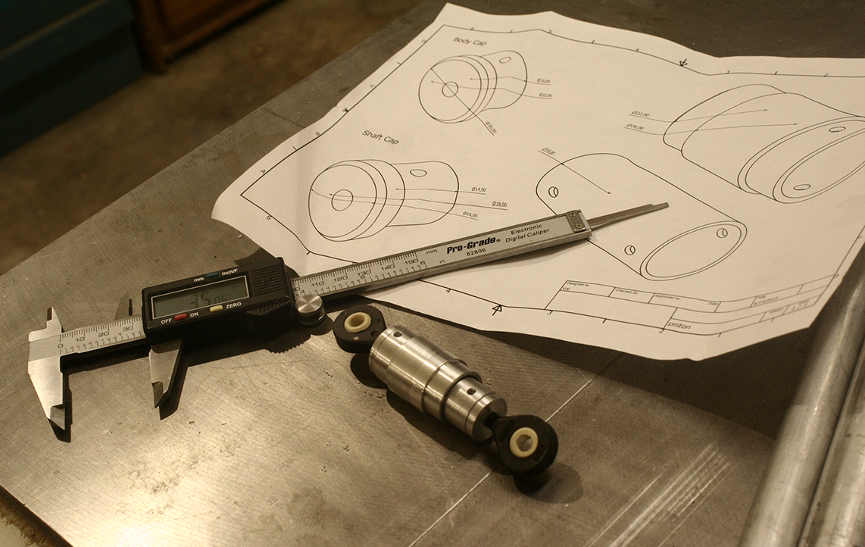
build/piston-making01.png
