01binary/elysium-max-exoskeleton/build/piston-making02.png

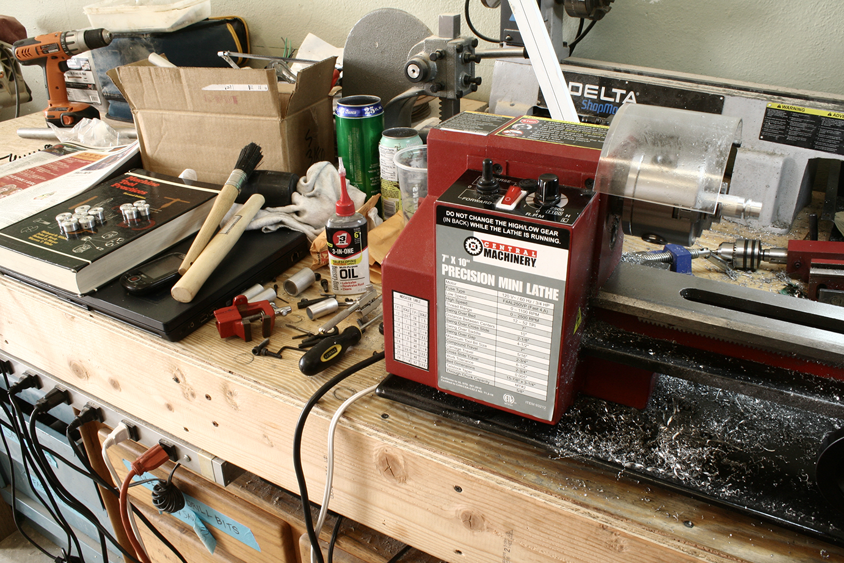
build/piston-making02.png
