01binary/elysium-max-exoskeleton/build/piston-making03.png

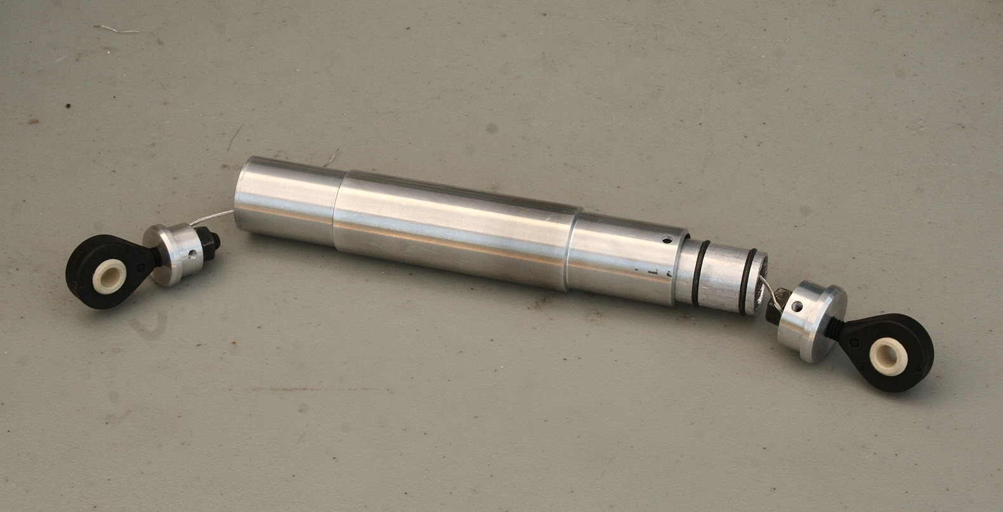
build/piston-making03.png
