01binary/elysium-max-exoskeleton/build/piston-making04.png

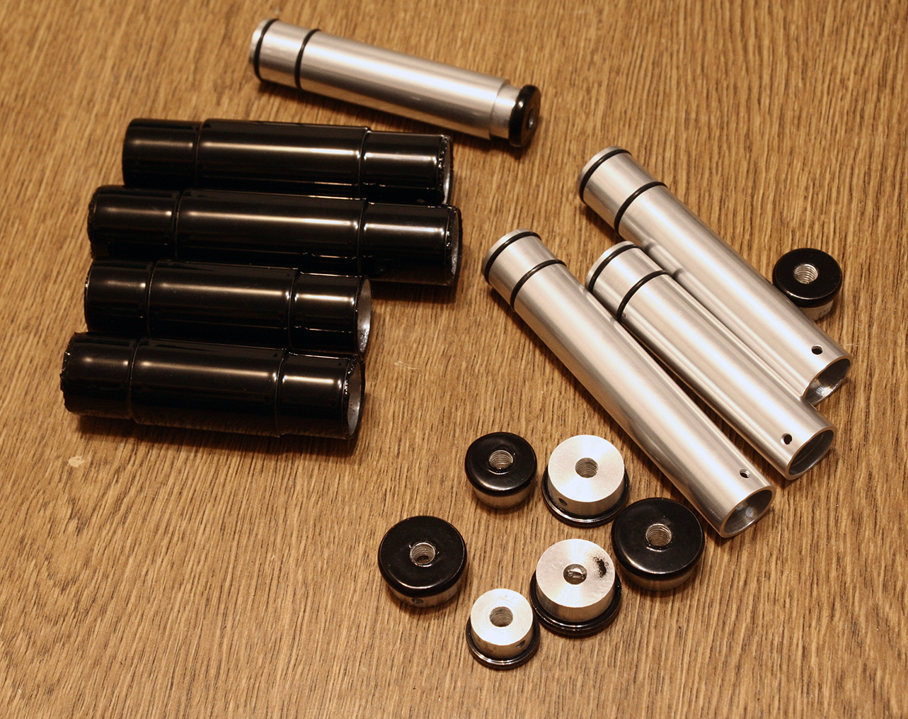
build/piston-making04.png
