01binary/elysium-max-exoskeleton/build/pistons01.png

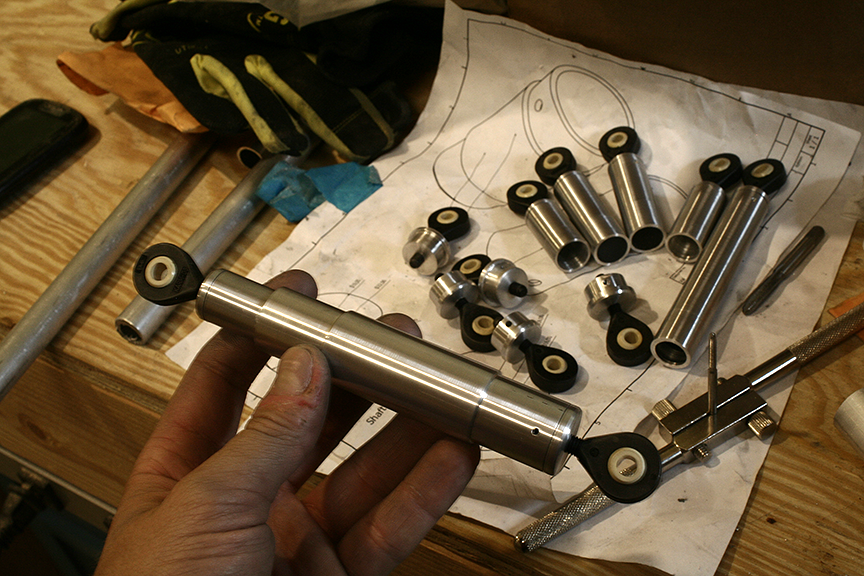
build/pistons01.png
