01binary/elysium-max-exoskeleton/build/pistons02.png

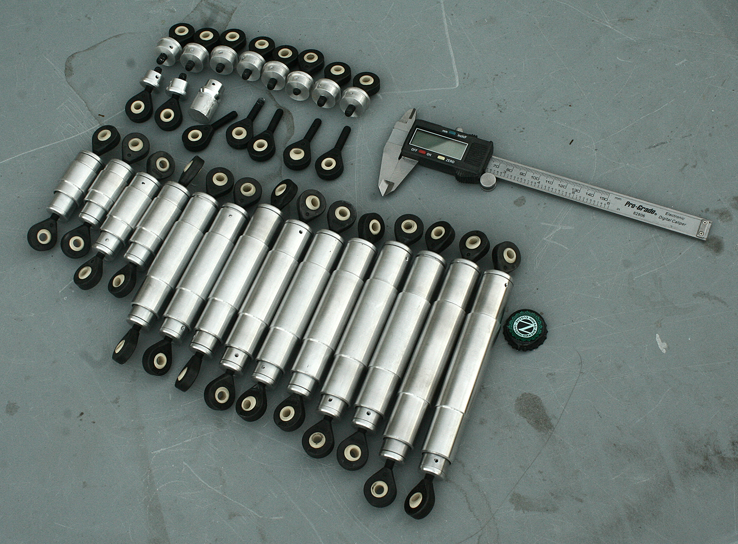
build/pistons02.png
