01binary/elysium-max-exoskeleton/build/pistons03.png

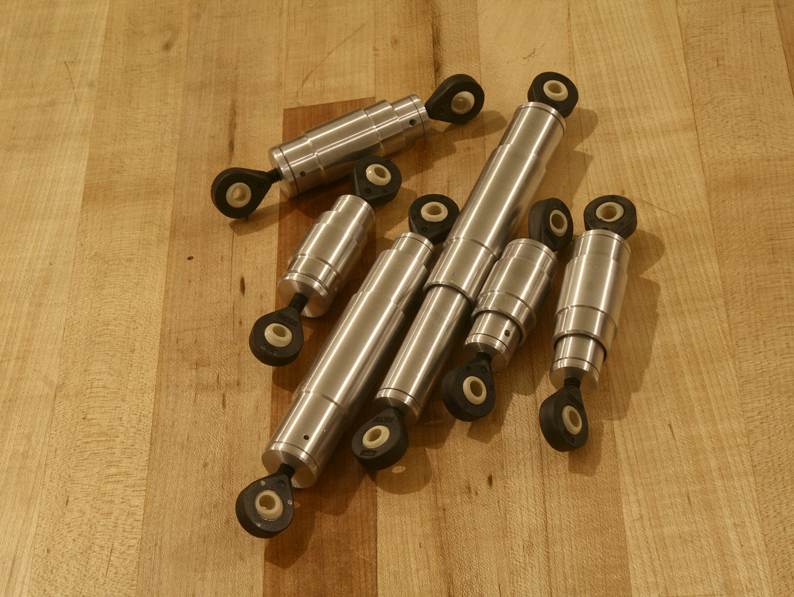
build/pistons03.png
