01binary/elysium-max-exoskeleton/build/pistons04.png

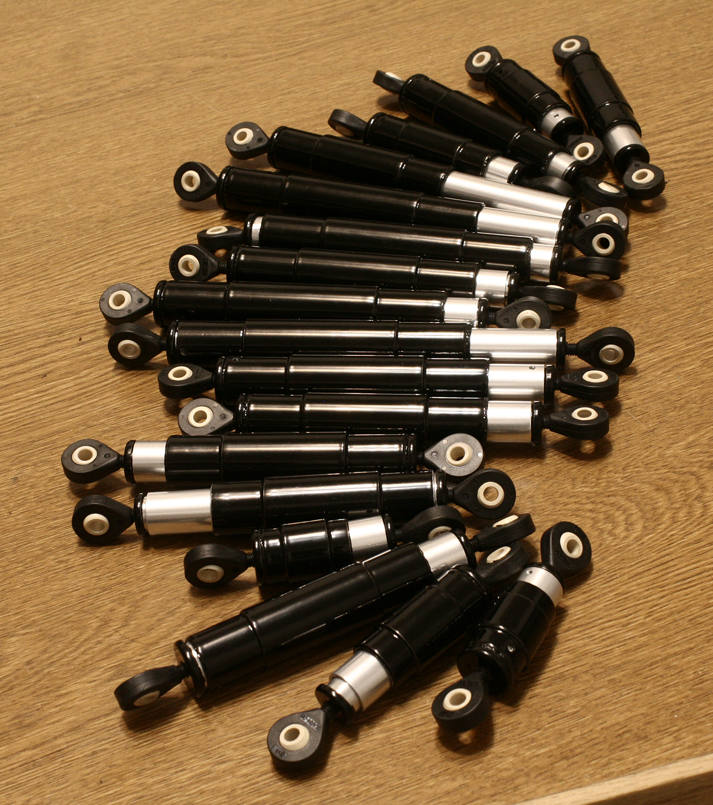
build/pistons04.png
