01binary/elysium-max-exoskeleton/build/priming.jpg

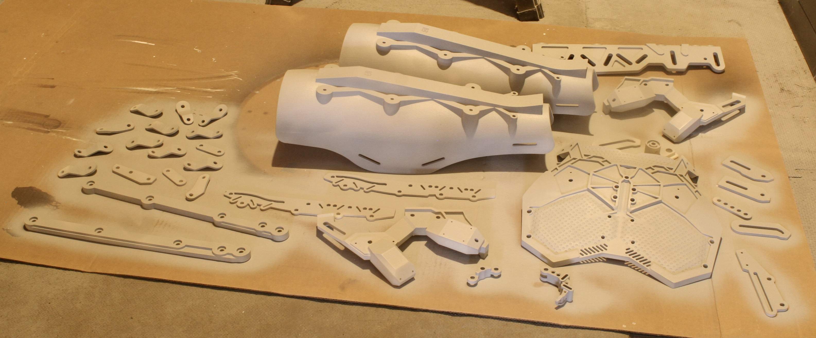
build/priming.jpg
