01binary/elysium-max-exoskeleton/build/shin-1.png

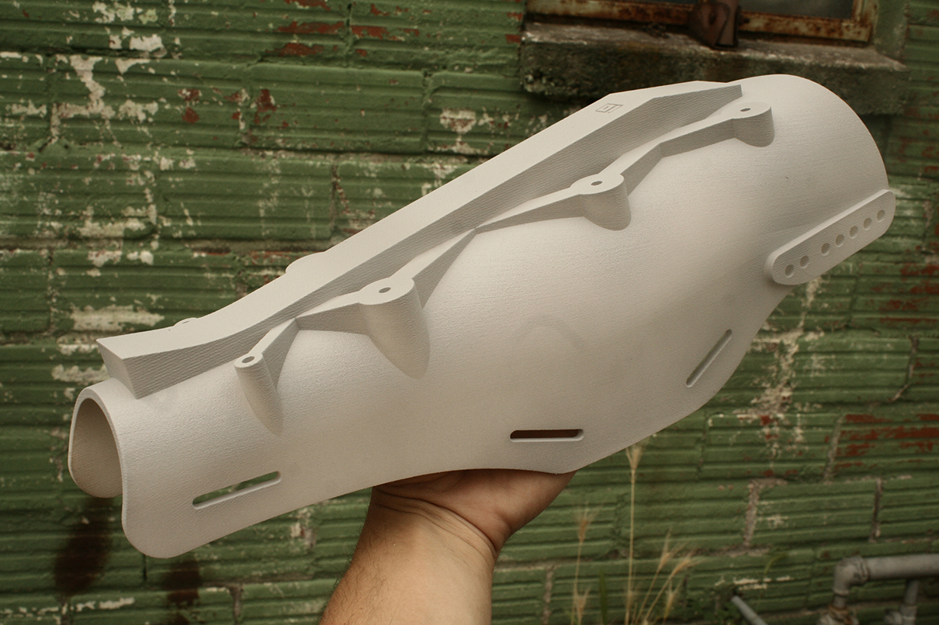
build/shin-1.png
