01binary/elysium-max-exoskeleton/build/shin-onbody.png

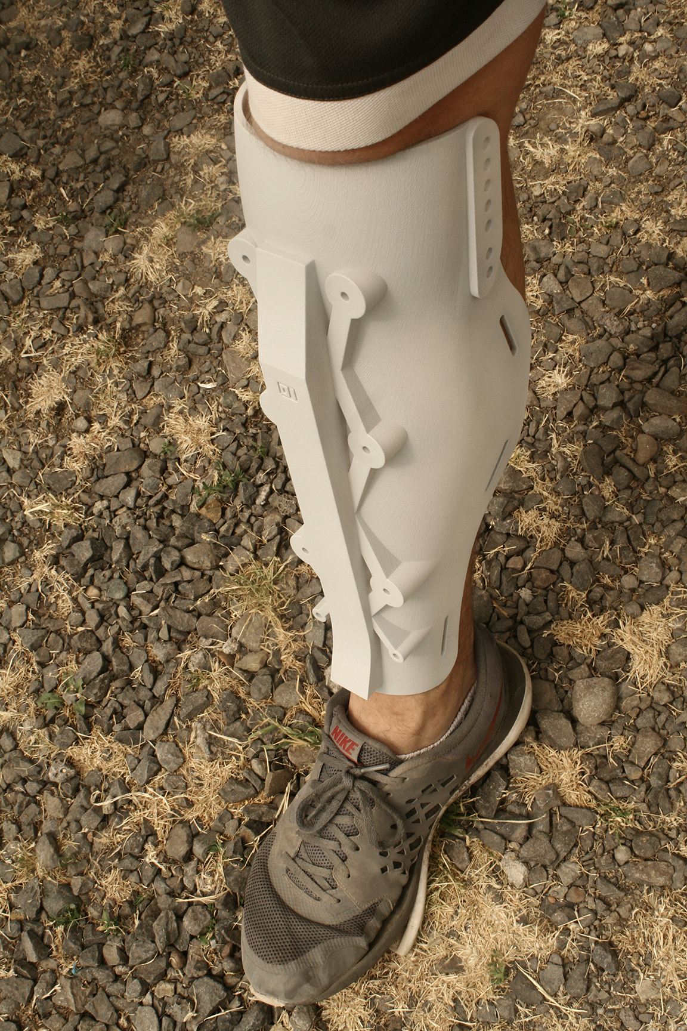
build/shin-onbody.png
