01binary/elysium-max-exoskeleton/build/shoulder assembly done.png

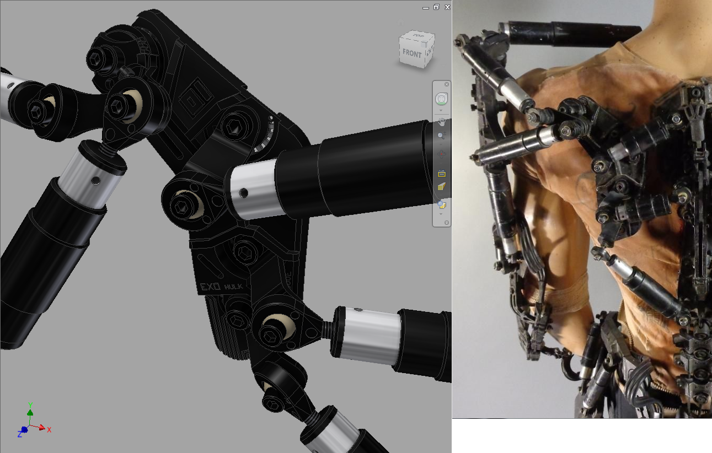
build/shoulder assembly done.png
