01binary/elysium-max-exoskeleton/build/shoulder assembly one more.png

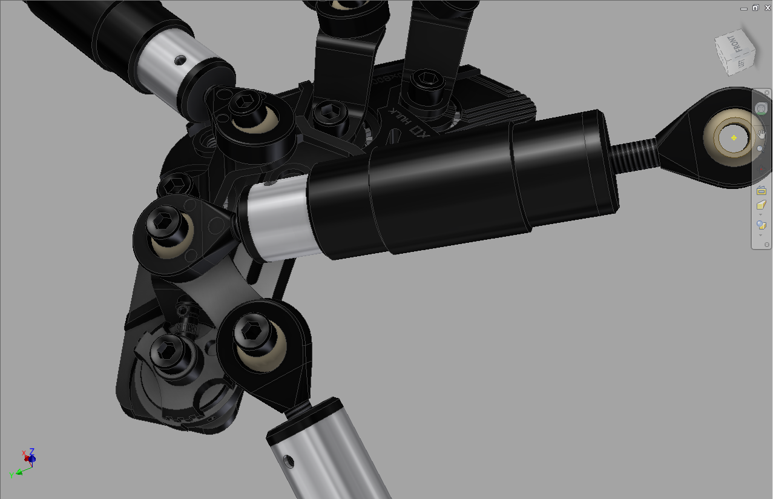
build/shoulder assembly one more.png
