01binary/elysium-max-exoskeleton/build/spine01.png

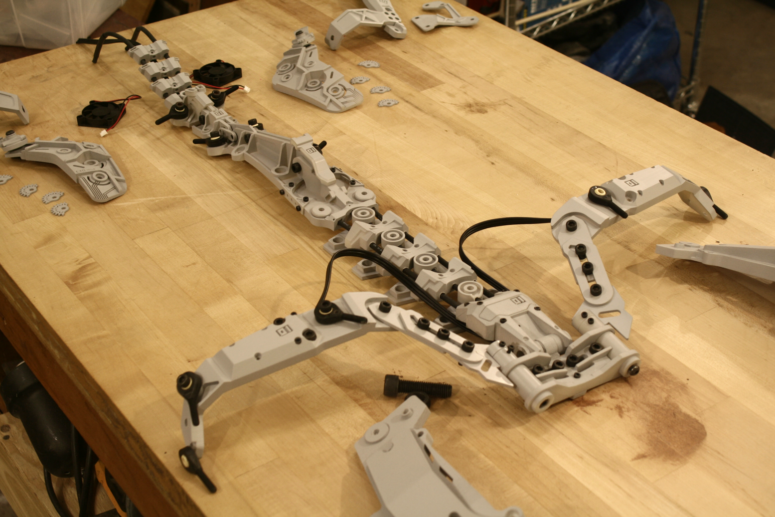
build/spine01.png
