01binary/elysium-max-exoskeleton/build/spine03.png

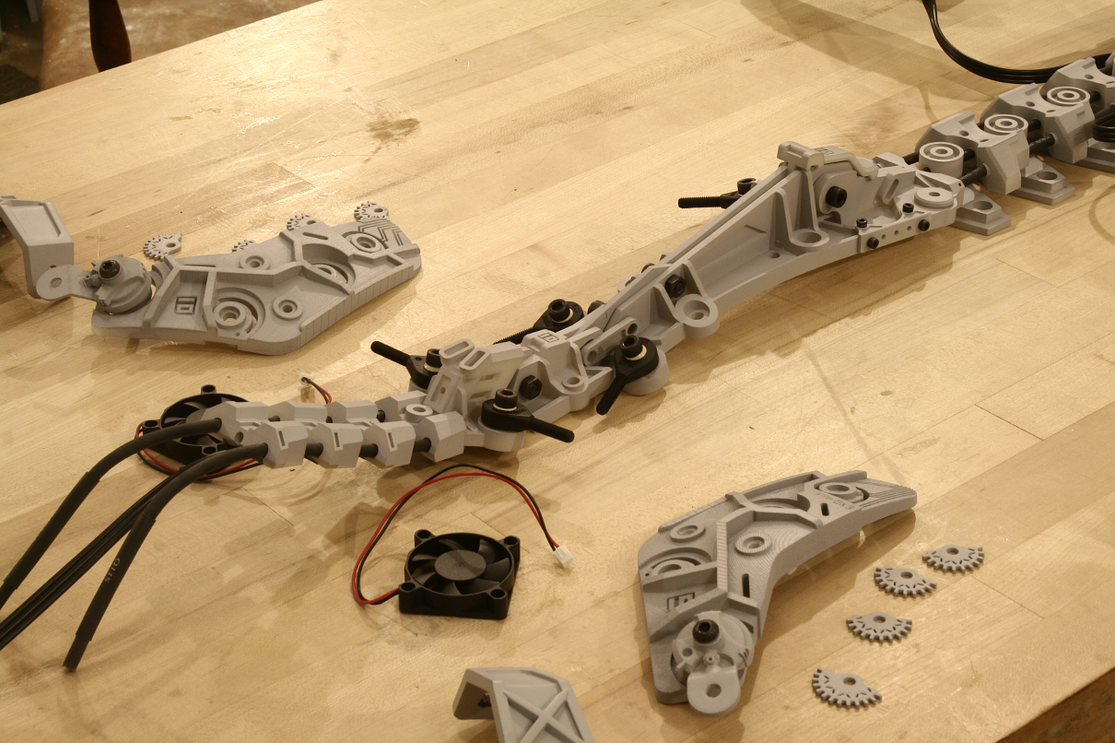
build/spine03.png
