01binary/elysium-max-exoskeleton/build/spine04.png

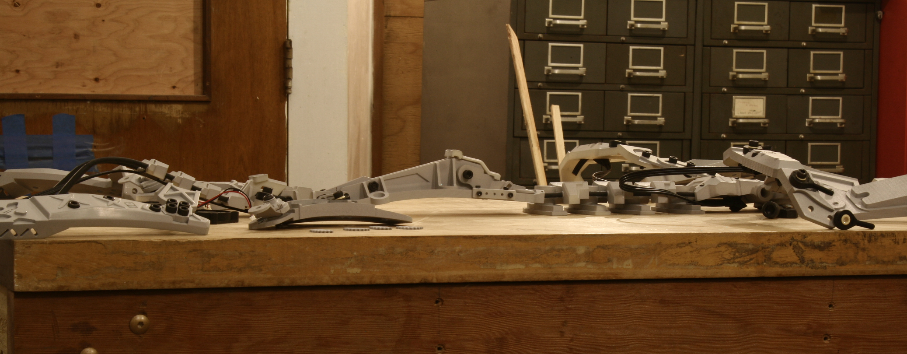
build/spine04.png
