01binary/elysium-max-exoskeleton/build/spine-inventor-done.png

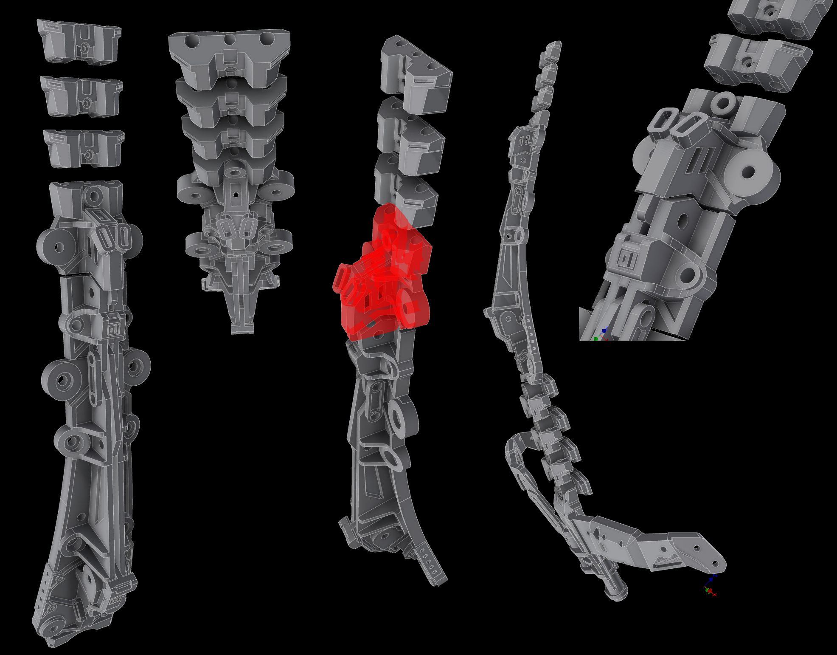
build/spine-inventor-done.png
