01binary/elysium-max-exoskeleton/build/spine-upper01.png

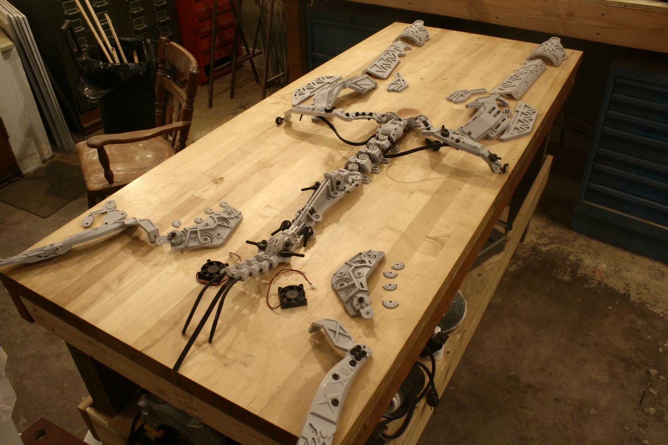
build/spine-upper01.png
