01binary/elysium-max-exoskeleton/build/upperbody01.png

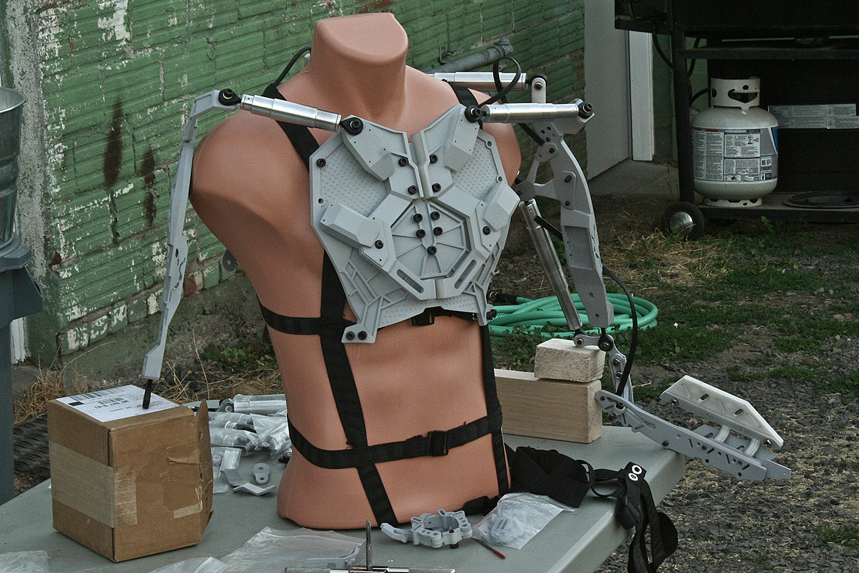
build/upperbody01.png
