01binary/elysium-max-exoskeleton/build/upperbody03.png

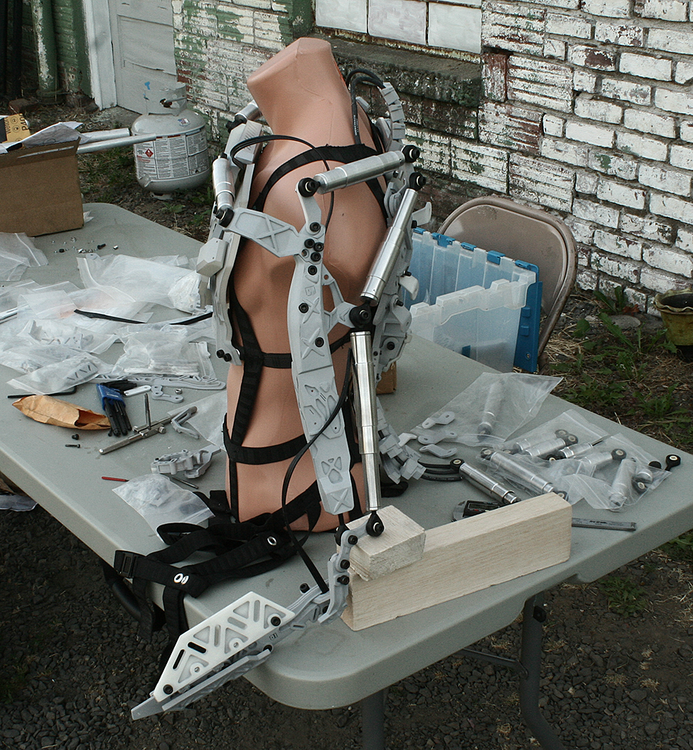
build/upperbody03.png
