01binary/elysium-max-exoskeleton/instructions/images/chest/chest-view-back.png

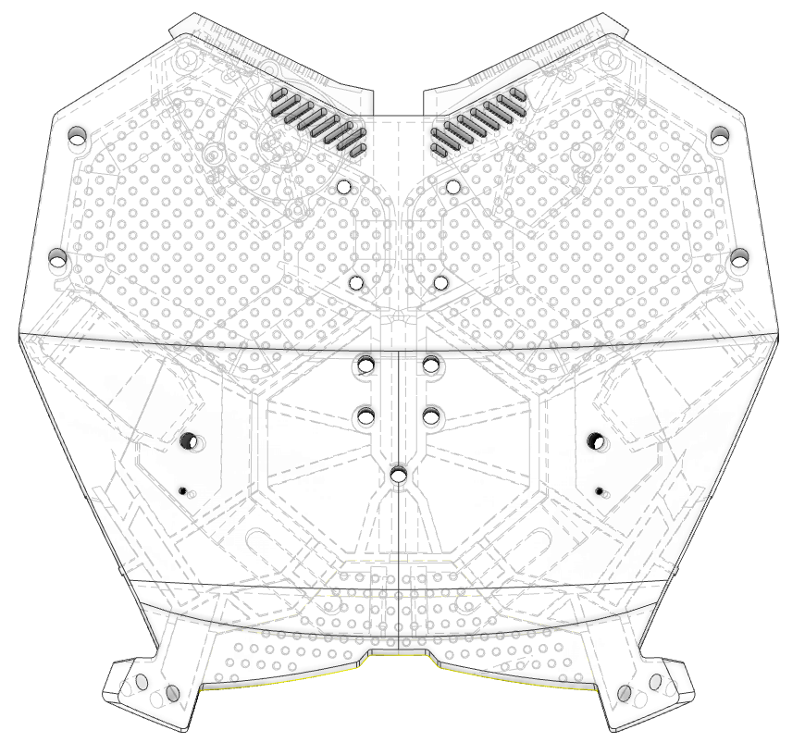
instructions/images/chest/chest-view-back.png
