01binary/elysium-max-exoskeleton/instructions/images/chest/chest-view-corner.png

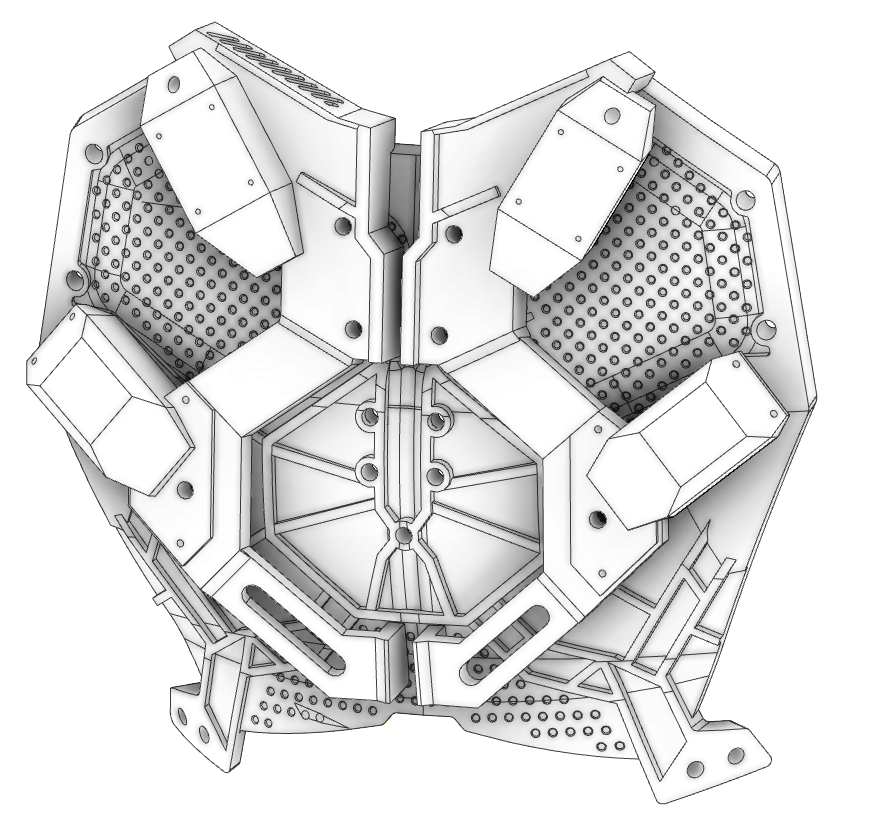
instructions/images/chest/chest-view-corner.png
