01binary/elysium-max-exoskeleton/instructions/images/chest/chest-view-front.png

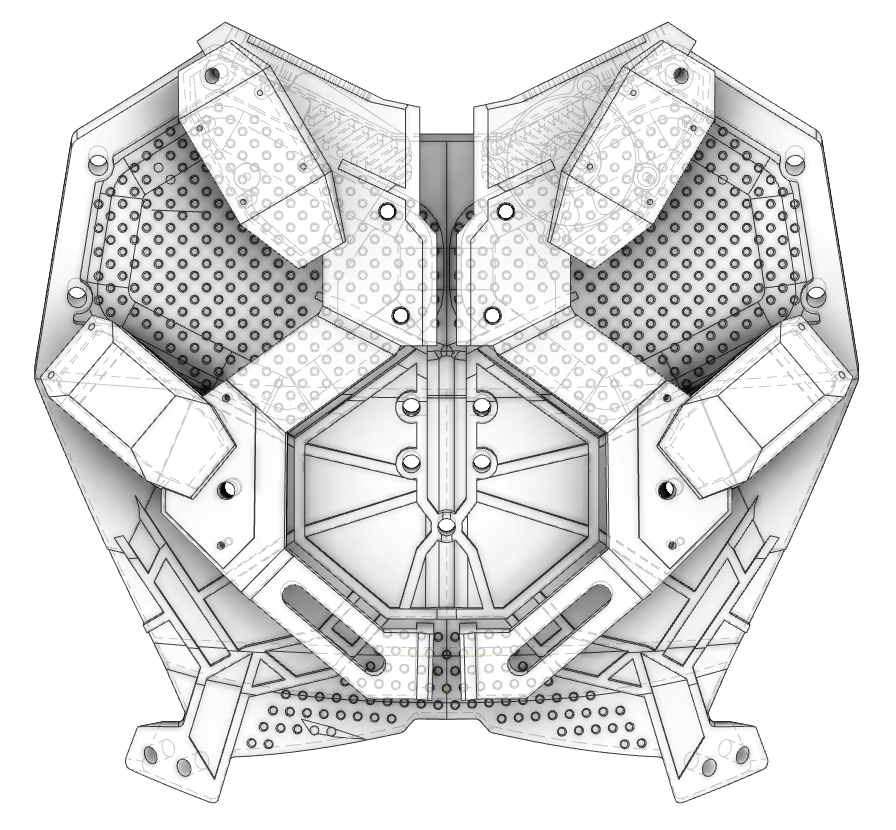
instructions/images/chest/chest-view-front.png
