01binary/elysium-max-exoskeleton/instructions/images/chest/chest-view-side.png

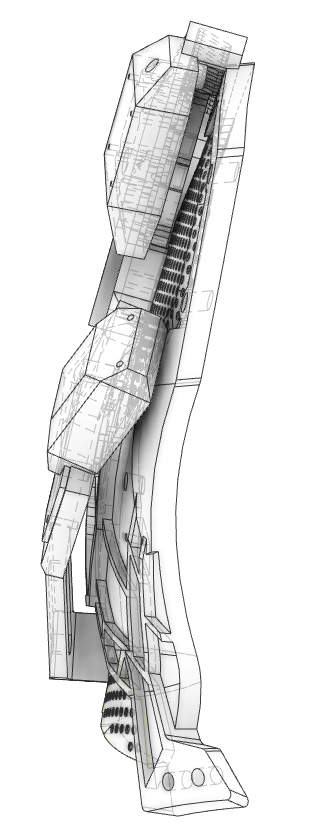
instructions/images/chest/chest-view-side.png
