01binary/elysium-max-exoskeleton/instructions/images/chest/chest-view-top.png

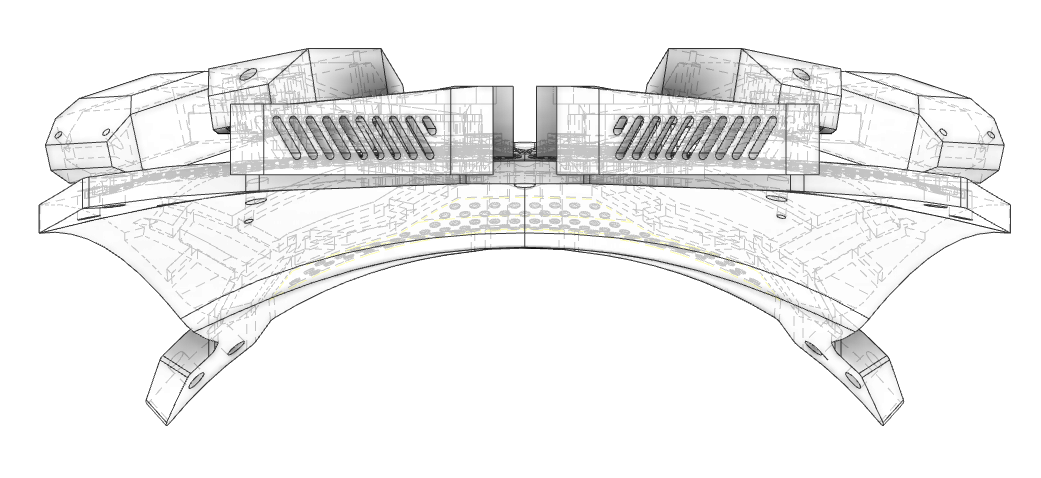
instructions/images/chest/chest-view-top.png
