01binary/elysium-max-exoskeleton/instructions/images/chest/chest.png

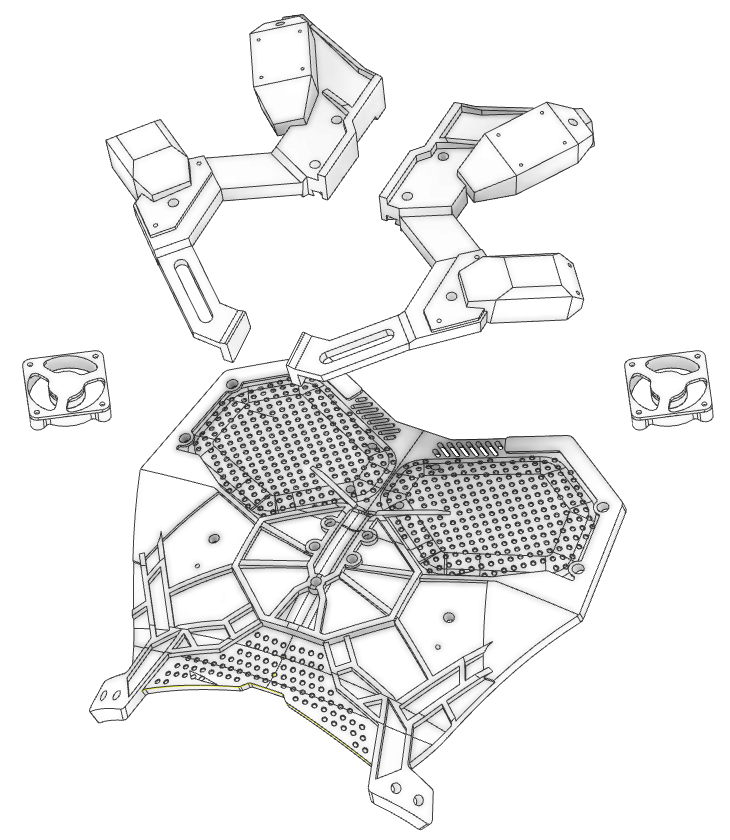
instructions/images/chest/chest.png
