01binary/elysium-max-exoskeleton/instructions/images/exoskeleton-view-back.png

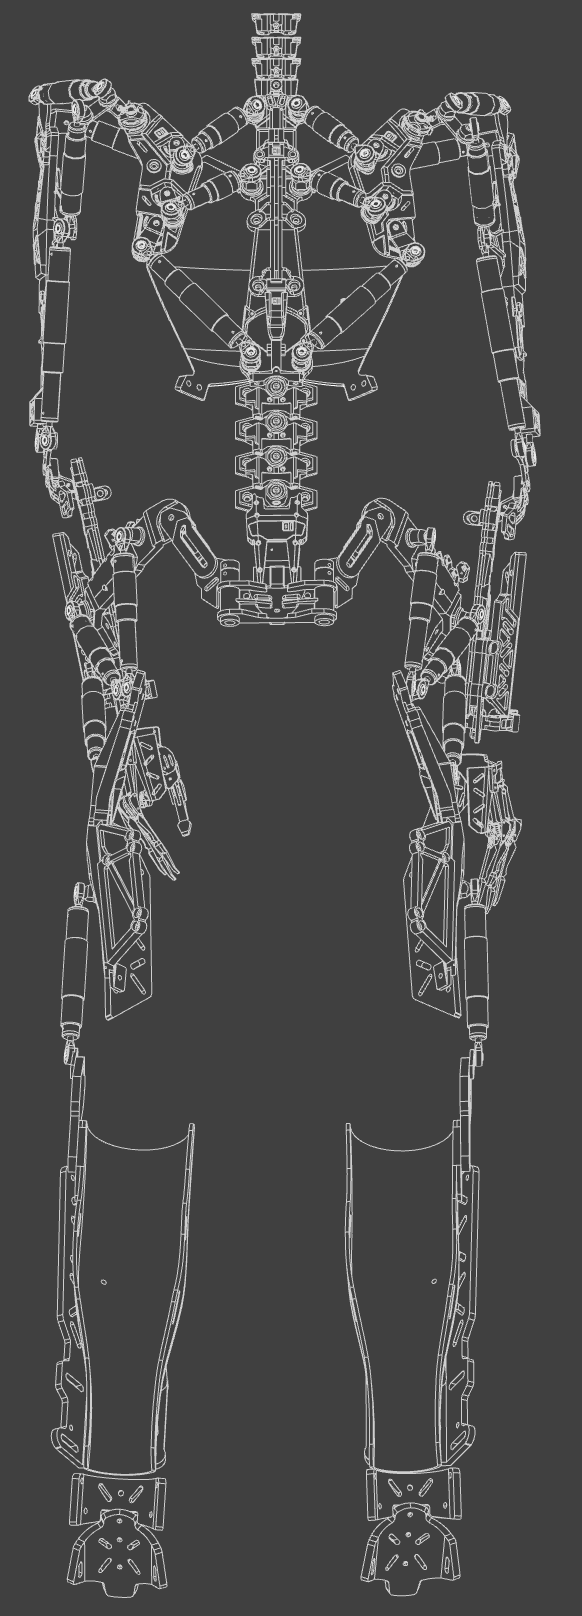
instructions/images/exoskeleton-view-back.png
