01binary/elysium-max-exoskeleton/instructions/images/exoskeleton-view-bottom.png

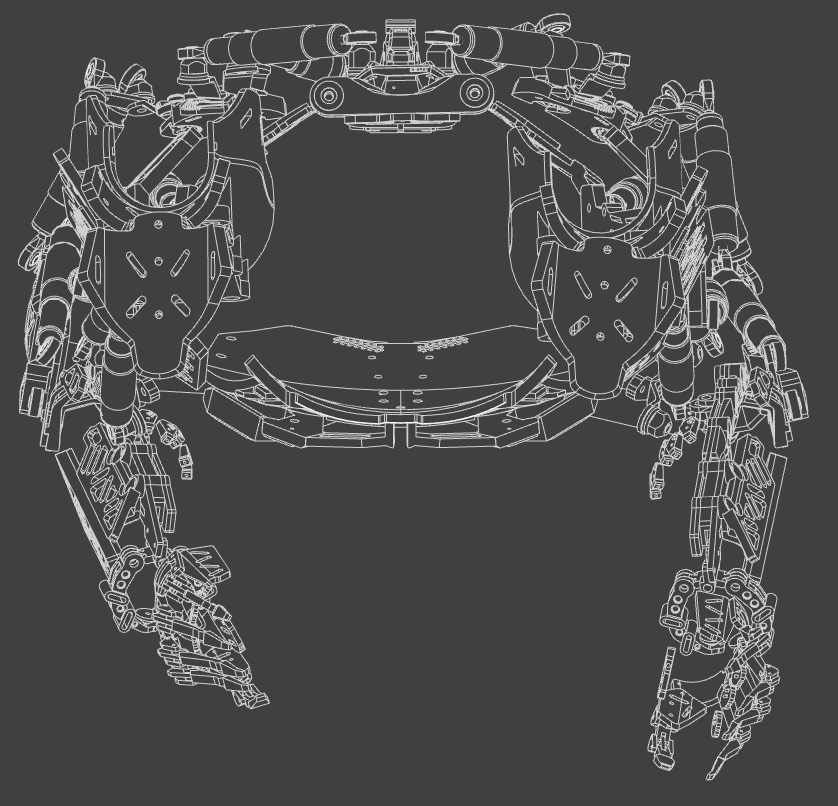
instructions/images/exoskeleton-view-bottom.png
