01binary/elysium-max-exoskeleton/instructions/images/exoskeleton-view-front.png

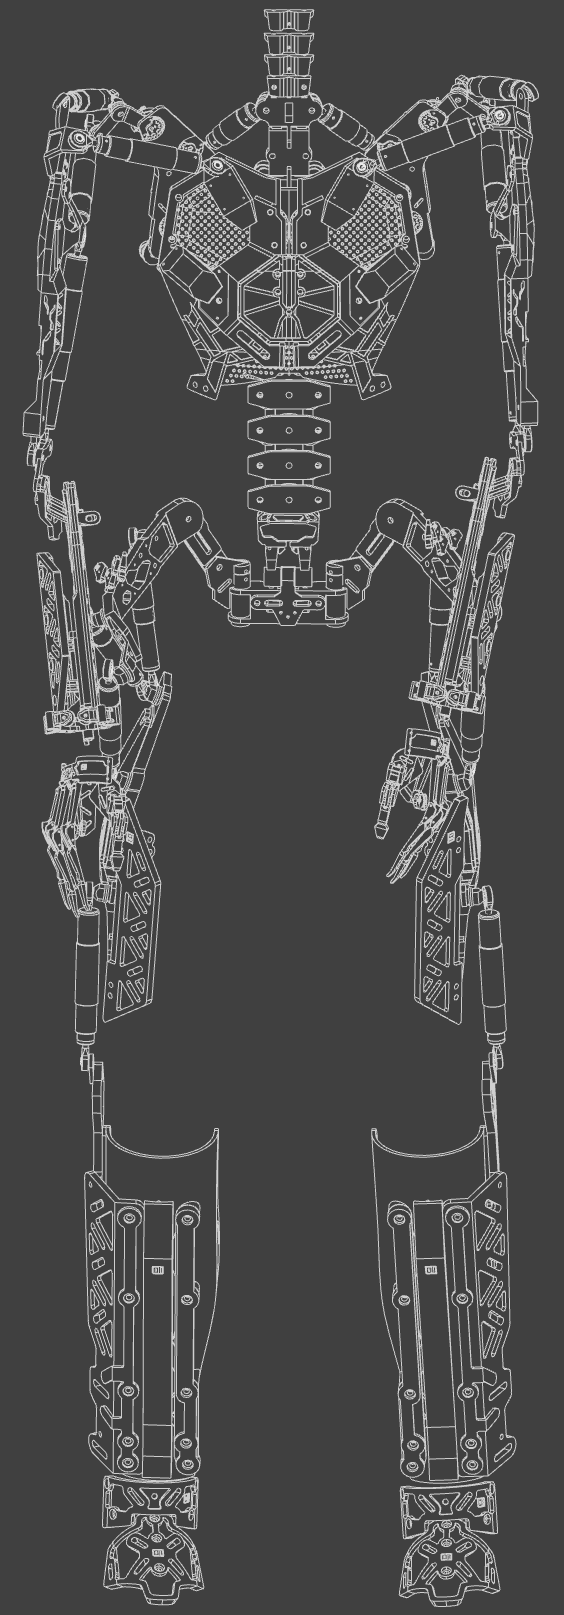
instructions/images/exoskeleton-view-front.png
