01binary/elysium-max-exoskeleton/instructions/images/exoskeleton-view-side.png

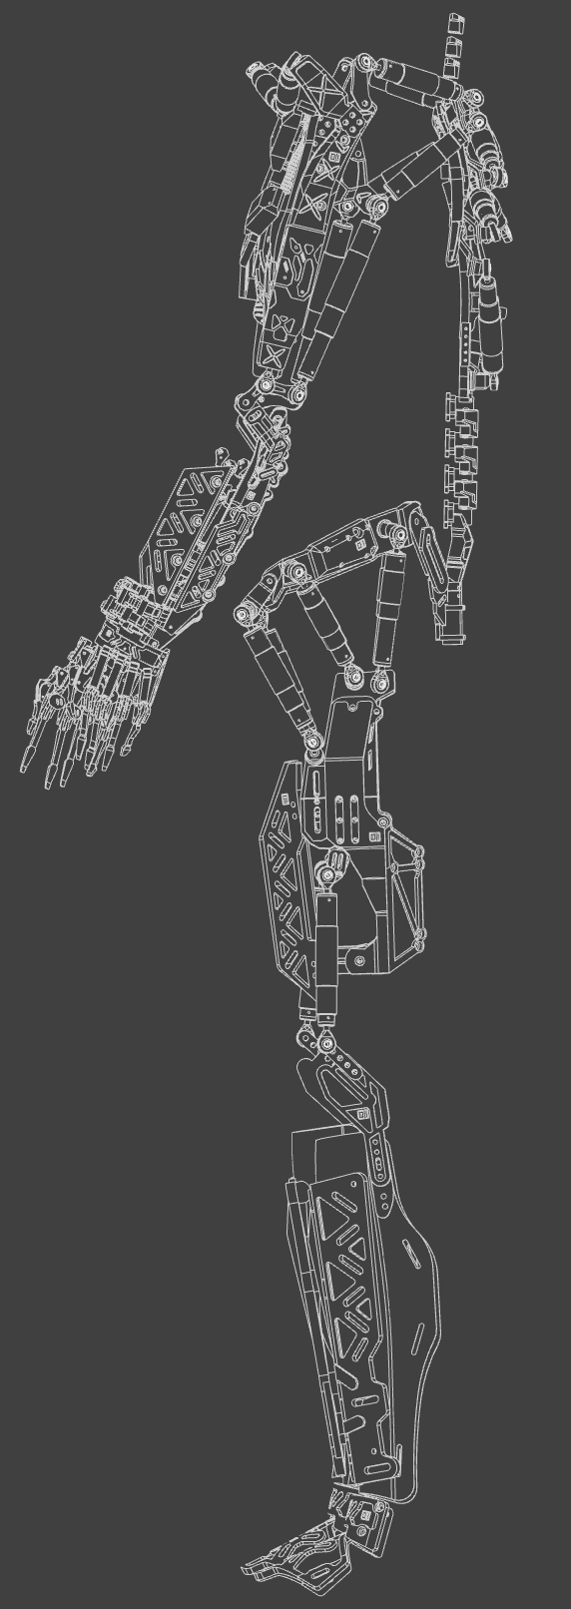
instructions/images/exoskeleton-view-side.png
