01binary/elysium-max-exoskeleton/instructions/images/exoskeleton-view-top.png

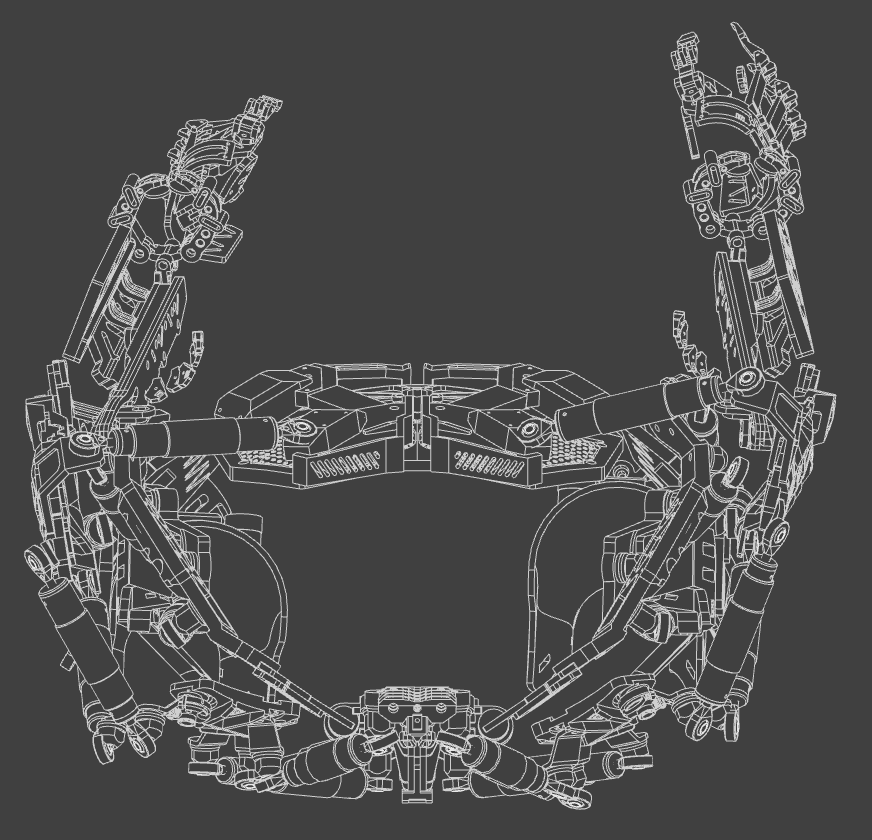
instructions/images/exoskeleton-view-top.png
