01binary/elysium-max-exoskeleton/instructions/images/exoskeleton-view.png

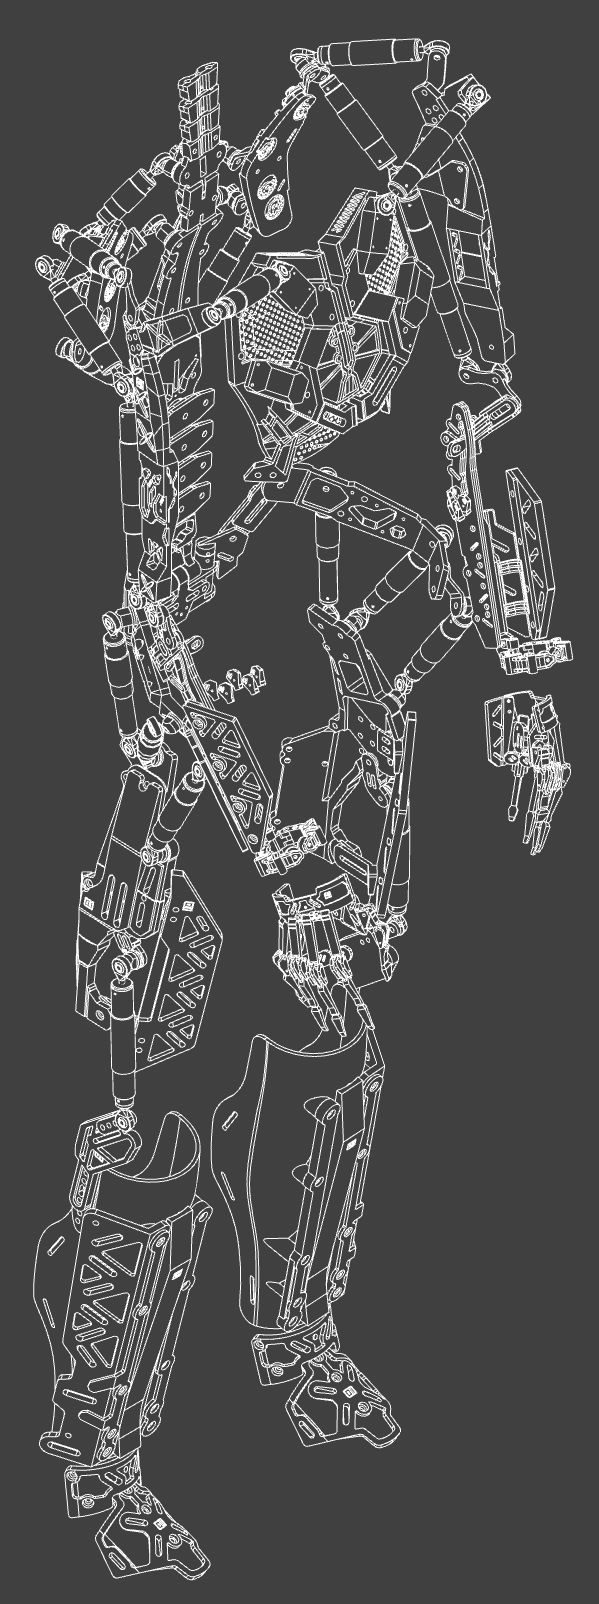
instructions/images/exoskeleton-view.png
