01binary/elysium-max-exoskeleton/instructions/images/fastener.png

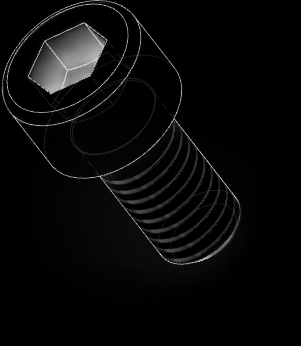
instructions/images/fastener.png
