01binary/elysium-max-exoskeleton/instructions/images/forearm/forearm-view-back.png

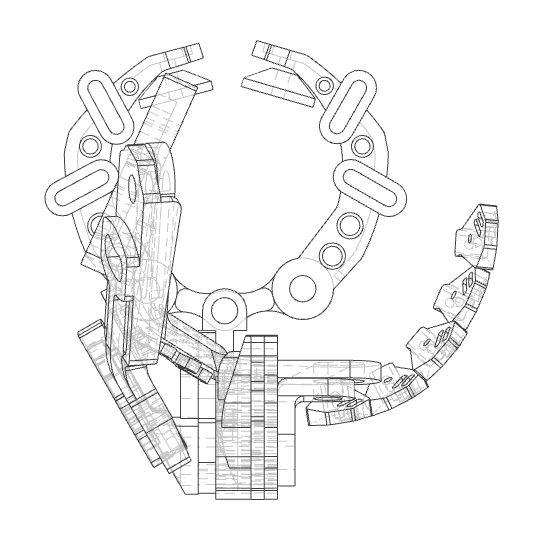
instructions/images/forearm/forearm-view-back.png
