01binary/elysium-max-exoskeleton/instructions/images/forearm/forearm-view-bottom.png

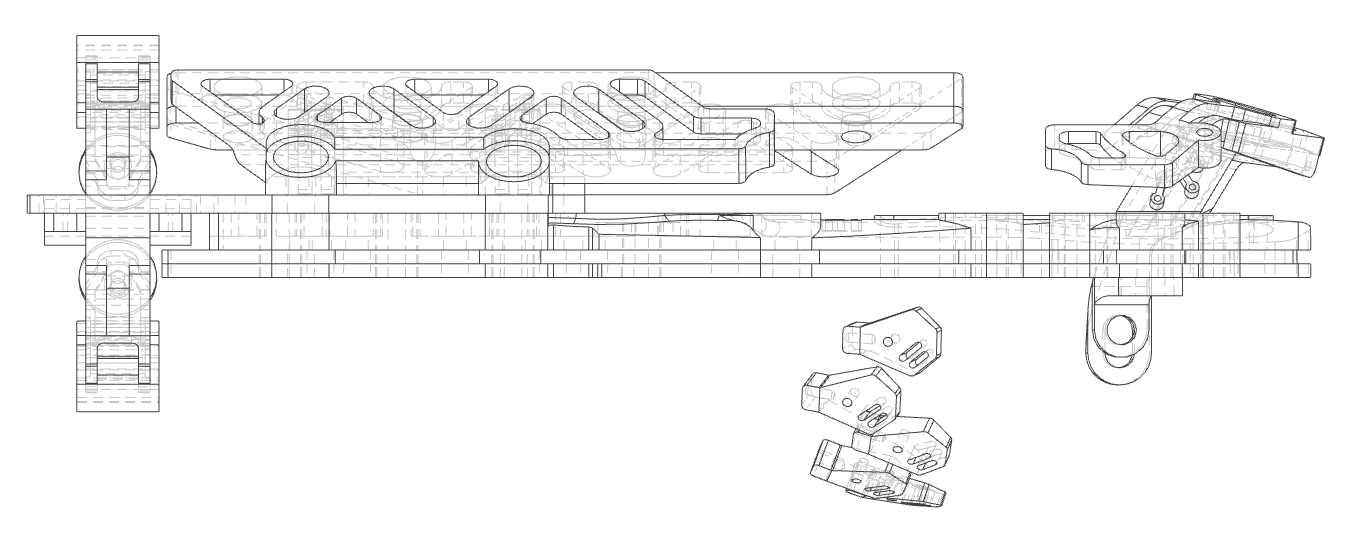
instructions/images/forearm/forearm-view-bottom.png
