01binary/elysium-max-exoskeleton/instructions/images/forearm/forearm-view-corner.png

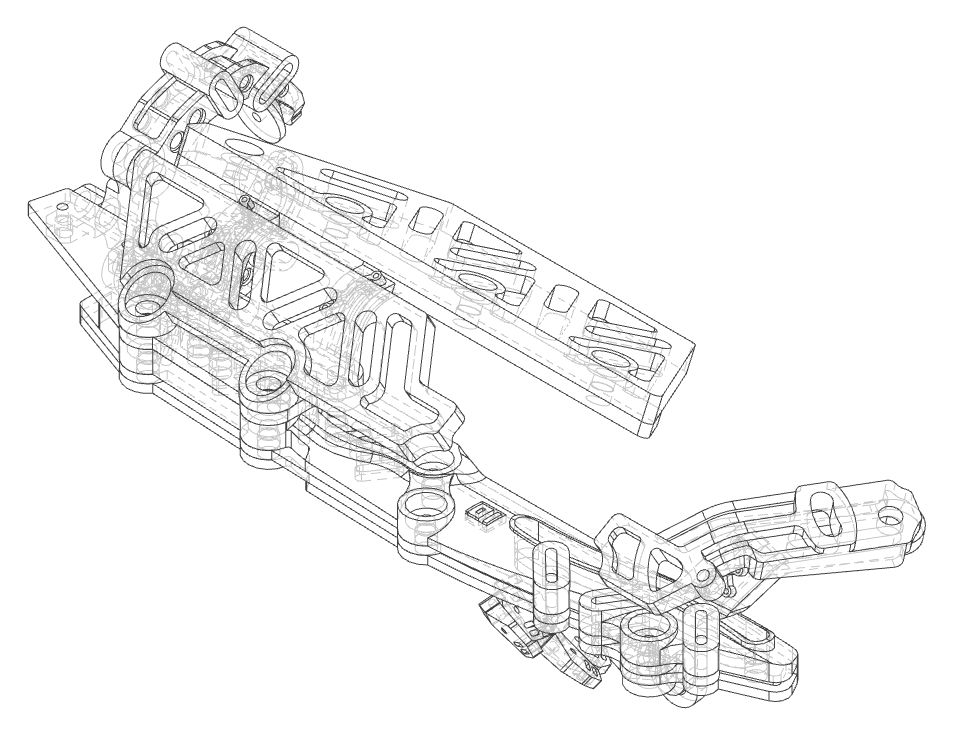
instructions/images/forearm/forearm-view-corner.png
