01binary/elysium-max-exoskeleton/instructions/images/forearm/forearm-view-right.png

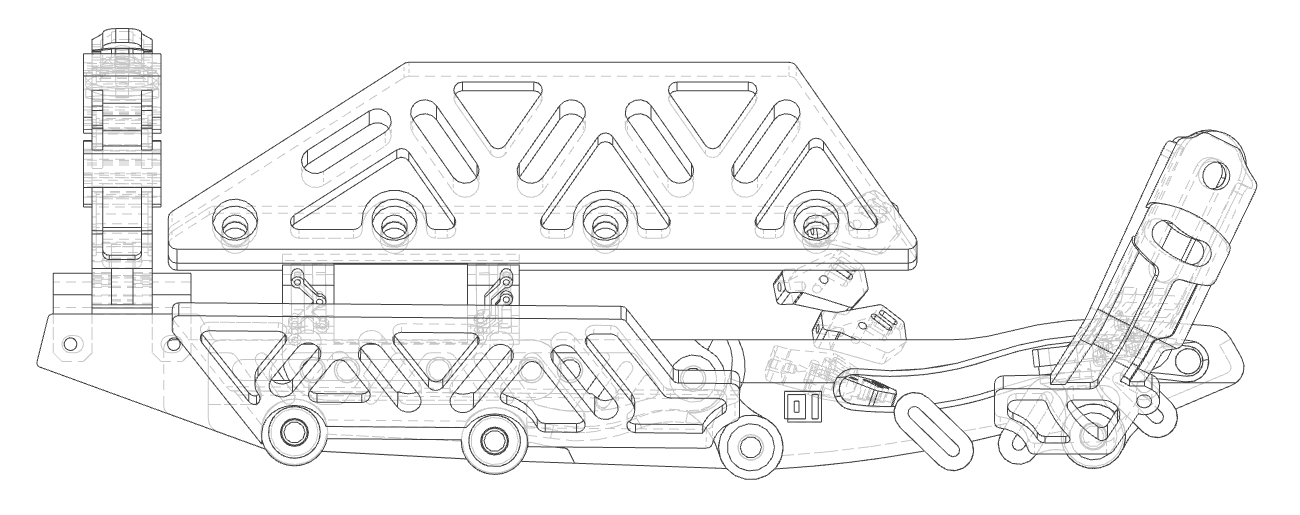
instructions/images/forearm/forearm-view-right.png
