01binary/elysium-max-exoskeleton/instructions/images/forearm/forearm-view-top.png

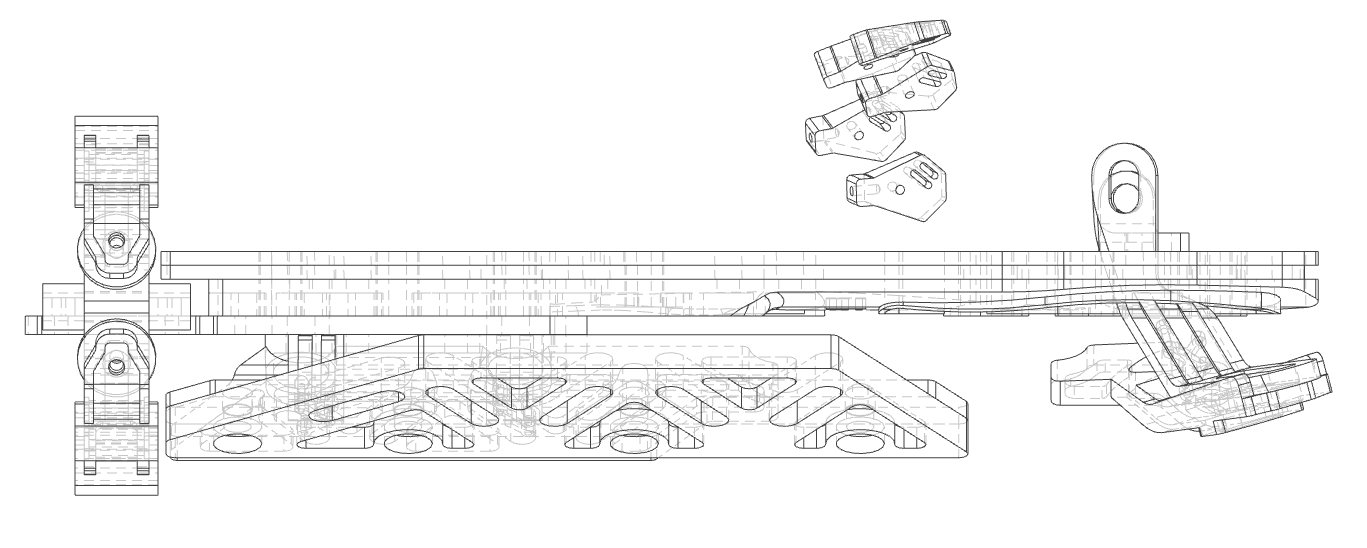
instructions/images/forearm/forearm-view-top.png
