01binary/elysium-max-exoskeleton/instructions/images/forearm/forearm.png

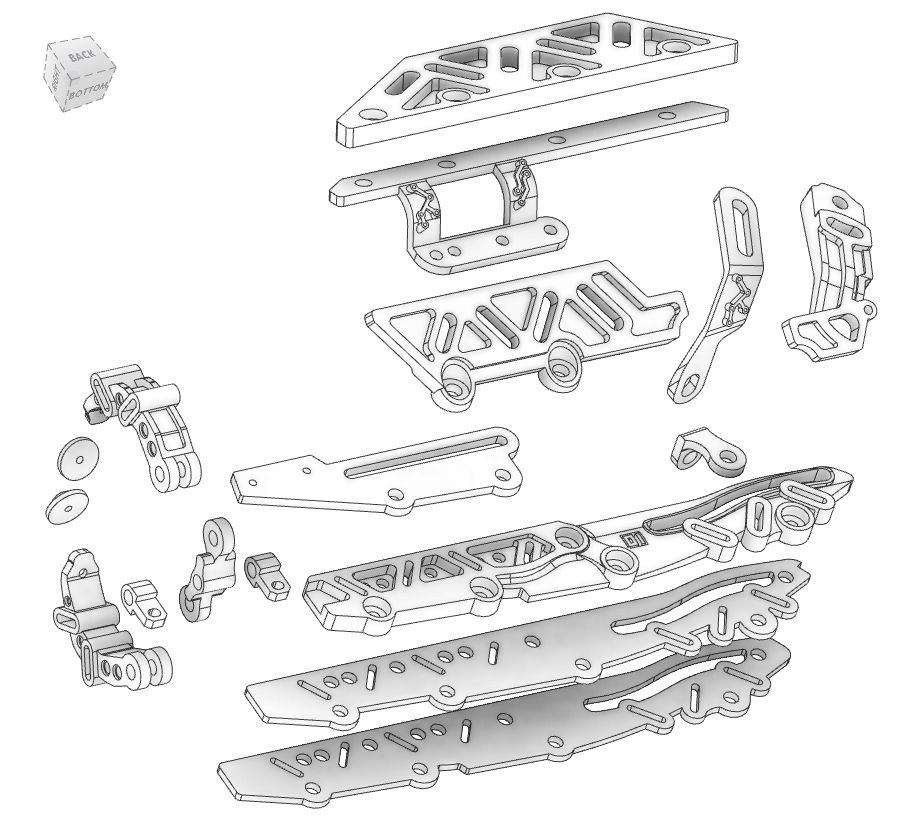
instructions/images/forearm/forearm.png
