01binary/elysium-max-exoskeleton/instructions/images/hand/hand-view-back.png

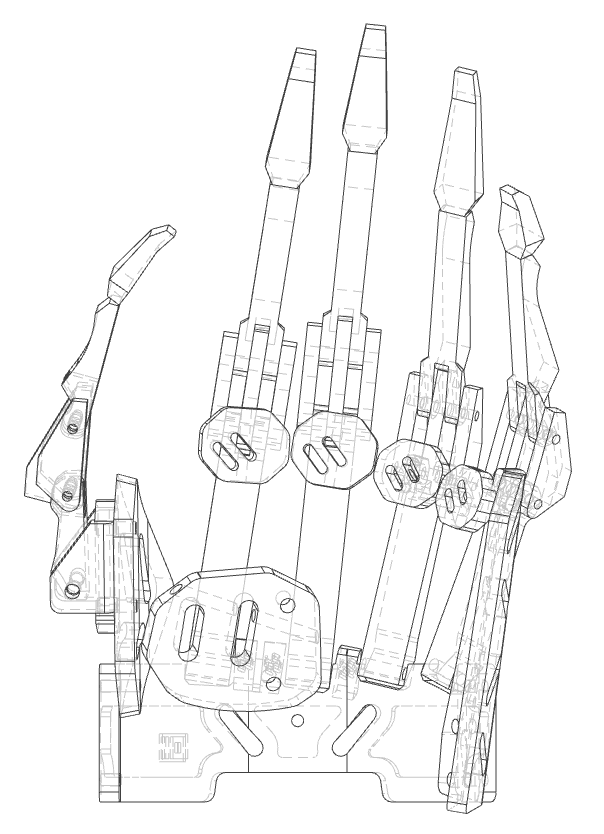
instructions/images/hand/hand-view-back.png
