01binary/elysium-max-exoskeleton/instructions/images/hand/hand-view-bottom.png

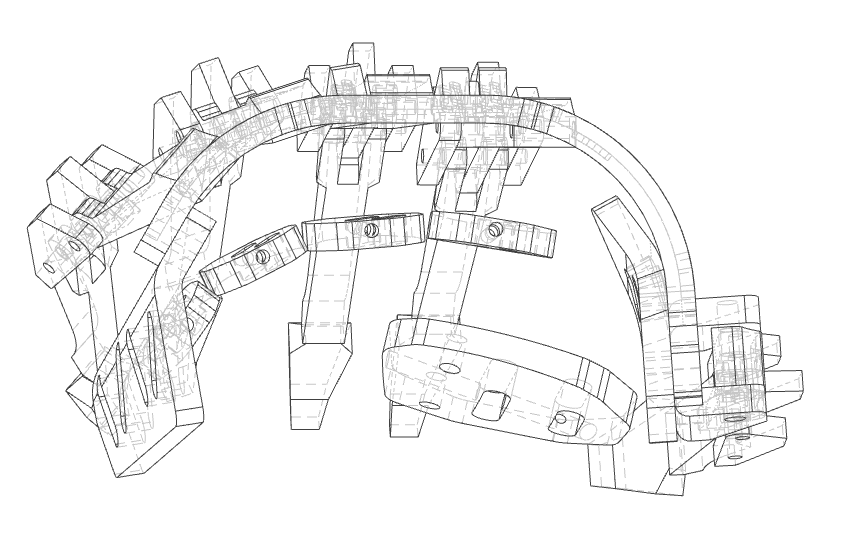
instructions/images/hand/hand-view-bottom.png
