01binary/elysium-max-exoskeleton/instructions/images/hand/hand-view-corner.png

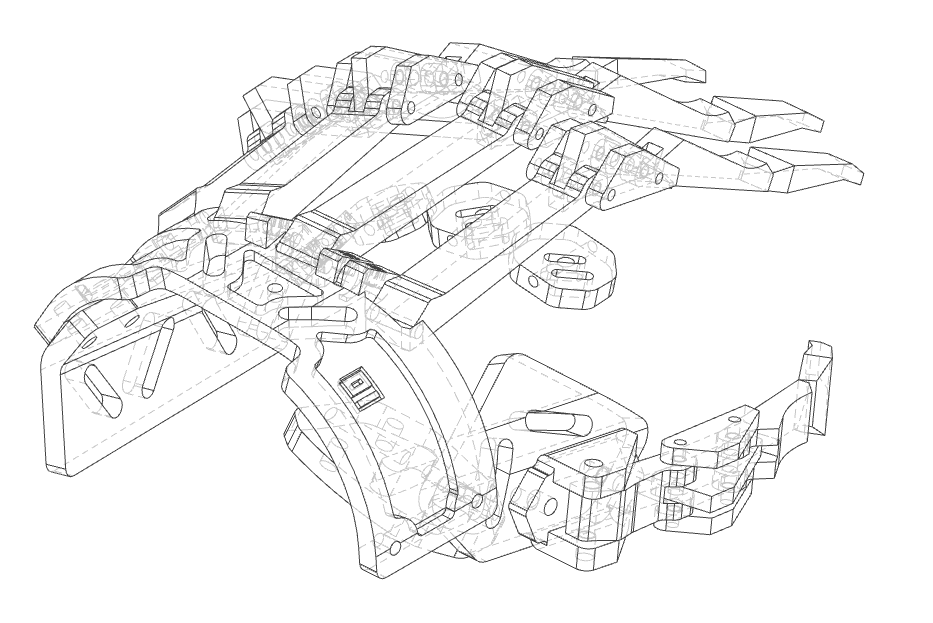
instructions/images/hand/hand-view-corner.png
