01binary/elysium-max-exoskeleton/instructions/images/hand/hand-view-front.png

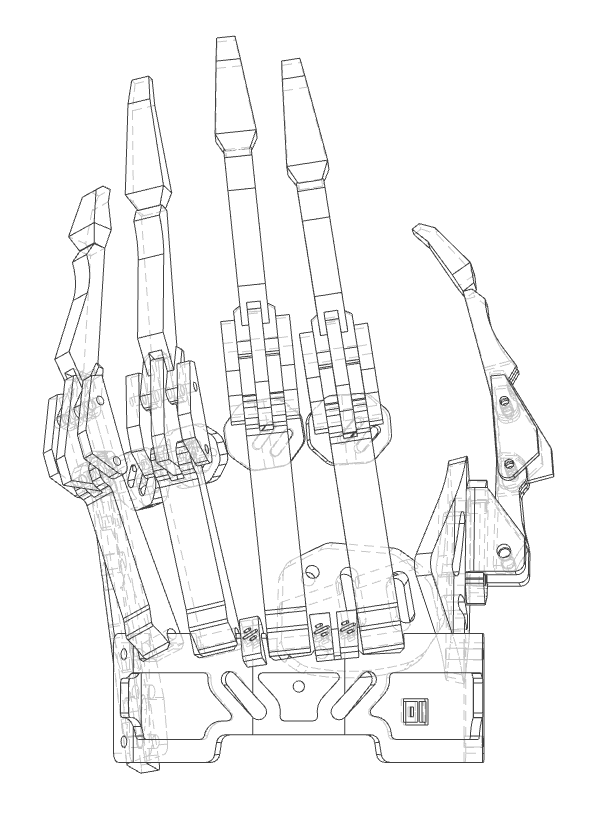
instructions/images/hand/hand-view-front.png
