01binary/elysium-max-exoskeleton/instructions/images/hand/hand-view-left.png

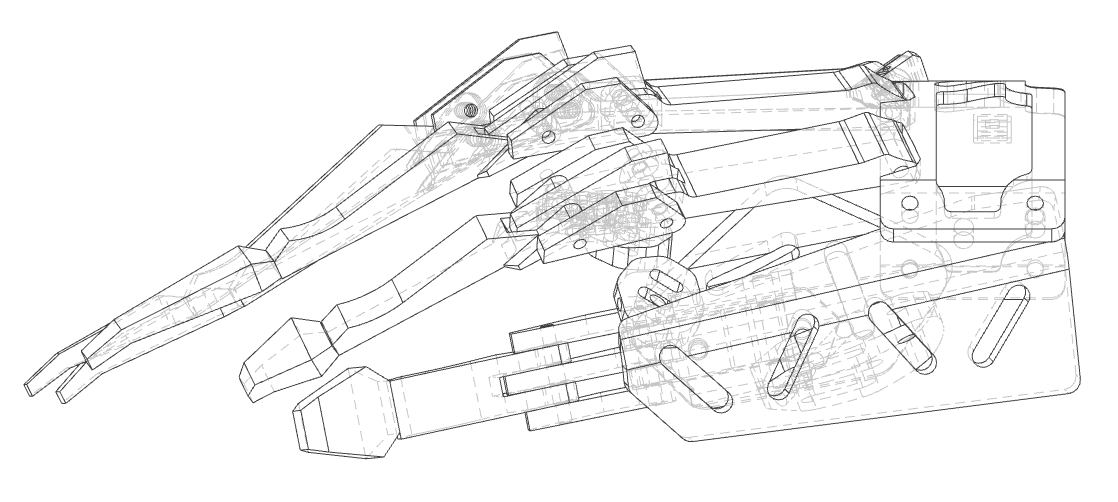
instructions/images/hand/hand-view-left.png
