01binary/elysium-max-exoskeleton/instructions/images/hand/hand-view-right.png

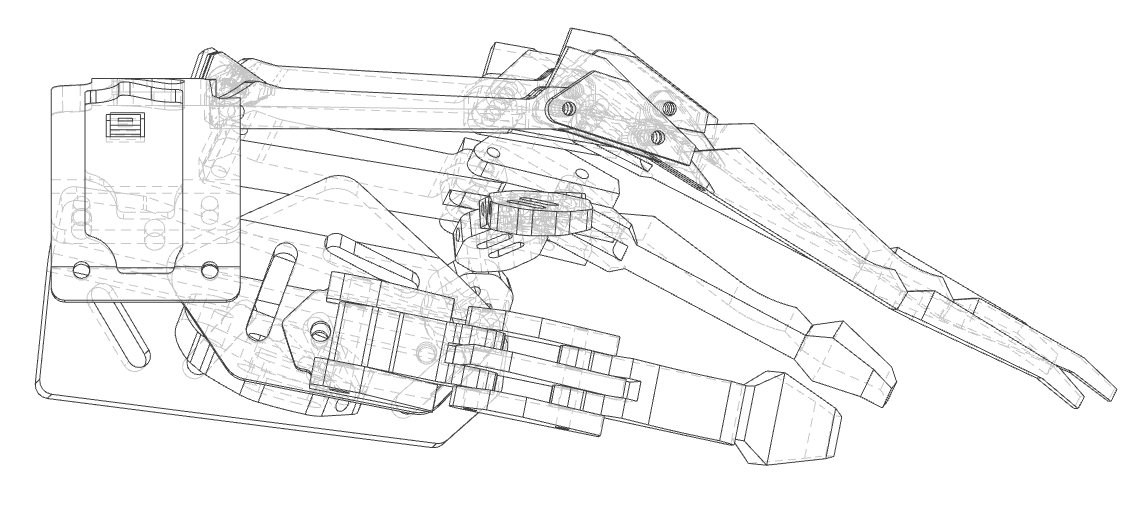
instructions/images/hand/hand-view-right.png
