01binary/elysium-max-exoskeleton/instructions/images/hand/hand-view-top.png

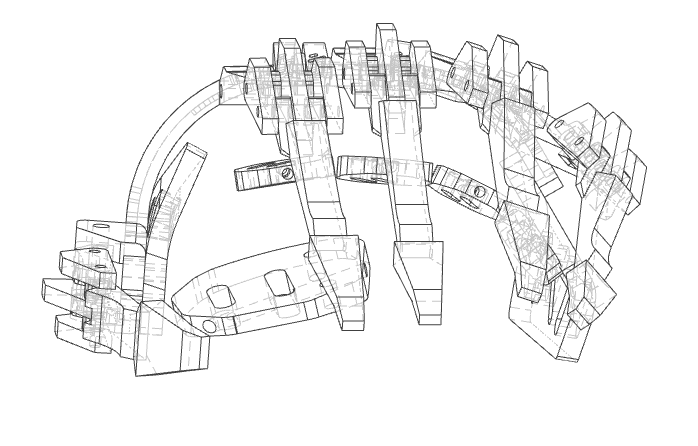
instructions/images/hand/hand-view-top.png
