01binary/elysium-max-exoskeleton/instructions/images/hand/hand.png

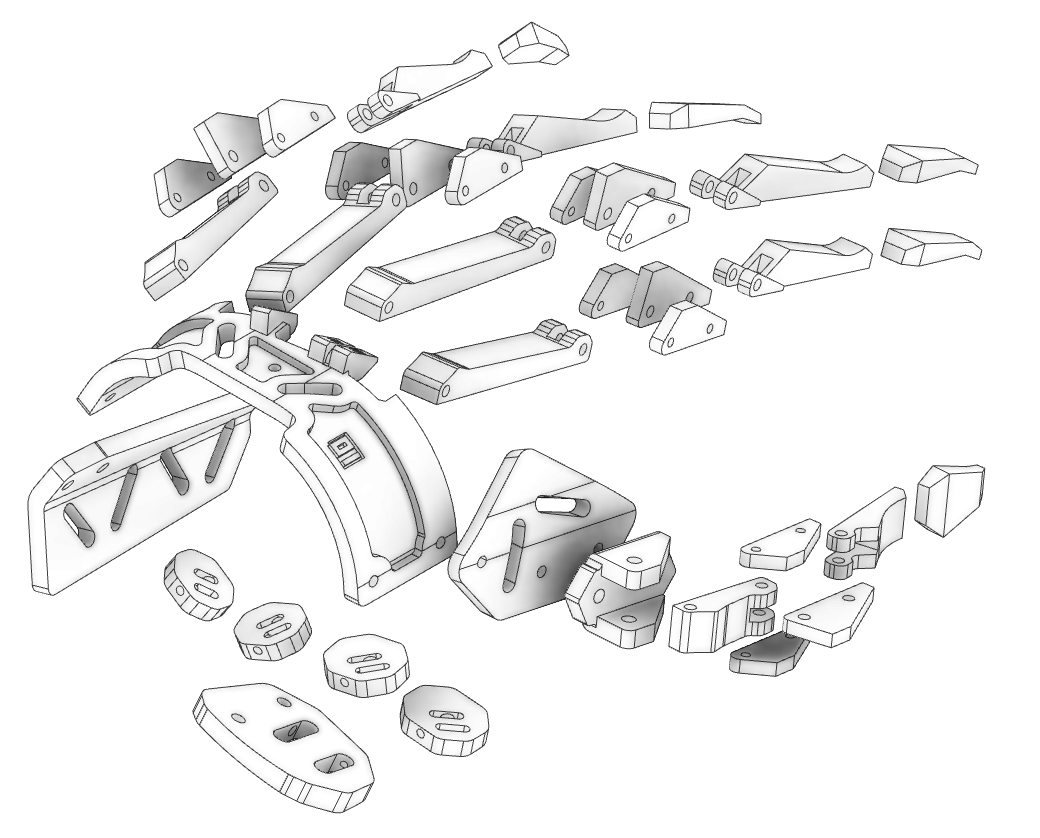
instructions/images/hand/hand.png
