01binary/elysium-max-exoskeleton/instructions/images/hip/hip-view-back.png

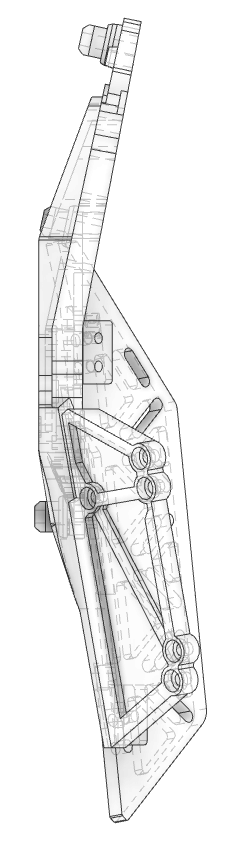
instructions/images/hip/hip-view-back.png
