01binary/elysium-max-exoskeleton/instructions/images/hip/hip-view-bottom.png

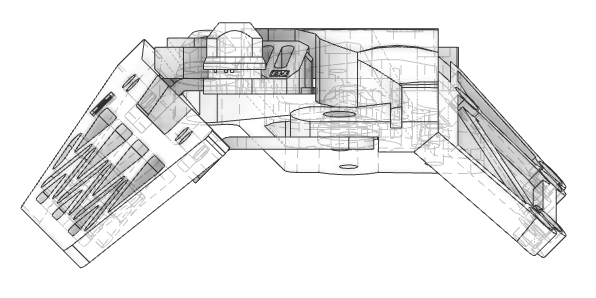
instructions/images/hip/hip-view-bottom.png
