01binary/elysium-max-exoskeleton/instructions/images/hip/hip-view-corner.png

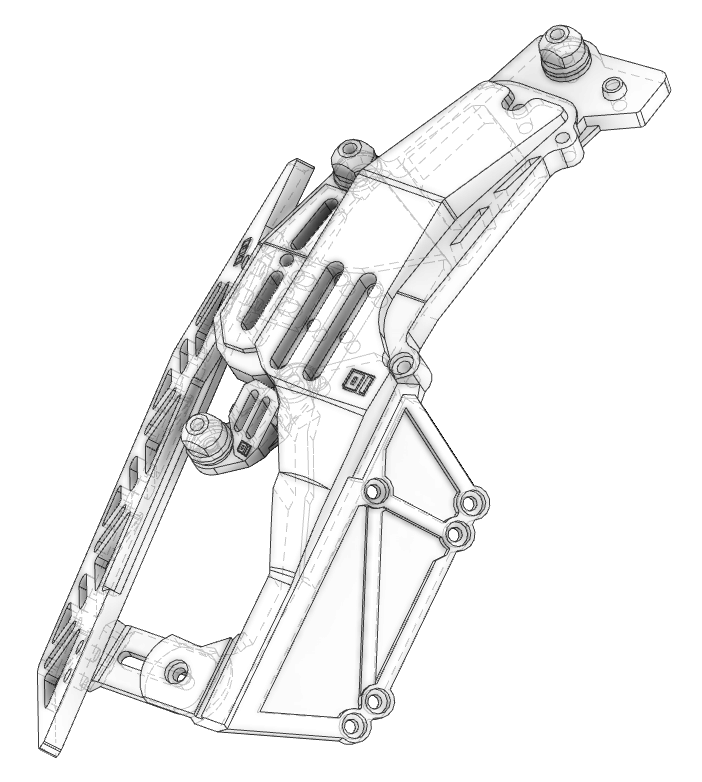
instructions/images/hip/hip-view-corner.png
