01binary/elysium-max-exoskeleton/instructions/images/hip/hip-view-front.png

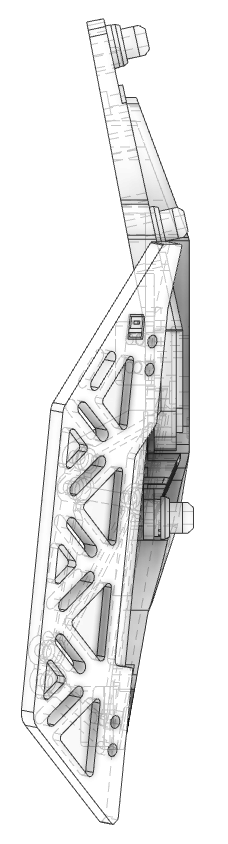
instructions/images/hip/hip-view-front.png
