01binary/elysium-max-exoskeleton/instructions/images/hip/hip-view-left.png

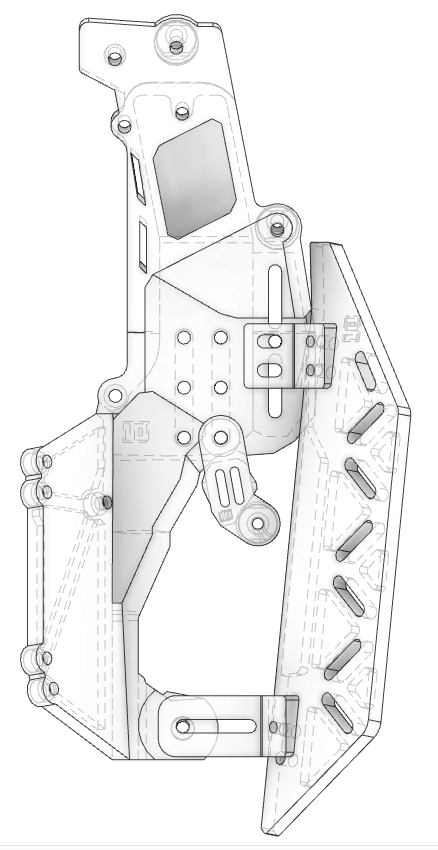
instructions/images/hip/hip-view-left.png
