01binary/elysium-max-exoskeleton/instructions/images/hip/hip-view-right.png

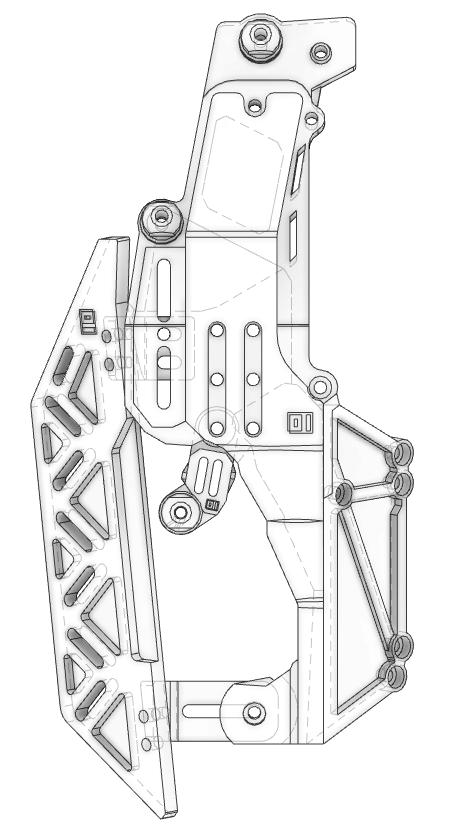
instructions/images/hip/hip-view-right.png
