01binary/elysium-max-exoskeleton/instructions/images/hip/hip-view-top.png

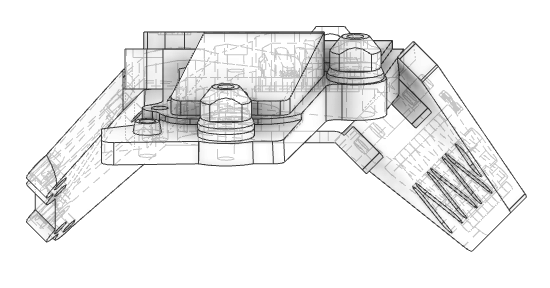
instructions/images/hip/hip-view-top.png
