01binary/elysium-max-exoskeleton/instructions/images/hip/hip.png

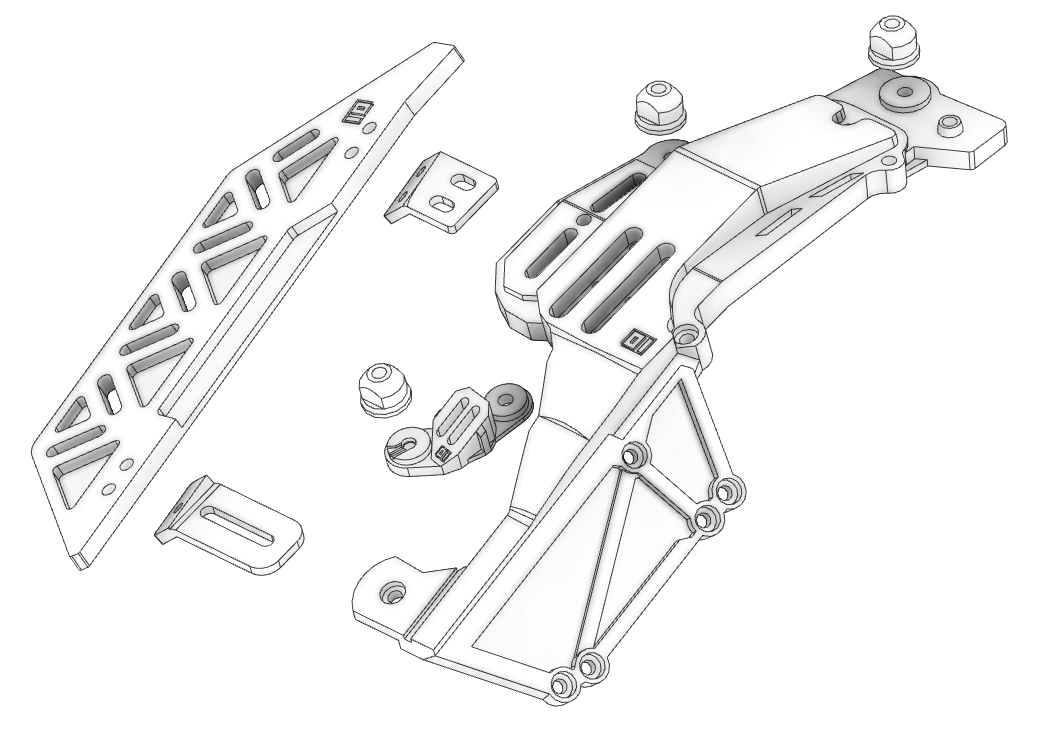
instructions/images/hip/hip.png
