01binary/elysium-max-exoskeleton/instructions/images/leg/leg-view-back.png

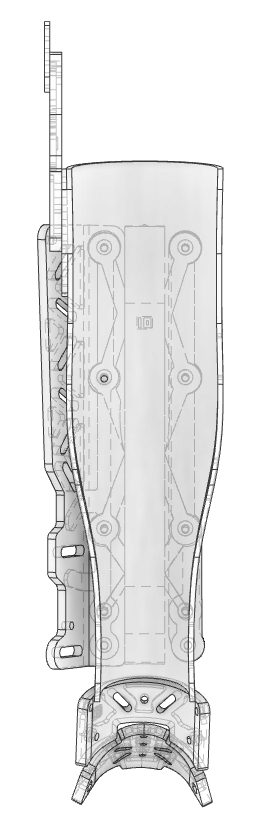
instructions/images/leg/leg-view-back.png
