01binary/elysium-max-exoskeleton/instructions/images/leg/leg-view-bottom.png

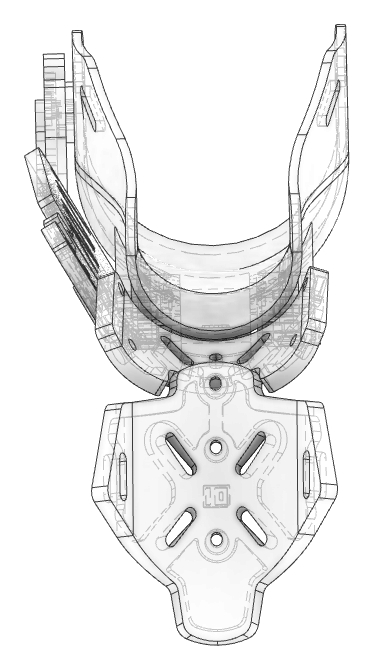
instructions/images/leg/leg-view-bottom.png
