01binary/elysium-max-exoskeleton/instructions/images/leg/leg-view-corner.png

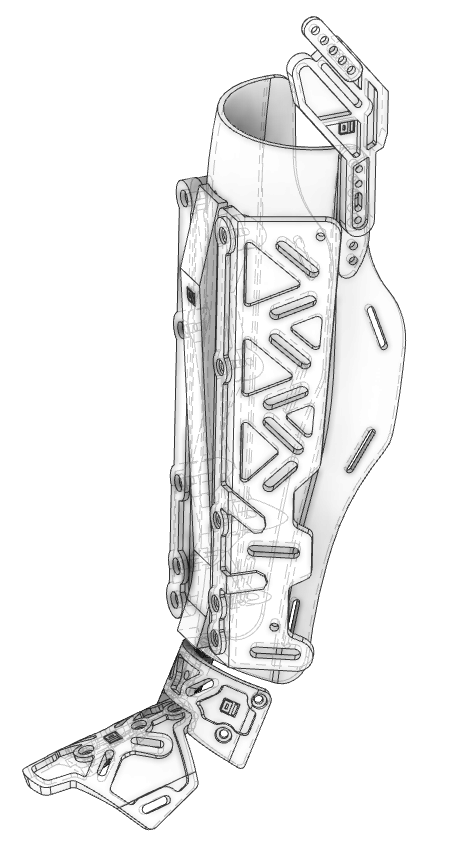
instructions/images/leg/leg-view-corner.png
