01binary/elysium-max-exoskeleton/instructions/images/leg/leg-view-front.png

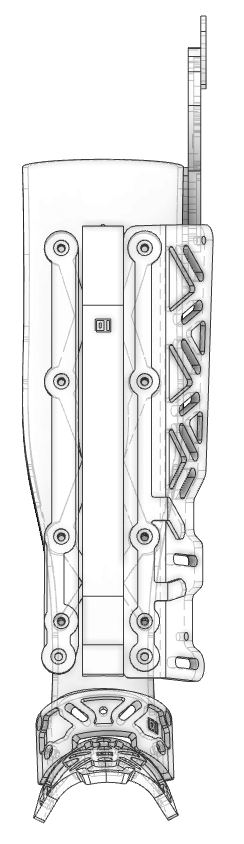
instructions/images/leg/leg-view-front.png
