01binary/elysium-max-exoskeleton/instructions/images/leg/leg-view-left.png

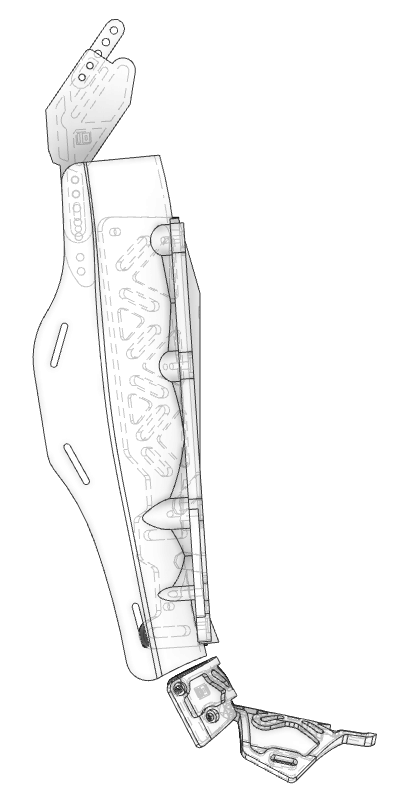
instructions/images/leg/leg-view-left.png
