01binary/elysium-max-exoskeleton/instructions/images/leg/leg-view-right.png

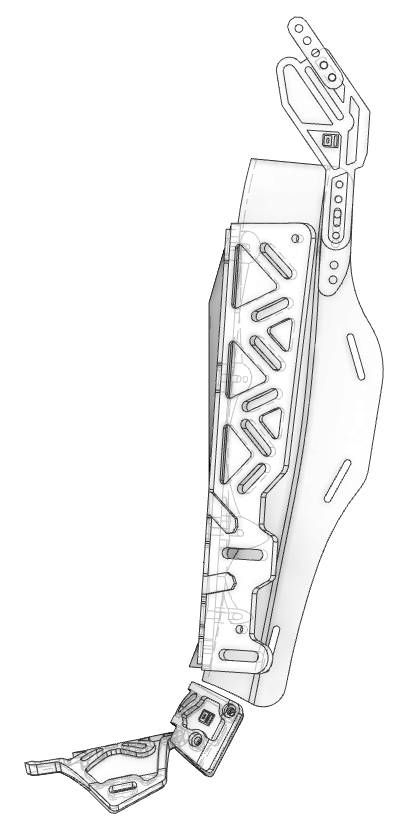
instructions/images/leg/leg-view-right.png
