01binary/elysium-max-exoskeleton/instructions/images/leg/leg.png

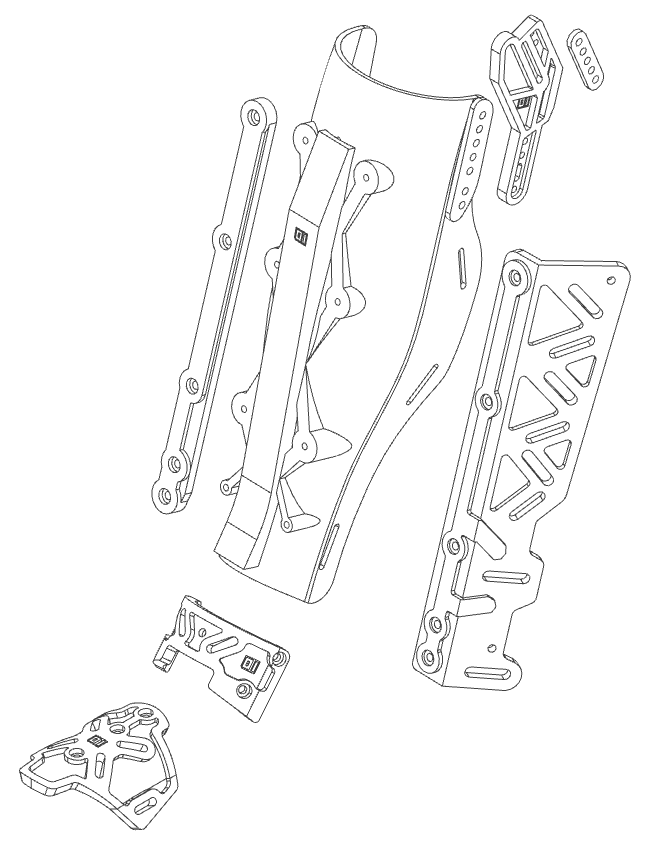
instructions/images/leg/leg.png
