01binary/elysium-max-exoskeleton/instructions/images/optional/vacuum-tube-holders01.png

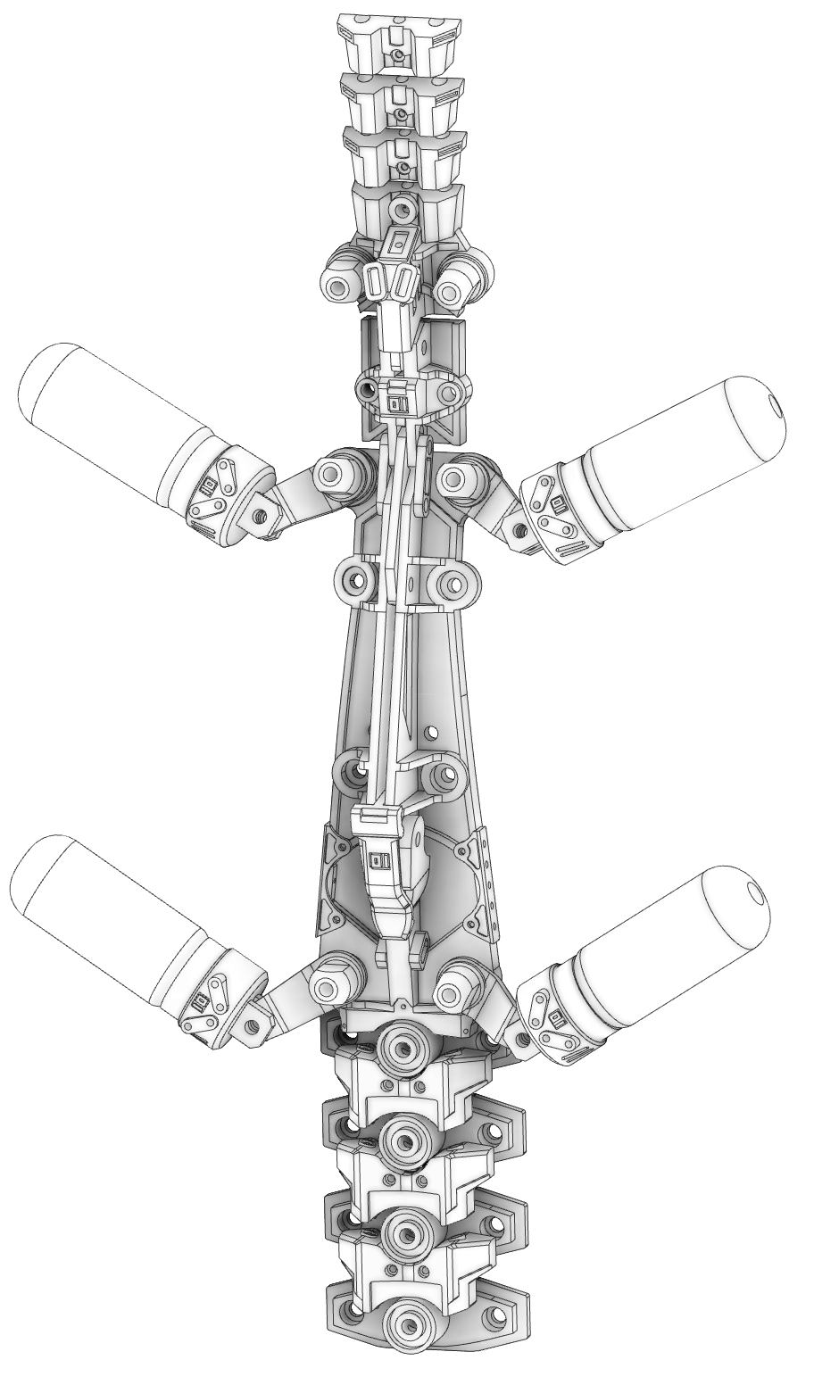
instructions/images/optional/vacuum-tube-holders01.png
