01binary/elysium-max-exoskeleton/instructions/images/optional/vacuum-tube-holders02.png

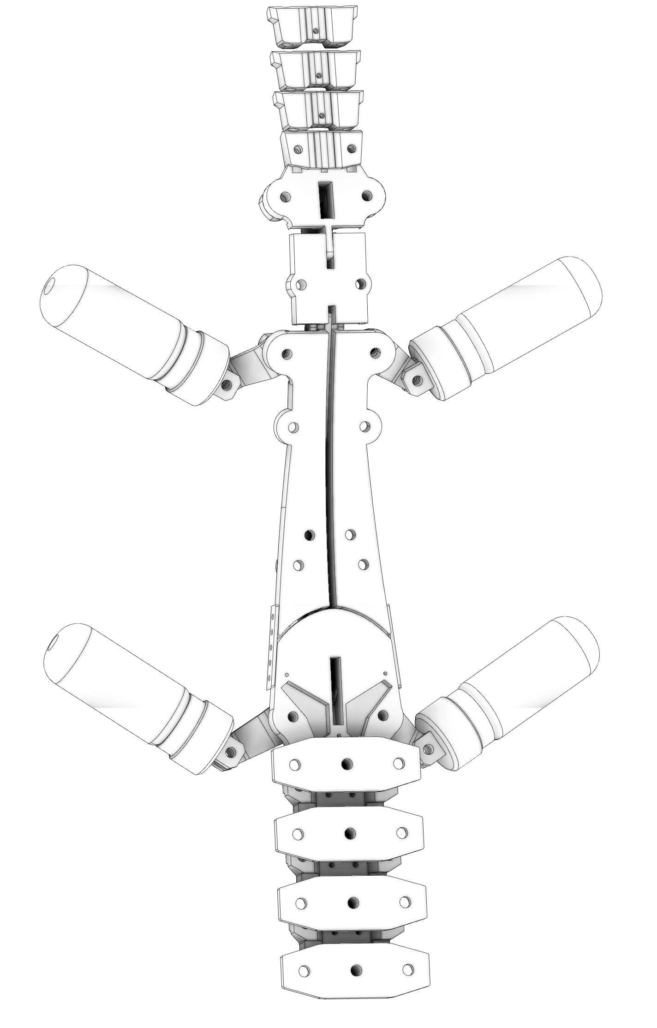
instructions/images/optional/vacuum-tube-holders02.png
