01binary/elysium-max-exoskeleton/instructions/images/pelvis/pelvis-view-back.png

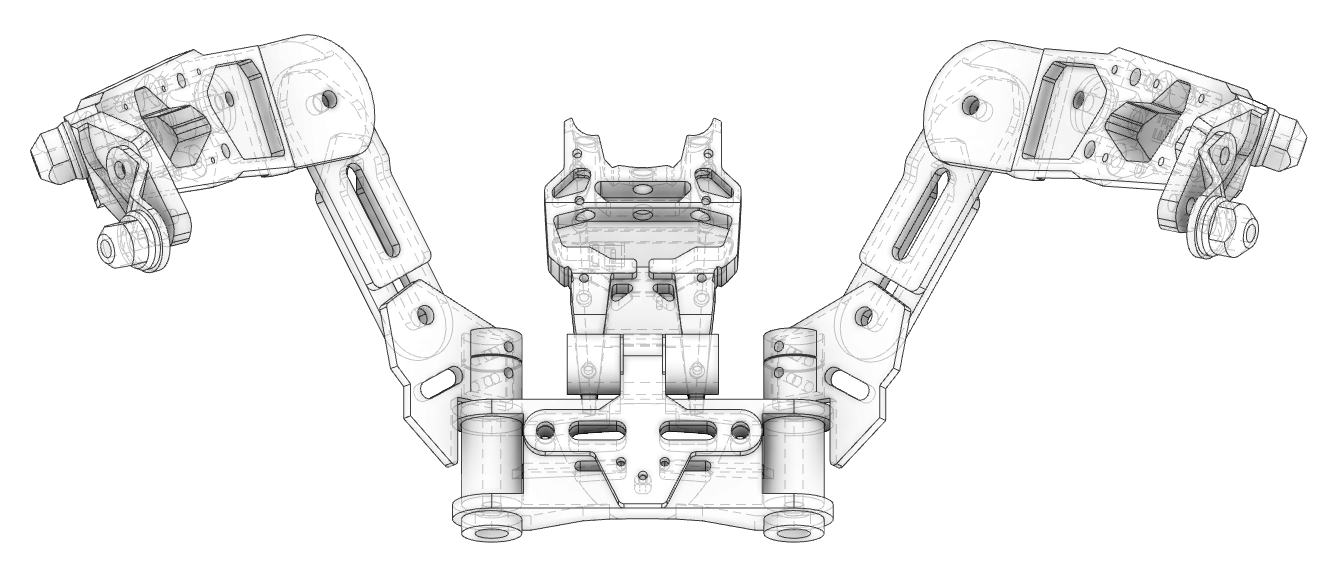
instructions/images/pelvis/pelvis-view-back.png
