01binary/elysium-max-exoskeleton/instructions/images/pelvis/pelvis-view-bottom.png

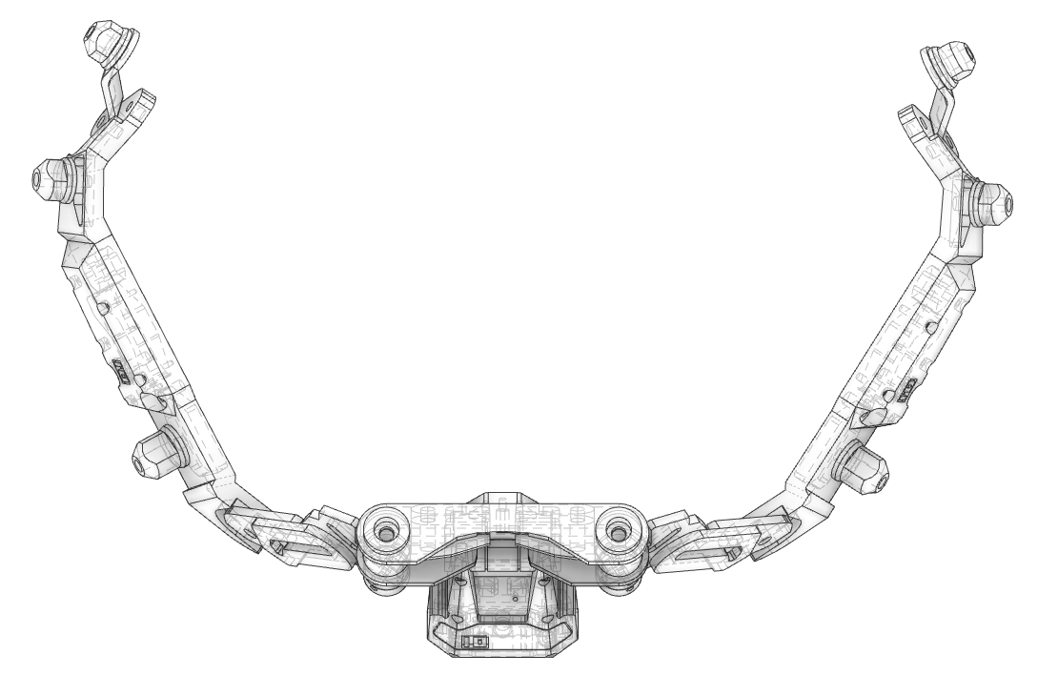
instructions/images/pelvis/pelvis-view-bottom.png
