01binary/elysium-max-exoskeleton/instructions/images/pelvis/pelvis-view-front.png

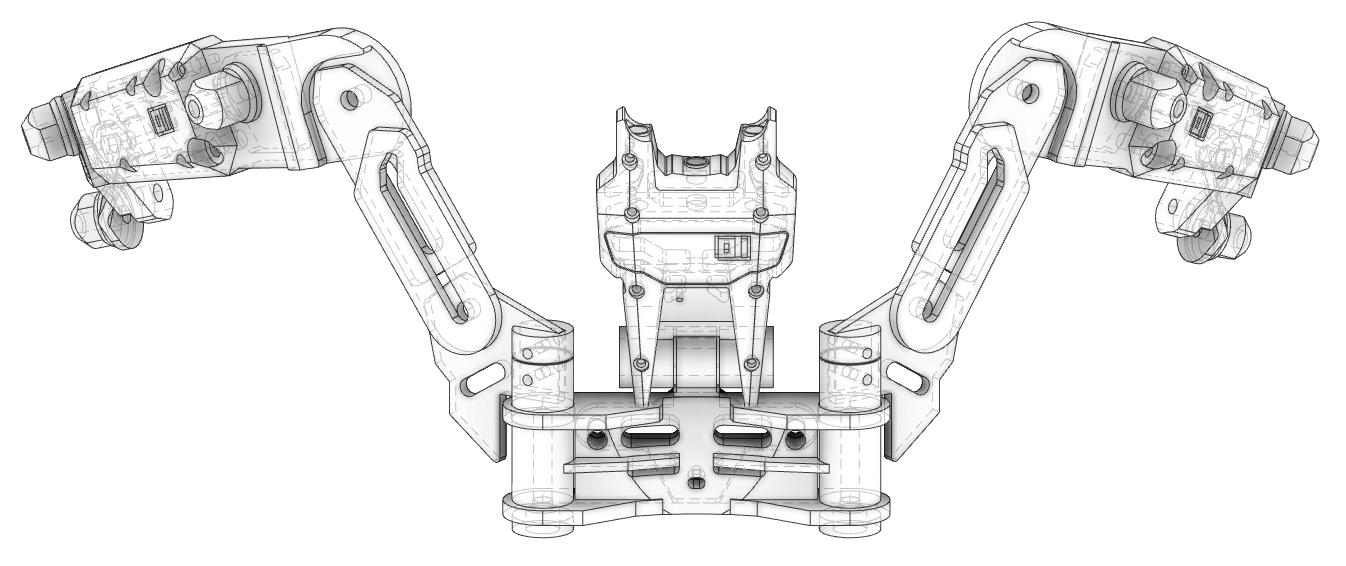
instructions/images/pelvis/pelvis-view-front.png
