01binary/elysium-max-exoskeleton/instructions/images/pelvis/pelvis-view-side.png

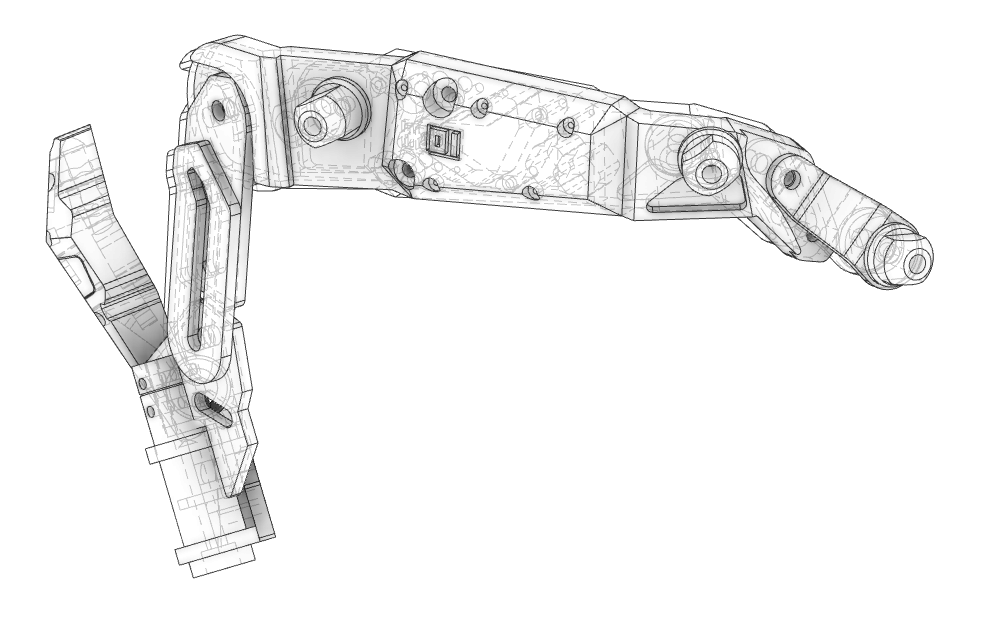
instructions/images/pelvis/pelvis-view-side.png
