01binary/elysium-max-exoskeleton/instructions/images/pelvis/pelvis-view-top.png

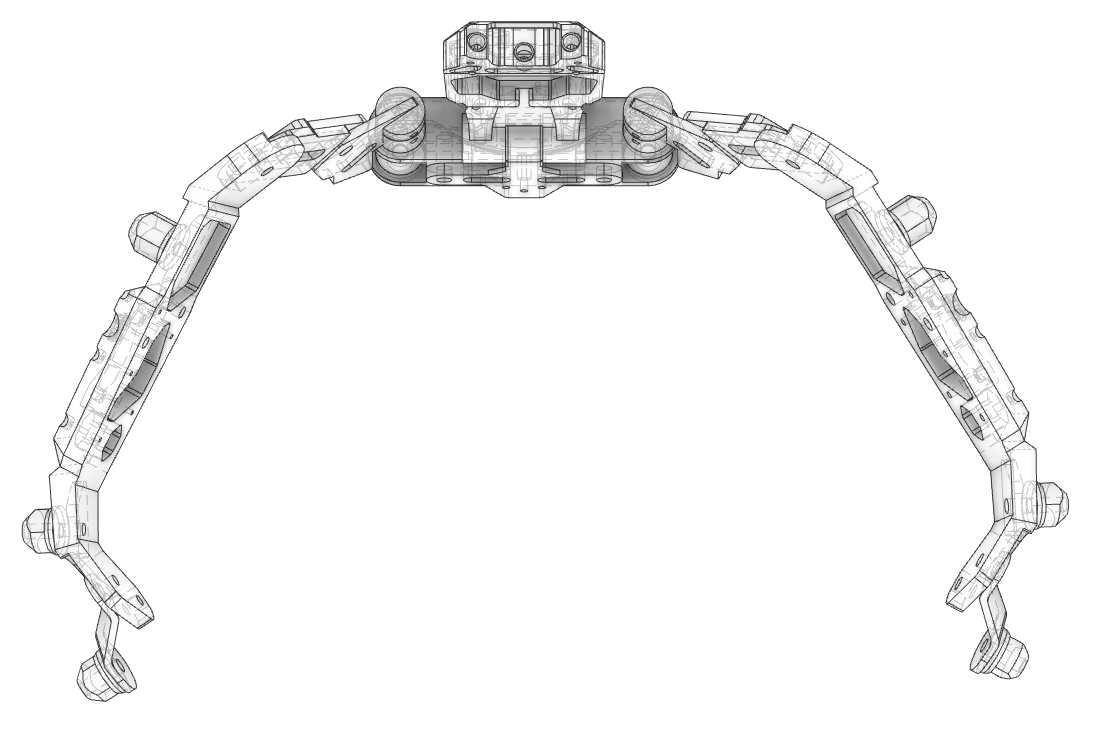
instructions/images/pelvis/pelvis-view-top.png
