01binary/elysium-max-exoskeleton/instructions/images/pelvis/pelvis-wing.png

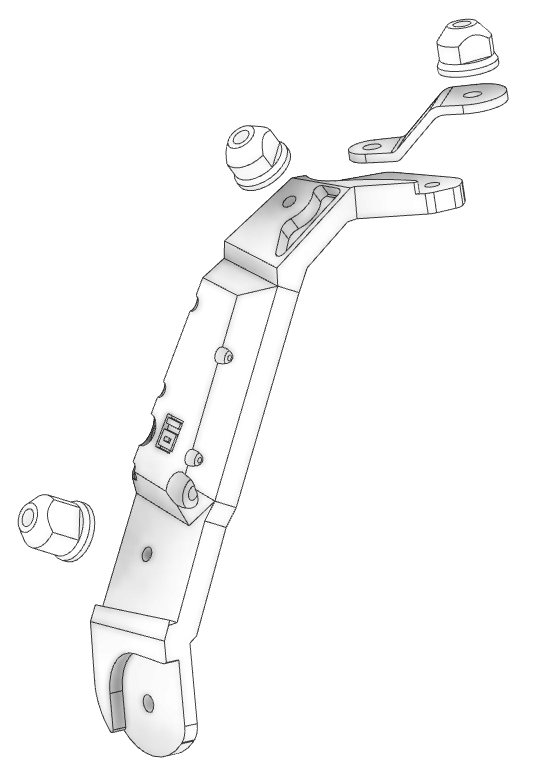
instructions/images/pelvis/pelvis-wing.png
