01binary/elysium-max-exoskeleton/instructions/images/pelvis/pelvis.png

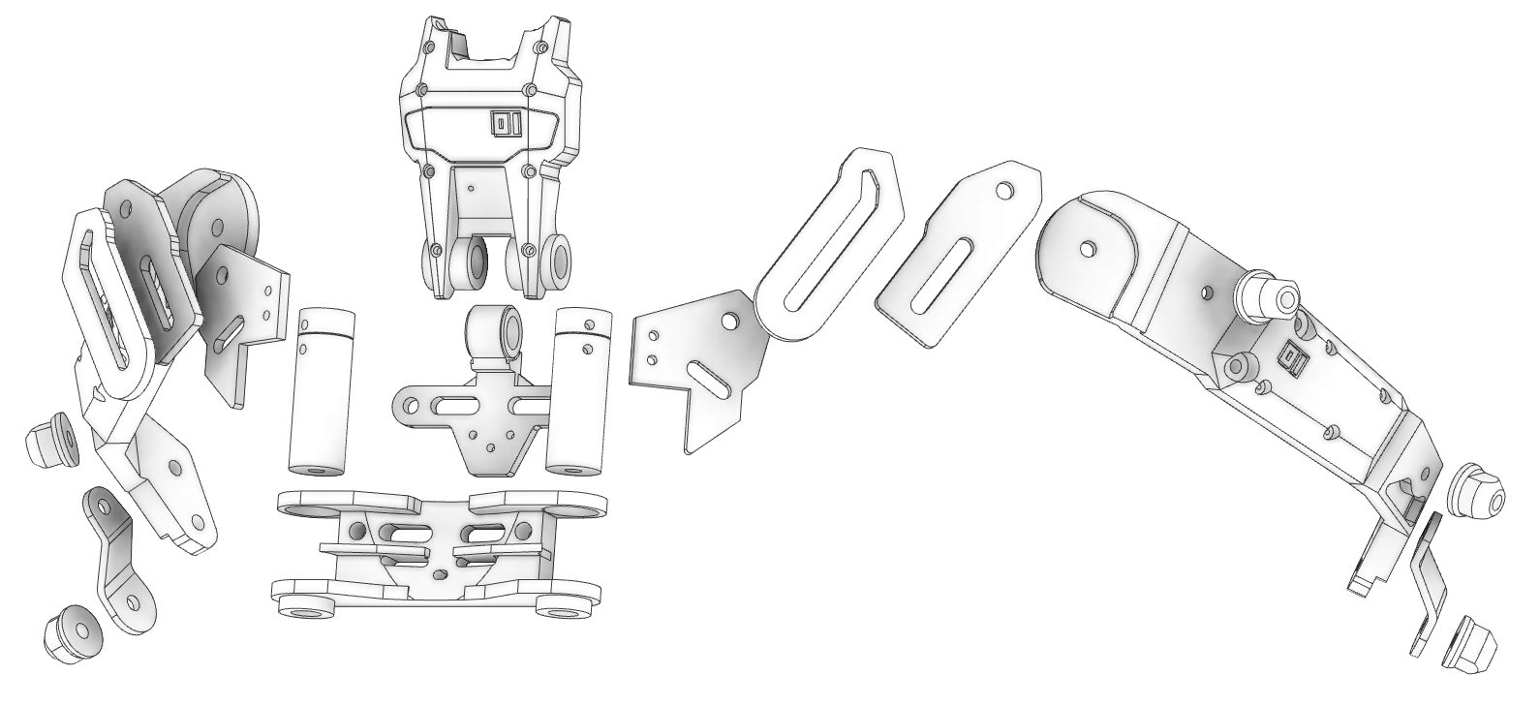
instructions/images/pelvis/pelvis.png
