01binary/elysium-max-exoskeleton/instructions/images/piston/piston-view-back.png

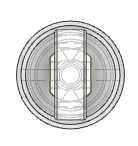
instructions/images/piston/piston-view-back.png
