01binary/elysium-max-exoskeleton/instructions/images/piston/piston-view-corner.png

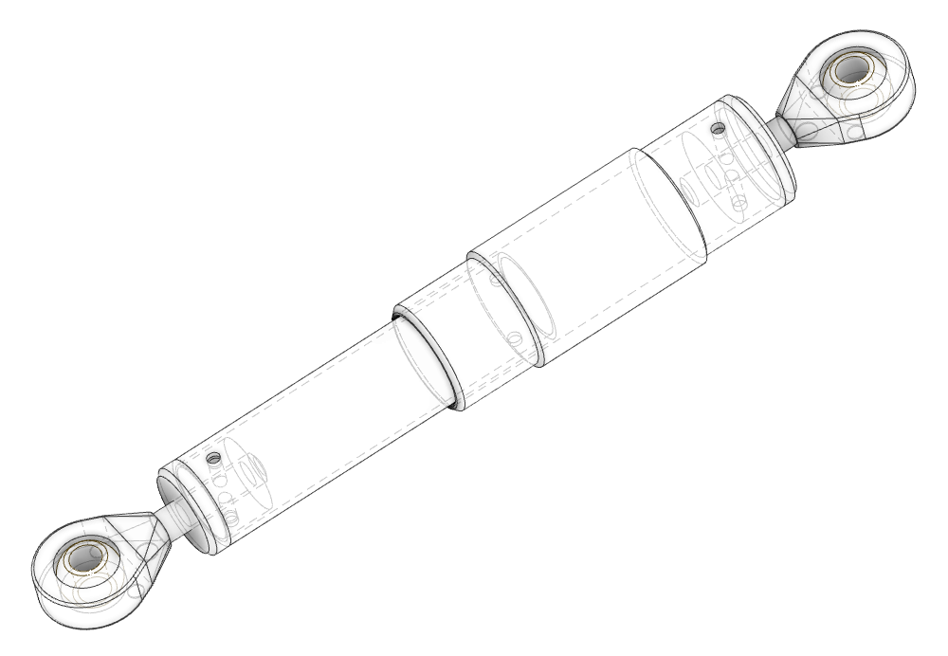
instructions/images/piston/piston-view-corner.png
