01binary/elysium-max-exoskeleton/instructions/images/piston/piston.png

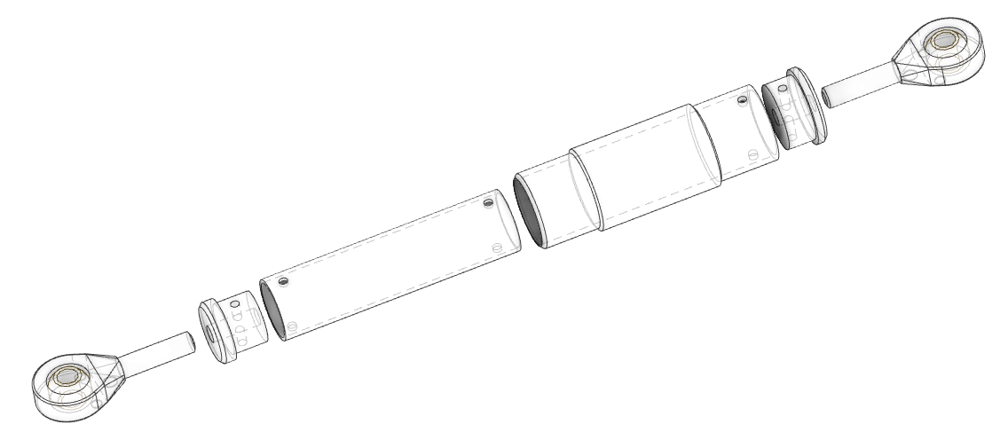
instructions/images/piston/piston.png
