01binary/elysium-max-exoskeleton/instructions/images/shoulder/shoulder-view-back.png

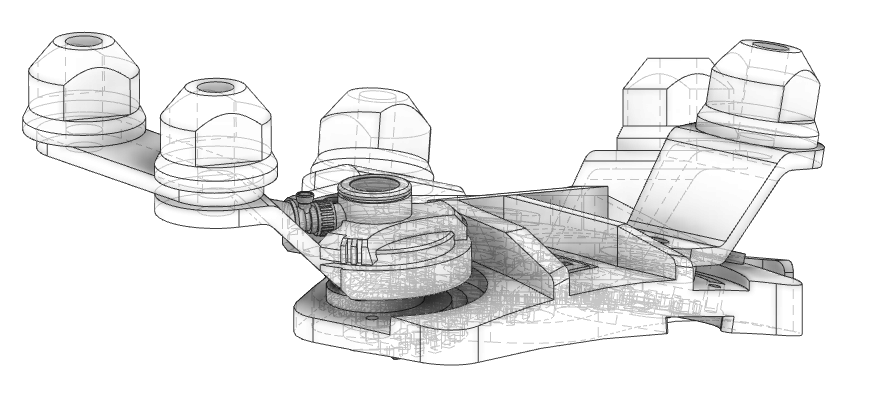
instructions/images/shoulder/shoulder-view-back.png
