01binary/elysium-max-exoskeleton/instructions/images/shoulder/shoulder-view-bottom.png

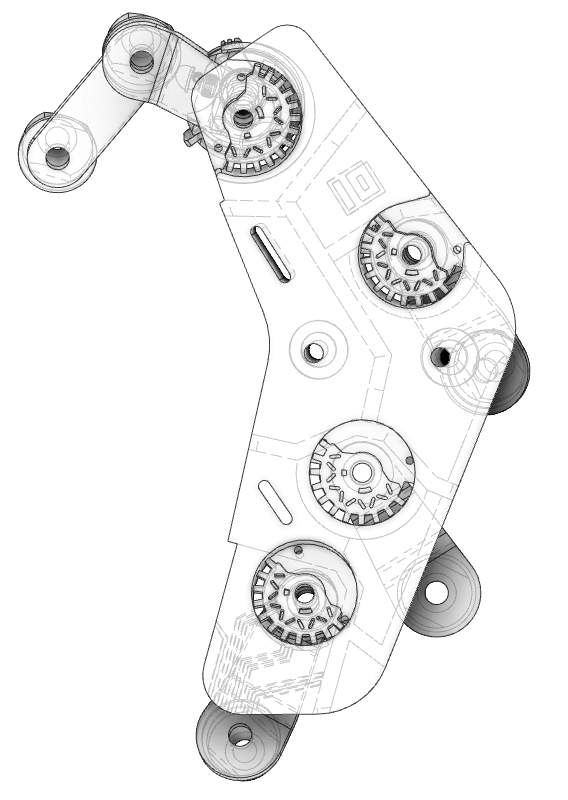
instructions/images/shoulder/shoulder-view-bottom.png
