01binary/elysium-max-exoskeleton/instructions/images/shoulder/shoulder-view-front.png

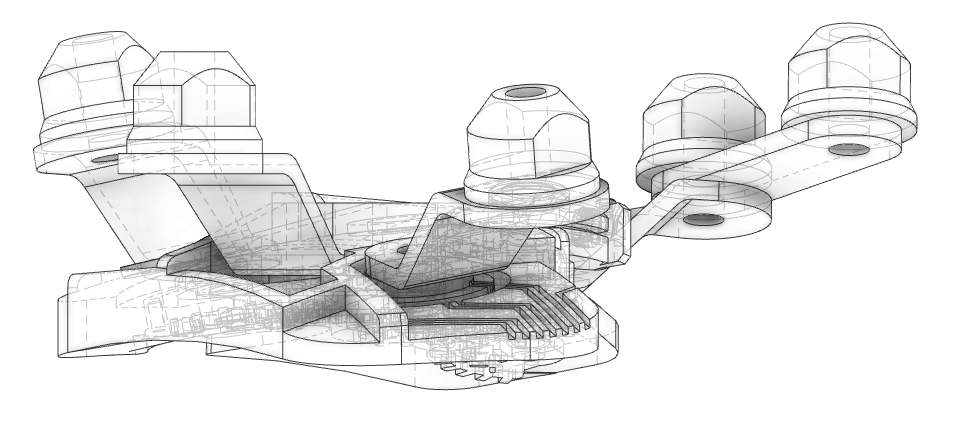
instructions/images/shoulder/shoulder-view-front.png
