01binary/elysium-max-exoskeleton/instructions/images/shoulder/shoulder-view-left.png

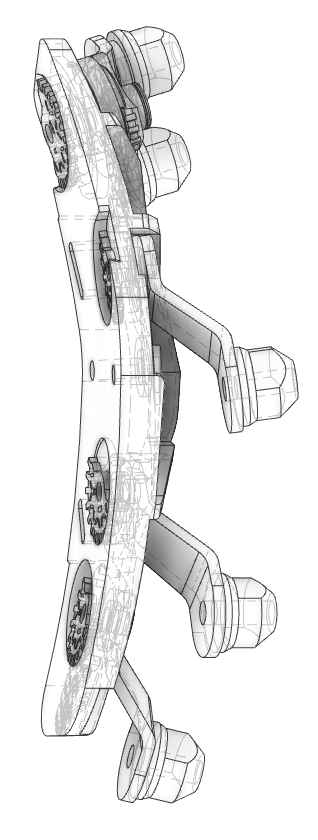
instructions/images/shoulder/shoulder-view-left.png
