01binary/elysium-max-exoskeleton/instructions/images/shoulder/shoulder-view-right.png

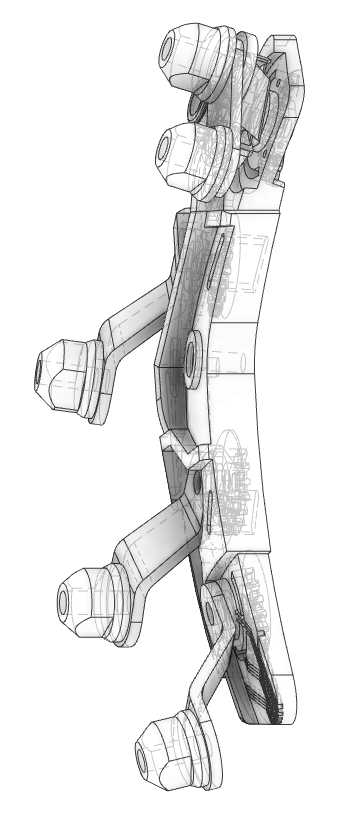
instructions/images/shoulder/shoulder-view-right.png
