01binary/elysium-max-exoskeleton/instructions/images/shoulder/shoulder-view-top.png

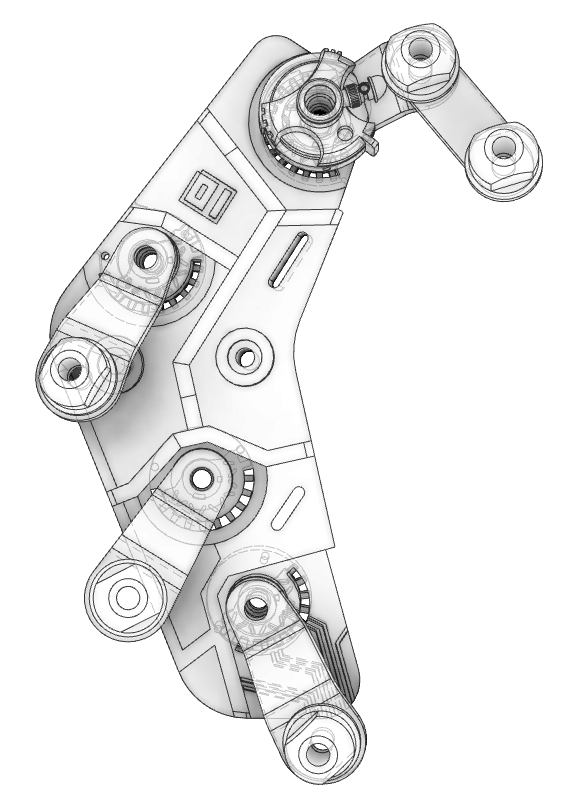
instructions/images/shoulder/shoulder-view-top.png
