01binary/elysium-max-exoskeleton/instructions/images/shoulder/shoulder.png

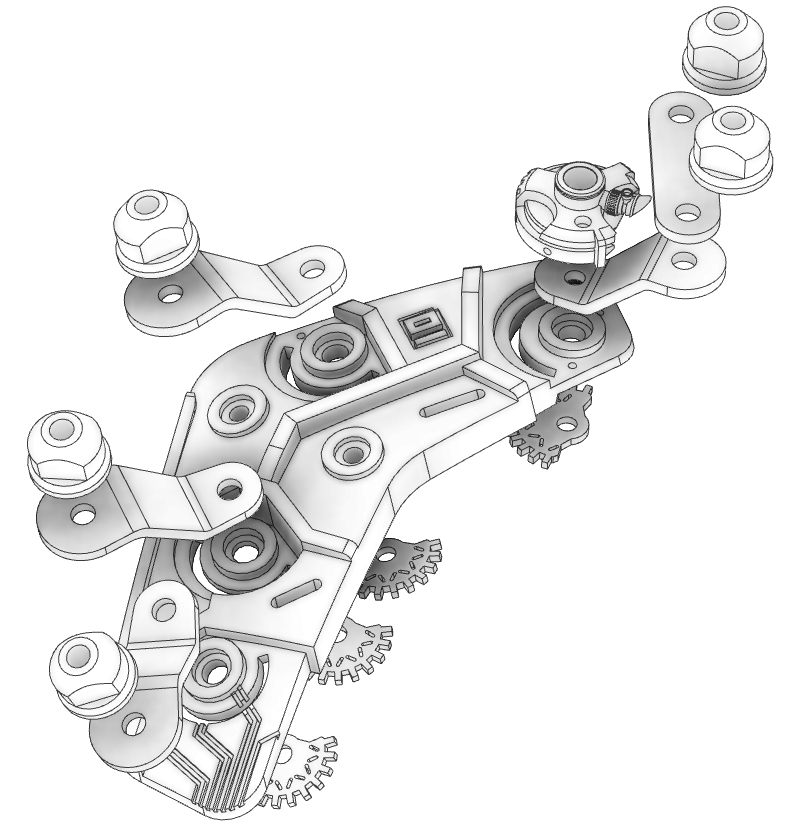
instructions/images/shoulder/shoulder.png
