01binary/elysium-max-exoskeleton/instructions/images/spine/spine-view-back.png

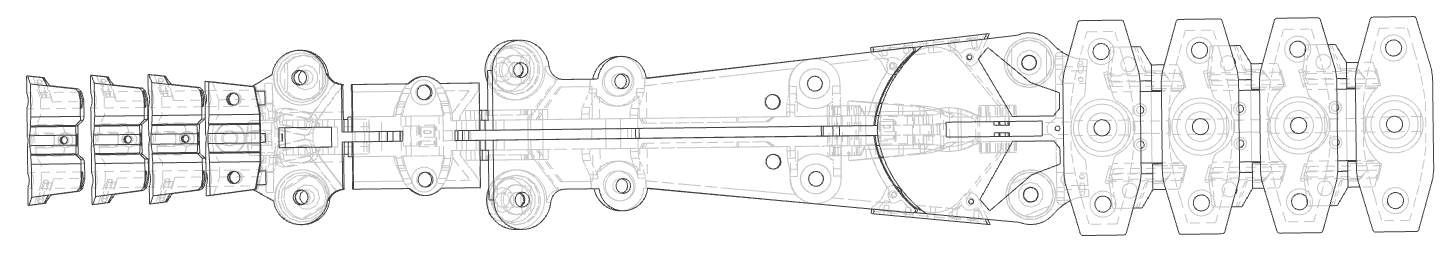
instructions/images/spine/spine-view-back.png
