01binary/elysium-max-exoskeleton/instructions/images/spine/spine-view-corner.png

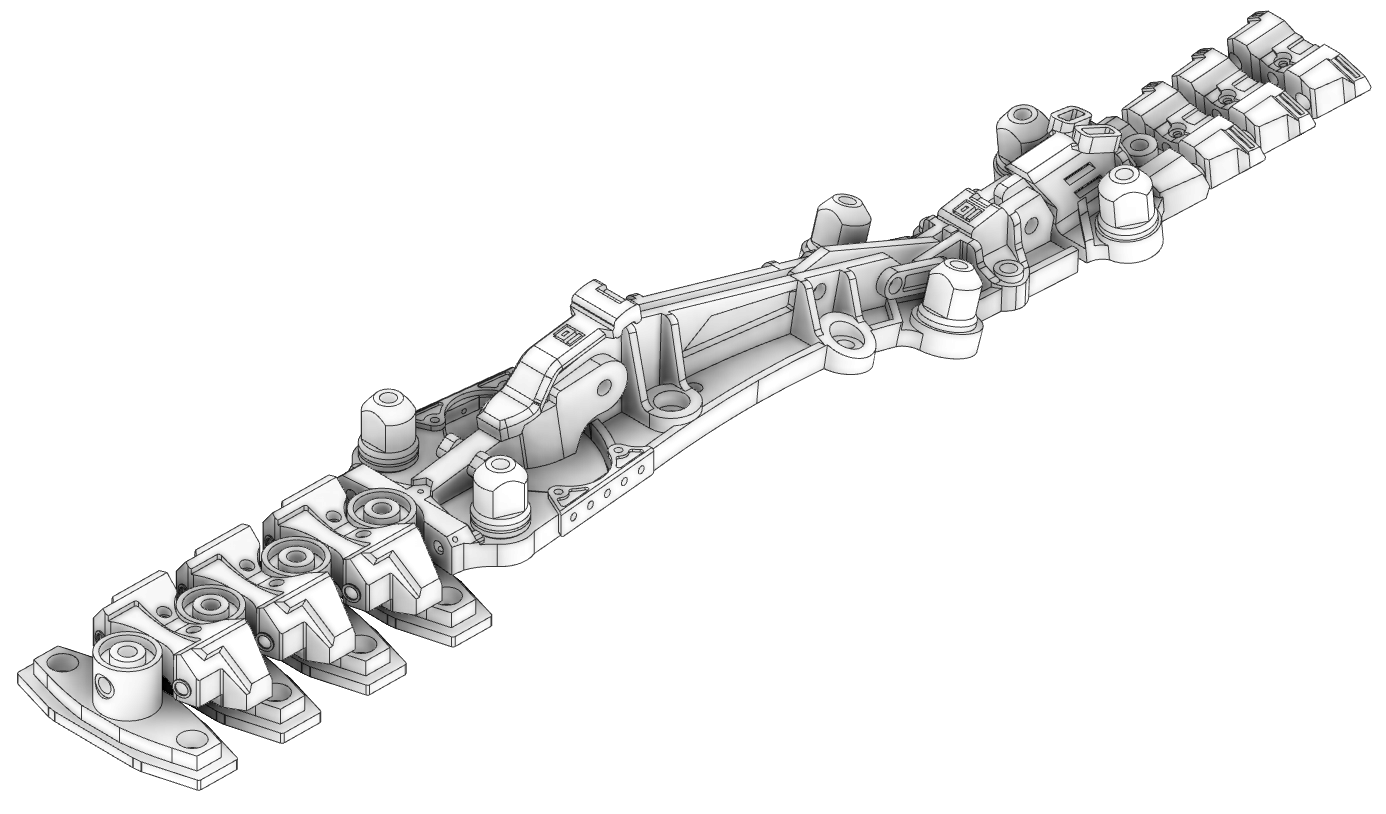
instructions/images/spine/spine-view-corner.png
