01binary/elysium-max-exoskeleton/instructions/images/spine/spine-view-front.png

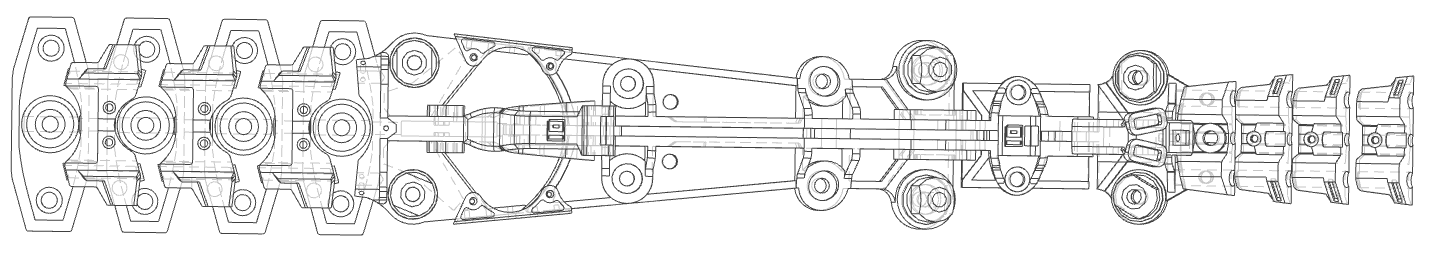
instructions/images/spine/spine-view-front.png
