01binary/elysium-max-exoskeleton/instructions/images/spine/spine-view-right.png

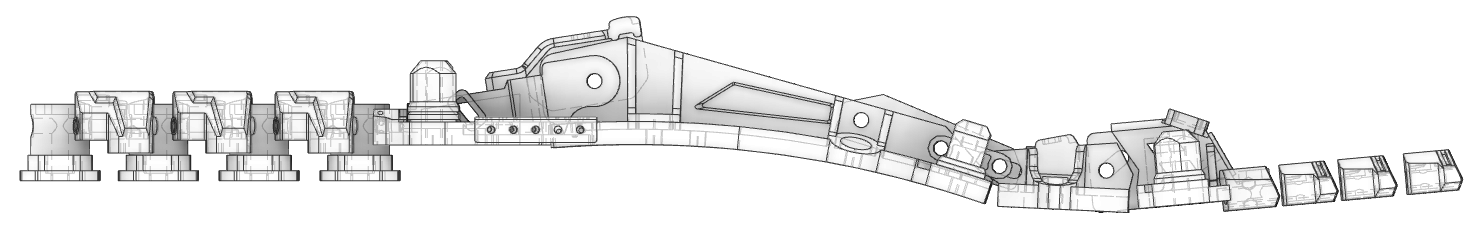
instructions/images/spine/spine-view-right.png
