01binary/elysium-max-exoskeleton/instructions/images/spine/spine-view-top.png

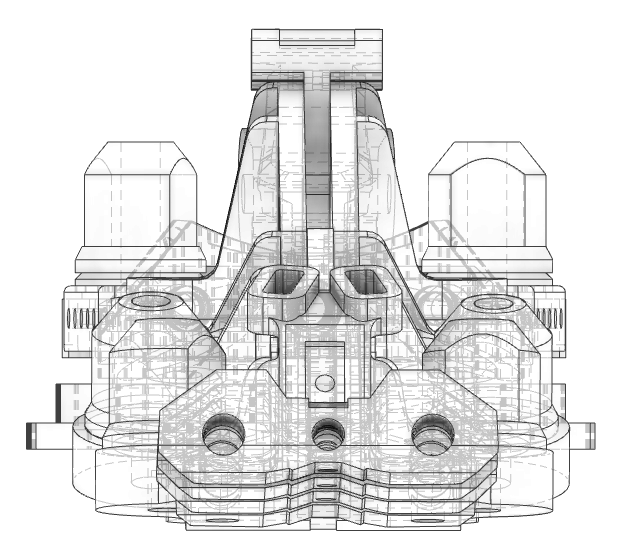
instructions/images/spine/spine-view-top.png
