01binary/elysium-max-exoskeleton/instructions/images/spine/spine.png

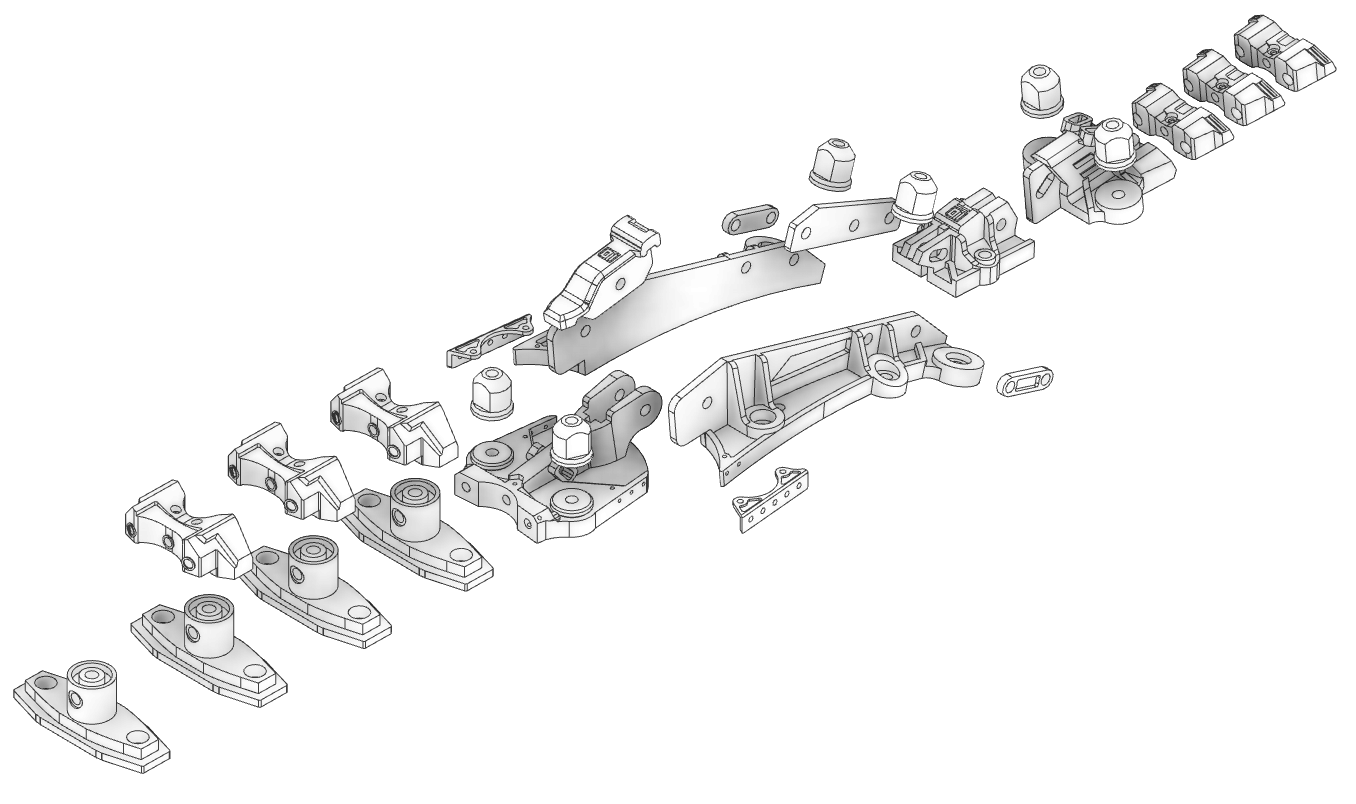
instructions/images/spine/spine.png
