01binary/elysium-max-exoskeleton/instructions/images/upper-arm/upper-arm-view-back.png

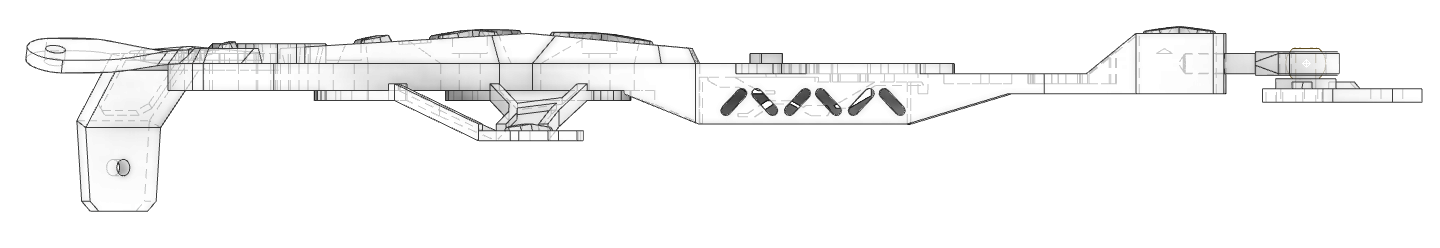
instructions/images/upper-arm/upper-arm-view-back.png
