01binary/elysium-max-exoskeleton/instructions/images/upper-arm/upper-arm-view-bottom.png

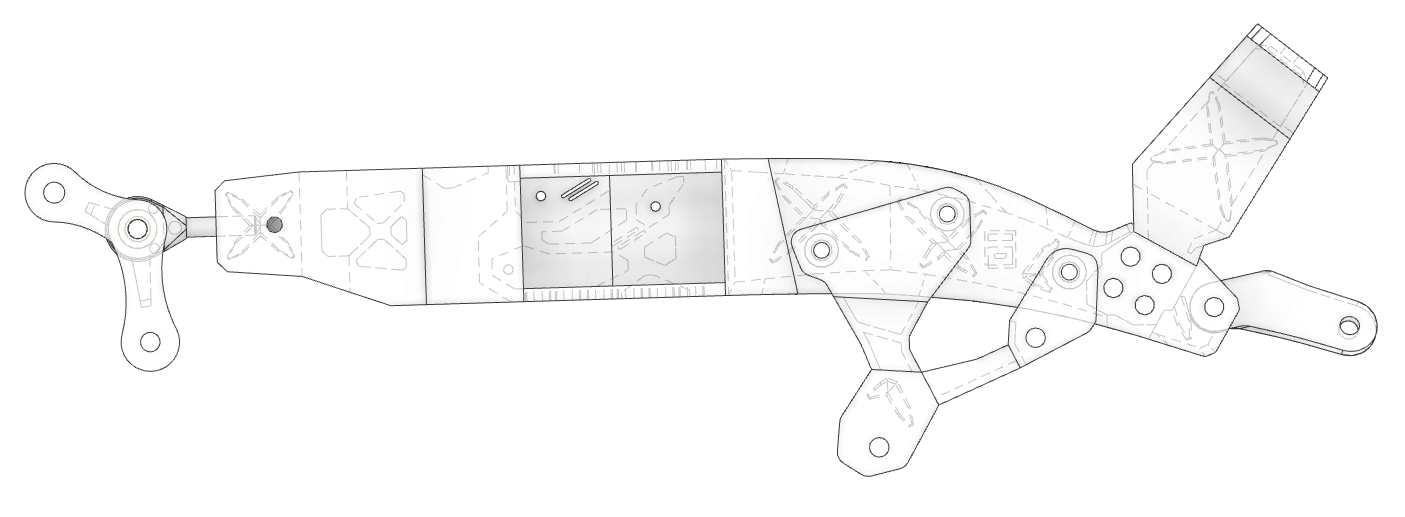
instructions/images/upper-arm/upper-arm-view-bottom.png
