01binary/elysium-max-exoskeleton/instructions/images/upper-arm/upper-arm-view-corner.png

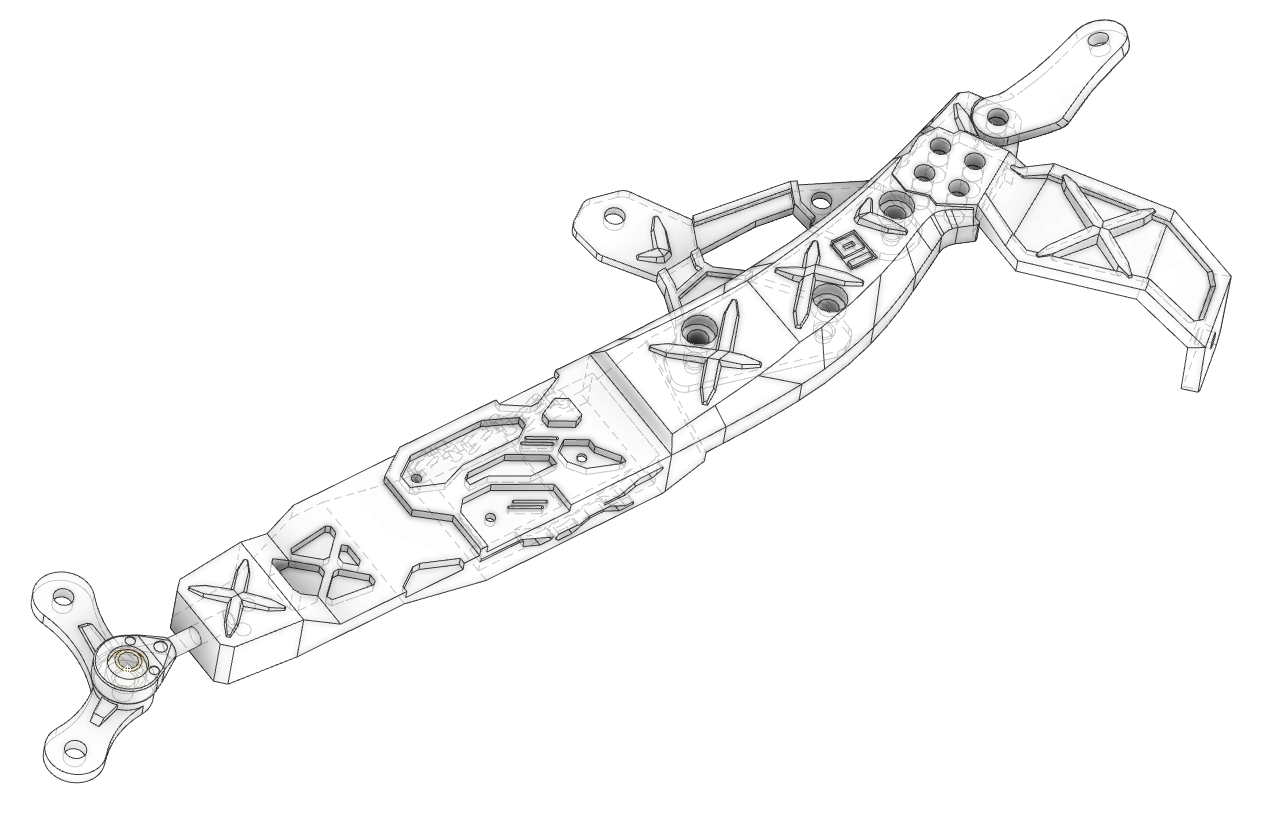
instructions/images/upper-arm/upper-arm-view-corner.png
