01binary/elysium-max-exoskeleton/instructions/images/upper-arm/upper-arm-view-front.png

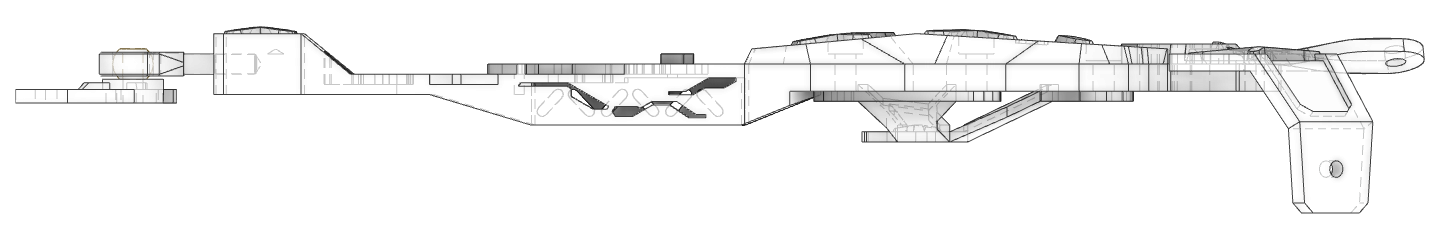
instructions/images/upper-arm/upper-arm-view-front.png
