01binary/elysium-max-exoskeleton/instructions/images/upper-arm/upper-arm-view-left.png

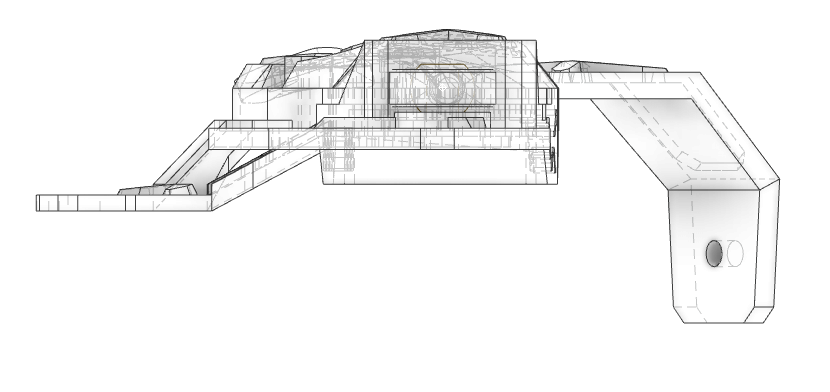
instructions/images/upper-arm/upper-arm-view-left.png
