01binary/elysium-max-exoskeleton/instructions/images/upper-arm/upper-arm-view-right.png

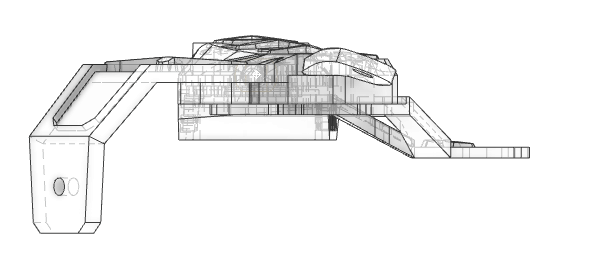
instructions/images/upper-arm/upper-arm-view-right.png
