01binary/elysium-max-exoskeleton/instructions/images/upper-arm/upper-arm-view-top.png

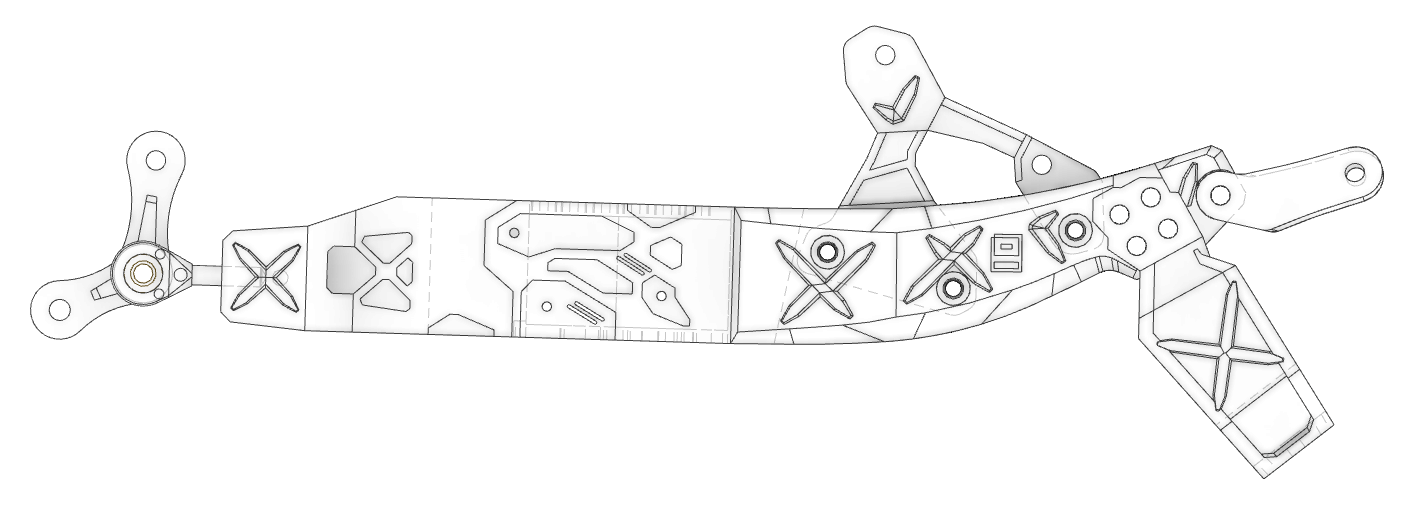
instructions/images/upper-arm/upper-arm-view-top.png
