01binary/elysium-max-exoskeleton/instructions/images/upper-arm/upper-arm.png

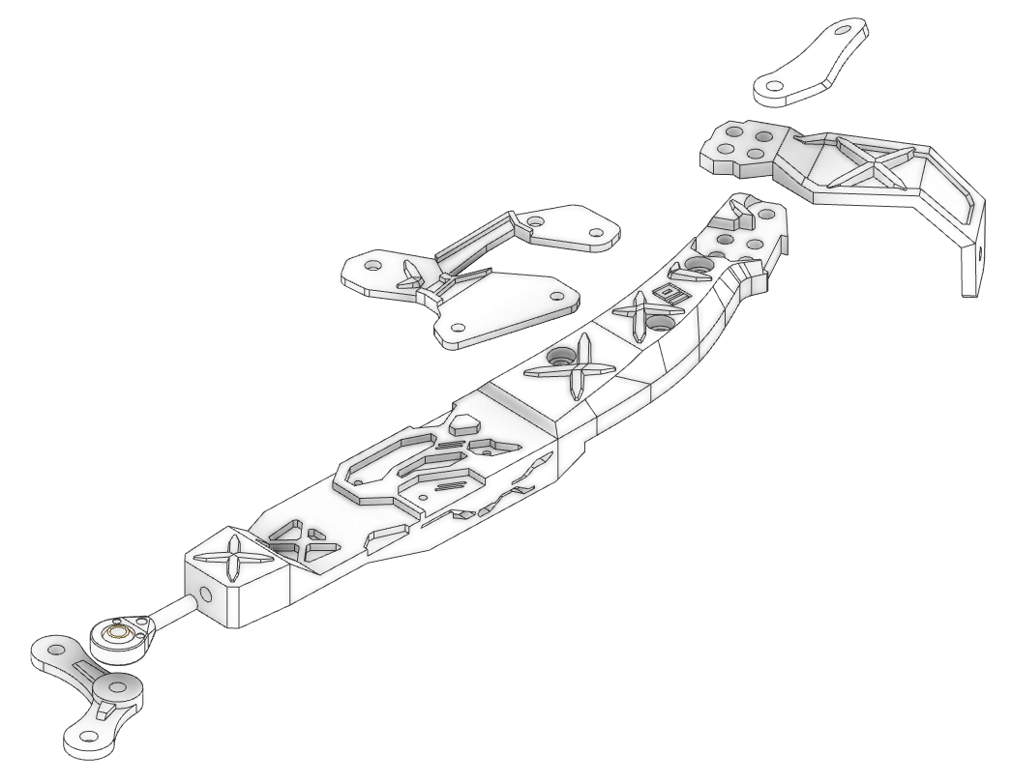
instructions/images/upper-arm/upper-arm.png
