01binary/elysium-max-exoskeleton/instructions/src/links/lighting.png

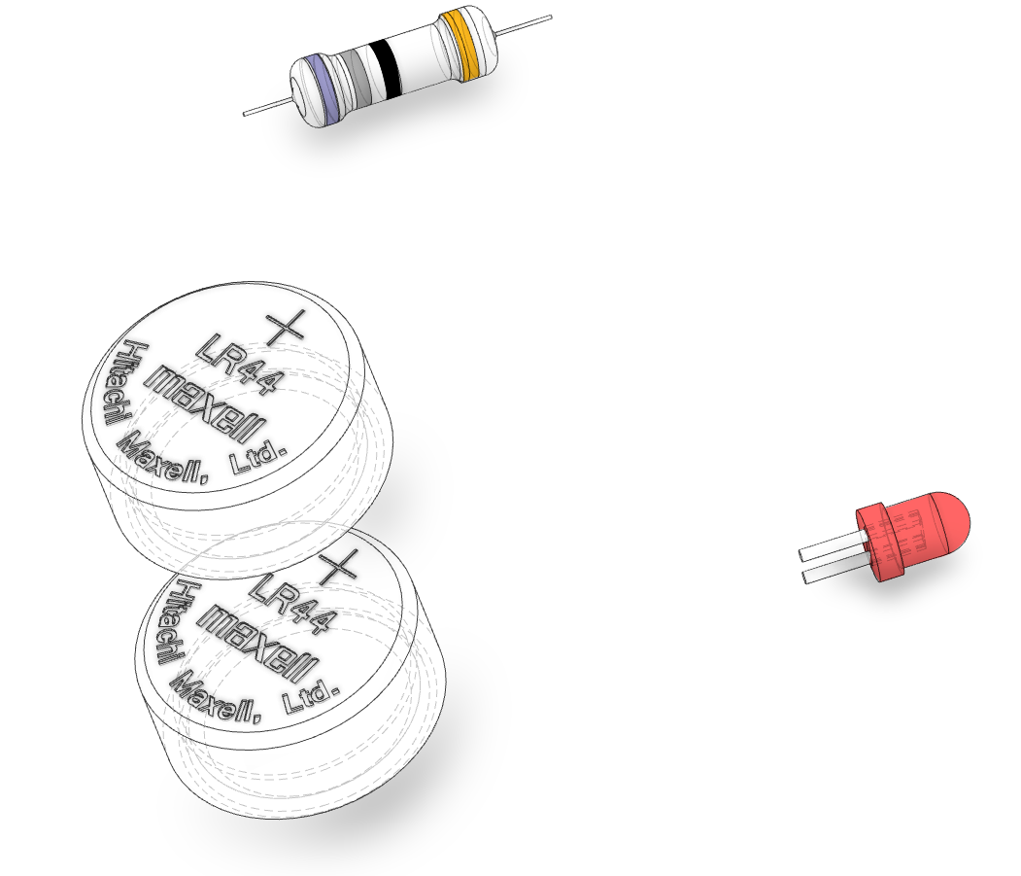
instructions/src/links/lighting.png
